rompasaurus/dilder/PromptProgression.md

# Prompt Progression

A record of every prompt submitted during the development of Dilder.

Spelling and grammar are lightly cleaned for readability while preserving the original intent and voice.

## Fields tracked per entry

Every prompt entry below uses the following fields. Entries that don't yet list all fields should be treated as incomplete and backfilled when the context is recovered.

- **Date/Time** — absolute date (`YYYY-MM-DD`) of the prompt. Relative dates like "Thursday" get resolved when the entry is written.
- **Prompt** — the user's message, quoted. Spelling and grammar are lightly cleaned for readability while preserving the original intent and voice.
- **Input Tokens (est)** — approximate user-facing input token count.
- **Output Tokens (est)** — approximate assistant output token count across the full turn.
- **Commit** — the short SHA + subject line of the git commit that landed the changes from this prompt, in the form `` `abc1234` — commit subject ``. Uses `n/a — <reason>` if no files were changed (research / Q&A / explanation turns) or if the work was never committed.
- **Files Created/Modified** — bulleted list of files touched, with short notes on the change. If nothing changed, omit or write `none`. Multi-prompt sessions may share a single commit; each entry still lists the files the specific prompt touched.

---

## Prompt #1
- **Date/Time:** 2026-04-08
- **Prompt:** "Let's create a new git repo for this project and put it up on my rompasaurus GitHub account. Also create a prompt progression file to notate every prompt that I type out for this project in an MD file with date and time stamp and the token count for each, and the files created or modified, in a file called PromptProgression."
- **Input Tokens (est):** ~75
- **Output Tokens (est):** ~350
- **Commit:** `369880d` — Initial commit: add PromptProgression.md for tracking project prompts
- **Files Created/Modified:**
  - `PromptProgression.md` (created)
  - `.git/` (initialized)
  - GitHub repo `rompasaurus/dilder` (created)

---

## Prompt #2
- **Date/Time:** 2026-04-08
- **Prompt:** "Let's set up a README and plan for this project. The idea is to create a learning platform and blog along with a YouTube series that goes through the development process of creating a Tamagotchi clone using a Pi Zero, e-ink display, battery, and 3D-printed case. As part of this we are going to document the entire process, starting with the prompts and structure of the project and planning process. Flesh out a README that outlines this intent, marking each addition in phases so that it can be compiled into a proper step-by-step instruction."
- **Input Tokens (est):** ~110
- **Output Tokens (est):** ~2,500
- **Commit:** `cc9ea8f` — Add README with phased project roadmap and update prompt log
- **Files Created/Modified:**
  - `README.md` (created)
  - `PromptProgression.md` (modified)

---

## Prompt #3
- **Date/Time:** 2026-04-09
- **Prompt:** "Let's continue the planning process. Bear in mind each prompt I submit needs to be recorded in PromptProgression.md. I suppose Phase 0 planning is somewhat complete — there is a section to define the pet and personality but I believe that should be planned at a later date. I think the focus first will be piecing together the hardware for a prototype testable unit with a display and input, and perhaps we'll put a placeholder animal animation of sorts to get a scaffold in place code-wise and a process in place for deploying code and testing it. As for the hardware, what we are going to be working with is a Pi Zero and this e-ink display. Let's begin to research the materials list to include this and whatever else hardware-wise will be needed to get a test bench setup for developing on this hardware. Also, given this hardware, come up with prototype sketches that could potentially be a 3D-printed casing for these materials and allow for 4–5 buttons of input actions to be recorded on the hardware, and suggest and research the types of cheap off-the-shelf components that can be used to establish input actions."
- **Input Tokens (est):** ~220
- **Output Tokens (est):** ~4,500
- **Commit:** `733c582` — Add hardware research with materials list, component specs, and input options
- **Files Created/Modified:**
  - `PromptProgression.md` (modified)
  - `docs/hardware-research.md` (created)
  - `README.md` (modified)

---

## Prompt #4
- **Date/Time:** 2026-04-09
- **Prompt:** "I also need the output processing token estimate from the prompts as well in the prompt progression."
- **Input Tokens (est):** ~20
- **Output Tokens (est):** ~250
- **Commit:** `8b8b2e4` — Update README and prompt log for Phase 1 hardware planning
- **Files Created/Modified:**
  - `PromptProgression.md` (modified — added output token estimates to all entries)

---

## Prompt #5
- **Date/Time:** 2026-04-09
- **Prompt:** "Those concept ASCII images are neat, but I want something more like a long rectangular case with the buttons on the right of the display — somewhat like the second-to-last generation of iPod Nanos — with four buttons: up, down, left, right, and a center button. Try to mock this up and see if you can generate an actual example, full-resolution prototype concept of this, bearing in mind the hardware we are using."
- **Input Tokens (est):** ~90
- **Output Tokens (est):** ~3,800
- **Commit:** `e1b6891` — Add prototype enclosure concept renders (v1 and v2 SVGs)
- **Files Created/Modified:**
  - `docs/concepts/prototype-v1.svg` (created — full-resolution prototype concept render)
  - `docs/hardware-research.md` (modified — replaced ASCII concepts with SVG reference and updated form factor)
  - `PromptProgression.md` (modified)

---

## Prompt #6
- **Date/Time:** 2026-04-09
- **Prompt:** "That's a good start. Let's create another revision of the prototype and make a v2. This time let's make the dimensions make sense — the display is going to take up the largest area of the device with the buttons being a quarter or less of the device's face real estate. Let's also take into account the Waveshare's actual dimensions and account for these ratios."
- **Input Tokens (est):** ~75
- **Output Tokens (est):** ~6,500
- **Commit:** `e1b6891` — Add prototype enclosure concept renders (v1 and v2 SVGs)
- **Files Created/Modified:**
  - `docs/concepts/prototype-v2.svg` (created — dimension-accurate prototype concept at 4:1 scale)
  - `docs/hardware-research.md` (modified — updated enclosure section with v2 specs and real component dimensions)
  - `PromptProgression.md` (modified)

---

## Prompt #7
- **Date/Time:** 2026-04-09
- **Prompt:** "For the hardware research we will need a breadboard to wire everything together — add that in there. Then we can begin the hardware setup and configuration, assuming we bought all the materials listed and a Waveshare e-ink display 2.13 V3. Compose an in-depth, well-researched setup guide to begin displaying text on the display and compile and run embedded code on the Raspberry Pi. Make the guide as simple and exhaustive as possible. Include a table of contents and walk me through the documentation for the hardware and how to set up the development and debugging environment. Pull in and research every bit of documentation I will need to be successful in this project."
- **Input Tokens (est):** ~130
- **Output Tokens (est):** ~12,000
- **Commit:** `30bb8b7` — Add comprehensive hardware and dev environment setup guide
- **Files Created/Modified:**
  - `docs/setup-guide.md` (created — comprehensive hardware and dev environment setup guide with 13 sections)
  - `docs/hardware-research.md` (modified — updated display to V3, added breadboard detail)
  - `README.md` (modified — added setup guide link to docs table and Phase 1 checklist)
  - `PromptProgression.md` (modified)

---

## Prompt #8
- **Date/Time:** 2026-04-09
- **Prompt:** "I want to set up a documentation webpage/portfolio to provide an in-depth guide on how this project is progressing in real time, along with a page for documentation and research, contact information, and an introduction. Let's create a new folder to begin planning this. I would also like to use pwnagotchi.ai as something of an inspiration for how to set this up and organise the website. It doesn't need to be anything ridiculous — in fact, static pages may be the ideal format — along with a Discord group and Patreon page. Let's roll out this folder and christen it with a new MD file."
- **Input Tokens (est):** ~120
- **Output Tokens (est):** ~3,500
- **Commit:** `f44695c` — Add website planning folder with site structure and community plan
- **Files Created/Modified:**
  - `website/PLAN.md` (created — website plan with site structure, page descriptions, Discord/Patreon plans, SSG comparison, pwnagotchi analysis)
  - `PromptProgression.md` (modified)

---

## Prompt #9
- **Date/Time:** 2026-04-09
- **Prompt:** "Let's kick off the website implementation. Look through the plan and start fleshing this out. Make sure while implementing the site to notate every step taken in a website implementation process MD, which will have a nicely structured TOC and detailed step-by-step notes on the process of creating this static site — to act as instruction and documentation. I also need a detailed guide on how to add and update content and the structure of the site, and further steps to deploy on Digital Ocean for as cheap as possible, and the best way to secure a domain for a website. Come up with domain ideas as well. Add steps to create a Patreon and Discord account. Don't forget to update PromptProgression with any prompt I input — don't be afraid to clean spelling and grammar before putting it in there too."
- **Input Tokens (est):** ~180
- **Output Tokens (est):** ~35,000
- **Commit:** `0360ba9` — Build out full MkDocs website scaffold and dev tooling (Prompts 9–13)
- **Files Created/Modified:**
  - `website/mkdocs.yml` (created — full MkDocs Material config with blog plugin, nav, social links, extensions)
  - `website/docs/index.md` (created — landing page)
  - `website/docs/about/index.md` (created — about page)
  - `website/docs/about/contact.md` (created — contact page)
  - `website/docs/blog/index.md` (created — blog landing)
  - `website/docs/blog/posts/phase-0-planning.md` (created — Phase 0 blog post)
  - `website/docs/blog/posts/phase-1-hardware.md` (created — Phase 1 blog post)
  - `website/docs/docs/index.md` (created — docs overview)
  - `website/docs/docs/hardware/materials-list.md` (created — migrated from hardware-research.md)
  - `website/docs/docs/hardware/wiring-pinout.md` (created — GPIO assignments and breadboard layout)
  - `website/docs/docs/hardware/enclosure-design.md` (created — case dimensions and design constraints)
  - `website/docs/docs/setup/pi-zero-setup.md` (created — OS flash, SSH, SPI setup)
  - `website/docs/docs/setup/display-setup.md` (created — HAT attachment, Waveshare library, hello world)
  - `website/docs/docs/setup/dev-environment.md` (created — rsync workflow, VS Code Remote-SSH, systemd)
  - `website/docs/docs/software/project-structure.md` (created — planned firmware architecture)
  - `website/docs/community/index.md` (created — community overview)
  - `website/docs/community/discord.md` (created — Discord server structure)
  - `website/docs/community/support.md` (created — Patreon tiers)
  - `website/docs/prompts/index.md` (created — prompt log mirroring PromptProgression.md)
  - `website/docs/stylesheets/extra.css` (created — custom CSS overrides)
  - `website/IMPLEMENTATION.md` (created — 14-section build process doc covering MkDocs setup, GitHub Pages, Digital Ocean deployment, domain registration guide, domain ideas, Discord setup, Patreon setup)
  - `website/CONTENT-GUIDE.md` (created — 11-section content management guide covering blog posts, docs pages, nav, Markdown features, images, and publishing)
  - `PromptProgression.md` (modified)

---

## Prompt #10
- **Date/Time:** 2026-04-09
- **Prompt:** "Give me a Python setup CLI script I can run to deploy this locally, with nice logging and status output when it is running, and various helper options for this project."
- **Input Tokens (est):** ~40
- **Output Tokens (est):** ~4,500
- **Commit:** `0360ba9` — Build out full MkDocs website scaffold and dev tooling (Prompts 9–13)
- **Files Created/Modified:**
  - `website/dev.py` (created — CLI with subcommands: check, install, serve, build, deploy, clean, status; ANSI color output with spinner; argparse; no external dependencies)

---

## Prompt #11
- **Date/Time:** 2026-04-09
- **Prompt:** "Give me a nice selection menu interface instead of a list of commands."
- **Input Tokens (est):** ~15
- **Output Tokens (est):** ~3,800
- **Commit:** `0360ba9` — Build out full MkDocs website scaffold and dev tooling (Prompts 9–13)
- **Files Created/Modified:**
  - `website/dev.py` (modified — replaced no-args fallback with interactive arrow-key menu: ↑↓ navigation, live description footer, env status badges, returns to menu after each command)

---

## Prompt #12
- **Date/Time:** 2026-04-09
- **Prompt:** "There seems to be a build failure when I build via the CLI script."
- **Input Tokens (est):** ~180 (included full error output)
- **Output Tokens (est):** ~500
- **Commit:** `0360ba9` — Build out full MkDocs website scaffold and dev tooling (Prompts 9–13)
- **Files Created/Modified:**
  - `website/docs/blog/.authors.yml` (created — required by MkDocs blog plugin for named authors)
  - `website/docs/blog/index.md` (modified — removed dead RSS link that wasn't a source file)
  - `website/docs/docs/hardware/enclosure-design.md` (modified — changed SVG links from broken relative paths to GitHub URLs)

---

## Prompt #13
- **Date/Time:** 2026-04-09
- **Prompt:** "Let's update the prompts with the last ones I sent through — divide and describe them. Commit the changes, and also apply the git commit as another field in the prompt progression where the prompt's changes were applied. Don't be afraid to clean up the spelling and grammar a bit. Report this prompt as well."
- **Input Tokens (est):** ~65
- **Output Tokens (est):** ~2,500
- **Commit:** `78ea1a0` — Backfill commit hash in PromptProgression.md (Prompt 13)
- **Files Created/Modified:**
  - `PromptProgression.md` (modified — full grammar/spelling pass, added commit hash field to all entries, added Prompts #11–13)

---

## Prompt #14
- **Date/Time:** 2026-04-09
- **Prompt:** "Walk me through how I could deploy this on GitHub Pages and the pricing structure — hopefully free — and if a domain can be linked to a GitHub Pages account."
- **Input Tokens (est):** ~35
- **Output Tokens (est):** ~900
- **Commit:** `633b084` — Add GitHub Actions workflow for automatic Pages deployment
- **Files Created/Modified:**
  - `.github/workflows/deploy-site.yml` (created — workflow that triggers on pushes to `website/` on main, installs MkDocs Material, and runs `mkdocs gh-deploy`)

---

## Prompt #15
- **Date/Time:** 2026-04-09
- **Prompt:** "Can you embed the concept images instead of linking to the GitHub page on the website?"
- **Input Tokens (est):** ~30
- **Output Tokens (est):** ~300
- **Commit:** `e358a1f` — Embed prototype SVG renders directly in enclosure design page
- **Files Created/Modified:**
  - `website/docs/assets/images/prototype-v1.svg` (created — copied from docs/concepts/)
  - `website/docs/assets/images/prototype-v2.svg` (created — copied from docs/concepts/)
  - `website/docs/docs/hardware/enclosure-design.md` (modified — replaced GitHub links with inline `![img]()` embeds)

---

## Prompt #16
- **Date/Time:** 2026-04-09
- **Prompt:** "Should the site folder be in the gitignore or will that need to be included to render on the GitHub Pages?"
- **Input Tokens (est):** ~25
- **Output Tokens (est):** ~150
- **Commit:** n/a — explanation only, no files changed
- **Files Created/Modified:** none

---

## Prompt #17
- **Date/Time:** 2026-04-09
- **Prompt:** "Add the last prompts with code changes to the prompt history with a commit ref."
- **Input Tokens (est):** ~20
- **Output Tokens (est):** ~400
- **Commit:** `1c270fd` — Update PromptProgression with Prompts 14–17 and fix #13 commit ref
- **Files Created/Modified:**
  - `PromptProgression.md` (modified — fixed Prompt #13 commit hash, added Prompts #14–17)

---

## Prompt #18
- **Date/Time:** 2026-04-09
- **Prompt:** "I need a website deployment process guide for GitHub Pages. I have a registered domain on Squarespace and I would like to deploy this site on GitHub and link my domain to this page."
- **Input Tokens (est):** ~45
- **Output Tokens (est):** ~2,800
- **Commit:** `38baa75` — Add deployment guide and CNAME file for Squarespace domain setup
- **Files Created/Modified:**
  - `website/DEPLOY.md` (created — 13-section deployment guide: GitHub Pages setup, first deployment, CNAME file, Squarespace DNS configuration with step-by-step record setup, HTTPS, mkdocs.yml update, end-to-end verification checklist, troubleshooting)
  - `website/docs/CNAME` (created — placeholder CNAME file, update with real domain before deploying)

---

## Prompt #19
- **Date/Time:** 2026-04-09
- **Prompt:** "Add my Patreon page to the site."
- **Input Tokens (est):** ~15
- **Output Tokens (est):** ~100
- **Commit:** `3b36905` — Add real Patreon URL (MchenrysDevelopment) across site
- **Files Created/Modified:**
  - `website/mkdocs.yml` (modified — Patreon social link updated)
  - `website/docs/community/support.md` (modified — Patreon URL updated)
  - `website/docs/about/contact.md` (modified — Patreon URL updated)

---

## Prompt #20
- **Date/Time:** 2026-04-09
- **Prompt:** "There's a 404 error — it's not loading despite the domain pointing correctly and the GitHub hook deploying."
- **Input Tokens (est):** ~40
- **Output Tokens (est):** ~300
- **Commit:** `0af7962` — Clarify Pages source setting in workflow comment
- **Files Created/Modified:**
  - `.github/workflows/deploy-site.yml` (modified — added comment clarifying Pages must be set to "Deploy from a branch → gh-pages" not "GitHub Actions")

---

## Prompt #21
- **Date/Time:** 2026-04-09
- **Prompt:** "Make that branch for me so that it triggers the deploy."
- **Input Tokens (est):** ~20
- **Output Tokens (est):** ~150
- **Commit:** `1c7f210` — Trigger GitHub Pages deployment via website/ path change
- **Files Created/Modified:**
  - `website/requirements.txt` (modified — added comment to satisfy workflow paths filter and trigger first deployment)

---

## Prompt #22
- **Date/Time:** 2026-04-09
- **Prompt:** *(Shared GitHub Actions build log showing successful deploy to gh-pages branch with CNAME resolution to dilder.dev)*
- **Input Tokens (est):** ~200 (build log)
- **Output Tokens (est):** ~200
- **Commit:** `18c8876` — Lowercase CNAME domain
- **Files Created/Modified:**
  - `website/docs/CNAME` (modified — changed `Dilder.dev` to `dilder.dev` for consistency)

---

## Prompt #23
- **Date/Time:** 2026-04-09
- **Prompt:** "Now we need to pull in the documentation for the Pi Zero WH and the e-ink display. Reach out to the official documentation and put it in its own folder in the docs folder. We need to then extract the pinout and pertinent documentation and attach it to the Wiring & Pinout doc."
- **Input Tokens (est):** ~55
- **Output Tokens (est):** ~8,500
- **Commit:** `61525d6` — Add official hardware reference docs and expand wiring pinout
- **Files Created/Modified:**
  - `website/docs/docs/reference/pi-zero-wh.md` (created — full 40-pin GPIO table, electrical limits, SPI/I²C/UART/PWM protocol assignments, BCM vs physical numbering guide, official links)
  - `website/docs/docs/reference/waveshare-eink.md` (created — display specs, HAT pin mapping with signal behavior table, SPI protocol details, refresh rules, V3 vs V4 comparison, Python setup examples, safety notes, official links)
  - `website/docs/docs/hardware/wiring-pinout.md` (modified — expanded with full 40-pin header map, signal behavior table, wiring diagram, SPI config table, links to new reference docs, troubleshooting section)
  - `website/mkdocs.yml` (modified — Reference section added to nav)

---

## Prompt #24
- **Date/Time:** 2026-04-09
- **Prompt:** "Update the prompts file with this and the commit."
- **Input Tokens (est):** ~15
- **Output Tokens (est):** ~400
- **Commit:** `09519b5` — Update PromptProgression with Prompts 20–24
- **Files Created/Modified:**
  - `PromptProgression.md` (modified — added Prompts #20–24)

---

## Prompt #25
- **Date/Time:** 2026-04-10
- **Prompt:** "Let's update this plan and the hardware we are going to use. For now I have a set of Waveshare 2.13 V3 displays and Pico W boards on hand that I would like to use to start this project with instead of the Pi Zero. We'll put the Pi Zero in a later dev phase and start with what we have. Update the documentation to account for this hardware change and pull in the correct documentation for this hardware and setup in the project and on the site. Update everything and replace the Zero with the Pico, and then we need to create a setup document to wire up the Waveshare to the Pico W and begin debugging from VSCode on Linux."
- **Input Tokens (est):** ~130
- **Output Tokens (est):** ~45,000
- **Commit:** `604039f` — Migrate from Pi Zero to Pico W as Phase 1 development platform
- **Files Created/Modified:**
  - `README.md` (modified — Pico W as primary board, Pi Zero deferred to Phase 5, new phase roadmap)
  - `docs/hardware-research.md` (modified — Pico W specs, SPI1 pin mapping, updated materials list and GPIO budget)
  - `website/docs/docs/reference/pico-w.md` (created — full Pico W reference: RP2040 specs, pinout, electrical limits, MicroPython firmware, Pico W vs Pi Zero comparison)
  - `website/docs/docs/reference/waveshare-eink.md` (modified — added Pico W jumper wire mapping, MicroPython driver setup, kept Pi Zero mapping for future)
  - `website/docs/docs/reference/pi-zero-wh.md` (modified — added "future hardware" banner)
  - `website/docs/docs/hardware/materials-list.md` (modified — Pico W components, updated costs and specs)
  - `website/docs/docs/hardware/wiring-pinout.md` (modified — complete rewrite for Pico W GPIO, jumper wire diagrams, MicroPython button code, visual pin map)
  - `website/docs/docs/hardware/enclosure-design.md` (modified — Pico W dimensions, enclosure deferred note)
  - `website/docs/docs/setup/pi-zero-setup.md` (modified — rewritten as Pico W setup: MicroPython flash, BOOTSEL, serial REPL, Wi-Fi test)
  - `website/docs/docs/setup/display-setup.md` (modified — rewritten for Pico W jumper wire connection, Waveshare MicroPython driver, framebuf hello world)
  - `website/docs/docs/setup/dev-environment.md` (modified — rewritten for VSCode + MicroPico on Linux: serial permissions, project config, file upload, mpremote CLI, debugging)
  - `website/docs/docs/software/project-structure.md` (modified — updated for MicroPython: framebuf, machine.Pin, flash storage notes)
  - `website/docs/docs/index.md` (modified — updated section names and descriptions for Pico W)
  - `website/docs/index.md` (modified — landing page updated for Pico W)
  - `website/mkdocs.yml` (modified — site description, nav labels, added Pico W reference page)
  - `website/docs/blog/posts/phase-1-hardware.md` (modified — rewritten for Pico W test bench)
  - `website/docs/blog/posts/phase-0-planning.md` (modified — hardware decision section updated for Pico W first approach)

---

## Prompt #26
- **Date/Time:** 2026-04-10
- **Prompt:** "Update the prompts file and fix grammar a bit. Divide, describe, and commit."
- **Input Tokens (est):** ~20
- **Output Tokens (est):** ~1,500
- **Commit:** `604039f` — Migrate from Pi Zero to Pico W as Phase 1 development platform
- **Files Created/Modified:**
  - `PromptProgression.md` (modified — added Prompts #25–26)

---

## Prompt #27
- **Date/Time:** 2026-04-11
- **Prompt:** "Let's make a development setup folder with a Docker Compose file and a step-by-step guide with a table of contents on setting up the Pico W and Waveshare e-ink display — physically connecting the display to the Pico board via GPIO headers, then flashing and connecting the Pico to this computer and running a first Hello World program via VSCode using compiled C. I need all the instructions to set up the hardware, configure VSCode, connect, debug, and run this application. Make this guide as detailed and as simple as possible, step by step. Also update the PromptProgression every time I submit a prompt here — clean up the grammar and spelling though. Make this setup guide the Pico and display first-time setup, and update the dev website too."
- **Input Tokens (est):** ~150
- **Output Tokens (est):** ~45,000
- **Commit:** `8f0df95` — Add C SDK dev environment, setup CLI, and first-time hardware guide
- **Files Created/Modified:**
  - `dev-setup/pico-and-display-first-time-setup.md` (created — comprehensive 13-section first-time setup guide with TOC: hardware wiring, C SDK toolchain install, VSCode configuration, CMake cross-compilation, build/flash/debug workflow, troubleshooting)
  - `dev-setup/hello-world/CMakeLists.txt` (created — CMake build config for Pico W with Waveshare e-Paper library, USB serial output, Ninja generator)
  - `dev-setup/hello-world/main.c` (created — Hello World C program that initializes SPI, draws text on the e-ink display, and prints heartbeat to USB serial)
  - `dev-setup/Dockerfile` (created — Ubuntu 24.04 container with ARM cross-compiler toolchain and Pico SDK for reproducible builds)
  - `dev-setup/docker-compose.yml` (created — single-service compose file that mounts the project and runs CMake + Ninja build)
  - `website/docs/docs/setup/first-time-setup.md` (created — website version of the setup guide with MkDocs Material formatting, tabbed OS instructions, admonitions)
  - `website/mkdocs.yml` (modified — added "First-Time Setup (C SDK)" to the Setup nav section)
  - `PromptProgression.md` (modified — added Prompt #27)

---

## Prompt #28
- **Date/Time:** 2026-04-11
- **Prompt:** "Let's start planning the hardware enclosure design. Create a new folder labelled hardware-design and document the applicable dimensions of the e-ink display and Pico board, along with viable off-the-shelf button options that can be wired to the Pico easily. Research the web for the best button options and provide a cost breakdown. Then we need to start planning how to model out a 3D-printed prototype case based on the concept images — link the concept images, suggest the best CAD software and company to print the first prototype cases, and provide estimated costs. Put this in a new hardware planning document with a table of contents and step-by-step guide. Also update the PromptProgression with this entry, following the same pattern."
- **Input Tokens (est):** ~150
- **Output Tokens (est):** ~25,000
- **Commit:** `8f0df95` — Add C SDK dev environment, setup CLI, and first-time hardware guide
- **Files Created/Modified:**
  - `hardware-design/hardware-planning.md` (created — comprehensive enclosure planning document with TOC: component dimensions, button selection with cost breakdown, concept image links, enclosure constraints, CAD software comparison, step-by-step 3D modeling plan, printing service comparison with costs, prototype timeline)

---

## Prompt #29
- **Date/Time:** 2026-04-11
- **Prompt:** "I want another Hello World version of the code running in C as well. The intent with this project is to have it running on C code completely for speed and efficiency. Also, for the wiring section, I am using the soldered-on headers and pins to slot the Waveshare directly onto the Pico on its headers, so it just slides in. Update the guide accordingly — I will provide pictures later."
- **Input Tokens (est):** ~80
- **Output Tokens (est):** ~30,000
- **Commit:** `8f0df95` — Add C SDK dev environment, setup CLI, and first-time hardware guide
- **Files Created/Modified:**
  - `dev-setup/hello-world-serial/main.c` (created — bare-minimum serial-only Hello World in C: LED blink + heartbeat printf, no display wiring needed, verifies toolchain end-to-end)
  - `dev-setup/hello-world-serial/CMakeLists.txt` (created — minimal CMake config linking only pico_stdlib with USB serial output)
  - `dev-setup/pico-and-display-first-time-setup.md` (rewritten — restructured as two checkpoints: Checkpoint 1 serial-only, Checkpoint 2 display; added C vs MicroPython rationale; updated wiring section from jumper wires to direct header-on-header connection)
  - `website/docs/docs/setup/first-time-setup.md` (rewritten — website version updated to match: direct header connection, two-checkpoint flow, C-first rationale)
  - `PromptProgression.md` (modified — added Prompt #29)

---

## Prompt #30
- **Date/Time:** 2026-04-11
- **Prompt:** "Let's take this Pico W & Display First-Time Setup and implement a Python command-line step-by-step interface that sets everything up and explains the process in detail as well. Put the Python script in the root of this project."
- **Input Tokens (est):** ~40
- **Output Tokens (est):** ~35,000
- **Commit:** `8f0df95` — Add C SDK dev environment, setup CLI, and first-time hardware guide
- **Files Created/Modified:**
  - `setup.py` (created — interactive 14-step CLI walkthrough: prerequisite checks, ARM toolchain install with distro detection, Pico SDK clone, PICO_SDK_PATH configuration, serial port permissions, VSCode extension install, serial hello world build/flash/verify, display connection guidance, Waveshare library download, display hello world build/flash/verify; includes --status, --step N, and --list flags; matches dev.py visual style with ANSI colors, spinners, boxed explanations, and manual-step callouts)
  - `PromptProgression.md` (modified — added Prompt #30)

---

## Prompt #31
- **Date/Time:** 2026-04-11
- **Prompt:** "Failed at step 5 — `usermod: group 'dialout' does not exist`. Does the Pico need to be connected at step 5?"
- **Input Tokens (est):** ~30
- **Output Tokens (est):** ~5,000
- **Commit:** `8f0df95` — Add C SDK dev environment, setup CLI, and first-time hardware guide
- **Files Created/Modified:**
  - `setup.py` (modified — added `detect_serial_group()` and `user_in_serial_group()` helpers that check for `uucp` first then `dialout`; Arch/CachyOS uses `uucp`, Debian/Ubuntu uses `dialout`; all hardcoded `dialout` references replaced with dynamic detection)
  - `dev-setup/pico-and-display-first-time-setup.md` (modified — serial permissions section updated with distro-specific group names)
  - `website/docs/docs/setup/first-time-setup.md` (modified — same distro-specific serial group fix with tabbed instructions)
  - `PromptProgression.md` (modified — added Prompt #31)

---

## Prompt #32
- **Date/Time:** 2026-04-11
- **Prompt:** *(Pasted build failure output from setup.py Step 7 — `PICO_DEFAULT_LED_PIN` undeclared error)*
- **Input Tokens (est):** ~80
- **Output Tokens (est):** ~8,000
- **Commit:** `8f0df95` — Add C SDK dev environment, setup CLI, and first-time hardware guide
- **Files Created/Modified:**
  - `dev-setup/hello-world-serial/main.c` (modified — replaced `PICO_DEFAULT_LED_PIN` and `gpio_put` with `cyw43_arch_gpio_put(CYW43_WL_GPIO_LED_PIN)` since the Pico W's onboard LED is wired to the CYW43 Wi-Fi chip, not a regular GPIO pin; added `pico/cyw43_arch.h` include and `cyw43_arch_init()` call)
  - `dev-setup/hello-world-serial/CMakeLists.txt` (modified — added `pico_cyw43_arch_none` to link libraries for CYW43 LED control)
  - `setup.py` (modified — fixed build error output to show both stdout and stderr since Ninja reports compile errors on stdout)
  - `PromptProgression.md` (modified — added Prompt #32)

---

## Prompt #33
- **Date/Time:** 2026-04-11
- **Prompt:** "Could not find the RPI-RP2 mount despite it showing up in Dolphin file explorer."
- **Input Tokens (est):** ~40
- **Output Tokens (est):** ~5,000
- **Commit:** `8f0df95` — Add C SDK dev environment, setup CLI, and first-time hardware guide
- **Files Created/Modified:**
  - `setup.py` (modified — added `find_rpi_rp2_mount()` helper that checks static paths, falls back to `findmnt`/`lsblk` for the actual mount point, retries after 1-second delay for automount; both flash steps now loop with retry instead of failing on first miss)
  - `PromptProgression.md` (modified — added Prompt #33)

---

## Prompt #34
- **Date/Time:** 2026-04-11
- **Prompt:** *(Pasted Step 12 build failure — `Debug.h: No such file or directory` and missing `<stdlib.h>` warnings)*
- **Input Tokens (est):** ~100
- **Output Tokens (est):** ~5,000
- **Commit:** `8f0df95` — Add C SDK dev environment, setup CLI, and first-time hardware guide
- **Files Created/Modified:**
  - `dev-setup/hello-world/main.c` (modified — added missing `#include <stdlib.h>` for `malloc`/`free`)
  - `dev-setup/hello-world/lib/Config/Debug.h` (added — copied from Waveshare repo, was missing from the initial file list)
  - `setup.py` (modified — added `Debug.h` to the Waveshare library copy list in Step 11)
  - `dev-setup/pico-and-display-first-time-setup.md` (modified — added `Debug.h` to the manual copy commands)
  - `website/docs/docs/setup/first-time-setup.md` (modified — same `Debug.h` fix)
  - `PromptProgression.md` (modified — added Prompt #34)

---

## Prompt #35
- **Date/Time:** 2026-04-11
- **Prompt:** "That worked. Let's update the documentation and provide a step-by-step walkthrough of this script and setup process in the setup document. Also update the prompts doc with all the prompts we used here and the last session, then divide, describe, commit, and push this code."
- **Input Tokens (est):** ~50
- **Output Tokens (est):** ~12,000
- **Commit:** `8f0df95` — Add C SDK dev environment, setup CLI, and first-time hardware guide
- **Files Created/Modified:**
  - `dev-setup/pico-and-display-first-time-setup.md` (modified — added "Automated Setup Script" section at the top with full walkthrough: command reference, 14-step table with automated/manual flags, example `--status` output, resume instructions)
  - `website/docs/docs/setup/first-time-setup.md` (modified — added matching setup script walkthrough with MkDocs admonitions and step table)
  - `.gitignore` (modified — added build artifacts, Waveshare lib files, pico_sdk_import.cmake, `__pycache__/`, `.vscode/`)
  - `PromptProgression.md` (modified — added Prompts #27–35, updated all pending commit hashes)
  - All new and modified files committed and pushed to origin/main

---

## Prompt #36
- **Date/Time:** 2026-04-11
- **Prompt:** "Now that the dev environment is set up, let's make a Python GUI to interface with the Pico — view logs, debug, and create a simple utility to draw images and type text on an emulated e-ink display that can then be either saved locally or sent to the e-ink display live. When saved, add it to an assets folder in the root of this project directory. Also, if there are any other useful utilities that can be added to enhance the development and usage of the Pico W, add them to this Python UI. Let's make this in Tkinter and put it in the root of this project in a directory called DevTool. Also I need an in-depth walkthrough of this implementation in the folder as well — an MD with a TOC and step-by-step instructions."
- **Input Tokens (est):** ~150
- **Output Tokens (est):** ~55,000
- **Commit:** `cf5cd3a` — Add DevTool — Tkinter GUI for Pico W development
- **Files Created/Modified:**
  - `DevTool/devtool.py` (created — 950-line Tkinter GUI with five tabs: display emulator with pencil/eraser/line/rect/text tools and save/load/send; serial monitor with connect/disconnect/send/log; firmware flash utility with BOOTSEL detection and build buttons; asset manager with preview and delete; GPIO pin reference viewer; dark theme; threaded serial I/O)
  - `DevTool/requirements.txt` (created — pyserial, Pillow)
  - `DevTool/README.md` (created — 11-section walkthrough with TOC: requirements, installation, all five tabs documented with usage instructions, file formats, architecture overview, class structure, threading model, troubleshooting table)
  - `assets/` (created — empty directory for saved display images)
  - `PromptProgression.md` (modified — added Prompt #36)

---

## Prompt #37
- **Date/Time:** 2026-04-11
- **Prompt:** "Add a utility tab to walk through connecting the Pico via USB, and also add a Wi-Fi option as well in the GUI as a tab. Be descriptive and as simple as possible. And add a documentation tab to reference how to use the application."
- **Input Tokens (est):** ~50
- **Output Tokens (est):** ~25,000
- **Commit:** `cdae51f` — Add Connect and Docs tabs to DevTool
- **Files Created/Modified:**
  - `DevTool/devtool.py` (modified — added two new tabs: ConnectionUtility with USB serial walkthrough (4 steps with live Check buttons for device detection, serial port, permissions, plus link to Serial Monitor) and Wi-Fi walkthrough (C code examples, CMake config, network scanner, TCP connection tester with IP/port input); DocumentationTab with searchable TOC sidebar, styled headings/code blocks, Find/Clear search with highlight, covers all 7 tabs plus keyboard shortcuts, file formats, and troubleshooting)
  - `DevTool/README.md` (modified — updated TOC, launch table, and architecture table for 7 tabs; added Section 9 Connection Utility with USB and Wi-Fi step tables; added Section 10 Documentation tab description; renumbered remaining sections)
  - `PromptProgression.md` (modified — added Prompt #37)

---

## Prompt #38
- **Date/Time:** 2026-04-11
- **Prompt:** "Allow me to run the sudo for serial permissions in the DevTool."
- **Input Tokens (est):** ~15
- **Output Tokens (est):** ~5,000
- **Commit:** `b8985c7` — Add sudo serial permissions button to DevTool Connect tab
- **Files Created/Modified:**
  - `DevTool/devtool.py` (modified — added "Fix: Add me to serial group" button in the Connect tab USB walkthrough; `_fix_serial_perms()` method auto-detects the correct group, tries `pkexec` for a graphical sudo prompt first, falls back to opening a terminal emulator with the command, shows confirmation dialog before running, reports success with logout reminder)
  - `PromptProgression.md` (modified — added Prompt #38)

---

## Prompt #39
- **Date/Time:** 2026-04-11
- **Prompt:** "The DevTool was suspended but didn't close. Help me close this and prevent this in the future."
- **Input Tokens (est):** ~20
- **Output Tokens (est):** ~2,000
- **Commit:** `586dff9` — Ignore Ctrl+Z (SIGTSTP) in DevTool to prevent zombie suspends
- **Files Created/Modified:**
  - `DevTool/devtool.py` (modified — added `signal.signal(signal.SIGTSTP, signal.SIG_IGN)` at startup to ignore Ctrl+Z; killed the suspended process with `kill -9`)

---

## Prompt #40
- **Date/Time:** 2026-04-11
- **Prompt:** "Update the prompts and add the latest assets as well. Clean up spelling and grammar."
- **Input Tokens (est):** ~20
- **Output Tokens (est):** ~3,000
- **Commit:** `5025ec6` — Add test assets and update PromptProgression through Prompt #40
- **Files Created/Modified:**
  - `assets/garbage.pbm` (added — test image saved from DevTool display emulator)
  - `assets/garbage.bin` (added — raw display buffer of the test image)
  - `assets/garbage.png` (added — PNG export of the test image)
  - `PromptProgression.md` (modified — added Prompts #39–40, backfilled commit hashes for #37–38, grammar and spelling pass)

---

## Prompt #41
- **Date/Time:** 2026-04-11
- **Prompt:** "We need to update the website with all the new documentation and Python tools created. Follow the structure of the site and update this."
- **Input Tokens (est):** ~30
- **Output Tokens (est):** ~60,000
- **Commit:** `b408ab1` — Update website with Tools docs, blog post, prompt log, and DevTool Programs tab
- **Files Created/Modified:**
  - `website/docs/docs/tools/devtool.md` (created — DevTool documentation page with installation, tabs overview, file formats, and architecture)
  - `website/docs/docs/tools/setup-cli.md` (created — setup.py documentation page with step tables, features, and status dashboard)
  - `website/docs/docs/tools/website-dev.md` (created — website dev.py documentation page with commands and workflow)
  - `website/docs/blog/posts/phase-1-devtools.md` (created — blog post covering setup CLI, DevTool GUI, and C-first development decisions)
  - `website/mkdocs.yml` (modified — added Tools section to nav with DevTool, Setup CLI, Website Dev CLI)
  - `website/docs/docs/index.md` (modified — added Tools subsection with links to all three tool pages)
  - `website/docs/docs/software/project-structure.md` (modified — complete rewrite: updated repo layout to include DevTool, dev-setup, hardware-design, assets, website planning docs; rewrote planned modules from MicroPython to C SDK; updated comparison table)
  - `website/docs/index.md` (modified — updated current phase to reflect dev tooling progress, added Dev Tools quick link card, added tools link to "How This Project Works" section)
  - `website/docs/prompts/index.md` (modified — added Prompts #10–40, covering website deployment, GitHub Pages, hardware migration, C SDK setup, DevTool development)
  - `PromptProgression.md` (modified — added Prompt #41)

---

## Prompt #42
- **Date/Time:** 2026-04-11
- **Prompt:** "Divide, describe, and commit. Update the prompts, fix grammar. Check all the latest Claude sessions for prompts."
- **Input Tokens (est):** ~25
- **Output Tokens (est):** ~2,000
- **Commit:** `b408ab1` — Update website with Tools docs, blog post, prompt log, and DevTool Programs tab
- **Files Created/Modified:**
  - `PromptProgression.md` (modified — added Prompt #42)

---

## Prompt #43
- **Date/Time:** 2026-04-11
- **Prompt:** "Also the software on the site needs the READMEs for the GUI app and a guide on the CLI setup."
- **Input Tokens (est):** ~25
- **Output Tokens (est):** ~40,000
- **Commit:** `8401317` — Expand DevTool and Setup CLI pages with full README content
- **Files Created/Modified:**
  - `website/docs/docs/tools/devtool.md` (rewritten — expanded from summary to full documentation matching DevTool/README.md: all 7 tabs with detailed usage instructions, drawing tools, serial monitor, flash firmware, asset manager, GPIO reference, connection utility with USB/Wi-Fi walkthroughs, documentation tab, file format specifications with byte layouts, class architecture, threading model, troubleshooting table)
  - `website/docs/docs/tools/setup-cli.md` (rewritten — expanded from summary to comprehensive guide matching dev-setup/pico-and-display-first-time-setup.md: 14-step walkthrough table, hardware requirements, software installed, Pico W and Waveshare specs, C vs MicroPython rationale, display connection with side-view diagram and pin mapping, troubleshooting tables for build/flash/serial/display issues, quick reference card)
  - `PromptProgression.md` (modified — added Prompt #43)

---

## Prompt #44
- **Date/Time:** 2026-04-11
- **Prompt:** "OK, you made a dev tool where I can create assets via the display emulator. First of all, the pencil and line don't draw on the window at all — text and rectangle do. Also I want the ability to preview the asset on the Pico display if it's connected — add a button to deploy to Pico. Then we want to create another tab in the dev tool to deploy from a list of programs. For the first program I want you to create a sassy octopus that smiles and alternates between that expression and an open-mouth expression with a text chat bubble where it blurts out from a random list of unhinged hilarious conspiracies and jokes and meme statements, alternating between facial expressions. The octopus should be on the left side of the display and the chat bubble to the right of its mouth."
- **Input Tokens (est):** ~200
- **Output Tokens (est):** ~80,000
- **Commit:** `63e696b`
- **Files Created/Modified:**
  - `DevTool/devtool.py` (modified — fixed `_draw_brush` range bug that broke pencil/line tools; added Programs tab with preview/deploy; added Sassy Octopus program with pixel art, 3 mouth expressions, 30 quotes, tiny bitmap font, chat bubble rendering; made Send to Pico non-blocking with write timeout)

---

## Prompt #45
- **Date/Time:** 2026-04-11
- **Prompt:** "The octopus needs more legs and it should have less black and more curvaceous. The display emulator tab should have a preview deploy on the Pico as well."
- **Input Tokens (est):** ~40
- **Output Tokens (est):** ~30,000
- **Commit:** `151b575` — Make DevTool serial send non-blocking and backfill Prompt #40 commit hash
- **Files Created/Modified:**
  - `DevTool/devtool.py` (modified — redesigned octopus to outline style with 6 curvy tentacles, then reverted to original chunky style per user preference; added 6 tentacle legs; fixed deploy hang with write_timeout)

---

## Prompt #46
- **Date/Time:** 2026-04-11
- **Prompt:** "God the octopus looks awful, use the other octopus you made — it looked way better."
- **Input Tokens (est):** ~20
- **Output Tokens (est):** ~15,000
- **Commit:** `b408ab1` — Update website with Tools docs, blog post, prompt log, and DevTool Programs tab
- **Files Created/Modified:**
  - `DevTool/devtool.py` (modified — reverted to original chunky filled-style octopus with 6 tentacle legs, improved open-mouth with proper white interior and black border)

---

## Prompt #47
- **Date/Time:** 2026-04-11
- **Prompt:** "I don't want to see the logs — write the steps in the write-failed message. Also the logs at the bottom need to be resizable."
- **Input Tokens (est):** ~30
- **Output Tokens (est):** ~10,000
- **Commit:** `63e696b` — Add Programs tab, Sassy Octopus, IMG-receiver and standalone firmware, fix drawing tools
- **Files Created/Modified:**
  - `DevTool/devtool.py` (modified — moved deploy failure steps to status label; replaced fixed log bar with resizable PanedWindow + scrollbar + Clear button; improved port detection with Raspberry Pi VID 0x2E8A; fixed hardcoded /dev/ttyACM0 references)

---

## Prompt #48
- **Date/Time:** 2026-04-11
- **Prompt:** "Also no device found error — I changed USB ports, does that break this? If so check for the correct port in all the utils."
- **Input Tokens (est):** ~30
- **Output Tokens (est):** ~5,000
- **Commit:** `63e696b` — Add Programs tab, Sassy Octopus, IMG-receiver and standalone firmware, fix drawing tools
- **Files Created/Modified:**
  - `DevTool/devtool.py` (modified — `find_pico_serial()` now checks Raspberry Pi USB VID 0x2E8A first, then falls back to ttyACM/usbmodem name matching; connection utility uses dynamic detection instead of hardcoded paths)

---

## Prompt #49
- **Date/Time:** 2026-04-11
- **Prompt:** "It says to flash the firmware via the flash tab — where is the image, what am I flashing? Can't you do it in the Programs tab when I have the Pico in BOOTSEL mode?"
- **Input Tokens (est):** ~40
- **Output Tokens (est):** ~40,000
- **Commit:** `63e696b` — Add Programs tab, Sassy Octopus, IMG-receiver and standalone firmware, fix drawing tools
- **Files Created/Modified:**
  - `dev-setup/img-receiver/main.c` (created — Pico W firmware that receives IMG: protocol over USB serial and displays on e-ink, with landscape-to-portrait transpose and partial refresh)
  - `dev-setup/img-receiver/CMakeLists.txt` (created)
  - `dev-setup/img-receiver/lib/` (created — copied shared Waveshare/GUI libraries)
  - `dev-setup/docker-compose.yml` (modified — added build-img-receiver service)
  - `DevTool/devtool.py` (modified — added Build & Flash button to Programs tab with Docker build + BOOTSEL flash; added 3 mouth expressions: smirk, smile, open; added MOUTH_CYCLE animation; updated all error messages to reference Programs tab)

---

## Prompt #50
- **Date/Time:** 2026-04-11
- **Prompt:** "Also give the octopus more mouth expressions — I want a default smile which is a half-circle that's white and slightly off-angle from the normal mouth."
- **Input Tokens (est):** ~30
- **Output Tokens (est):** ~5,000
- **Commit:** `63e696b` — Add Programs tab, Sassy Octopus, IMG-receiver and standalone firmware, fix drawing tools
- **Files Created/Modified:**
  - `DevTool/devtool.py` (modified — added smirk expression as default: tilted half-circle with white interior; animation now cycles smirk → open → smile → open)

---

## Prompt #51
- **Date/Time:** 2026-04-12
- **Prompt:** "In the build give some more descriptive logs of what Docker is doing. Also can the logs and windows be resized on this GUI?"
- **Input Tokens (est):** ~25
- **Output Tokens (est):** ~15,000
- **Commit:** `63e696b` — Add Programs tab, Sassy Octopus, IMG-receiver and standalone firmware, fix drawing tools
- **Files Created/Modified:**
  - `DevTool/devtool.py` (modified — Docker image build step now streams output line-by-line with `[docker]` prefixed log entries; shows download/install/clone progress in real time; increased timeout to 600s; fixed sidebar panels to allow proper horizontal resizing)

---

## Prompt #52
- **Date/Time:** 2026-04-12
- **Prompt:** "I want the ability to deploy the sassy octopus fully to the Pico so I can run it without having the USB connected and it will just boot into this program standalone."
- **Input Tokens (est):** ~40
- **Output Tokens (est):** ~30,000
- **Commit:** `63e696b` — Add Programs tab, Sassy Octopus, IMG-receiver and standalone firmware, fix drawing tools
- **Files Created/Modified:**
  - `dev-setup/sassy-octopus/main.c` (created — standalone firmware that cycles pre-rendered frames on the e-ink display with partial refresh, no USB needed)
  - `dev-setup/sassy-octopus/CMakeLists.txt` (created)
  - `dev-setup/sassy-octopus/lib/` (created — copied shared Waveshare/GUI libraries)
  - `dev-setup/docker-compose.yml` (modified — added build-sassy-octopus service)
  - `DevTool/devtool.py` (modified — added Deploy Standalone button that pre-renders all 120 animation frames in Python, writes frames.h C header, Docker-builds the firmware, and flashes to Pico via BOOTSEL)

---

## Prompt #53
- **Date/Time:** 2026-04-12
- **Prompt:** "Divide, describe, and commit. Update the prompts, fix spelling, and add documentation on the new features of the tool. Update existing docs and the website and prompts file, and commit and push."
- **Input Tokens (est):** ~40
- **Output Tokens (est):** ~50,000
- **Commit:** `63e696b` — Add Programs tab, Sassy Octopus, IMG-receiver and standalone firmware, fix drawing tools
- **Files Created/Modified:**
  - `PromptProgression.md` (modified — added Prompts #44–53)
  - `README.md` (modified — updated Phase 1 checklist, added DevTool and firmware projects)
  - `DevTool/README.md` (modified — updated for 8 tabs, added Programs tab docs, updated architecture)
  - `website/docs/docs/tools/devtool.md` (modified — added Programs tab and standalone deploy documentation)
  - `website/docs/prompts/index.md` (modified — added Prompts #41–53)
  - `dev-setup/img-receiver/main.c`, `dev-setup/sassy-octopus/main.c` (spelling fixes)

---

## Prompt #54
- **Date/Time:** 2026-04-12
- **Prompt:** "Could the XIAO nRF52840, BT5.0 do the same thing as the Pi Pico in this project?"
- **Input Tokens (est):** ~25
- **Output Tokens (est):** ~4,000
- **Commit:** n/a — analysis only, no files changed
- **Files Created/Modified:** none

---

## Prompt #55
- **Date/Time:** 2026-04-12
- **Prompt:** "Give me a comparison chart for Raspberry Pi Pico, RP2040, Cortex-M0+, microUSB..." *(pasted full shopping cart with 9 boards: Pi Pico, Pi Pico H, Pi Pico 2 W, Pi Pico 2 WH, XIAO SAMD21, XIAO nRF52840+, XIAO MG24 Sense, XIAO ESP32S3+, XIAO RP2350)*
- **Input Tokens (est):** ~400
- **Output Tokens (est):** ~5,000
- **Commit:** n/a — analysis only, no files changed
- **Files Created/Modified:** none

---

## Prompt #56
- **Date/Time:** 2026-04-12
- **Prompt:** *(Pasted wrong shopping cart with microscopes, USB mouse, stool, and other non-display items — corrected in next prompt)*
- **Input Tokens (est):** ~350
- **Output Tokens (est):** ~1,500
- **Commit:** n/a — clarification, no files changed
- **Files Created/Modified:** none

---

## Prompt #57
- **Date/Time:** 2026-04-12
- **Prompt:** *(Pasted correct shopping cart with 18 items: boards, e-paper displays, LCD/TFT displays, and Pi Zeros — asked for display comparison with board compatibility, power consumption, refresh rates, and pros/cons)*
- **Input Tokens (est):** ~600
- **Output Tokens (est):** ~8,000
- **Commit:** n/a — analysis only, no files changed
- **Files Created/Modified:** none

---

## Prompt #58
- **Date/Time:** 2026-04-12
- **Prompt:** "Go in depth with the difference in the e-ink displays — what would be the improvements or detriments to each."
- **Input Tokens (est):** ~20
- **Output Tokens (est):** ~6,000
- **Commit:** n/a — analysis only, no files changed
- **Files Created/Modified:** none

---

## Prompt #59
- **Date/Time:** 2026-04-12
- **Prompt:** "OK, update the hardware research with all the details from this research and prompt session. Also update the prompts file and clean grammar and spelling. Commit and push."
- **Input Tokens (est):** ~30
- **Output Tokens (est):** ~8,000
- **Commit:** `ce2f22b` — Add board and display comparison research to hardware docs
- **Files Created/Modified:**
  - `docs/hardware-research.md` (modified — added Board Comparison table with 9 boards, Display Comparison section with 4 e-paper displays and 7 LCD/TFT alternatives, trade-off analysis, firmware impact assessments, and recommendations; updated firmware language from MicroPython to C/C++)
  - `PromptProgression.md` (modified — added Prompts #54–59, grammar and spelling cleanup)

---

## Prompt #60
- **Date/Time:** 2026-04-12
- **Prompt:** "OK, let's research LiPo batteries that I could wire up to these boards easily and run me through estimated cost and battery life on each board and wiring setup process as well."
- **Input Tokens (est):** ~40
- **Output Tokens (est):** ~10,000
- **Commit:** n/a — analysis only, no files changed
- **Files Created/Modified:** none

---

## Prompt #61
- **Date/Time:** 2026-04-12
- **Prompt:** "Could a rechargeable AAA battery work for this?"
- **Input Tokens (est):** ~15
- **Output Tokens (est):** ~3,000
- **Commit:** n/a — analysis only, no files changed
- **Files Created/Modified:** none

---

## Prompt #62
- **Date/Time:** 2026-04-12
- **Prompt:** "What about just 1 battery?"
- **Input Tokens (est):** ~10
- **Output Tokens (est):** ~2,000
- **Commit:** n/a — analysis only, no files changed
- **Files Created/Modified:** none

---

## Prompt #63
- **Date/Time:** 2026-04-12
- **Prompt:** "Update the hardware research — add a section for batteries and expected battery life. Include 2000mAh and 3000mAh options and viable options for that and expected price. Update prompts and website documentation with everything as well. Commit and push."
- **Input Tokens (est):** ~40
- **Output Tokens (est):** ~10,000
- **Commit:** `1e27cb4` — Add battery and power research to hardware docs and website
- **Files Created/Modified:**
  - `docs/hardware-research.md` (modified — added Battery & Power section with board power consumption, LiPo options up to 3000mAh, battery life estimates, charging solutions, wiring diagrams for Pico/XIAO/Pi Zero, AAA NiMH alternative, and recommendation)
  - `website/docs/docs/hardware/materials-list.md` (modified — updated battery section with specific recommendations, added no-boost-converter tip)
  - `website/docs/prompts/index.md` (modified — added Prompts #54–63)
  - `PromptProgression.md` (modified — added Prompts #60–63)

---

## Prompt #64
- **Date/Time:** 2026-04-12
- **Prompt:** "OK, the testing pulled screenshots for the website. I also need the devtool and the setup to have screenshot walkthroughs as well and detailed documentation. Also scan code changes and ensure the tests are up to date."
- **Input Tokens (est):** ~50
- **Output Tokens (est):** ~120,000
- **Commit:** *(included in multi-commit push)*
- **Files Created/Modified:**
  - `testing/devtool/test_dependency_gate.py` (created — tests for `_check_and_install_deps()` distro detection, `_check_docker_toolchain()` startup health check, and simplified output logging)
  - `testing/setup_cli/test_docker_step.py` (created — tests for Step 15 Docker install/daemon/compose detection and build file verification)
  - `testing/setup_cli/test_test_setup.py` (created — tests for `setup_testing()` function, `--test-setup` CLI flag, Docker/Testing status sections)
  - `testing/setup_cli/test_cli_screenshots.py` (created — ANSI-to-PNG rendering pipeline for CLI screenshots via Playwright)
  - `testing/setup_cli/test_prerequisites.py` (modified — added `TestTkinterPrereqCheck` and `TestPyserialPrereqCheck` classes with realistic mock run_cmd responses)
  - `testing/setup_cli/test_vscode_extensions.py` (modified — added `TestCodeOSSDetection` class covering pacman detection, codium path resolution, and proprietary VSCode fallback)
  - `testing/setup_cli/test_cli_navigation.py` (modified — updated step count from 14 to 15, added `TestTestSetupFlag` class and `--test-setup` help mention test)
  - `testing/utils/guide_generator.py` (modified — added setup_cli screenshot descriptions for help, list, status, and test-setup renders)
  - DevTool screenshots generated: 35 PNGs covering all 8 tabs (display emulator with all 6 tools, serial monitor states, flash firmware, asset manager, programs, GPIO pins, connection utility USB/WiFi modes, documentation with search)
  - Setup CLI screenshots generated: 4 PNGs for global flags (help, list, status, test-setup rendered as styled terminal HTML)
  - Test suite: 147 tests passing (90 devtool + 57 setup_cli), 0 failures
  - User guides generated: `testing/guides/devtool_guide.md` (35 screenshots), `testing/guides/setup_cli_guide.md` (4 screenshots), `testing/guides/website_guide.md` (23 screenshots)

---

## Prompt #65
- **Date/Time:** 2026-04-12
- **Prompt:** "Get a few more screenshots for the setup.py util. I want every step captured and put into documentation. Also we need to attach all the screenshots to the associated documentation and update the website to show it."
- **Input Tokens (est):** ~50
- **Output Tokens (est):** ~150,000
- **Commit:** *(included in multi-commit push)*
- **Files Created/Modified:**
  - `testing/setup_cli/test_cli_screenshots.py` (rewritten — added `TestStepScreenshots` class with parametrized tests for all 15 steps, `_capture_step_output()` helper that pipes Enter+quit to capture step headers/explanations, `TestCLIGlobalScreenshots` class for --help/--list/--status/--test-setup)
  - `testing/utils/guide_generator.py` (modified — added 15 step-by-step screenshot descriptions: `setup_cli_step_01` through `setup_cli_step_15`)
  - `website/docs/assets/images/setup-cli/` (created — 19 PNGs: 4 global flag renders + 15 individual step screenshots)
  - `website/docs/assets/images/devtool/` (created — 35 PNGs copied from testing screenshots)
  - `website/docs/docs/tools/setup-cli.md` (rewritten — added 19 embedded screenshots: help output, step list, full step-by-step walkthrough with a screenshot for each of all 15 steps, status dashboard, testing setup; updated step count to 15, added Checkpoint 3, added Code OSS detection and `--test-setup` documentation)
  - `website/docs/docs/tools/devtool.md` (rewritten — added 28 embedded screenshots: every tab overview, all 6 drawing tools individually, drawing demo, inverted canvas, save workflow, serial monitor 3 states, flash firmware with BOOTSEL detection, asset manager list and preview, programs list/preview/deploy, GPIO pin diagram, connection utility USB/WiFi modes, documentation with search; updated architecture for dependency gate, Docker health check, line count ~3400)
  - `website/docs/docs/setup/first-time-setup.md` (modified — added 7 embedded screenshots at toolchain install, Docker setup, checkpoint 1, display connection, and checkpoint 2 sections; updated step count from 14 to 15, added Step 15 Docker row, added status dashboard screenshot)
  - Test suite: 162 tests passing (90 devtool + 72 setup_cli), 0 failures
  - MkDocs site builds successfully with all 54 images resolving across 3 documentation pages

---

## Prompt #66
- **Date/Time:** 2026-04-12
- **Prompt:** "Looks good, let's update the prompts. Look through the entire list of relevant session history in Claude and ensure the entire prompts with error messages are put into the prompt history. Clean up grammar and spelling and account for any prompts that haven't been listed yet. Update while running the commits on all the staged code changes. Be descriptive and push it."
- **Input Tokens (est):** ~60
- **Output Tokens (est):** ~80,000
- **Commit:** *(see commits below)*
- **Files Created/Modified:**
  - `PromptProgression.md` (modified — added Prompts #64–66 covering testing framework creation, step screenshot capture, documentation updates with embedded images, and prompt history update)
  - `website/docs/prompts/index.md` (modified — added Prompts #64–66)

---

## Prompt #67
- **Date/Time:** 2026-04-12
- **Prompt:** "Let's continue the hardware design process. Let's make a 3D print prototyping pipeline MD analysis document and go through every viable off-the-shelf 3D printing option, technologies and price points, and use this to evaluate the most cost-effective and quickest way to CAD design and print a case and mounting system for this hardware. Give a pros and cons list between all the available 3D printing technologies and tech stacks and overhead behind it. Also deep-dive into third-party print options and the pros and cons and price options for this as well. Build a robust document for this with a TOC and pricing estimates. Give several viable options after research."
- **Input Tokens (est):** ~120
- **Output Tokens (est):** ~15,000
- **Commit:** `d61b2ff` — Add 3D printing prototyping pipeline analysis
- **Files Created/Modified:**
  - `hardware-design/3d-printing-pipeline.md` (created — comprehensive 15-section analysis covering FDM/SLA/SLS/MJF technologies, 9 third-party services deep-dived with pricing, material guide, CAD software comparison, cost estimates specific to Dilder enclosure, 5 ranked viable options, decision framework, and scaling path to injection molding)

---

## Prompt #68
- **Date/Time:** 2026-04-12
- **Prompt:** "OK, update the prompts with this and commit and push this doc and update the website as well."
- **Input Tokens (est):** ~25
- **Output Tokens (est):** ~8,000
- **Commit:** `d61b2ff` — Add 3D printing pipeline to website and update prompts
- **Files Created/Modified:**
  - `PromptProgression.md` (modified — added Prompts #67–68)
  - `website/docs/prompts/index.md` (modified — added Prompts #67–68)
  - `website/docs/docs/hardware/3d-printing-pipeline.md` (created — website copy of the pipeline analysis)
  - `website/docs/docs/hardware/enclosure-design.md` (modified — added 3D Printing Pipeline summary section with technology table, recommended approach, top services, and JLCPCB bundling tip)
  - `website/mkdocs.yml` (modified — added "3D Printing Pipeline" to Hardware nav section)

---

## Prompt #69
- **Date/Time:** 2026-04-12
- **Prompt:** "Alright we have a sassy octopus, let's make a sassy supportive octopus — same functionality but just the text should be more oriented to humorous but supportive statements, littered with unhinged but weirdly loving statements, sprinkle in some spicy language, and make a huge list of cycled text for this and add it to the programs to be deployable to the Pico."
- **Input Tokens (est):** ~80
- **Output Tokens (est):** ~12,000
- **Commit:** `da4d979`
- **Files Created/Modified:**
  - `DevTool/devtool.py` (modified — added `SUPPORTIVE_QUOTES` list with 80 quotes, added `supportive_octopus` program entry, parameterized `_draw_chat_bubble` and `_generate_octopus_frame` with tagline, refactored `_run_sassy_octopus` to generic `_run_octopus`, added `_OCTOPUS_CONFIGS` and `_FIRMWARE_DIRS` lookup dicts)
  - `dev-setup/supportive-octopus/main.c` (created — standalone Pico firmware for Supportive Octopus)
  - `dev-setup/supportive-octopus/CMakeLists.txt` (created — CMake build config)
  - `dev-setup/docker-compose.yml` (modified — added `build-supportive-octopus` service)
  - `.gitignore` (modified — added supportive-octopus build artifacts)

---

## Prompt #70
- **Date/Time:** 2026-04-12
- **Prompt:** "OK the sassy quotes are looking sparse compared to the supportive ones, let's expand on this — more unhinged, more weird, more conspiratorial, and more chaotic. Sprinkle in plenty of spicy language and swear words too. Get tin-foiled with some of them, get stupid with the others. Pull from modern memetic conspiracies. And if the quotes are especially weird, give the octopus a weird expression, and especially unhinged, make an unhinged expression."
- **Input Tokens (est):** ~100
- **Output Tokens (est):** ~15,000
- **Commit:** `da4d979`
- **Files Created/Modified:**
  - `DevTool/devtool.py` (modified — expanded `SASSY_QUOTES` from 30 to 124 entries with mood tags, added `MOUTH_WEIRD` and `MOUTH_UNHINGED` expressions with pixel art functions for wobbly sine-wave mouth and jagged scream-mouth, added `_octo_weird_eyes` with misaligned pupils and `_octo_unhinged_eyes` with tiny pinprick pupils, added `_parse_quote` and `_mood_cycle` helpers, updated all rendering and frame generation to use mood-based expression cycling)

---

## Prompt #71
- **Date/Time:** 2026-04-12
- **Prompt:** "OK the DevTool program tab is a bit wonky — when I select a display model it deselects the program. Also the display mode is hard to read once selected, the background lightness ruins the text."
- **Input Tokens (est):** ~40
- **Output Tokens (est):** ~3,000
- **Commit:** `da4d979`
- **Files Created/Modified:**
  - `DevTool/devtool.py` (modified — added `exportselection=False` to program Listbox to prevent deselection on focus loss, added `TCombobox` dark theme styling with proper `fieldbackground`/`foreground`/`selectbackground` for readonly state, added `option_add` for combobox popdown listbox dark theme)

---

## Prompt #72
- **Date/Time:** 2026-04-12
- **Prompt:** "Let's embed the sassy and supportive octopus on the website too, as a banner with all the quotes made. Have it cycle through them at the top."
- **Input Tokens (est):** ~30
- **Output Tokens (est):** ~10,000
- **Commit:** `b447aab`
- **Files Created/Modified:**
  - `website/docs/javascripts/octopus-banner.js` (created — canvas-rendered pixel art octopus with typewriter quote cycling across both sassy and supportive pools, responsive design)
  - `website/docs/stylesheets/extra.css` (modified — added octopus banner styles with dark background, blinking cursor, responsive breakpoints)
  - `website/docs/index.md` (modified — added banner div at top of homepage)
  - `website/mkdocs.yml` (modified — added `extra_javascript` for banner script)

---

## Prompt #73
- **Date/Time:** 2026-04-12
- **Prompt:** "Look at the SASSY_QUOTES and SUPPORTIVE_QUOTES blocks of strings. I want you to double the amount of quotes in each one and get weird with it — go off the rails, get unhinged, conspiratorial, and fun. Silly but match the theme for each block. Don't be afraid to swear or use spicy language."
- **Input Tokens (est):** ~80
- **Output Tokens (est):** ~18,000
- **Commit:** `23e7fd7`
- **Files Created/Modified:**
  - `DevTool/devtool.py` (modified — doubled `SASSY_QUOTES` from 124 to 252, doubled `SUPPORTIVE_QUOTES` from 80 to 160, each section expanded with theme-matched new entries)
  - `website/docs/javascripts/octopus-banner.js` (modified — updated JS quote arrays to match the expanded Python lists)

---

## Prompt #74
- **Date/Time:** 2026-04-12
- **Prompt:** "I want to ensure the programs on the Pi will also contain these quotes."
- **Input Tokens (est):** ~15
- **Output Tokens (est):** ~20,000
- **Commit:** `6b42bde`
- **Files Created/Modified:**
  - `dev-setup/sassy-octopus/main.c` (rewritten — runtime rendering engine replaces pre-baked frames; embeds body RLE, 5×7 bitmap font, all 5 mouth expressions, word-wrap text renderer, ADC-seeded PRNG; renders each frame on-the-fly)
  - `dev-setup/supportive-octopus/main.c` (rewritten — identical runtime renderer)
  - `dev-setup/sassy-octopus/CMakeLists.txt` (modified — removed GUI/Font deps, added hardware_adc and math lib)
  - `dev-setup/supportive-octopus/CMakeLists.txt` (modified — same changes)
  - `DevTool/devtool.py` (modified — replaced `_generate_frames_header` with `_generate_quotes_header` that outputs ~17KB string header instead of ~4MB bitmap data)
  - `.gitignore` (modified — `frames.h` → `quotes.h`)

---

## Prompt #75
- **Date/Time:** 2026-04-12
- **Prompt:** "OK let's look at the DevTool GUI documentation — the screenshots are nice but too damn big to really read. Can we run the test with the GUI again but with a smaller window and capture more readable screenshots?"
- **Input Tokens (est):** ~50
- **Output Tokens (est):** ~15,000
- **Commit:** `75fb79a` — Retake DevTool screenshots at compact 900x550 window size
- **Files Created/Modified:**
  - `DevTool/capture_screenshots.py` (created — automated screenshot capture script that launches the DevTool at 900x550, cycles through all 8 tabs, and saves PNGs via ImageMagick `import`)
  - `website/docs/assets/images/devtool/*.png` (35 files modified — all screenshots resized from 1908x2040 to 976x720, total image size reduced from ~2.5MB to ~1.3MB)

---

## Prompt #76
- **Date/Time:** 2026-04-12
- **Prompt:** "The website still shows the old small pics."
- **Input Tokens (est):** ~10
- **Output Tokens (est):** ~1,000
- **Commit:** n/a — confirmed GitHub Actions deployed successfully; issue was CDN cache (max-age 600s), resolved with hard refresh
- **Files Created/Modified:** none

---

## Prompt #77
- **Date/Time:** 2026-04-12
- **Prompt:** "The tool demo screenshots are all the same blank canvases — nothing shows on them in the screenshots."
- **Input Tokens (est):** ~20
- **Output Tokens (est):** ~20,000
- **Commit:** `7e06495` — Retake all DevTool screenshots with real drawn content
- **Files Created/Modified:**
  - `DevTool/capture_screenshots.py` (rewritten — draws real content for each tool: pencil sine wave, eraser with gap, crossing lines, nested rectangles, overlapping filled rects, multi-size text, house scene with roof/door/tree/sun, inverted version, simulated serial output with heartbeats, Sassy Octopus preview with quote)
  - `website/docs/assets/images/devtool/*.png` (16 detail screenshots replaced — each now shows actual tool output instead of blank canvas copies)

---

## Prompt #78
- **Date/Time:** 2026-04-12
- **Prompt:** "Perfect. Take all my prompts in this session not in the prompt progression and add them. Fix the grammar and spelling and commit."
- **Input Tokens (est):** ~25
- **Output Tokens (est):** ~8,000
- **Commit:** `608ab92` — Add Prompts #75–78 covering screenshot recapture and prompt log update
- **Files Created/Modified:**
  - `PromptProgression.md` (modified — added Prompts #75–78, grammar and spelling cleanup)

---

## Prompt #79
- **Date/Time:** 2026-04-12
- **Prompt:** "OK I have added pictures of the Pico and display setup. Compress into a smaller JPEG and delete the originals in the folders, then put them in the setup guide in the appropriate locations to give a picture of how the hardware looks and is set up."
- **Input Tokens (est):** ~50
- **Output Tokens (est):** ~10,000
- **Commit:** `a6f174c` — Add hardware photos to setup guide — compressed HEIC to JPG
- **Files Created/Modified:**
  - `website/docs/assets/images/hardware/*.jpg` (8 files created — converted from 4096x3072 HEIC to 800px-wide compressed JPG, ~985KB total down from ~21MB)
  - `docs/pictures/*.heic` (8 files deleted — originals removed after conversion)
  - `website/docs/docs/setup/first-time-setup.md` (modified — embedded photos at What You Need, Pico W at a Glance, Waveshare HAT, Seat the Display, Checkpoint 2 sections)

---

## Prompt #80
- **Date/Time:** 2026-04-12
- **Prompt:** "OK let's update the programs — the sassy and supportive octopuses. I want you to move the octopus and chat bubble down more, center vertically. Then let's add the day's date fully written out and the time without seconds, 12-hour format AM/PM, at the top middle."
- **Input Tokens (est):** ~60
- **Output Tokens (est):** ~15,000
- **Commit:** `2532778` — Add date/time header and vertically center octopus layout
- **Files Created/Modified:**
  - `DevTool/devtool.py` (modified — added date/time header rendering with `datetime.now().strftime`, centered at top; added Y_OFF=12 vertical offset to all octopus drawing; added y_offset parameter to `_draw_chat_bubble`)

---

## Prompt #81
- **Date/Time:** 2026-04-12
- **Prompt:** "The clock and height look good on the preview. I need it to also deploy via the C code as well to the Pico."
- **Input Tokens (est):** ~25
- **Output Tokens (est):** ~20,000
- **Commit:** `2864b14` — Add date/time header and vertical centering to standalone Pico firmware
- **Files Created/Modified:**
  - `dev-setup/sassy-octopus/main.c` (modified — added RTC initialization from compile-time `__DATE__`/`__TIME__`, `draw_clock_header()` with month name lookup and 12-hour format, Y_OFF=12 with `px_set_off`/`px_clr_off` helpers, offset applied to all body/eye/mouth/bubble drawing)
  - `dev-setup/sassy-octopus/CMakeLists.txt` (modified — added `hardware_rtc` to link libraries)
  - `dev-setup/supportive-octopus/main.c` (modified — same changes as sassy-octopus)
  - `dev-setup/supportive-octopus/CMakeLists.txt` (modified — added `hardware_rtc`)

---

## Prompt #82
- **Date/Time:** 2026-04-12
- **Prompt:** "Perfect. Update the prompts with this and commit."
- **Input Tokens (est):** ~10
- **Output Tokens (est):** ~5,000
- **Commit:** `17d0953` — Add Prompts #79–82 covering hardware photos, clock header, and Pico deploy
- **Files Created/Modified:**
  - `PromptProgression.md` (modified — added Prompts #79–82, backfilled commit hash for Prompt #78)

---

## Prompt #83
- **Date/Time:** 2026-04-12
- **Prompt:** "OK let's make an angry octopus program. We need to change its eyes to be two slanted half-circles angled in an angry way, then compile a list of nonsensical wacky kind-of-mean quotes but still cute. Then we also want to split out the sassy octopus and pull out the conspiratorial crazy statements into a conspiratorial octopus program. And if there are other emotional states we can map into a program, let's create those as well. Get fun and weird with the quotes and make sure they match the emotion state."
- **Input Tokens (est):** ~100
- **Output Tokens (est):** ~60,000
- **Commit:** `d0cc8fb` — Add Angry, Conspiratorial, Sad, and Chaotic octopus programs
- **Files Created/Modified:**
  - `DevTool/devtool.py` (modified — added MOUTH_ANGRY/SAD/CHAOTIC expressions with pixel art, angry slanted half-circle eyebrows, sad droopy brows, chaotic spiral eyes, angry frown mouth, sad frown, chaotic zigzag mouth, per-program default_mood, ANGRY_QUOTES 45 entries, CONSPIRATORIAL_QUOTES 47 entries split from sassy, SAD_QUOTES 35 entries, CHAOTIC_QUOTES 40 entries, 6 programs registered in PROGRAMS/_OCTOPUS_CONFIGS/_FIRMWARE_DIRS)
  - `dev-setup/angry-octopus/main.c`, `dev-setup/angry-octopus/CMakeLists.txt` (created)
  - `dev-setup/conspiratorial-octopus/main.c`, `dev-setup/conspiratorial-octopus/CMakeLists.txt` (created)
  - `dev-setup/sad-octopus/main.c`, `dev-setup/sad-octopus/CMakeLists.txt` (created)
  - `dev-setup/chaotic-octopus/main.c`, `dev-setup/chaotic-octopus/CMakeLists.txt` (created)
  - `dev-setup/docker-compose.yml` (modified — added 4 new build services)
  - `.gitignore` (modified — added new firmware build/lib/quote artifacts)

---

## Prompt #84
- **Date/Time:** 2026-04-12
- **Prompt:** "That's pretty great. Let's fix the angry one's eyes — they should look like slanted half-circles."
- **Input Tokens (est):** ~20
- **Output Tokens (est):** ~8,000
- **Commit:** `cba64b2` — Fix angry octopus eyebrows — thick slanted half-circle arcs
- **Files Created/Modified:**
  - `DevTool/devtool.py` (modified — rewrote `_octo_angry_eyes()` with proper thick curved arcs using sine-wave sweep across the eye socket width, 3px thick with extra fill, outer high / inner low for V-furrowed brow look)

---

## Prompt #85
- **Date/Time:** 2026-04-12
- **Prompt:** "The angry eyes look good on the preview but the C program eyes don't match — the pupils should be close to the nose and downward."
- **Input Tokens (est):** ~25
- **Output Tokens (est):** ~20,000
- **Commit:** `db5d6cd` — Add angry/sad/chaotic expressions to standalone Pico firmware
- **Files Created/Modified:**
  - `dev-setup/sassy-octopus/main.c` (modified — added MOOD_ANGRY/SAD/CHAOTIC constants, EXPR_ANGRY/SAD/CHAOTIC, `draw_pupils_angry()` with inward+down shifted pupils, `draw_brows_angry()` with matching half-circle arcs, `draw_pupils_sad()` with downward pupils, `draw_brows_sad()` with droopy arcs, `draw_pupils_chaotic()` with spiral ring eyes, `draw_mouth_angry/sad/chaotic()`, updated expression cycles and render_frame switch)
  - All 5 other octopus firmware main.c files updated with same changes

---

## Prompt #86
- **Date/Time:** 2026-04-12
- **Prompt:** "OK update the webpage implementation as well with the new quotes and emotion states."
- **Input Tokens (est):** ~15
- **Output Tokens (est):** ~15,000
- **Commit:** `038ba93` — Add all 6 octopus emotion states to website banner
- **Files Created/Modified:**
  - `website/docs/javascripts/octopus-banner.js` (modified — added ANGRY, CONSPIRATORIAL, SAD, CHAOTIC quote arrays with 25 entries each, updated `buildPool()` to include all 6 pools, updated `updateMode()` with labels and CSS classes for all 6 modes)
  - `website/docs/stylesheets/extra.css` (modified — added `.octo-mode-angry` red, `.octo-mode-conspiratorial` yellow, `.octo-mode-sad` blue, `.octo-mode-chaotic` orange accent colors)

---

## Prompt #87
- **Date/Time:** 2026-04-12
- **Prompt:** "Update the prompts with the latest ones not added and fix grammar and push."
- **Input Tokens (est):** ~15
- **Output Tokens (est):** ~8,000
- **Commit:** `59921bf` — Add Prompts #83–87 covering new octopus programs, expression fixes, and website banner
- **Files Created/Modified:**
  - `PromptProgression.md` (modified — added Prompts #83–87, backfilled commit hash for Prompt #82)

---

## Prompt #88
- **Date/Time:** 2026-04-12
- **Prompt:** "Let's add a hungry and tired and slap happy octopus as well. Implement this on the webpage, on the DevTool preview, and in the C program. Come up with a really good set of quotes for each state."
- **Input Tokens (est):** ~40
- **Output Tokens (est):** ~40,000
- **Commit:** `b8bdf54` — Add Hungry, Tired, and Slap Happy octopus programs
- **Files Created/Modified:**
  - `DevTool/devtool.py` (modified — added MOUTH_HUNGRY/TIRED/SLAPHAPPY expressions, hungry upward-staring eyes, tired half-closed eyelids, slap-happy one-squint-one-manic eyes, drooling mouth, yawn mouth, wobbly grin, HUNGRY_QUOTES 30, TIRED_QUOTES 30, SLAPHAPPY_QUOTES 30, 3 new programs registered)
  - `dev-setup/hungry-octopus/`, `dev-setup/tired-octopus/`, `dev-setup/slaphappy-octopus/` (created — main.c + CMakeLists.txt)
  - All 9 octopus firmware main.c files updated with new expressions
  - `dev-setup/docker-compose.yml` (modified — 3 new build services)
  - `.gitignore` (modified — new build/lib entries)
  - `website/docs/javascripts/octopus-banner.js` (modified — 3 new quote arrays, labels, sources)
  - `website/docs/stylesheets/extra.css` (modified — hungry pink, tired gray, slap-happy teal)

---

## Prompt #89
- **Date/Time:** 2026-04-12
- **Prompt:** "Let's add a lazy octopus and a fat octopus and chill octopus and creepy octopus."
- **Input Tokens (est):** ~20
- **Output Tokens (est):** ~80,000
- **Commit:** `d053296` — Add Lazy, Fat, Chill, Creepy, Excited, Nostalgic, and Homesick octopus programs
- **Files Created/Modified:**
  - `DevTool/devtool.py` (modified — added 7 new expression types: lazy nearly-shut eyes + flat mouth, fat wide pupils + cheek puffs, chill side-glancing + half-smile, creepy heart-shaped pupils + tongue, excited sparkle crosses + wide grin, nostalgic up-right looking + wistful smile, homesick teary eyes + wobbly line; 7 quote lists of 30 each; 7 programs registered)
  - 7 new firmware directories created (lazy/fat/chill/creepy/excited/nostalgic/homesick-octopus)
  - All 16 firmware main.c files updated
  - Docker, gitignore, website JS + CSS all updated

---

## Prompt #90
- **Date/Time:** 2026-04-12
- **Prompt:** "Excited as well and nostalgic."
- **Input Tokens (est):** ~5
- **Output Tokens (est):** ~500
- **Commit:** `ec59806` — Add Prompts #88-95, update website docs for 16 programs and body animations
- **Files Created/Modified:** (included in Prompt #89 commit — both were added in the same batch)

---

## Prompt #91
- **Date/Time:** 2026-04-12
- **Prompt:** "Homesick too."
- **Input Tokens (est):** ~5
- **Output Tokens (est):** ~500
- **Commit:** `ec59806` — Add Prompts #88-95, update website docs for 16 programs and body animations
- **Files Created/Modified:** (included in Prompt #89 commit)

---

## Prompt #92
- **Date/Time:** 2026-04-12
- **Prompt:** "The emotion state doc shouldn't have checkboxes. Also you didn't produce any images of the state or animation for me to view — you only explained it."
- **Input Tokens (est):** ~30
- **Output Tokens (est):** ~15,000
- **Commit:** `efcb22b` — Replace emotion states doc with rendered previews, remove checkboxes
- **Files Created/Modified:**
  - `assets/octopus-emotion-states.md` (rewritten — removed all checkboxes and tracker tables, replaced with clean visual gallery showing each octopus face)
  - `assets/emotion-previews/*.png` (17 files created — rendered at 2x scale from the DevTool engine, one per emotion state)

---

## Prompt #93
- **Date/Time:** 2026-04-12
- **Prompt:** "Let's make some body movement animations and head deformations to match with the emotional states in various ways as well."
- **Input Tokens (est):** ~25
- **Output Tokens (est):** ~50,000
- **Commit:** `b5a3b2f` — Add body movement animations and head deformations per emotional state
- **Files Created/Modified:**
  - `DevTool/devtool.py` (modified — added `_body_transform(mood, frame_count)` returning dx/dy/x_expand/row_wobble per mood, modified `_generate_octopus_frame` to accept `frame_count` and apply transforms to body spans and pixel offsets)
  - All 16 firmware main.c files updated with matching C `setup_body_transform()` function, `draw_body_transformed()`, per-row wobble globals, and `render_frame` now takes `frame_idx` parameter
  - `assets/emotion-previews/*-anim.png` (17 animation strip PNGs created — 4-frame strips showing body movement per mood)
  - `assets/octopus-emotion-states.md` (updated — added animation strips and body animation descriptions to every emotion state)

---

## Prompt #94
- **Date/Time:** 2026-04-12
- **Prompt:** "Also I want images of just the octopus in the MD document, focusing on the animations and clearly annotated and described in each picture. Make a robust set, then apply it."
- **Input Tokens (est):** ~30
- **Output Tokens (est):** ~5,000
- **Commit:** `ec59806` — Add Prompts #88-95, update website docs for 16 programs and body animations
- **Files Created/Modified:** (included in Prompt #93 commit — animation strips were generated in that batch)

---

## Prompt #95
- **Date/Time:** 2026-04-12
- **Prompt:** "OK let's look through the session prompts and add them to the prompt document, then update all the webpages with the new documents and documentation. Fix spelling and grammar too."
- **Input Tokens (est):** ~30
- **Output Tokens (est):** ~30,000
- **Commit:** *(see below)*
- **Files Created/Modified:**
  - `PromptProgression.md` (modified — added Prompts #88–95, backfilled commit hash for Prompt #87)
  - `website/docs/prompts/index.md` (modified — added Prompts #88–95)
  - `website/docs/docs/tools/devtool.md` (modified — updated Programs tab section for 16 programs, added body animation documentation)

---

## Prompt #96
- **Date/Time:** 2026-04-12
- **Prompt:** "OK let's export the octopus and its facial expressions and animations into the assets folder, label and map all the available combinations, and then plan for new implementation. For every emotional state of the octopus planned we need to start moving the body according to its state as well. Give me a nice exhaustive combination of assets that eventually can be put into the C program upon approval. Give me an MD document to outline each state and provide a check mark and notes option for each state for improvements later in Claude."
- **Input Tokens (est):** ~100
- **Output Tokens (est):** ~15,000
- **Commit:** `deb3291` — Add custom fat/lazy octopus bodies, C-faithful renderer, keyboard input plan, and Prompts #96-104
- **Files Created/Modified:**
  - `assets/octopus-emotion-states.md` (created — comprehensive tracker doc with all 13 emotional states, per-feature tables, body motion priority matrix, implementation approach for RLE body transforms, animation cycle reference, and source file reference)

---

## Prompt #97
- **Date/Time:** 2026-04-12
- **Prompt:** "What would it take to map the keyboard actions for the time being to the Pico so that I can play around with user actions on the octopus? Create an MD in the docs and dive into the options."
- **Input Tokens (est):** ~40
- **Output Tokens (est):** ~20,000
- **Commit:** `deb3291` — Add custom fat/lazy octopus bodies, C-faithful renderer, keyboard input plan, and Prompts #96-104
- **Files Created/Modified:**
  - `docs/keyboard-to-pico-input.md` (created — explores 3 options: Serial Command Mode over existing USB CDC, GPIO Button Array on free pins GP0-GP4, and Hybrid; includes full key mapping table for 30+ commands covering mood selection, expression override, animation control, body motion, quote control, and system commands; provides C code snippets for handle_command(), polling main loop, and state variables; GPIO pinout diagram; DevTool integration mockup; 10-step implementation plan)

---

## Prompt #98
- **Date/Time:** 2026-04-12
- **Prompt:** "The fat and lazy octopus legs are hard to differentiate between which leg is which. Perhaps for the fat one make the octopus fat up top with a bit thicker legs, and with the lazy one make it lounge on its side with a tentacle on its belly lying like a French woman."
- **Input Tokens (est):** ~50
- **Output Tokens (est):** ~40,000
- **Commit:** `deb3291` — Add custom fat/lazy octopus bodies, C-faithful renderer, keyboard input plan, and Prompts #96-104
- **Files Created/Modified:**
  - `dev-setup/fat-octopus/main.c` (modified — replaced `body_rle[]` with custom wider body: dome starts 2 rows higher, +5px per side at peak, no waist taper, tentacles widened +1px per side; updated `setup_body_transform` to remove `body_x_expand=3` since body is inherently fat)
  - `dev-setup/lazy-octopus/main.c` (modified — replaced `body_rle[]` with reclining pose: asymmetric body sloping rightward, belly tentacle overlay function, sprawling tentacles; updated `setup_body_transform`)
  - `DevTool/devtool.py` (modified — added `_octo_body_fat()`, `_octo_body_lazy()`, `_octo_belly_tentacle_lazy()`, updated `_body_transform()` and `_generate_octopus_frame()` to use mood-specific bodies)

---

## Prompt #99
- **Date/Time:** 2026-04-12
- **Prompt:** "Use the C implementation of the animations and produce accurately a set of images in the assets folder to compare against the Python."
- **Input Tokens (est):** ~25
- **Output Tokens (est):** ~50,000
- **Commit:** `deb3291` — Add custom fat/lazy octopus bodies, C-faithful renderer, keyboard input plan, and Prompts #96-104
- **Files Created/Modified:**
  - `assets/render_c_previews.py` (created — standalone Python script that is a 1:1 port of every C firmware drawing function: `fill_circle`, all `draw_pupils_*`, `draw_brows_*`, `draw_lids_*`, `draw_mouth_*`, body RLE decode, chat bubble, body transforms, and row wobble; renders all 16 moods to PNG at 4x scale plus a comparison grid)
  - `assets/c-render/*.png` (16 individual mood PNGs + `_grid_all_moods.png` generated)
  - `assets/py-render/*.png` (16 Python devtool renders regenerated for comparison)
  - `assets/c-vs-python-key-comparison.png` (created — side-by-side Normal/Fat/Lazy comparison)
  - `assets/c-vs-python-comparison.png` (created — side-by-side all 16 moods)

---

## Prompt #100
- **Date/Time:** 2026-04-12
- **Prompt:** "Lazy octopus looks weird. Just have him sit on his side with his legs draped to the right."
- **Input Tokens (est):** ~20
- **Output Tokens (est):** ~15,000
- **Commit:** `deb3291` — Add custom fat/lazy octopus bodies, C-faithful renderer, keyboard input plan, and Prompts #96-104
- **Files Created/Modified:**
  - `dev-setup/lazy-octopus/main.c` (modified — replaced reclining body_rle with simpler design: standard head dome + body, cheeks taper rightward, all 5 tentacles sweep diagonally to the right with organic sine wobble; removed `draw_belly_tentacle_lazy()` call from render_frame)
  - `DevTool/devtool.py` (modified — updated `_octo_body_lazy()` to match new tentacles-draped-right design, removed belly tentacle from frame builder)
  - `assets/render_c_previews.py` (modified — updated `BODY_RLE_LAZY` and removed belly tentacle from `MOOD_CONFIG`)
  - All preview PNGs regenerated

---

## Prompt #101
- **Date/Time:** 2026-04-12
- **Prompt:** "Compare the C renders with the Python images and make sure they line up. Also with the C render, split up each octopus into its own image file named like the emotion previews."
- **Input Tokens (est):** ~30
- **Output Tokens (est):** ~10,000
- **Commit:** `deb3291` — Add custom fat/lazy octopus bodies, C-faithful renderer, keyboard input plan, and Prompts #96-104
- **Files Created/Modified:**
  - `assets/render_c_previews.py` (modified — added full `setup_body_transform()` with body_dx/dy/x_expand/wobble matching C firmware, added `body_x_expand` to `draw_body()`, added `row_wobble()` to `px_set_off`/`px_clr_off`)
  - `assets/emotion-previews/*.png` (all 34 files regenerated — 17 statics + 17 anim strips from C-faithful renderer)
  - `assets/c-render/*.png` (regenerated with body transforms applied)
  - `assets/py-render/*.png` (regenerated for comparison)
  - Pixel comparison: 10/16 moods pixel-perfect match, remaining 6 within 256 pixels (sinf rounding)

---

## Prompt #102
- **Date/Time:** 2026-04-12
- **Prompt:** "C renders need to be generated now too."
- **Input Tokens (est):** ~10
- **Output Tokens (est):** ~500
- **Commit:** `deb3291` — Add custom fat/lazy octopus bodies, C-faithful renderer, keyboard input plan, and Prompts #96-104
- **Files Created/Modified:**
  - `assets/c-render/*.png` (regenerated — 16 individual PNGs + grid)

---

## Prompt #103
- **Date/Time:** 2026-04-12
- **Prompt:** "The C renders don't have as many as the emotion previews though."
- **Input Tokens (est):** ~15
- **Output Tokens (est):** ~5,000
- **Commit:** `deb3291` — Add custom fat/lazy octopus bodies, C-faithful renderer, keyboard input plan, and Prompts #96-104
- **Files Created/Modified:**
  - `assets/c-render/*-anim.png` (17 animation strips generated to match emotion-previews)
  - `assets/c-render/supportive.png` and `assets/c-render/supportive-anim.png` (copied from normal)
  - `assets/py-render/*-anim.png` (17 animation strips generated)
  - `assets/py-render/supportive.png` and `assets/py-render/supportive-anim.png` (copied from normal)
  - All three folders now contain matching 34-file sets

---

## Prompt #104
- **Date/Time:** 2026-04-12
- **Prompt:** "OK go through session history, find all my new prompts, update the prompt document, commit and push the change. Be as descriptive as possible. Update docs and the website as well."
- **Input Tokens (est):** ~30
- **Output Tokens (est):** ~40,000
- **Commit:** `deb3291` — Add custom fat/lazy octopus bodies, C-faithful renderer, keyboard input plan, and Prompts #96-104
- **Files Created/Modified:**
  - `PromptProgression.md` (modified — added Prompts #96–104)
  - `website/docs/prompts/index.md` (modified — added Prompts #93–104)
  - `assets/octopus-emotion-states.md` (modified — updated Fat and Lazy body descriptions)
  - All changes committed and pushed

---

## Prompt #105
- **Date/Time:** 2026-04-12
- **Prompt:** "OK let's implement a new project that combines all the emotional states of the octopus and put the state below and allow keyboard input to go left and right to select a new state and show the quotes for the states. Show < on the left and > on the right to indicate the selection and put the state bottom middle."
- **Input Tokens (est):** ~75
- **Output Tokens (est):** ~80,000
- **Commit:** `dd837c7` — Add Mood Selector program, comprehensive programs guide, and Prompts #105-111
- **Files Created/Modified:**
  - `dev-setup/mood-selector/main.c` (created — 1,305-line C firmware combining all 16 emotional states into one interactive program; includes all pupil/mouth/brow/lid/tear drawing functions, body transforms, expression cycles, quote filtering by mood, serial input polling with `[`/`]` navigation, and `< MOOD_NAME >` status bar at screen bottom)
  - `dev-setup/mood-selector/quotes.h` (created — auto-generated, 823 quotes from all 16 moods, 51.6 KB)
  - `dev-setup/mood-selector/generate_quotes.py` (created — Python script that extracts all quote lists from `devtool.py` and generates the combined `quotes.h`)
  - `dev-setup/mood-selector/CMakeLists.txt` (created — Pico SDK build config with display variant selection)
  - `dev-setup/mood-selector/pico_sdk_import.cmake` (copied from sassy-octopus)
  - `dev-setup/mood-selector/lib/` (copied — Waveshare display drivers)
  - `DevTool/devtool.py` (modified — added `mood_selector` to `PROGRAMS`, `_OCTOPUS_CONFIGS` with all quotes concatenated, and `_FIRMWARE_DIRS`)
  - Font extended with `<` and `>` glyph bitmaps (indices 49, 50) in `font5x7[]` array

---

## Prompt #106
- **Date/Time:** 2026-04-12
- **Prompt:** "Also provide input options on the program main page that map to the Pico."
- **Input Tokens (est):** ~20
- **Output Tokens (est):** ~5,000
- **Commit:** `dd837c7` — Add Mood Selector program, comprehensive programs guide, and Prompts #105-111
- **Files Created/Modified:**
  - `dev-setup/mood-selector/main.c` (modified — added `print_help()` function that prints full key mapping table to serial on startup and on `?` keypress; includes mood navigation `[`/`]`, direct selection letters `n/w/u/a/s/c/h/t/p/l/f/k/y/e/o/m`, quote refresh `q`, and random mood `r`)

---

## Prompt #107
- **Date/Time:** 2026-04-12
- **Prompt:** "Move the mood selector more to the bottom and put the actual emotion state in the text field, not mood selector, with < char and > char instead of ~."
- **Input Tokens (est):** ~30
- **Output Tokens (est):** ~3,000
- **Commit:** `dd837c7` — Add Mood Selector program, comprehensive programs guide, and Prompts #105-111
- **Files Created/Modified:**
  - `dev-setup/mood-selector/main.c` (modified — moved status bar to `IMG_H - 8` for flush-bottom positioning; replaced `~ MOOD SELECTOR ~` tagline with dynamic `< MOOD_NAME >` using `<` and `>` characters; restored bubble to full 70px height)

---

## Prompt #108
- **Date/Time:** 2026-04-12
- **Prompt:** "Also when deploying to the Pi give a clear indication of the [] buttons and whether they were pressed and what mood is showing on the Pico."
- **Input Tokens (est):** ~25
- **Output Tokens (est):** ~5,000
- **Commit:** `dd837c7` — Add Mood Selector program, comprehensive programs guide, and Prompts #105-111
- **Files Created/Modified:**
  - `dev-setup/mood-selector/main.c` (modified — enhanced serial output: each keypress now logs `KEY 'x' pressed | >> RIGHT | SASSY --> WEIRD` with direction indicator `<< LEFT`/`>> RIGHT`/`?? RAND`/`== JUMP`, previous and new mood names, position counter `(N/16)`, and separator lines; frame log updated to show `Frame N | < MOOD > (N/16) | "QUOTE"`)

---

## Prompt #109
- **Date/Time:** 2026-04-12
- **Prompt:** "The firmware started with the program though." (Regarding serial input not working — Pico detected at `/dev/ttyACM0` via `/dev/serial/by-id/`)
- **Input Tokens (est):** ~10
- **Output Tokens (est):** ~500
- **Commit:** `dd837c7` — Add Mood Selector program, comprehensive programs guide, and Prompts #105-111
- **Files Created/Modified:**
  - No files modified — troubleshooting session: confirmed Pico serial device at `/dev/serial/by-id/usb-Raspberry_Pi_Pico_*`, instructed to connect with `screen /dev/ttyACM0 115200` or `picocom`

---

## Prompt #110
- **Date/Time:** 2026-04-12
- **Prompt:** (Build failure: `no such service: build-mood-selector` — Docker compose missing the mood-selector service)
- **Input Tokens (est):** ~15
- **Output Tokens (est):** ~2,000
- **Commit:** `dd837c7` — Add Mood Selector program, comprehensive programs guide, and Prompts #105-111
- **Files Created/Modified:**
  - `dev-setup/docker-compose.yml` (modified — added `build-mood-selector` service with volumes mapping `./mood-selector:/project` and `./hello-world/lib:/project/lib`)

---

## Prompt #111
- **Date/Time:** 2026-04-12
- **Prompt:** "OK update the documentation and give an in-depth breakdown of every program and its uses and how to use it fully and provide screenshots. Make a new MD with a TOC for all of the options, then update the prompt, fix spelling, pull latest prompts, and all that. Commit and push."
- **Input Tokens (est):** ~50
- **Output Tokens (est):** ~60,000
- **Commit:** `dd837c7` — Add Mood Selector program, comprehensive programs guide, and Prompts #105-111
- **Files Created/Modified:**
  - `docs/programs-guide.md` (created — comprehensive guide to all 19 programs with TOC, display layout diagram, animation cycle docs, building/flashing instructions, per-program sections with preview images and feature tables, mood selector serial input reference with connection instructions, and comparison table)
  - `website/docs/docs/software/project-structure.md` (modified — updated directory tree to include all 16 octopus programs, mood-selector, keyboard-to-pico-input.md, and programs-guide.md)
  - `PromptProgression.md` (modified — added Prompts #105–111)
  - `website/docs/prompts/index.md` (modified — added Prompts #102–107)
  - `.gitignore` (modified — added mood-selector build/lib/cmake excludes)
  - All changes committed and pushed

---

## Prompt #112
- **Date/Time:** 2026-04-12
- **Prompt:** "How do I input via the computer connected to the mood selector app? The keys aren't working right now."
- **Input Tokens (est):** ~20
- **Output Tokens (est):** ~500
- **Commit:** `4e891f6` — Add collapsible program tree, update Prompts #112-118
- **Files Created/Modified:**
  - No files modified — troubleshooting: Pico found at `/dev/serial/by-id/usb-Raspberry_Pi_Pico_*` (`/dev/ttyACM0`), instructed to connect with `screen /dev/ttyACM0 115200`, `picocom`, or `minicom`; noted that only one program can hold the serial port at a time

---

## Prompt #113
- **Date/Time:** 2026-04-12
- **Prompt:** "The firmware started with the program though." (Clarifying that the Pico was running but serial input wasn't reaching it)
- **Input Tokens (est):** ~10
- **Output Tokens (est):** ~300
- **Commit:** `4e891f6` — Add collapsible program tree, update Prompts #112-118
- **Files Created/Modified:**
  - No files modified — confirmed device present at `/dev/ttyACM0` via `/dev/serial/by-id/`; issue was that no serial terminal was connected to send keystrokes to the firmware

---

## Prompt #114
- **Date/Time:** 2026-04-12
- **Prompt:** "We need to organize the programs — they are getting too complex. Let's make a tree structure for it that expands and collapses. Use your best judgment, don't make it more than 3 deep."
- **Input Tokens (est):** ~35
- **Output Tokens (est):** ~15,000
- **Commit:** `b0fd97a` — Add joystick wiring guide, update materials list, and sync Prompts #114-133
- **Files Created/Modified:**
  - `DevTool/devtool.py` (modified — replaced flat `tk.Listbox` program selector with collapsible `ttk.Treeview`; added `PROGRAM_TREE` data structure defining 3-level hierarchy; added `_TOOL_PROGRAMS` dict for utility program metadata; added `_tree_id_to_key` mapping; updated `_build_ui()` to populate tree with categories and subcategories; updated `_get_selected_key()` to use Treeview selection; updated `_on_select()` to look up programs in both `PROGRAMS` and `_TOOL_PROGRAMS` dicts; styled with `Prog.Treeview` theme matching dark UI)

---

## Prompt #115
- **Date/Time:** 2026-04-12
- **Prompt:** (Runtime error: `_tkinter.TclError: unknown option "-width"` — `ttk.Treeview` does not accept a `width` constructor argument)
- **Input Tokens (est):** ~15
- **Output Tokens (est):** ~500
- **Commit:** `b0fd97a` — Add joystick wiring guide, update materials list, and sync Prompts #114-133
- **Files Created/Modified:**
  - `DevTool/devtool.py` (modified — replaced `width=28` constructor kwarg with `self.prog_tree.column("#0", width=220, minwidth=180)` which is the correct Treeview API for setting column width)

---

## Prompt #116
- **Date/Time:** 2026-04-12
- **Prompt:** "I think we need to add a level for 'Octopus' to contain all the things below Tools."
- **Input Tokens (est):** ~20
- **Output Tokens (est):** ~2,000
- **Commit:** `b0fd97a` — Add joystick wiring guide, update materials list, and sync Prompts #114-133
- **Files Created/Modified:**
  - `DevTool/devtool.py` (modified — restructured `PROGRAM_TREE`: merged "Emotional States" and "Interactive" under a single "Octopus" top-level category; tree is now Tools > [programs] and Octopus > Classic/Intense/Melancholy/Playful/Relaxed/Interactive > [programs]; maintains 3-level max depth)

---

## Prompt #117
- **Date/Time:** 2026-04-12
- **Prompt:** "OK run through all the session prompts for this project again and update the prompt document. Fix grammar while you're at it."
- **Input Tokens (est):** ~25
- **Output Tokens (est):** ~20,000
- **Commit:** `b0fd97a` — Add joystick wiring guide, update materials list, and sync Prompts #114-133
- **Files Created/Modified:**
  - `PromptProgression.md` (modified — added Prompts #112–117, corrected website prompt index reference in #111)
  - `website/docs/prompts/index.md` (modified — added Prompts #108–113)

---

## Prompt #118
- **Date/Time:** 2026-04-12
- **Prompt:** "OK run through all the session prompts for this project again and update the prompt document. Fix grammar while you're at it." (Duplicate of #117 — prompted commit of uncommitted changes)
- **Input Tokens (est):** ~25
- **Output Tokens (est):** ~2,000
- **Commit:** `b0fd97a` — Add joystick wiring guide, update materials list, and sync Prompts #114-133
- **Files Created/Modified:**
  - `PromptProgression.md` (modified — added Prompt #118)
  - `DevTool/devtool.py`, `PromptProgression.md`, `website/docs/prompts/index.md` — all committed and pushed

---

## Prompt #119
- **Date/Time:** 2026-04-13
- **Prompt:** "I've done a bit of research on the Pico and since the Raspberry Pi Pico W features the CYW43439 chip, it supports both Wi-Fi and Bluetooth (BLE). Depending on whether you have an existing Wi-Fi network or want the devices to work entirely independently, there are three primary ways to achieve discovery and synchronization. [Detailed research on Wi-Fi Infrastructure Mode, Wi-Fi SoftAP Mode, and BLE Advertising including detection/sync mechanisms, pros/cons, and handshake logic.] What I would like to have is a feature that synchronizes with other Picos running this pet and provides a bonus or notification to indicate that you discovered other players. Add a research document for this feature to the root docs folder."
- **Input Tokens (est):** ~500
- **Output Tokens (est):** ~8,000
- **Commit:** `b0fd97a` — Add joystick wiring guide, update materials list, and sync Prompts #114-133
- **Files Created/Modified:**
  - `docs/peer-discovery-research.md` (created — full research document covering three communication methods, recommended BLE approach, discovery protocol design with 13-byte handshake packet, validation logic, cooldown timer, reward/notification system with animations and stat boosts, encounter log data structure, display feedback, technical considerations for power/flash/versioning/security, and phased implementation plan A–E)

---

## Prompt #120
- **Date/Time:** 2026-04-13
- **Prompt:** "I think another component of peer discovery would be mating prospects to create unique offspring based on the other types of creatures met via proximity."
- **Input Tokens (est):** ~30
- **Output Tokens (est):** ~6,000
- **Commit:** `b0fd97a` — Add joystick wiring guide, update materials list, and sync Prompts #114-133
- **Files Created/Modified:**
  - `docs/peer-discovery-research.md` (modified — added Mating & Offspring System section: genetic trait system with 17-bit genome encoding 6 traits, 45/45/10 inheritance algorithm, mating eligibility conditions, offspring lifecycle with egg/hatching/slots, offspring data structure, generation tracking, BLE protocol extension for gene exchange, display integration for mating events; expanded implementation phases from A–E to A–I; added new open questions about trait rendering, offspring permanence, cross-pollination, and consent UX)

---

## Prompt #121
- **Date/Time:** 2026-04-13
- **Prompt:** "I suppose with a mating system we could generate unique animals and creatures as a result based on this but would it get too complex to compute this on a Pico?"
- **Input Tokens (est):** ~30
- **Output Tokens (est):** ~4,000
- **Commit:** `b0fd97a` — Add joystick wiring guide, update materials list, and sync Prompts #114-133
- **Files Created/Modified:**
  - `docs/peer-discovery-research.md` (modified — added Computational Feasibility on the Pico W section: genetics calculation cost analysis showing sub-microsecond execution, rendering cost breakdown showing table lookups vs hardcoded values are identical cost, combinatorial variety analysis showing 131,072 unique combinations from ~308 bytes of lookup tables, SRAM budget showing ~45 bytes additional, flash budget showing ~3.4KB additional, and hardware limitation analysis confirming the Pico W has orders of magnitude more resources than needed)

---

## Prompt #122
- **Date/Time:** 2026-04-13
- **Prompt:** "Also tell me what it would take to add more flash memory if that would be needed."
- **Input Tokens (est):** ~15
- **Output Tokens (est):** ~6,000
- **Commit:** `b0fd97a` — Add joystick wiring guide, update materials list, and sync Prompts #114-133
- **Files Created/Modified:**
  - `docs/hardware-research.md` (modified — added Flash Memory Expansion section: current flash budget analysis, Option 0 Pico 2 W upgrade, Option 1 SPI NOR flash chips W25Q16–W25Q128 with pricing and SPI0 wiring table, Option 2 pre-assembled breakout modules, Option 3 MicroSD card, comparison summary table, and tiered recommendation)

---

## Prompt #123
- **Date/Time:** 2026-04-13
- **Prompt:** "Is there a way to get 100+ MB of flash?"
- **Input Tokens (est):** ~10
- **Output Tokens (est):** ~2,500
- **Commit:** `b0fd97a` — Add joystick wiring guide, update materials list, and sync Prompts #114-133
- **Files Created/Modified:**
  - (No files modified — conversational response explaining SPI NAND flash chips W25N01GV through W25N04KV with pricing, NOR vs NAND trade-offs table, and recommendation that MicroSD is the better choice for 100+ MB)

---

## Prompt #124
- **Date/Time:** 2026-04-13
- **Prompt:** "Give the price and update the docs."
- **Input Tokens (est):** ~10
- **Output Tokens (est):** ~8,000
- **Commit:** `b0fd97a` — Add joystick wiring guide, update materials list, and sync Prompts #114-133
- **Files Created/Modified:**
  - `docs/hardware-research.md` (modified — added Option 3 SPI NAND Flash section with W25N512GV through W25N04KV chip lineup and pricing, NOR vs NAND comparison table, driver complexity notes mentioning dhara FTL library, breakout module availability; restructured Option 4 MicroSD with clearer pricing; expanded comparison summary table with all NAND options; updated recommendation with two paths to 100+ MB)

---

## Prompt #125
- **Date/Time:** 2026-04-13
- **Prompt:** "How much more power hungry is the Pi Zero?"
- **Input Tokens (est):** ~10
- **Output Tokens (est):** ~1,500
- **Commit:** `b0fd97a` — Add joystick wiring guide, update materials list, and sync Prompts #114-133
- **Files Created/Modified:**
  - (No files modified — conversational response referencing existing battery life data from hardware-research.md: Pi Zero W draws 3.2x more active power, 35x more in sleep, needs a boost converter, and lasts ~12 hours on 1000mAh vs 6.8 days for the Pico W)

---

## Prompt #126
- **Date/Time:** 2026-04-13
- **Prompt:** "Can I get a Pico with a larger NAND memory somewhere somehow?"
- **Input Tokens (est):** ~15
- **Output Tokens (est):** ~3,000
- **Commit:** `b0fd97a` — Add joystick wiring guide, update materials list, and sync Prompts #114-133
- **Files Created/Modified:**
  - (No files modified — conversational response explaining no Pico-class board ships with NAND; listed RP2040/RP2350 boards with extra NOR flash including WeAct RP2040, SparkFun Thing Plus, and Pimoroni Pico Plus 2 W with 16MB flash + 8MB PSRAM at ~$14; confirmed 100+ MB always requires external add-on)

---

## Prompt #127
- **Date/Time:** 2026-04-13
- **Prompt:** "Add this to the doc and give the power consumption estimates."
- **Input Tokens (est):** ~10
- **Output Tokens (est):** ~8,000
- **Commit:** `b0fd97a` — Add joystick wiring guide, update materials list, and sync Prompts #114-133
- **Files Created/Modified:**
  - `docs/hardware-research.md` (modified — expanded Option 0 into full board upgrade comparison table with Pico W, Pico 2 W, Adafruit Feather RP2040, SparkFun Thing Plus RP2040, and Pimoroni Pico Plus 2 W; added power consumption comparison table for all boards; added battery life estimates showing Pimoroni at ~5.5–6.0 days vs Pico 2 W at ~6.4 days; added external flash power consumption table for NOR, NAND, MicroSD, and PSRAM; updated comparison summary with power column; updated recommendation to include Pimoroni as Option 3)

---

## Prompt #128
- **Date/Time:** 2026-04-13
- **Prompt:** "Let's look at the Chinese market and tell me if there is a Pico-like board with Wi-Fi and a lot of memory."
- **Input Tokens (est):** ~20
- **Output Tokens (est):** ~8,000
- **Commit:** `b0fd97a` — Add joystick wiring guide, update materials list, and sync Prompts #114-133
- **Files Created/Modified:**
  - (No files modified — conversational research response covering Chinese MCU boards: ESP32-S3 boards from WeAct, Luatos, YD, and Lolin with 16MB flash + 8MB PSRAM + WiFi + BLE at $3.50–6; RP2040 boards from WeAct and YD with 16MB flash but no wireless at $2.50–3.50; exotic options like Sipeed BL616/BL808; trade-off analysis of Pico SDK vs ESP-IDF migration)

---

## Prompt #129
- **Date/Time:** 2026-04-13
- **Prompt:** "Give me the processor specs and speed."
- **Input Tokens (est):** ~10
- **Output Tokens (est):** ~6,000
- **Commit:** `b0fd97a` — Add joystick wiring guide, update materials list, and sync Prompts #114-133
- **Files Created/Modified:**
  - (No files modified — conversational response with detailed ESP32-S3 vs RP2040 vs RP2350 comparison: CPU architecture, clock speeds, FPU, DSP, cache sizes, DMA, crypto acceleration, CoreMark and Dhrystone benchmarks, power consumption comparison)

---

## Prompt #130
- **Date/Time:** 2026-04-13
- **Prompt:** "Also give me the documentation rating for these options and how easy code would be given the docs and API and resources available."
- **Input Tokens (est):** ~25
- **Output Tokens (est):** ~2,000
- **Commit:** `b0fd97a` — Add joystick wiring guide, update materials list, and sync Prompts #114-133
- **Files Created/Modified:**
  - (No files modified — conversational response with developer experience ratings for Pico SDK, Pico SDK 2.x, and ESP-IDF across documentation quality, getting started ease, API clarity, community support, example code, BLE maturity, e-ink library support, Arduino support, and toolchain setup)

---

## Prompt #131
- **Date/Time:** 2026-04-13
- **Prompt:** "Other than e-ink, what is another very low watt screen option for this project?"
- **Input Tokens (est):** ~15
- **Output Tokens (est):** ~6,000
- **Commit:** `b0fd97a` — Add joystick wiring guide, update materials list, and sync Prompts #114-133
- **Files Created/Modified:**
  - (No files modified — conversational research response covering Sharp Memory LCD, OLED, and Nokia PCD8544 displays: Sharp LS013B7DH03 as top pick with 1µA standby and 10–20 fps animation at $15–25; SSD1306 OLED as runner-up at $2–5 with 60 fps but 100–250x more power; PCD8544 as retro budget option at $1–3 but only 84x48 resolution; full comparison matrix of power, animation, sunlight readability, battery life, and pricing)

---

## Prompt #132
- **Date/Time:** 2026-04-13
- **Prompt:** "Get all the session prompts for this project and add to the prompts and commit and push the code."
- **Input Tokens (est):** ~20
- **Output Tokens (est):** ~15,000
- **Commit:** `b0fd97a` — Add joystick wiring guide, update materials list, and sync Prompts #114-133
- **Files Created/Modified:**
  - `PromptProgression.md` (modified — added Prompts #119–132)
  - `docs/peer-discovery-research.md` (created)
  - `docs/hardware-research.md` (modified)
  - All changes committed and pushed

---

## Prompt #133
- **Date/Time:** 2026-04-13
- **Prompt:** "OK today I should be receiving this DollaTek 5pcs Five Direction Navigation Button Module for MCU AVR Game 5D Rocker Joystick... let's make a wiring and setup plan to begin testing this component with the Pico board and suggest the ideal way to wire this given the screen and headers already being used and also tell me if a GPS module could be attached along with an accelerometer."
- **Input Tokens (est):** ~250
- **Output Tokens (est):** ~30,000
- **Commit:** `2147300` — Add LiPo battery wiring guide, update materials and pinout, add Prompts #133-134
- **Files Created/Modified:**
  - `website/docs/docs/hardware/joystick-wiring.md` (created — full wiring guide with TOC, step-by-step instructions, wiring diagram, C and MicroPython test code, debounce notes, GPIO budget, future expansion compatibility, troubleshooting table)
  - `website/mkdocs.yml` (modified — added Joystick Wiring nav entry under Hardware)
  - `website/docs/docs/hardware/materials-list.md` (modified — added DollaTek 5-Way Navigation Button Module)
  - `website/docs/docs/hardware/wiring-pinout.md` (modified — added joystick module cross-reference)
  - `PromptProgression.md` (modified — added Prompt #133)
  - `website/docs/prompts/index.md` (modified — added Prompts #114–133)
  - All changes committed and pushed

---

## Prompt #134
- **Date/Time:** 2026-04-13
- **Prompt:** "OK let's also make a plan for this component as well: InnCraft Energy Lithium Polymer Battery 1000 mAh 3.7V, 51x34x5 Model 503450 2P Molex 51021-020 1.25mm Connection. Guide me through wiring this up and make another MD hardware doc on this."
- **Input Tokens (est):** ~100
- **Output Tokens (est):** ~25,000
- **Commit:** `2147300` — Add LiPo battery wiring guide, update materials and pinout, add Prompts #133-134
- **Files Created/Modified:**
  - `website/docs/docs/hardware/battery-wiring.md` (created — full LiPo wiring guide with TOC, 3 wiring options, step-by-step for direct and TP4056, safety guide, voltage monitoring code in C and MicroPython, battery life estimates, charging behavior, troubleshooting)
  - `website/mkdocs.yml` (modified — added Battery Wiring nav entry under Hardware)
  - `website/docs/docs/hardware/materials-list.md` (modified — updated 1000mAh battery entry with InnCraft product link and Molex connector details)
  - `website/docs/docs/hardware/wiring-pinout.md` (modified — added battery VSYS/GND to pin budget table and cross-reference)
  - `PromptProgression.md` (modified — added Prompts #133–134)
  - `website/docs/prompts/index.md` (modified — added Prompt #134)
  - All changes committed and pushed

---

## Prompt #135
- **Date/Time:** 2026-04-13
- **Prompt:** "OK let's get the user engagement plan committed and up on the site as well. Update prompts in this process too, and commit and push."
- **Input Tokens (est):** ~30
- **Output Tokens (est):** ~5,000
- **Commit:** `9379cb0` — Add user engagement plan to website docs, update Prompt #135
- **Files Created/Modified:**
  - `website/docs/docs/design/user-engagement-plan.md` (created — copied from `docs/user-engagement-plan.md` to website; comprehensive game design document with 21 sections covering gameplay loops, stat system, emotional state engine, sensor interactions, life stages, progression, dialogue, treasure hunts, step rewards, hardware requirements, virtual pet research, and phased rollout plan)
  - `website/mkdocs.yml` (modified — added Design section with User Engagement Plan entry)
  - `PromptProgression.md` (modified — added Prompt #135)
  - `website/docs/prompts/index.md` (modified — added Prompt #135)
  - `docs/user-engagement-plan.md` (committed — was previously untracked)
  - All changes committed and pushed

---

## Prompt #136
- **Date/Time:** 2026-04-14
- **Prompt:** "OK take a look at this project https://github.com/7west/PicoTop/ — this guy designed a purpose-built Pico with the components he wanted to do the things he designed it to do, a simple desktop. But I want to look at this codebase and see how the PicoTop board was designed and implemented. Reverse this process based on the repo and outline this in a research document in the docs folder of the root. Make an in-depth MD file and also research what it would take to design a board with all the components I have planned for this project. Outline how they can be designed, what open technologies can be used to create the schematics, and how it can be brought into a physical reality, and what services could be used to print out a custom board. Give me a TOC and ample resources that will guide me through this concept to a fleshed-out board and map of learning and implementation plan to do this."
- **Input Tokens (est):** ~200
- **Output Tokens (est):** ~50,000
- **Commit:** `b6ec18d` — Add custom PCB design research with PicoTop case study and learning path
- **Files Created/Modified:**
  - `docs/custom-pcb-design-research.md` (created — comprehensive 14-section research document: PicoTop reverse-engineering case study with full component inventory and manufacturing pipeline analysis; Dilder custom board target specification with component map, interface diagram, power architecture, and phased board tiers; PCB design tool comparison (KiCad 10, LibrePCB, Horizon EDA); RP2040 minimal circuit with LCSC BOM; full schematic-to-board workflow; fabrication service comparison (JLCPCB, PCBWay, OSH Park, Aisler, Seeed); component sourcing strategy; system block diagram with I2C bus and power tree; 15-week learning path from zero to custom board; curated resources including videos, books, and communities; cost estimate (~$21/board for 5-board run); risk assessment; and milestone-based implementation plan)
  - `PromptProgression.md` (modified — added Prompt #136)
  - `website/docs/prompts/index.md` (modified — added Prompt #136)
  - All changes committed and pushed

---

## Prompt #137
- **Date/Time:** 2026-04-14
- **Prompt:** "Let's update the website as well with this research and a blog post for this and add some other blog posts for the latest changes implemented as well that would make sense to add."
- **Input Tokens (est):** ~30
- **Output Tokens (est):** ~15,000
- **Commit:** `69ad9a9` — Add breadboard wiring guide, PCB research to site, 4 blog posts, Prompts #137-140
- **Files Created/Modified:**
  - `website/docs/docs/design/custom-pcb-design-research.md` (created — PCB research added to website Design section)
  - `website/mkdocs.yml` (modified — added Custom PCB Design Research nav entry)
  - `website/docs/blog/posts/custom-pcb-research.md` (created — blog post on PicoTop case study, Dilder board spec, KiCad learning path)
  - `website/docs/blog/posts/hardware-arrives.md` (created — blog post on joystick module and LiPo battery arrival and wiring)
  - `website/docs/blog/posts/engagement-plan.md` (created — blog post on user engagement plan: stats, sensors, evolution, treasure hunts, step targets)
  - `website/docs/blog/posts/peer-discovery.md` (created — blog post on BLE peer discovery, mating system, 17-bit genome, offspring lifecycle)
  - `PromptProgression.md` (modified — added Prompt #137)
  - `website/docs/prompts/index.md` (modified — added Prompt #137)
  - All changes committed and pushed

---

## Prompt #138
- **Date/Time:** 2026-04-14
- **Prompt:** "Let's add a backstory to the home page and docs. I have this picture of a plush octopus that my wife Emma bought on a day out last week that started the chain of events. We were shopping at the local TEDi (dollar store) and found him in the bin all happy, big, and soft. We began to anthropomorphize him on the walk home and slowly a personality was developing. On a whim we came up with the name Jamal. The question ultimately asked itself — when realizing how we gave life to this soft lil octopus, what if we could create a somewhat living, responsive, and sassy version of this squid? What would it take and how could we go about it? Take this backstory, clean it up, expound a little, convert the HEIC picture to JPEG, and add it to the blog home page along with the story. Update the docs and README as well. Add spice and flesh out the lore."
- **Input Tokens (est):** ~200
- **Output Tokens (est):** ~12,000
- **Commit:** `55189fd` — Update Prompts #142 with joystick firmware, build errors, and wiring fix
- **Files Created/Modified:**
  - `assets/pictures/Jamal.heic` (deleted — replaced with JPEG)
  - `website/docs/assets/images/jamal-the-original.jpg` (created — converted from HEIC, quality 90)
  - `website/docs/index.md` (modified — added "The Origin Story — How Jamal Was Found" section with photo at top of page, updated footer tagline)
  - `website/docs/blog/index.md` (modified — added "Where It All Began" section with photo and condensed backstory)
  - `website/docs/docs/index.md` (modified — added "The Namesake" section explaining Jamal as spiritual mascot)
  - `README.md` (modified — added "How It Started — Meet Jamal" section with photo, updated footer tagline)
  - `website/docs/about/index.md` (modified — added "The Origin Story" section with full lore, updated rompasaurus tagline)
  - `PromptProgression.md` (modified — added Prompt #138)
  - `website/docs/prompts/index.md` (modified — added Prompt #138)
  - All changes committed and pushed as `d8ff202`

---

## Prompt #139
- **Date/Time:** 2026-04-14
- **Prompt:** "The origin story formatting is a bit weird with the image — don't split the text in half, just make it all one block. Highlight the quote like you did, just place it on its own line and give the picture its own line without text wrapped around it."
- **Input Tokens (est):** ~50
- **Output Tokens (est):** ~1,500
- **Commit:** `55189fd` — Update Prompts #142 with joystick firmware, build errors, and wiring fix
- **Files Created/Modified:**
  - `website/docs/index.md` (modified — removed grid div wrapper from origin story so image and text flow as single column instead of side-by-side)
  - `PromptProgression.md` (modified — added Prompt #139)
  - `website/docs/prompts/index.md` (modified — added Prompt #139)
  - All changes committed and pushed as `edb669d`

---

## Prompt #140
- **Date/Time:** 2026-04-14
- **Prompt:** "OK I have the DollaTek 5-way joystick, the GY-NEO6MV2 NEO-6M GPS module, speakers, and HC-SR04. I want to set this up on a breadboard with the Waveshare 2.13 V3 display. Give me a proper wiring diagram for me to set this up properly to the Pico WH board. Add this to a hardware doc in the root of this project as an MD file."
- **Input Tokens (est):** ~100
- **Output Tokens (est):** ~20,000
- **Commit:** `84e3ad9` — Clean up spelling and grammar in PromptProgression.md
- **Files Created/Modified:**
  - `docs/breadboard-wiring-guide.md` (created — full breadboard wiring guide: complete pin assignment table for all 5 peripherals on 16 GPIO; master ASCII wiring diagram; annotated Pico WH pin map; component-by-component wiring for e-Paper SPI1, joystick GPIO with pull-ups, GPS UART0 with TX/RX crossover, HC-SR04 with 5V→3.3V voltage divider circuit, and speaker with PWM and NPN transistor amplifier option; breadboard zone layout for full-size board; power budget analysis showing ~130mA total on 300mA 3V3 rail; voltage level warnings; test code for GPS NMEA reading, ultrasonic distance measurement, speaker tone generation, and all-peripherals diagnostic; troubleshooting table)
  - `PromptProgression.md` (modified — added Prompt #140)
  - `website/docs/prompts/index.md` (modified — added Prompt #140)
  - All changes committed and pushed as `69ad9a9`

---

## Prompt #141
- **Date/Time:** 2026-04-14
- **Prompt:** "The Waveshare I have has a 40-pin header on the back — update the wiring to reflect that and check the online docs to confirm this. [Follow-up: double-check the physical pin mapping for the Waveshare rev 3a with the Pico headers, something doesn't seem right. Follow-up: I don't have VCC on the Waveshare, I have a VSYS though. Follow-up: yes update the README and materials list as well, and update the prompts file with this troubleshooting — all the chats for this project not yet added today.]"
- **Input Tokens (est):** ~300
- **Output Tokens (est):** ~25,000
- **Commit:** `55189fd` — Update Prompts #142 with joystick firmware, build errors, and wiring fix
- **Files Created/Modified:**
  - `docs/breadboard-wiring-guide.md` (modified — corrected display model from "Waveshare 2.13" e-Paper HAT V3" to "Waveshare Pico-ePaper-2.13"; replaced VCC/3V3(OUT)/pin 36 power with VSYS/pin 39 throughout; replaced RPi HAT 40-pin header section with Pico-native 40-pin direct-plug documentation; updated pin assignment table, master wiring diagram, annotated pin map, power budget, voltage level table, wire shopping list, and breadboard layout notes)
  - `website/docs/docs/hardware/wiring-pinout.md` (modified — replaced RPi HAT 40-pin header section with Pico-native module documentation; corrected all VCC/pin 36 references to VSYS/pin 39; updated visual pin map, text wiring diagram, GPIO pin budget, SPI config note, battery tip, and troubleshooting)
  - `website/docs/docs/hardware/materials-list.md` (modified — corrected product name, specs table, and jumper wire notes)
  - `README.md` (modified — corrected display product name and link)
  - `website/docs/blog/posts/phase-1-hardware.md` (modified — corrected product name and jumper wire note)
  - `website/docs/docs/tools/setup-cli.md` (modified — corrected product name and HAT plug note)
  - `website/docs/docs/setup/first-time-setup.md` (modified — corrected product name)
  - `docs/setup-guide.md` (modified — corrected product name)
  - `docs/hardware-research.md` (modified — corrected product name and connection notes)
  - `PromptProgression.md` (modified — added Prompt #141)
  - `website/docs/prompts/index.md` (modified — added Prompt #141)
  - All changes committed and pushed as `98bbf74`

---

## Prompt #142
- **Date/Time:** 2026-04-14
- **Prompt:** "OK I have the joystick wired in — let's add an interactive program that builds on the mood selector and wires the left and right actions to the change of moods selector at the bottom. Then we also want to print on the screen to the right of the mood display the input that was pressed last and update each time an input is received. Add this program to the interactive list in the DevTool."
- **Input Tokens (est):** ~100
- **Output Tokens (est):** ~30,000
- **Commit:** `55189fd` — Update Prompts #142 with joystick firmware, build errors, and wiring fix
- **Files Created/Modified:**
  - `dev-setup/joystick-mood-selector/main.c` (created — 1400-line C firmware: builds on mood-selector with 5-way GPIO joystick input; LEFT/RIGHT cycle moods, UP = random mood, DOWN = new quote, CENTER = reset to SASSY; last input indicator drawn on right side of status bar; 200ms debounce; serial input still works as fallback)
  - `dev-setup/joystick-mood-selector/CMakeLists.txt` (created — build config with display variant support V2/V3/V3a/V4)
  - `dev-setup/docker-compose.yml` (modified — added `build-joystick-mood-selector` service)
  - `DevTool/devtool.py` (modified — registered joystick_mood_selector in PROGRAMS dict, PROGRAM_TREE under Interactive, _OCTOPUS_CONFIGS with all 823 quotes, and _FIRMWARE_DIRS mapping)
  - `.gitignore` (modified — added build/, lib/, pico_sdk_import.cmake entries for joystick-mood-selector)
  - `PromptProgression.md` (modified — added Prompt #142)
  - `website/docs/prompts/index.md` (modified — added Prompt #142)
- **Build errors encountered:**
  - Docker compose: `no such service: build-joystick-mood-selector` — fixed by adding the service entry to `dev-setup/docker-compose.yml`
  - Build artifacts (489 files including `build/` directory) accidentally committed — fixed by adding `.gitignore` entries and `git rm --cached`
- **Hardware troubleshooting:**
  - CENTER button not registering — traced to wiring error: joystick CENTER wire was in GND (pin 8) instead of GP6 (pin 9). Adjacent pins on breadboard. Fixed by moving wire to correct pin. Code was correct.
- **Commits:** `9e8e49c` (firmware + DevTool), `5d70554` (gitignore fix + build artifact cleanup)
  - All changes committed and pushed as `55189fd`

---

## Prompt #143
- **Date/Time:** 2026-04-14
- **Prompt:** "Update the documentation and website and blog with the joystick session. I have added some HEIC images — convert them to JPEG, annotate what's in them, update the MD docs where relevant. Update the blog and docs on the site as well. There is a battery pic in these files — get the battery model and begin to plan out how to wire that up. Then update the prompts and commit."
- **Input Tokens (est):** ~150
- **Output Tokens (est):** ~20,000
- **Commit:** `83d517c` — Add joystick build session photos, blog post, battery planning, Prompt #143
- **Files Created/Modified:**
  - 16 HEIC images converted to JPEG in `website/docs/assets/images/hardware/build-session/` with descriptive names: sassy-octopus-display-front, pico-w-epaper-stacked-rear, jamal-plush-armchair, dollatek-joystick-closeup, pico-w-jumper-wires-display-side/angle, pico-w-gpio-wiring-top/closeup, test-bench-full-with-joystick, joystick-selector-tired-mood/hungry-left/hungry-npcs, lipo-battery-inncraft-1000mah, workspace-full-breadboard-setup, joystick-on-breadboard
  - `assets/*.heic` (16 files deleted — replaced with JPEGs above)
  - `website/docs/blog/posts/joystick-first-input.md` (created — blog post: joystick build session with 6 annotated photos, wiring mixup story, battery planning, next steps)
  - `website/docs/docs/hardware/battery-wiring.md` (modified — added battery photo to specifications section)
  - `website/docs/docs/hardware/joystick-wiring.md` (modified — added joystick close-up photo to overview section)
  - `website/docs/docs/hardware/wiring-pinout.md` (modified — added GPIO wiring photo at top of page)
  - `website/docs/index.md` (modified — updated Phase 2 status with joystick milestone, added live hardware photo)
  - `README.md` (modified — marked serial input and GPIO joystick as done, added battery power as next step)
  - `PromptProgression.md` (modified — added Prompt #143)
  - `website/docs/prompts/index.md` (modified — added Prompt #143)
  - Battery identified: InnCraft Energy INS503450, 1000mAh, 3.7V, Molex 51021-0200 — matches existing battery wiring guide exactly. Wiring plan: direct to VSYS (pin 39) for breadboard testing, TP4056 for permanent build.
  - All changes committed and pushed

---

## Prompt #144
- **Date/Time:** 2026-04-14 to 2026-04-15
- **Prompt:** "Create a setup script for KiCad to pull in the JLCPCB tools so that we can begin to model out the schematics and then board design... we basically need to copy out the Pico WH schematic and add a battery connection and charging circuit and a joystick input along with an accelerometer and GPS module... begin with a planning document, pull in the tools, make the schematic, then get the board modeled." (Multi-session — evolved through ~30 follow-up prompts covering PCB design, component selection, autorouting, MCU change from RP2040 to ESP32-S3, display connector research.)
- **Input Tokens (est):** ~5,000 (across ~30 prompts)
- **Output Tokens (est):** ~200,000
- **Commit:** `af57530`
- **Key Decisions Made:**
  - Switched MCU from RP2040 to **ESP32-S3-WROOM-1-N16R8** (WiFi+BLE, 16MB flash, 8MB PSRAM built in)
  - Eliminated 7 components (external flash, crystal, caps, USB resistors) by using module
  - Switched from 2-layer to **4-layer PCB** (required for routing under ESP32 ground pad)
  - Display connector: 8-pin 2.54mm header (connects to Waveshare HAT via ribbon cable, NOT raw 24-pin FPC)
  - Board target: ~30x75mm, 4-layer
  - Installed FreeRouting autorouter (downloaded portable Linux binary)
  - JLCPCB selected for fabrication (ships to Germany)
- **Files Created/Modified:**
  - `docs/esp32-s3-pcb-research.md` (created — ESP32-S3 module research: specs, antenna keep-out, ground pad routing, reference designs, 4-layer stackup, component placement strategy)
  - `hardware-design/pcb-design-plan.md` (major rewrite — RP2040 to ESP32-S3, updated BOM, GPIO pinout, layout strategy, fabrication steps)
  - `hardware-design/setup-kicad-jlcpcb.py` (created — automated KiCad + JLCPCB plugin setup)
  - `hardware-design/Board Design kicad/dilder.kicad_pro` (created — KiCad project file)
  - `hardware-design/Board Design kicad/dilder.kicad_sch` (created — schematic with all components + net labels)
  - `hardware-design/Board Design kicad/dilder.kicad_pcb` (created — 4-layer PCB, 27 components placed via pcbnew API)
  - `hardware-design/Board Design kicad/build_esp32s3.py` (created — builds PCB with real footprints, multiple iterations v1-v6)
  - `hardware-design/Board Design kicad/generate_schematic.py` (created — generates wired KiCad schematic)
  - `website/docs/docs/reference/esp32-s3-wroom1.md` (created — ESP32-S3 reference page)
  - `website/docs/docs/design/custom-pcb-design-research.md` (modified — added ESP32-S3 transition notice)
  - `website/mkdocs.yml` (modified — added ESP32-S3 reference nav entry)
  - `PromptProgression.md` (modified — added Prompt #144)

---

## Prompt #145
- **Date/Time:** 2026-04-15
- **Prompt:** "Use the research to map out components on the board. Processor at top with antenna off the edge, USB-C at bottom, joystick centered above USB-C. Optimize placement. Then update docs, website, blog, commit, and update prompts."
- **Input Tokens (est):** ~200
- **Output Tokens (est):** ~15,000
- **Commit:** `9b4f3e8`
- **Files Created/Modified:**
  - `website/docs/blog/posts/esp32-s3-pcb-design.md` (created — blog post: RP2040 to ESP32-S3 transition, PCB design journey, antenna keep-out, display connector decision, FreeRouting lessons, reference designs, current board status)
  - `README.md` (modified — added ESP32-S3 custom PCB as in-progress milestone, noted MCU transition)
  - `website/docs/index.md` (modified — added ESP32-S3 PCB design status to Current Phase section)
  - `website/docs/prompts/index.md` (modified — added Prompt #145)
  - `PromptProgression.md` (modified — added Prompt #145)
  - `hardware-design/Board Design kicad/build_esp32s3.py` (updated — v7 placement optimization based on pin exit sides)
  - `hardware-design/Board Design kicad/dilder.kicad_pcb` (regenerated — 45x80mm, 27 components, optimized placement)

---

## Prompt #146
- **Date/Time:** 2026-04-15
- **Prompt:** "Let's make a hardware assembly and board prototyping MD document and compile all the pricing research and note all the sources used and data compiled. Give me some rough estimates through various providers. Also find if there are any open board schematics and board Gerber files that can be used that match this project's requirements, and compose a document with this as well."
- **Input Tokens (est):** ~100
- **Output Tokens (est):** ~20,000
- **Commit:** `e11a78d` — Add PCB assembly and prototyping research document, Prompt #146
- **Files Created/Modified:**
  - `docs/pcb-assembly-and-prototyping.md` (created — comprehensive 10-section document: provider comparison table for 5 fab houses; detailed pricing breakdowns for JLCPCB, PCBWay, OSH Park, Aisler, Seeed Fusion; per-joint assembly costs, setup fees, component handling fees; cost estimates for Dilder board across all providers; break-even analysis for Aisler vs China including 19% DE VAT; 6 open-source reference designs analyzed — Ducky Board, OpenTama, TamaFi V2, PocketMage PDA, AeonLabs template, PicoTop; recommended manufacturing path with ordering checklist; 25+ cited sources)
  - `website/docs/docs/design/pcb-assembly-and-prototyping.md` (created — website copy)
  - `website/mkdocs.yml` (modified — added PCB Assembly & Prototyping nav entry under Design)
  - `website/docs/docs/index.md` (modified — added Design section with links to engagement plan, PCB research, and assembly/prototyping docs)
  - `PromptProgression.md` (modified — added Prompt #146)
  - `website/docs/prompts/index.md` (modified — added Prompt #146)
  - All changes committed and pushed as `e11a78d`

---

## Prompt #147
- **Date/Time:** 2026-04-15
- **Prompt:** "On the PCB design and assembly document, can you pull images for all the components suggested and anything with a price next to it — I want to actually see the component image somewhere."
- **Input Tokens (est):** ~50
- **Output Tokens (est):** ~5,000
- **Commit:** `3f46a7b` — Add open-source board design research page with images and walkthroughs, Prompts #147-148
- **Files Created/Modified:**
  - 12 component product photos downloaded from LCSC into `website/docs/assets/images/components/` (ESP32-S3-WROOM-1, TP4056, DW01A, FS8205A, AMS1117-3.3, SS34 diode, USB-C connector, JST PH battery connector, Alps joystick, MPU-6050, red/green LEDs)
  - `docs/pcb-assembly-and-prototyping.md` (modified — added Visual BOM gallery section with component images, LCSC links, and pricing)
  - `website/docs/docs/design/pcb-assembly-and-prototyping.md` (synced)
  - All changes committed and pushed as `d12d85f`

---

## Prompt #148
- **Date/Time:** 2026-04-15
- **Prompt:** "Is there a KiCad open board design for the Pico and ESP32 dev boards? If so, pull them into the hardware-design folder in individual folders with MD details. Then make another section — do open board design research and provide extensive documentation and pictures and walk through each design on the site."
- **Input Tokens (est):** ~100
- **Output Tokens (est):** ~25,000
- **Commit:** `3f46a7b` — Add open-source board design research page with images and walkthroughs, Prompts #147-148
- **Files Created/Modified:**
  - `hardware-design/reference-boards/` (created — 7 open-source KiCad projects: rp2040-pico-usbc, rp2040-minimal-jlcpcb, rp2040-designguide, esp32s3-basic-devboard, esp32s3-ducky-epaper, espressif-kicad-libs, opentama-virtual-pet)
  - `hardware-design/reference-boards/README.md` (created — master index documenting all 7 designs)
  - 7 reference board images in `website/docs/assets/images/reference-boards/` (3D renders, PCB layouts, schematic screenshots, assembled board photos)
  - `website/docs/docs/design/open-board-designs.md` (created — comprehensive walkthrough page with images, per-design analysis, component overlap tables, comparison matrix)
  - `website/mkdocs.yml` (modified — added nav entry)
  - `website/docs/docs/index.md` (modified — added link in Design section)
  - `PromptProgression.md` (modified — added Prompts #147-148)
  - `website/docs/prompts/index.md` (modified — added Prompts #147-148)
  - All changes committed and pushed as `3f46a7b`

---

## Prompt #149
- **Date/Time:** 2026-04-15
- **Prompt:** "I need to update the schematics, get rid of the RP2040, use the ESP32, add a parts list, and wire up all the components on this if you can."
- **Input Tokens (est):** ~50
- **Output Tokens (est):** ~25,000
- **Commit:** `04cecb3` — Replace RP2040 with ESP32-S3-WROOM-1-N16R8 in schematic, add BOM, Prompt #149
- **Files Created/Modified:**
  - `hardware-design/Board Design kicad/generate_schematic.py` (rewritten — replaced RP2040 with ESP32-S3-WROOM-1-N16R8 symbol and wiring; removed W25Q16JV flash, 12MHz crystal + load caps, 27R USB resistors, ATGM336H GPS; added ESP32-S3 lib symbol with 17 pins; rewired all nets: SPI e-paper GPIO9/10/3/11/46/12, I2C IMU GPIO16/17, USB-OTG GPIO19/20 direct to USB-C, joystick GPIO4-8, EN pull-up; component count 33→20; added full BOM table in docstring)
  - `hardware-design/Board Design kicad/dilder.kicad_sch` (regenerated — rev 0.3, ESP32-S3 schematic with all nets wired, validated with kicad-cli)
  - `hardware-design/BOM.md` (created — full bill of materials with LCSC part numbers, costs per component, GPIO pin assignment table, cost summary, changelog from v0.2)
  - `hardware-design/Measurements.md` (updated — replaced Pico board with ESP32-S3-WROOM-1 module dimensions, added PCB, joystick, USB-C, JST, MPU-6050 measurements)

---

## Prompt #150
- **Date/Time:** 2026-04-15
- **Prompt:** "OK, pull in some example schematics and KiCad files into a new example folder in hardware design that use the ESP32 and somewhat similar functions. Find as many related examples as possible, put them in their own folder, and create an MD file for each to describe the use of each design and origin and backstory and details and links and TOC."
- **Input Tokens (est):** ~80
- **Output Tokens (est):** ~15,000
- **Commit:** `2e5e0a8` — Add 11 ESP32 KiCad reference designs with documentation, Prompt #150
- **Files Created/Modified:**
  - `hardware-design/examples/` (created — 11 open-source ESP32/ESP32-S3 KiCad projects cloned as reference designs)
  - `hardware-design/examples/01-pocketmage-pda/` (ESP32-S3 e-ink PDA, ~1800 stars, Apache-2.0)
  - `hardware-design/examples/02-lilka-console/` (ESP32-S3 DIY gaming console, Ukraine, GPL-2.0)
  - `hardware-design/examples/03-ducky-board-epaper/` (ESP32-S3 + 1.52" e-paper + Li-Ion, GPL-3.0)
  - `hardware-design/examples/04-olimex-s3-devkit-lipo/` (OLIMEX ESP32-S3 + LiPo, OSHW, GPL-3.0)
  - `hardware-design/examples/05-olimex-devkit-lipo/` (OLIMEX ESP32 + LiPo, 4 hardware revisions, Apache-2.0)
  - `hardware-design/examples/06-unexpected-maker-s3/` (Unexpected Maker ESP32-S3 carrier boards)
  - `hardware-design/examples/07-whirlingbits-s3-platform/` (ESP32-S3 + SD + e-paper schematic, MIT)
  - `hardware-design/examples/08-esp-rust-board/` (Espressif-affiliated Feather board, CERN-OHL-S-2.0)
  - `hardware-design/examples/09-bitwiseajeet-tp4056/` (ESP32-C3 + TP4056 exact charger match, MIT)
  - `hardware-design/examples/10-klp5e-sensor-board/` (educational ESP32-C3 + TP4056 + sensors)
  - `hardware-design/examples/11-aeonlabs-s3-template/` (minimal ESP32-S3 template, CC0)
  - Each folder has `ABOUT.md` with origin, backstory, feature comparison table, key takeaways, KiCad file listing, and links
  - `hardware-design/examples/INDEX.md` (created — master TOC with 3-tier relevance ranking, feature cross-reference table, usage guide)

---

## Prompt #151
- **Date/Time:** 2026-04-15
- **Prompt:** "The MPU-6050 accelerometer is a bit pricey — we really just want to track steps and aggressive motions. Price out GPS and brainstorm location detection. Ditch the GPS, go 3-axis LIS2DH12TR, put WiFi fingerprinting and BLE scanning on the software plan. Create a document, update hardware planning, pics, and pricing."
- **Input Tokens (est):** ~200
- **Output Tokens (est):** ~30,000
- **Commit:** `1a1de2a` — Swap MPU-6050 for LIS2DH12TR, add motion/location plan, parts sheets, Prompts #151-152
- **Key Decision:** MPU-6050 ($6.88, 6-axis IMU) → LIS2DH12TR ($0.46, 3-axis accel + HW pedometer). GPS dropped — WiFi fingerprinting + BLE scanning (free, built into ESP32-S3) handle location. BOM total: $11.14 → $4.72/board.
- **Files Created/Modified:**
  - `docs/motion-location-detection.md` (created — 10-section plan: LIS2DH12 specs, HW pedometer, tap/shake/freefall/orientation, WiFi fingerprinting algo, BLE scanning, sensor→pet behavior map, power budget, GPS comparison, implementation phases)
  - `website/docs/docs/design/motion-location-detection.md` (website copy)
  - `website/docs/assets/images/components/lis2dh12-accelerometer.jpg` (created — LCSC product photo)
  - `website/docs/assets/images/components/mpu-6050-imu.jpg` (deleted)
  - `docs/pcb-assembly-and-prototyping.md` (modified — sensor swap, updated all BOM/cost tables)
  - `website/docs/docs/design/pcb-assembly-and-prototyping.md` (synced)
  - `hardware-design/pcb-design-plan.md` (modified — LIS2DH12 replaces MPU-6050, GPS dropped)
  - `hardware-design/BOM.md` (modified — sensor swap, GPS removed, totals updated)
  - `website/mkdocs.yml` (added Motion & Location Detection nav)
  - `website/docs/docs/index.md` (added motion detection link)
  - `PromptProgression.md` (#151), `website/docs/prompts/index.md` (#151)

---

## Prompt #152
- **Date/Time:** 2026-04-15
- **Prompt:** "Make a parts-sheets folder in hardware with an MD file for each component and import official datasheets into a manufacturer-datasheets subfolder."
- **Input Tokens (est):** ~50
- **Output Tokens (est):** ~15,000
- **Commit:** `1a1de2a` — Swap MPU-6050 for LIS2DH12TR, add motion/location plan, parts sheets, Prompts #151-152
- **Files Created/Modified:**
  - `hardware-design/parts-sheets/README.md` (created — index of all 11 component part sheets)
  - 11 part sheet MD files: `esp32-s3-wroom1.md`, `lis2dh12.md`, `tp4056.md`, `dw01a.md`, `fs8205a.md`, `ams1117.md`, `ss34.md`, `skrhabe010.md`, `usb-c-connector.md`, `jst-ph-battery.md`, `led-red.md`, `led-green.md` (each with specs, pin connections, application notes, datasheet links)
  - `hardware-design/parts-sheets/manufacturer-datasheets/ESP32-S3-WROOM-1-datasheet.pdf` (1.3MB, official Espressif)
  - `PromptProgression.md` (#152), `website/docs/prompts/index.md` (#152)
  - All changes committed and pushed as `1a1de2a`

---

## Prompt #153
- **Date/Time:** 2026-04-15
- **Prompt:** "Continue on the parts sheets — ensure every needed part has a matching MD file and a manufacturer spec/datasheet in the datasheets folder. Each MD file needs to be robust and in-depth, well-researched — important background info, what it functions for, how it works, technologies behind it. The more advanced a part, the more in-depth you need to be, dumb it down and make TOCs for everyone and provide sources."
- **Input Tokens (est):** ~100
- **Output Tokens (est):** ~40,000
- **Commit:** `12829d6` — Rewrite all parts sheets with full TOCs, technology guides, and sources, Prompt #153
- **Files Created/Modified:**
  - Rewrote all 12 existing part sheets from scratch with full Table of Contents, plain-English "What Is This Part?" intros, deep technology explainers (MEMS accelerometer physics, MOSFET field-effect operation, CC/CV lithium charging theory, Schottky metal-semiconductor junctions, LDO bandgap reference internals, MLCC multi-layer construction, LED photon emission, I2C/SPI protocol tutorials, USB-C CC negotiation), manufacturer/inventor history, and cited sources (Wikipedia, datasheets, application notes, tutorials)
  - `hardware-design/parts-sheets/esp32-s3-wroom1.md` (62→230 lines — CPU architecture, WiFi OFDM, BLE, PSRAM vs SRAM, PCB antenna MIFA design, USB-OTG, module vs bare chip, Espressif history)
  - `hardware-design/parts-sheets/tp4056.md` (61→230 lines — three charging phases, CC/CV with ASCII graph, internal block diagram, thermal regulation math, common mistakes)
  - `hardware-design/parts-sheets/lis2dh12.md` (88→230 lines — MEMS proof mass, differential capacitive sensing, sigma-delta ADC, all HW features table, operating modes, I2C tutorial, register map, ST/MEMS history)
  - `hardware-design/parts-sheets/dw01a.md` (52→170 lines — lithium chemistry dangers, copper dissolution/dendrites, thermal runaway, hysteresis thresholds, monitoring circuit internals)
  - `hardware-design/parts-sheets/fs8205a.md` (53→170 lines — MOSFET physics, N-channel enhancement mode, Rds(on) power math, back-to-back body diode problem with diagrams)
  - `hardware-design/parts-sheets/ams1117.md` (48→190 lines — linear vs switching regulators, bandgap voltage reference, dropout at different loads, thermal math, LDO vs buck tradeoff table, 1117 family history)
  - `hardware-design/parts-sheets/ss34.md` (34→170 lines — PN junction physics, forward/reverse bias, Schottky metal-semiconductor junction, Walter Schottky bio)
  - `hardware-design/parts-sheets/usb-c-connector.md` (35→170 lines — reversible dual-row design, CC orientation detection, power negotiation resistor values, 16 vs 24 pin, NRZI signaling, USB timeline 1996-2024)
  - `hardware-design/parts-sheets/skrhabe010.md` (51→160 lines — rocker mechanism, tactile dome contacts, silver plating, debouncing, Alps Alpine history)
  - `hardware-design/parts-sheets/jst-ph-battery.md` (27→100 lines — JST connector family comparison table, polarity warning, JST company history)
  - `hardware-design/parts-sheets/led-red.md` (31→110 lines — LED physics, bandgap-to-wavelength table, current limiting math)
  - `hardware-design/parts-sheets/led-green.md` (31→80 lines — InGaN, Shuji Nakamura Nobel Prize)
  - `hardware-design/parts-sheets/jst-sh-epaper.md` (created — JST SH series, SPI interface tutorial, e-paper signal descriptions)
  - `hardware-design/parts-sheets/resistors-0402.md` (created — Ohm's Law, thick/thin film manufacturing, each resistor's specific function, tolerance grades)
  - `hardware-design/parts-sheets/capacitors-0402.md` (created — capacitor physics, MLCC construction, dielectric types, decoupling theory, 100nF+10uF combo)
  - `hardware-design/parts-sheets/manufacturer-datasheets/DOWNLOAD-GUIDE.md` (created — browser-clickable links for all datasheet PDFs)
  - `hardware-design/parts-sheets/README.md` (rewritten — comprehensive index with descriptions of each sheet's coverage, component count summary)
  - `website/docs/docs/hardware/wiring-pinout.md` (modified — added ESP32-S3 custom PCB GPIO table, power chain diagram, block diagram)
  - `website/docs/docs/hardware/materials-list.md` (modified — added ESP32-S3 PCB BOM section at top)

---

## Prompt #154
- **Date/Time:** 2026-04-15
- **Prompt:** "Create a breadboard prototype guide with EU/US sourcing and alpha board plans."
- **Input Tokens (est):** ~80
- **Output Tokens (est):** ~20,000
- **Commit:** `a5aec52` — Add breadboard prototype guide with EU/US sourcing and alpha board plans, Prompt #154
- **Files Created/Modified:**
  - `hardware-design/breadboard-prototype-guide.md` (created — 7 ESP32-S3 dev board options with comparison table, GPIO wiring map matching custom PCB, breadboard assembly steps, shopping lists optimized for German/EU retailers: Botland, Eckstein, BerryBase, Olimex, EXP-Tech, Amazon)
  - Three compact alpha board approaches: Feather stack, protoboard solder build, 3D-printed bracket with Olimex DevKit-Lipo
  - `.gitignore` (updated for `.history/` dirs)
  - `PromptProgression.md` (#154), `website/docs/prompts/index.md` (#154)

---

## Prompt #155
- **Date/Time:** 2026-04-15
- **Prompt:** "Continue where you left off — look at the staged changes and the planning and go from there."
- **Input Tokens (est):** ~150
- **Output Tokens (est):** ~60,000
- **Commit:** `dbc82c1` — Add v0.4 PCB routing, board design doc, update prompts, Prompt #155
- **Key Work:** PCB routing (Phase 4). Wrote `route_v04.py` — a 4-layer router for the v0.4 board using B.Cu vertical channels for long signals, staggered B.Cu L-routes for ePaper/joystick (crossing-free), custom routes for USB/EN/BOOT/battery protection, and F.Cu for power chain and local nets. Added In1.Cu GND plane and In2.Cu 3V3 plane. Iteratively fixed channel collisions (EN vs I2C_SDA), VBUS path crossings, and 3V3 via placement. Created comprehensive board design document.
- **Files Created/Modified:**
  - `hardware-design/Board Design kicad/route_v04.py` (created — v0.4 router, ~400 lines)
  - `hardware-design/Board Design kicad/build_esp32s3.py` (modified — regenerated placement)
  - `hardware-design/Board Design kicad/dilder.kicad_pcb` (routed board)
  - `hardware-design/board-design-v04.md` (created — complete board design document with BOM, zones, GPIO map, routing strategy, DRC status, fab workflow)
  - KiCad project files updated (`.kicad_prl`, `.kicad_pro`, `.kicad_sch`)
  - `website/docs/prompts/index.md` (updated with Prompts #154-155)

---

## Prompt #156
- **Date/Time:** 2026-04-15
- **Prompt:** "Commit the changes and push and update prompts, fix spelling."
- **Input Tokens (est):** ~60
- **Output Tokens (est):** ~5,000
- **Commit:** `dd3f5b3` — Add website blog posts, docs pages, icon, fix link, update prompts, Prompt #156
- **Files Created/Modified:**
  - `website/docs/blog/posts/breadboard-prototype-guide.md` (created — blog post: breadboard prototype build guide with parts list, GPIO wiring, regional sourcing, alpha board plans)
  - `website/docs/blog/posts/motion-location-detection.md` (created — blog post: MPU-6050 to LIS2DH12TR swap, WiFi fingerprinting, BLE peer detection)
  - `website/docs/blog/posts/pcb-routing-complete.md` (created — blog post: v0.4 PCB routing milestone, layer stack, zone layout, BOM cost)
  - `website/docs/docs/design/board-design.md` (created — website doc: board design v0.4 overview with BOM, zones, GPIO, layer stack, fab workflow)
  - `website/docs/docs/design/breadboard-prototype.md` (created — website doc: breadboard prototype guide with dev board comparison, wiring map, alpha board options)
  - `website/docs/assets/images/dilder-icon.svg` (created — octopus SVG icon for site logo/favicon)
  - `website/mkdocs.yml` (modified — added custom logo/favicon, board design and breadboard prototype to nav)
  - Fixed broken link in breadboard blog post (pointed to `custom-pcb-design-research.md` instead of `breadboard-prototype.md`)
  - `PromptProgression.md` (updated — added Prompts #154, #155, #156)
  - `website/docs/prompts/index.md` (updated — added Prompt #156)

---

## Prompt #157
- **Date/Time:** 2026-04-15
- **Prompt:** "Add AHT20 temp/humidity and BH1750FVI light sensors to board design. Both I2C, sharing bus with LIS2DH12. New parts sheets, updated BOM, docs, and KiCad guide. Board now 30 components, ~$5.20/unit."
- **Input Tokens (est):** ~500
- **Output Tokens (est):** ~5,000
- **Commit:** `9b4508d` — Add gameplay architecture planning docs, BME280→AHT20 update, blog post, Prompt #160
- **Files Created/Modified:**
  - `Gamplay Planning/04-sensor-interfaces.md` (verified — already updated with AHT20 and BH1750 definitions, I2C address map: LIS2DH12=0x18, BH1750=0x23, AHT20=0x38)
  - `README.md` (modified — updated component count from 27 to 30, added sensor list: LIS2DH12TR, AHT20, BH1750FVI-TR on shared I2C bus)
  - `PromptProgression.md` (updated — added Prompt #157)

---

## Prompt #158
- **Date/Time:** 2026-04-15
- **Prompt:** "I have created a gameplay planning folder. We are going to establish the pseudocode and structure of the gameplay loop for this game in several well-structured MD files. Let's take the Dilder User Engagement Plan and begin to outline a program structure and interfaces to orient this gameplay loop and user interface."
- **Input Tokens (est):** ~80
- **Output Tokens (est):** ~50,000
- **Commit:** `9b4508d` — Add gameplay architecture planning docs, BME280→AHT20 update, blog post, Prompt #160
- **Files Created/Modified:**
  - `Gamplay Planning/00-architecture-overview.md` (created — module map, data flow diagrams, RAM/flash budgets, file organization)
  - `Gamplay Planning/01-core-game-loop.md` (created — main loop pseudocode, tick scheduling, game states FSM, sleep/wake, event bus)
  - `Gamplay Planning/02-stat-system.md` (created — stat structs, fractional decay, care actions, thresholds, modifier stack)
  - `Gamplay Planning/03-emotion-engine.md` (created — 16 trigger functions, weight resolution, blending, forced overrides)
  - `Gamplay Planning/04-sensor-interfaces.md` (created — unified sensor context, 7 driver interfaces, polling rates, duty cycles)
  - `Gamplay Planning/05-input-menu-ui.md` (created — button debounce, menu FSM, screen composition, rendering pipeline)
  - `Gamplay Planning/06-life-stages-evolution.md` (created — stage FSM, evolution scoring for 6 adult forms, misbehavior, rebirth)
  - `Gamplay Planning/07-progression-unlocks.md` (created — XP sources, bond levels, 20+ achievements, decor inventory)
  - `Gamplay Planning/08-dialogue-system.md` (created — quote DB schema, selection algorithm, context triggers, intelligence gating)
  - `Gamplay Planning/09-persistence-storage.md` (created — 176-byte save struct, LittleFS flash layout, CRC integrity, location DB)
  - `Gamplay Planning/10-activity-tracker.md` (created — step tracking, daily/weekly/monthly targets, streaks, WiFi geolocation, treasure hunts)

---

## Prompt #159
- **Date/Time:** 2026-04-15
- **Prompt:** "Bear in mind we are going to be changing microcontrollers — tell me how that will affect the C implementation when the time comes in a document."
- **Input Tokens (est):** ~30
- **Output Tokens (est):** ~12,000
- **Commit:** `9b4508d` — Add gameplay architecture planning docs, BME280→AHT20 update, blog post, Prompt #160
- **Files Created/Modified:**
  - `Gamplay Planning/11-mcu-migration-impact.md` (created — RP2040 → ESP32-S3 migration guide: SDK translation, per-module impact, GPIO remapping, FreeRTOS implications, portability strategy)

---

## Prompt #160
- **Date/Time:** 2026-04-15
- **Prompt:** "OK update all the documentation with this and commit and update the prompts and website, add a blog."
- **Input Tokens (est):** ~30
- **Output Tokens (est):** ~15,000
- **Commit:** `9b4508d` — Add gameplay architecture planning docs, BME280→AHT20 update, blog post, Prompt #160
- **Files Created/Modified:**
  - `Gamplay Planning/04-sensor-interfaces.md` (modified — BME280 → AHT20: comment headers, I2C address 0x76 → 0x38, removed pressure field)
  - `Gamplay Planning/00-architecture-overview.md` (modified — BME280 → AHT20 in driver file listing)
  - `docs/user-engagement-plan.md` (modified — BME280 → AHT20: sensor table, cost tiers, I2C bus map, power budget, phase 3B, references)
  - `docs/custom-pcb-design-research.md` (modified — BME280 → AHT20 across all references, I2C address updated)
  - `website/docs/docs/design/user-engagement-plan.md` (modified — same BME280 → AHT20 updates as docs/ copy)
  - `website/docs/docs/design/custom-pcb-design-research.md` (modified — same BME280 → AHT20 updates as docs/ copy)
  - `website/docs/blog/posts/custom-pcb-research.md` (modified — BME280 → AHT20 in sensor list)
  - `website/docs/blog/posts/gameplay-architecture.md` (created — blog post: gameplay loop architecture, stat decay math, emotion resolution, evolution system, MCU migration, AHT20 update)
  - `PromptProgression.md` (updated — added Prompts #158, #159, #160)

---

## Prompt #161
- **Date/Time:** 2026-04-15
- **Prompt:** "In this same folder for gameplay planning I want you to create a user guide to show off the planned features as if everything has been implemented. Use the existing images of the game to compose this and make an in-depth guide on the game, the story behind it, how to play, and the mechanisms behind it — the environments, the options, and a huge TOC to go along with it. Outline how the stats system works and an achievement system for the player to try to uncover every feature of the game. Let's also separately make an MD document to implement a feature system and menu to view them as well."
- **Input Tokens (est):** ~120
- **Output Tokens (est):** ~40,000
- **Commit:** `a25f89c` — Add user guide, asset system, feature menus, KiCad sensor updates, blog posts, Prompt #162
- **Files Created/Modified:**
  - `Gamplay Planning/12-user-guide.md` (created — 1,207-line comprehensive player guide with 35-section TOC across 10 chapters: origin story, 16 emotions with images, stat system, care actions, sensor interactions, step tracking, life stages, 6 evolution forms, bond levels, dialogue, decor, treasure hunts, 64 achievements across 7 categories, environments, controls, tips)
  - `Gamplay Planning/13-feature-menus-achievements.md` (created — 963-line implementation spec: 64 achievement definitions as C structs, achievement viewer UI, stats viewer, activity summaries, decor browser, emotion gallery, evolution bestiary, memorial viewer, toast notification system, settings menu, full hierarchical menu map with unlock gates)

---

## Prompt #162
- **Date/Time:** 2026-04-15
- **Prompt:** "OK we've implemented a ton of things in several sessions today. Go through all the changes, update the docs if needed, and commit them, then update the prompts and the webpage as well — add a few blogs and show off the asset images. Get that user guide posted up on the site in the docs and website too."
- **Input Tokens (est):** ~80
- **Output Tokens (est):** ~15,000
- **Commit:** `a25f89c` — Add user guide, asset system, feature menus, KiCad sensor updates, blog posts, Prompt #162
- **Files Created/Modified:**
  - `website/docs/assets/images/octopus/` (created — copied 24 asset images: 11 grid PNGs + 16 emotion preview PNGs from assets/ for website use)
  - `website/docs/blog/posts/asset-rendering-system.md` (created — blog post: 22 environments, 42 outfits, 29 props, aura particles with grid image showcases)
  - `website/docs/docs/design/user-guide.md` (created — website copy of user guide with fixed image paths)
  - `website/mkdocs.yml` (modified — added user guide to Design nav section)
  - `Gamplay Planning/12-user-guide.md` (from Prompt #161)
  - `Gamplay Planning/13-feature-menus-achievements.md` (from Prompt #161)
  - Hardware changes from earlier session: KiCad schematic/PCB updates (AHT20+BH1750 sensors added), BOM updates, board-design-v04 updates, wiring-pinout updates, materials-list updates, KiCad lib tables, ERC report
  - `PromptProgression.md` (updated — added Prompts #161, #162)

---

## Prompt #163
- **Date/Time:** 2026-04-15
- **Prompt:** "This board is not good at all. Things are drawn off the board, you don't have the microcontroller in there, not sure this is salvageable. Also the schematic is not wired up properly and you didn't pull actual schematics that already exist via addon."
- **Input Tokens (est):** ~60
- **Output Tokens (est):** ~80,000
- **Commit:** `7a0fab4` — Add prompt log #163-167, schematic generator script, clean up prompts
- **Files Created/Modified:**
  - `hardware-design/Board Design kicad/sym-lib-table` (created — Espressif symbol library registration)
  - `hardware-design/Board Design kicad/fp-lib-table` (created — Espressif footprint library registration)
  - `hardware-design/Board Design kicad/generate_schematic_v2.py` (created — schematic generator using real KiCad library symbols and footprints)
  - `hardware-design/Board Design kicad/dilder.kicad_sch` (regenerated — 27 components with correct pin mappings, real footprint references, net label wiring)
  - `hardware-design/Board Design kicad/dilder.kicad_pcb` (regenerated — 27 real footprints from KiCad standard libraries, 4-layer board with zone pours, 101 net assignments, 43 stitching vias)

---

## Prompt #164
- **Date/Time:** 2026-04-15
- **Prompt:** "This is bad. I need to do this manually obviously. Give me an MD user document instead and explain it to me as if this is my first time using CAD software. I need an extensive how-to document on how to design schematics, best practices, guide me through each component and how to draw it properly and how to account for the wiring of each. Then I will need an in-depth PCB walkthrough, as exhaustive as possible with a huge list of steps that I can follow one by one until completion. Expound on the important electronics principles behind it when necessary and provide further resources and learning material at the end, and definitions as well."
- **Input Tokens (est):** ~120
- **Output Tokens (est):** ~45,000
- **Commit:** `7a0fab4` — Add prompt log #163-167, schematic generator script, clean up prompts
- **Files Created/Modified:**
  - `website/docs/docs/design/kicad-schematic-pcb-guide.md` (created — 1,300-line beginner-to-gerber KiCad guide: 5 parts, 13 schematic subcircuits, 10 PCB layout sections, electronics principles reference, 40+ term glossary, learning resources)
  - `website/mkdocs.yml` (modified — added KiCad guide to Design nav)

---

## Prompt #165
- **Date/Time:** 2026-04-15
- **Prompt:** "Let's add a light and temp and humidity sensor to the list of hardware requirements. Find the best part or parts to do this as well. Ensure it will work with the controller we have planned to use, then add it to the docs and the planning and pull in the datasheet and create an MD doc for it following the existing parts sheets format."
- **Input Tokens (est):** ~70
- **Output Tokens (est):** ~60,000
- **Commit:** `7a0fab4` — Add prompt log #163-167, schematic generator script, clean up prompts
- **Files Created/Modified:**
  - `hardware-design/parts-sheets/aht20.md` (created — 436-line parts sheet: AHT20 temp/humidity sensor, capacitive sensing physics, comparison table, I2C bus sharing)
  - `hardware-design/parts-sheets/bh1750fvi.md` (created — 487-line parts sheet: BH1750FVI-TR ambient light sensor, photodiode theory, lux reference, operating modes)
  - `hardware-design/parts-sheets/manufacturer-datasheets/DOWNLOAD-GUIDE.md` (modified — added AHT20 and BH1750 datasheet links)
  - `hardware-design/board-design-v04.md` (modified — BOM +U6/U7, GPIO table, Zone D, cost $5.20)
  - `hardware-design/BOM.md` (modified — +U7 AHT20, +U8 BH1750, +C10/C11, cost $5.12)
  - `hardware-design/parts-sheets/README.md` (modified — +2 sensor entries, count 27→31)
  - `website/docs/docs/hardware/materials-list.md` (modified — +U6/U7 rows)
  - `website/docs/docs/hardware/wiring-pinout.md` (modified — I2C address map, 3-sensor block diagram)
  - `website/docs/docs/design/board-design.md` (modified — 30 components, Zone D sensors, ASCII layout)
  - `website/docs/docs/design/kicad-schematic-pcb-guide.md` (modified — added sections 2.9 AHT20 and 2.10 BH1750)
  - `README.md` (modified — 30 components, sensor list)
  - `PromptProgression.md` (updated)

---

## Prompt #166
- **Date/Time:** 2026-04-15
- **Prompt:** "Pull the pictures for this component and update the hardware plan and website documents. Also update the prompts and all relevant documentation."
- **Input Tokens (est):** ~30
- **Output Tokens (est):** ~20,000
- **Commit:** `7a0fab4` — Add prompt log #163-167, schematic generator script, clean up prompts
- **Files Created/Modified:**
  - All sensor documentation verified and cross-referenced across 12 files (see Prompt #165 for full list)
  - `PromptProgression.md` (updated — spelling/grammar cleanup, added Prompts #163-167)

---

## Prompt #167
- **Date/Time:** 2026-04-15
- **Prompt:** "Add that board design guide you made to the website docs and commit last change and update the prompts. Also be sure to clean up the spelling and grammar in the prompt progression as well."
- **Input Tokens (est):** ~30
- **Output Tokens (est):** ~5,000
- **Commit:** `7a0fab4` — Add prompt log #163-167, schematic generator script, clean up prompts
- **Files Created/Modified:**
  - `PromptProgression.md` (modified — spelling/grammar cleanup across all 167 entries, added Prompts #163-167)

---

## Prompt #168
- **Date/Time:** 2026-04-15
- **Prompt:** "OK we are going to build out the dev tools to emulate this device, have it actually compile and run the C code that will be running on the device, and allow for joystick input and emulation of the sensor systems — pedometer, temp, light sensor, humidity, etc. So let's do this: let's add a robust Dilder tab to give emulation, to load up this game and run and debug it. So step one is to implement the C code for this. Make an entirely new directory folder to handle all the C development and implementation. Plan out the project structure and architecture, then code this out so that it can be run via the dev tool."
- **Input Tokens (est):** ~130
- **Output Tokens (est):** ~120,000
- **Commit:** `d3388a3` — Add firmware game engine, DevTool Dilder emulator tab, and documentation
- **Files Created/Modified:**
  - `firmware/` (created — entire directory: 35 source files)
  - `firmware/CMakeLists.txt` (created — CMake build producing libdilder.so + dilder_cli)
  - `firmware/.gitignore` (created — excludes build/)
  - `firmware/include/dilder.h` (created — public shared library API)
  - `firmware/include/game/game_state.h` (created — all data types: 808 lines)
  - `firmware/include/game/event.h` (created — event bus interface)
  - `firmware/include/game/stat.h` (created — stat system interface)
  - `firmware/include/game/emotion.h` (created — emotion engine interface)
  - `firmware/include/game/life.h` (created — life stages interface)
  - `firmware/include/game/time_mgr.h` (created — time manager interface)
  - `firmware/include/game/dialog.h` (created — dialogue system interface)
  - `firmware/include/game/progress.h` (created — progression/bond interface)
  - `firmware/include/game/game_loop.h` (created — game loop interface)
  - `firmware/include/sensor/sensor.h` (created — sensor emulation interface)
  - `firmware/include/ui/input.h` (created — button input queue)
  - `firmware/include/ui/render.h` (created — framebuffer rendering)
  - `firmware/include/ui/ui.h` (created — UI state machine)
  - `firmware/src/game/event.c` (created — event bus with ring buffer)
  - `firmware/src/game/time_mgr.c` (created — virtual game clock)
  - `firmware/src/game/stat.c` (created — decay, care actions, thresholds, modifiers: 776 lines)
  - `firmware/src/game/emotion.c` (created — 16 emotion triggers + resolution algorithm: 664 lines)
  - `firmware/src/game/life.c` (created — life stage FSM + evolution branching: 533 lines)
  - `firmware/src/game/dialog.c` (created — quote database, 80+ quotes across 16 moods)
  - `firmware/src/game/progress.c` (created — bond XP + leveling)
  - `firmware/src/game/game_loop.c` (created — main orchestrator: 483 lines)
  - `firmware/src/sensor/sensor.c` (created — emulated sensor values + event classification)
  - `firmware/src/ui/input.c` (created — circular buffer input queue)
  - `firmware/src/ui/render.c` (created — bitmap font, drawing primitives, octopus renderer: 1,296 lines)
  - `firmware/src/ui/ui.c` (created — menu FSM, input dispatch, screen rendering: 520 lines)
  - `firmware/src/platform/desktop/dilder_api.c` (created — shared library API for Python ctypes)
  - `firmware/src/platform/desktop/main_desktop.c` (created — standalone CLI test runner)
  - `DevTool/devtool.py` (modified — added DilderEmulatorTab class with display canvas, joystick, sensor sliders, game state panel, play/pause/step/reset, speed control, rebuild button)

---

## Prompt #169
- **Date/Time:** 2026-04-15
- **Prompt:** "OK I need you to make comments through the firmware files as if I don't know C code that well. Explain in depth what every function is doing and any complex line of code, and also the memory management in the code. Be detailed — this is to help in learning. Then we also need an MD doc in the firmware folder to outline the project structure, architecture, and guides to reading the code and debugging. Also update the software documentation and add this to the list of software on the website with the documentation as well."
- **Input Tokens (est):** ~100
- **Output Tokens (est):** ~150,000
- **Commit:** `d3388a3` (same commit — work done in same session)
- **Files Created/Modified:**
  - All 14 `.c` source files and 2 key `.h` headers rewritten with comprehensive beginner-friendly comments (every function documented, bitwise ops explained, memory model annotated, C patterns taught inline)
  - `firmware/FIRMWARE.md` (created — 633-line architecture guide: project structure, 5-level reading order, module deep dives, memory model, framebuffer layout, game tick flow, event system, emotion resolution, DevTool bridge, debugging guide, C patterns glossary)
  - `website/docs/docs/software/firmware-engine.md` (created — website documentation page with Mermaid architecture diagram, game systems overview, sensor emulation table, API reference)
  - `website/mkdocs.yml` (modified — added Firmware Game Engine to Software nav)
  - `website/docs/docs/software/project-structure.md` (modified — updated firmware section from placeholder to actual structure)

---

## Prompt #170
- **Date/Time:** 2026-04-15
- **Prompt:** "OK commit all the changes and update the prompts with the commit hash and prompts and such. Fix them word spellings and shit and commit again and push."
- **Input Tokens (est):** ~30
- **Output Tokens (est):** ~8,000
- **Commit:** `2d7a8b8` — Add prompt log #168-170, firmware engine and documentation entries
- **Files Created/Modified:**
  - `PromptProgression.md` (modified — added Prompts #168-170, spelling/grammar cleanup)

---

## Prompt #171 — 2026-04-17
- **Prompt:** "OK the setup needs to have options in each step if needed to differentiate and choose the ESP board, as well update the CLI."
- **Input Tokens (est):** ~40
- **Output Tokens (est):** ~45,000
- **Commit:** `0a64ad8` — Add ESP32-S3 multi-board support across DevTool, setup CLI, firmware, and docs
- **Files Created/Modified:**
  - `setup.py` (modified — added `--board {pico,esp32}` flag, board tags on all 16 steps, interactive board selection menu at startup, `step_matches_board()` filtering, `_install_python_app()` helper using pipx on Arch/CachyOS for PEP 668 compliance, board-aware walkthrough overview text)
  - `ESP Protyping/dev setup guide.md` (modified — renamed to multi-board guide, added "Choosing Your Board" section, every deployment step (1-6) now has Pico W and ESP32-S3 subsections, troubleshooting organized by board, automated section documents `--board` flag, Arch pipx instructions added)

---

## Prompt #172 — 2026-04-17
- **Prompt:** "PlatformIO install fails with externally-managed-environment error (PEP 668 on Arch/CachyOS)."
- **Input Tokens (est):** ~100 (error log)
- **Output Tokens (est):** ~8,000
- **Commit:** `0a64ad8` — Add ESP32-S3 multi-board support across DevTool, setup CLI, firmware, and docs
- **Files Created/Modified:**
  - `setup.py` (modified — added `_pip_is_externally_managed()` check, `_install_python_app()` that uses pipx on Arch via pacman, replaced raw pip calls in step 16 with the new helper)
  - `ESP Protyping/dev setup guide.md` (modified — added pipx instructions for Arch, added PEP 668 troubleshooting entry)

---

## Prompt #173 — 2026-04-17
- **Prompt:** "Add a selection option to select the setup option depending on the board intended to be used to the setup, make a CLI interface to do this."
- **Input Tokens (est):** ~30
- **Output Tokens (est):** ~5,000
- **Commit:** `0a64ad8` — Add ESP32-S3 multi-board support across DevTool, setup CLI, firmware, and docs
- **Files Created/Modified:**
  - `setup.py` (modified — added interactive board selection menu: "1) Pico W, 2) ESP32-S3, 3) Both" prompt at walkthrough start, skipped when `--board` is passed or `--step` is used)

---

## Prompt #174 — 2026-04-17
- **Prompt:** "PlatformIO build fails: board_config.h not found, then HAL linker errors, then hal_init symbol collision."
- **Input Tokens (est):** ~200 (build logs)
- **Output Tokens (est):** ~12,000
- **Commit:** `0a64ad8` — Add ESP32-S3 multi-board support across DevTool, setup CLI, firmware, and docs
- **Files Created/Modified:**
  - `ESP Protyping/dilder-esp32/platformio.ini` (modified — added `-I../../firmware/include` to build_flags, fixed build_src_filter paths from `../../` to `../../../`, removed invalid `build_src_extra` option)
  - `ESP Protyping/dilder-esp32/include/platform/board_config.h` (deleted — removed shadowing local copy with PIN_JOY_* names)
  - `firmware/src/platform/esp32s3/esp32s3_hal.c` (renamed to `.cpp` — C++ needed for Arduino SPI classes, added `extern "C"` linkage block)
  - `firmware/include/platform/hal.h` (modified — renamed `hal_init` to `dilder_hal_init` to avoid ESP-IDF collision)
  - `ESP Protyping/dilder-esp32/src/main.cpp` (modified — updated `hal_init()` call to `dilder_hal_init()`)

---

## Prompt #175 — 2026-04-17
- **Prompt:** "OK the DevTool Programs tab needs a board selection dropdown above the display model to select either the ESP or Pico, then allows me to deploy standalone or flash to the specified board. Make sure each program can deploy to the ESP."
- **Input Tokens (est):** ~50
- **Output Tokens (est):** ~25,000
- **Commit:** `0a64ad8` — Add ESP32-S3 multi-board support across DevTool, setup CLI, firmware, and docs
- **Files Created/Modified:**
  - `DevTool/devtool.py` (modified — ProgramsTab: added Target Board dropdown with serial detection status, ESP32 flash via PlatformIO `_build_and_flash_esp32()`, ESP32 standalone deploy `_deploy_standalone_esp32()` generating quotes.h + PlatformIO build + flash, board-aware flash hints, board-agnostic serial status messages; DilderDevTool: `target_board` property now handles label/key reverse-lookup, `_on_board_changed` syncs Programs tab combo, `_update_flash_hint` early-return guard)

---

## Prompt #176 — 2026-04-17
- **Prompt:** "Update the Connect tab when the target board is changed, I need separate steps for the ESP board. Also I need steps based on my ESP board on how to put it in download mode. Once done, update all the docs and website and add new blog and docs, commit then pull the prompts and update the prompts doc and update the website prompt blog."
- **Input Tokens (est):** ~60
- **Output Tokens (est):** ~50,000
- **Commit:** `0a64ad8` — Add ESP32-S3 multi-board support across DevTool, setup CLI, firmware, and docs
- **Files Created/Modified:**
  - `DevTool/devtool.py` (modified — ConnectionUtility: added `refresh_for_board()`, `_build_usb_panel_esp32()` with 5 ESP32-specific steps including CH340X detection, /dev/ttyUSB* check, download mode button sequence diagram, `_build_wifi_panel_esp32()` with Arduino WiFi setup, `_check_usb_esp32()` and `_check_serial_esp32()` detection methods; board indicator label in mode selector; DilderDevTool._on_board_changed now refreshes conn_tab)
  - `website/docs/docs/setup/first-time-setup.md` (modified — added `--board` CLI examples, Step 16 to table, board tags column)
  - `website/docs/blog/posts/esp32-board-support.md` (created — blog post about multi-board architecture going live)
  - `PromptProgression.md` (modified — added Prompts #171-176)
  - `website/docs/prompts/index.md` (modified — synced with PromptProgression.md)

---

## Prompt #177 — 2026-04-17
- **Prompt:** "OK we are going to build out the dev tools to emulate this device, have it actually compile and run the C code that will be running on the device, and allow for joystick input and emulation of the sensor systems — pedometer, temp, light sensor, humidity, etc. So let's do this: let's add a robust Dilder tab to give emulation, to load up this game and run and debug it. So step one is to implement the C code for this. Make an entirely new directory folder to handle all the C development and implementation. Plan out the project structure and architecture, then code this out so that it can be run via the dev tool."
- **Input Tokens (est):** ~130
- **Output Tokens (est):** ~120,000
- **Commit:** `d3388a3` — Add firmware game engine, DevTool Dilder emulator tab, and documentation
- **Files Created/Modified:**
  - `firmware/` (created — entire directory: 35 source files implementing complete game engine)
  - `DevTool/devtool.py` (modified — added DilderEmulatorTab with display canvas, joystick, sensor sliders, game state panel)

---

## Prompt #178 — 2026-04-17
- **Prompt:** "OK I need you to make comments through the firmware files as if I don't know C code that well. Explain in depth what every function is doing and any complex line of code, and also the memory management in the code. Be detailed — this is to help in learning. Then we also need an MD doc in the firmware folder to outline the project structure, architecture, and guides to reading the code and debugging. Also update the software documentation and add this to the list of software on the website with the documentation as well."
- **Input Tokens (est):** ~100
- **Output Tokens (est):** ~150,000
- **Commit:** `76f3079` — Port mood-selector to ESP32-S3, add implementation docs and code comments
- **Files Created/Modified:**
  - All 14 `.c` source files and 2 key `.h` headers rewritten with comprehensive beginner-friendly comments
  - `firmware/FIRMWARE.md` (created — 633-line architecture guide with 5-level reading order, debugging guide, C patterns glossary)
  - `website/docs/docs/software/firmware-engine.md` (created — website docs with Mermaid architecture diagram)
  - `website/mkdocs.yml` (modified — added Firmware Game Engine to nav)
  - `website/docs/docs/software/project-structure.md` (modified — updated firmware section)

---

## Prompt #179 — 2026-04-17
- **Prompt:** "Add the MSK-12C02 power switch to the board design — add it, pull in the specs datasheet, and add an MD file with documentation on it."
- **Input Tokens (est):** ~30
- **Output Tokens (est):** ~40,000
- **Commit:** n/a — work abandoned before commit — MSK-12C02 switch parts sheet + board-design files never preserved in git history (later purged in `85238b0`)
- **Files Created/Modified:**
  - `hardware-design/parts-sheets/msk-12c02.md` (created — 294-line parts sheet: SPDT slide switch mechanics, contact materials, power path design, enclosure slot notes)
  - `hardware-design/BOM.md` (modified — added SW2, updated to v0.4, 32 components)
  - `hardware-design/board-design-v04.md` (modified — added SW2 to Zone C, BOM table, ASCII layout, renumbered BOOT/RESET to SW3/SW4)
  - `hardware-design/parts-sheets/README.md` (modified — added MSK-12C02 entry, updated count to 32)
  - `hardware-design/parts-sheets/manufacturer-datasheets/DOWNLOAD-GUIDE.md` (modified — added datasheet link)
  - `website/docs/docs/hardware/materials-list.md` (modified — added SW2 row, component gallery with 12 photos)
  - `website/docs/docs/design/board-design.md` (modified — added SW2 to BOM, Zone C, ASCII layout)
  - `website/docs/docs/design/kicad-schematic-pcb-guide.md` (modified — added section 2.5b Power Switch with wiring steps)

---

## Prompt #180 — 2026-04-17
- **Prompt:** "Get me a full parts list for the planned new board with the power switch. Get me a BOM file and JLCPCB KiCad parts list. I don't want any extended parts — well, limit them as much as possible."
- **Input Tokens (est):** ~40
- **Output Tokens (est):** ~30,000
- **Commit:** n/a — work abandoned before commit — JLCPCB/BOM optimization files never preserved in git history (later purged in `85238b0`)
- **Files Created/Modified:**
  - `hardware-design/jlcpcb-kicad-parts.md` (created — optimized BOM with basic/extended tier for each part, 3 parts swapped to basic saving ~$9/order, LCSC quick-copy list, KiCad footprint notes)
  - `hardware-design/BOM.md` (modified — filled in missing LCSC codes: J3→C160407, R8/R9→C25905)

---

## Prompt #181 — 2026-04-17
- **Prompt:** "Draw me up a schematic image with all these parts connected up together, make a nice JPEG file I can see. Also provide description labels of what the bigger components do."
- **Input Tokens (est):** ~30
- **Output Tokens (est):** ~25,000
- **Commit:** n/a — work abandoned before commit — schematic-overview JPEG + generator script never preserved in git history (later purged in `85238b0`)
- **Files Created/Modified:**
  - `hardware-design/generate_schematic_image.py` (created — Pillow script generating full-board schematic overview)
  - `hardware-design/dilder-pcb-schematic-overview.jpg` (created — 3200x2000 schematic showing power path, ESP32, I2C sensors, SPI display, joystick, BOM summary, JLCPCB cost breakdown)

---

## Prompt #182 — 2026-04-17
- **Prompt:** "The programs don't work as expected, the joystick mood selector for example just shows a Dilder splash screen and not the octopus and quotes and selection like the Pico was doing. We need to fix the programs so they work identically."
- **Input Tokens (est):** ~50
- **Output Tokens (est):** ~80,000
- **Commit:** `6bbcad0` — Add joystick GPIO debug diagnostics to ESP32-S3 mood selector
- **Files Created/Modified:**
  - `ESP Protyping/dilder-esp32/src/main.cpp` (rewritten — full port of Pico mood-selector: RLE body, 16 eye variants, 17 mouths, body animations, 823 quotes, joystick + serial input, GxEPD2 display push)
  - `ESP Protyping/dilder-esp32/src/quotes.h` (copied from dev-setup/mood-selector/)

---

## Prompt #183 — 2026-04-17
- **Prompt:** "OK let's update the implementation docs for the code we set up in C for the programs. I need you to outline the project structure and code layout and design principles along with a deep explanation of each file. Let's also comment the code thoroughly to explain it to a person new to C. Then commit and push the changes and update the website docs and commit and push that. Then update the prompts with the session data from today on this computer."
- **Input Tokens (est):** ~60
- **Output Tokens (est):** ~60,000
- **Commit:** `76f3079` — Port mood-selector to ESP32-S3, add implementation docs and code comments
- **Files Created/Modified:**
  - `ESP Protyping/dilder-esp32/src/main.cpp` (modified — comprehensive beginner-friendly comments: rendering pipeline, GxEPD2 pattern, bit math, RLE encoding, font encoding, edge detection, Arduino execution model)
  - `firmware/include/platform/hal.h` (modified — HAL pattern explanation, function declarations vs definitions, extern "C" block)
  - `firmware/include/platform/board_config.h` (modified — preprocessor chain explanation, SPI bus selection, pin mapping per board)
  - `firmware/src/platform/esp32s3/esp32s3_hal.cpp` (modified — Arduino API explanation, INPUT_PULLUP/active-LOW logic, ADC voltage divider math, SPI init, extern "C")
  - `ESP Protyping/dilder-esp32/README.md` (created — 374-line implementation guide: architecture diagram, code layout map, rendering pipeline, display comparison, input handling, design principles, debugging)
  - `website/docs/docs/software/esp32-firmware.md` (created — website docs with Mermaid flow, controls table, pin mapping, memory usage)
  - `website/mkdocs.yml` (modified — added ESP32-S3 Firmware to Software nav)
  - `DevTool/devtool.py` (modified — PATH fix for pipx-installed PlatformIO)
  - `setup.py` (modified — PATH fix for pipx-installed PlatformIO in step 16 + status report)
  - `PromptProgression.md` (modified — added Prompts #177-183)

---

## Prompt #184 — 2026-04-22
- **Prompt:** "You made a middle.3mf file for this design. Give me a .scad script that I can modify. Also provide an export-to-3mf-from-scad guide and cook up a script to do this as well in Python with a menu and file explorer. Put this all in the scad parts folder."
- **Input Tokens (est):** ~60
- **Output Tokens (est):** ~45,000
- **Commit:** `632db0d` — Add v1 standalone middle plate SCAD, export guide, and Python export tool
- **Files Created/Modified:**
  - `hardware-design/scad Parts/middle-plate.scad` (created — standalone parametric middle plate extracted from esp32s3-enclosure.scad)
  - `hardware-design/scad Parts/scad-to-3mf-guide.md` (created — step-by-step export guide: CLI, GUI, batch, slicer tips, troubleshooting)
  - `hardware-design/scad Parts/scad-export.py` (created — interactive Python export tool with file browser, batch export, CLI mode)

---

## Prompts #185–194 — 2026-04-22
- **Prompt series:** Iterative CAD refinement session. Walk through middle plate geometry, extend header slot length to 56mm then 56.5mm, center slots on plate, fix pillar cutout overshoot for clean booleans, extract 3 components from topscreenassembly.3mf into standalone .scad files (top-plate-solid, top-plate-windowed, top-cover), redesign top cover as open frame (v2) with solid border and countersunk pillar pockets, redesign windowed plate (v1) with solid face, extended retaining rails, printable full-width lips, and rail-only wire gap. Attempted dome face plate (reverted).
- **Input Tokens (est):** ~500
- **Output Tokens (est):** ~120,000
- **Files Created/Modified:**
  - `hardware-design/scad Parts/middle-plate.scad` (modified — 56.5mm centered slots, clean pillar cutout overshoot)
  - `hardware-design/scad Parts/middle-plate-v1.scad` (created — v1 snapshot)
  - `hardware-design/scad Parts/middle-plate-v2.scad` (created — v2 snapshot)
  - `hardware-design/scad Parts/top-plate-solid.scad` (created — display cover without window)
  - `hardware-design/scad Parts/top-plate-windowed.scad` (created — display cover with window, original version)
  - `hardware-design/scad Parts/top-plate-windowed-v1.scad` (created — solid face, extended rails, printable lips, rail-only wire gap)
  - `hardware-design/scad Parts/top-cover.scad` (created — original dome cover)
  - `hardware-design/scad Parts/top-cover-v2.scad` (created — open frame, solid border, countersunk pillars)

---

## Prompt #195 — 2026-04-22
- **Prompt:** "OK let's gather a few screenshots of the new CAD designs and add it to the website. We need a living page for this project's design evolution. Also update the docs and everywhere sensible and update the prompts after committing, and commit and push."
- **Input Tokens (est):** ~50
- **Output Tokens (est):** ~60,000
- **Commit:** `762625a` — Add SCAD enclosure doc, blog post, renders, and Prompts #211-227
- **Files Created/Modified:**
  - `website/docs/assets/images/enclosure/middle-plate-v2.png` (created — OpenSCAD render)
  - `website/docs/assets/images/enclosure/top-plate-windowed-v1.png` (created — OpenSCAD render)
  - `website/docs/assets/images/enclosure/top-cover-v2.png` (created — OpenSCAD render)
  - `website/docs/assets/images/enclosure/full-enclosure-assembly.png` (created — OpenSCAD render)
  - `website/docs/docs/hardware/design-evolution.md` (created — living design evolution page with renders, specs, version history)
  - `website/mkdocs.yml` (modified — added Design Evolution to Hardware nav)
  - `website/docs/docs/hardware/enclosure-design.md` (modified — added ESP32-S3 update note and link to design evolution)
  - `PromptProgression.md` (modified — added Prompts #184-195)

---

## Prompts #196–202 — 2026-04-22
- **Prompt series:** Continued enclosure CAD iteration. Added countersunk pillar pockets to top cover v2. Created top cover v3 with rounded inner corners matching the windowed plate's corner radius. Added single-corner-rounded pillars (only the exposed inner corner of each pillar gets the radius). Created top-cover-v3-rounded-top variant with 2mm bullnose top edge. Created case separator sheets (inner and outer) as thin divider plates with header pass-through slots and screw holes. Applied single-corner-rounded pillars to the rounded-top variant as well.
- **Input Tokens (est):** ~400
- **Output Tokens (est):** ~80,000
- **Files Created/Modified:**
  - `hardware-design/scad Parts/top-cover-v2.scad` (modified — countersunk pillar pockets, exact pillar sizing to avoid border bleed)
  - `hardware-design/scad Parts/top-cover-v3.scad` (created — rounded inner corners, single-corner-rounded pillars)
  - `hardware-design/scad Parts/top-cover-v3-rounded-top.scad` (created — v3 with bullnose top edge + single-corner-rounded pillars)
  - `hardware-design/scad Parts/case-separator-inner.scad` (created — thin divider, inner plate footprint, header slots, screw holes)
  - `hardware-design/scad Parts/case-separator-outer.scad` (created — thin divider, outer base footprint, header slots, screw holes)

---

## Prompt #203 — 2026-04-22
- **Prompt:** "OK I added some pictures to the base of the project directory. Analyze, annotate, rename, and convert to JPEG. Delete the HEIC versions, put them in the images folder for the website and docs, update the docs and blog with the latest progress, update the prompts and fix my English as well. Commit and push."
- **Input Tokens (est):** ~60
- **Output Tokens (est):** ~50,000
- **Commit:** `762625a` — Add SCAD enclosure doc, blog post, renders, and Prompts #211-227
- **Files Created/Modified:**
  - `IMG*.heic` (7 files deleted — converted to JPEG and removed from project root)
  - `website/docs/assets/images/enclosure/enclosure-assembled-front.jpg` (created — front view of assembled case with e-ink display)
  - `website/docs/assets/images/enclosure/enclosure-halves-with-battery.jpg` (created — base shell with LiPo + display top cover)
  - `website/docs/assets/images/enclosure/components-layout-overview.jpg` (created — all printed parts and electronics spread)
  - `website/docs/assets/images/enclosure/esp32-board-on-printed-parts.jpg` (created — Olimex DevKit-Lipo on middle plate)
  - `website/docs/assets/images/enclosure/middle-plate-header-slots-closeup.jpg` (created — header slot detail)
  - `website/docs/assets/images/enclosure/middle-plate-and-joystick-closeup.jpg` (created — middle plate + joystick breakout)
  - `website/docs/assets/images/enclosure/dev-workstation-overview.jpg` (created — dual-monitor dev setup with wired prototype)
  - `website/docs/docs/hardware/design-evolution.md` (modified — added physical prototype photo section)
  - `website/docs/blog/posts/enclosure-first-prints.md` (created — blog post on first 3D-printed prototype)
  - `PromptProgression.md` (modified — added Prompts #196-203)

---

## Prompts #204–207 — 2026-04-22
- **Prompt series:** Created 6 top cover height variants (12mm, 17mm, 22mm for both flat-top and rounded-top v3). Expanded the windowed plate outer edge by 0.5mm per side for a tighter fit in the cover frame. Analyzed a new HEIC photo of the ESP32-S3 board fit-check, converted to JPEG, and used it to design a board cradle separator — an outer-footprint sheet with a board-shaped cutout and a 2mm raised cradle wall to hold the board in place. Updated design evolution page with new parts, version history entries, and the fit-check photo. Committed and pushed.
- **Input Tokens (est):** ~250
- **Output Tokens (est):** ~40,000
- **Files Created/Modified:**
  - `hardware-design/scad Parts/top-cover-v3-{12,17,22}mm.scad` (created — height variants of flat-top v3)
  - `hardware-design/scad Parts/top-cover-v3-rounded-top-{12,17,22}mm.scad` (created — height variants of rounded-top v3)
  - `hardware-design/scad Parts/top-plate-windowed-v1.scad` (modified — +0.5mm outer edge expansion)
  - `hardware-design/scad Parts/case-separator-board-cradle.scad` (created — outer separator with board cutout and raised cradle wall)
  - `website/docs/assets/images/enclosure/esp32-board-fitcheck-closeup.jpg` (created — board fit-check photo)
  - `website/docs/docs/hardware/design-evolution.md` (modified — new parts table, version history, fit-check photo)
  - `PromptProgression.md` (modified — added Prompts #204-207)

---

## Prompts #208–210 — 2026-04-22
- **Prompt series:** Trimmed windowed plate retaining rails by 0.5mm from the display-facing side (rails stay flush with plate edges, just narrower for easier screen insertion without bending). Widened board cradle separator cutout by 1mm per side for better board clearance. Updated design evolution version history and pushed.
- **Input Tokens (est):** ~150
- **Output Tokens (est):** ~15,000
- **Files Created/Modified:**
  - `hardware-design/scad Parts/top-plate-windowed-v1.scad` (modified — rail_trim=0.5mm from display side, flush outer edges preserved)
  - `hardware-design/scad Parts/case-separator-board-cradle.scad` (modified — cutout_extra=1mm per side)
  - `website/docs/docs/hardware/design-evolution.md` (modified — version history entries for rail trim and cradle widening)
  - `PromptProgression.md` (modified — added Prompts #208-210)

---

## Prompt #211 — 2026-04-22
- **Prompt:** "OK the is a puext1 port on the esp32 wroom board i have can this be connected to the waveshare display?"
- **Input Tokens (est):** ~25
- **Output Tokens (est):** ~4,500
- **Commit:** `762625a` — Add SCAD enclosure doc, blog post, renders, and Prompts #211-227
- **Files:** Research-only, no files changed. Identified `pUEXT1` as Olimex ESP32-S3-DevKit-Lipo UEXT10 connector. Mapped 10-pin pinout from reference schematic (GPIO17/18 UART, GPIO47/48 I2C, GPIO10–13 SPI). Compared to Waveshare 2.13" SPI 8-pin requirements and documented how pin repurposing would fill the gaps.

---

## Prompt #212 — 2026-04-22
- **Prompt:** "Can the display be wired into the OTGUSB port? or the joystick one of the two?"
- **Input Tokens (est):** ~20
- **Output Tokens (est):** ~2,800
- **Commit:** `762625a` — Add SCAD enclosure doc, blog post, renders, and Prompts #211-227
- **Files:** Research-only. USB-OTG is a protocol port (VBUS 5V, D+/D-, GND) — only 4 wires, can't drive SPI; "joystick port" is not a dedicated port — the DollaTek 5-way is jumper-wired into EXT1 header GPIOs.

---

## Prompt #213 — 2026-04-22
- **Prompt:** "[Measurements paste + case sandwich spec] 22mm between headers, antenna 18mm wide 6mm off, board 56x28mm. Need 4 square pillars nestled by the antenna corners + at the bottom of the board. Sandwich the board between a plane and a top cover, with a third plate 6mm below the headers. Let's make a SCAD script to plot this out."
- **Input Tokens (est):** ~250
- **Output Tokens (est):** ~7,500
- **Commit:** `762625a` — Add SCAD enclosure doc, blog post, renders, and Prompts #211-227
- **Files:**
  - `hardware-design/esp32s3-sandwich-mount.scad` (created — 3-plate sandwich mount with 4 corner pillars, screw channels, header pin slots, center window in top plate).

---

## Prompt #214 — 2026-04-22
- **Prompt:** "Rethink it — stack the board in the middle resting on a 2mm plastic plane, 5mm above the screen will be a cover with a hole for the display that curves down around the side. On the long sides slots for the screen to slide into. 6mm below the board another 2mm plastic layer for the battery. Still 4 square pillars. USB-C ports meet the edge with walls and holes. Make it in a SCAD script and copy it to a 3MF to print on Bambu."
- **Input Tokens (est):** ~180
- **Output Tokens (est):** ~12,000
- **Commit:** `762625a` — Add SCAD enclosure doc, blog post, renders, and Prompts #211-227
- **Files:**
  - `hardware-design/esp32s3-enclosure.scad` (created — full 3-piece enclosure: base with battery tray + side walls + USB-C cutouts + display slots, middle board tray, rounded top cover with display window).
  - `hardware-design/enclosure-prints/{base,middle,cover}.3mf` exported via OpenSCAD CLI.

---

## Prompt #215 — 2026-04-22
- **Prompt:** "Looks good but we need a spot for the middle piece to rest on when it's placed in the case."
- **Input Tokens (est):** ~25
- **Output Tokens (est):** ~3,500
- **Commit:** `762625a` — Add SCAD enclosure doc, blog post, renders, and Prompts #211-227
- **Files:**
  - `hardware-design/esp32s3-enclosure.scad` (modified — added `mid_plate_support()`: 2mm short-wall ledges between pillars + 4 pillar-corner tabs for 4-point plate support).
  - `enclosure-prints/base.3mf` re-exported.

---

## Prompt #216 — 2026-04-22
- **Prompt:** "Add another middle piece on top of the base that covers the rect holes on the side — a thin plastic pane with two 20mm slots on the middle of both sides of the long edge, 8mm inset."
- **Input Tokens (est):** ~60
- **Output Tokens (est):** ~5,500
- **Commit:** `762625a` — Add SCAD enclosure doc, blog post, renders, and Prompts #211-227
- **Files:**
  - `hardware-design/esp32s3-enclosure.scad` (modified — added `top_mid_plate` module, generalized `plate_shelf()` to support both z=8 and z=20.8 levels).
  - `enclosure-prints/topmid.3mf` created.

---

## Prompt #217 — 2026-04-22
- **Prompt:** "Get rid of the holes on the long edge in the base — there should only be 2 holes for the USB-C on that. Bevel all the outside edges and give the case a nice curve to it."
- **Input Tokens (est):** ~50
- **Output Tokens (est):** ~6,500
- **Commit:** `762625a` — Add SCAD enclosure doc, blog post, renders, and Prompts #211-227
- **Files:**
  - `hardware-design/esp32s3-enclosure.scad` (modified — removed display side-slot cutouts, added `rounded_v_box` helper for rounded vertical edges, cover redesigned to wrap over base with matching curves). All 4 pieces re-exported.

---

## Prompt #218 — 2026-04-22
- **Prompt:** "Add internal rails, make the base bottom as curvy as the top, fix print errors — the shelf edges need to extend to the bottom of the base so the printer can print properly."
- **Input Tokens (est):** ~70
- **Output Tokens (est):** ~14,000
- **Commit:** `762625a` — Add SCAD enclosure doc, blog post, renders, and Prompts #211-227
- **Files:**
  - `hardware-design/esp32s3-enclosure.scad` (modified — added `display_rails()` corner posts, `extend_to_floor` flag on lower shelf so it becomes a printable rib, curved bottom via sphere-offset trick for ~30° overhang).

---

## Prompt #219 — 2026-04-22
- **Prompt:** "Inset the shelves so the top-mid plate lays flush on top of the base. Also make screw hardware to fit in the screw holes so I can solder-meld it shut. The top-mid plate is not aligned with the base — I need everything to be flush and fit the components."
- **Input Tokens (est):** ~80
- **Output Tokens (est):** ~16,000
- **Commit:** `762625a` — Add SCAD enclosure doc, blog post, renders, and Prompts #211-227
- **Files:**
  - `hardware-design/esp32s3-enclosure.scad` (rewritten — raised `base_wall_top` to `z_disp_top + plate_thk` for flush plate, same-footprint cover, added `screw_plug`/`screw_plug_array` modules, `"screws"` render target).

---

## Prompt #220 — 2026-04-22
- **Prompt:** "The cover plate needs altering. Get rid of the display slot and add two long rails for the display to snap into. Also the base bottom needs to taper in the same manner as the cover. Ensure everything remains flush on the sides."
- **Input Tokens (est):** ~60
- **Output Tokens (est):** ~9,000
- **Commit:** `762625a` — Add SCAD enclosure doc, blog post, renders, and Prompts #211-227
- **Files:**
  - `hardware-design/esp32s3-enclosure.scad` (modified — removed topmid edge slots, added snap rails with 0.5mm bottom lips on top-mid plate underside, set `base_bot_cut = 0` for cover-matching taper).

---

## Prompt #221 — 2026-04-22
- **Prompt:** "You indented the wrong holes. It should be on the base — the 4 holes should go down the width of the top-mid plate so that it doesn't cause a gap."
- **Input Tokens (est):** ~45
- **Output Tokens (est):** ~4,500
- **Commit:** `762625a` — Add SCAD enclosure doc, blog post, renders, and Prompts #211-227
- **Files:**
  - `hardware-design/esp32s3-enclosure.scad` (modified — shortened base display-rail posts from `base_wall_top` to `z_disp_top`, removed corner notches from top-mid plate so its top face is solid with no through-holes or gaps).

---

## Prompt #222 — 2026-04-22
- **Prompt:** "The cover should not have a plastic plane on the base side of the model. The base should be completely open to the view window. Also on the top-mid model, on one of the long sides we need a 30mm by 6mm hole in the middle cut into the rail as well so wires can be fished through."
- **Input Tokens (est):** ~70
- **Output Tokens (est):** ~7,000
- **Commit:** `762625a` — Add SCAD enclosure doc, blog post, renders, and Prompts #211-227
- **Files:**
  - `hardware-design/esp32s3-enclosure.scad` (modified — removed cover's top plate leaving 4 corner posts + walls, added `topmid_window_w/l` cutout (25×50) and `wire_hole_len/depth` (30×6) on top-mid plate -X edge that cuts through both plate and snap rail).

---

## Prompt #223 — 2026-04-22
- **Prompt:** "No, you took off the wrong side of plastic on the cover. That was the top. Take off the opposite side instead."
- **Input Tokens (est):** ~25
- **Output Tokens (est):** ~2,500
- **Commit:** `762625a` — Add SCAD enclosure doc, blog post, renders, and Prompts #211-227
- **Files:**
  - `hardware-design/esp32s3-enclosure.scad` (modified — restored cover's top plate with 25×50 viewing window aligned with top-mid plate window; bottom remains open).

---

## Prompt #224 — 2026-04-22
- **Prompt:** "Go back to the previous and cut a 30mm by 6mm hole on the cover base to route wires."
- **Input Tokens (est):** ~25
- **Output Tokens (est):** ~2,200
- **Commit:** `762625a` — Add SCAD enclosure doc, blog post, renders, and Prompts #211-227
- **Files:**
  - `hardware-design/esp32s3-enclosure.scad` (modified — reverted cover to open-top and added a 30×6 notch at the bottom of the -X long wall).

---

## Prompt #225 — 2026-04-22
- **Prompt:** "Hole is on the wrong edge. It should be on the bottom not side."
- **Input Tokens (est):** ~20
- **Output Tokens (est):** ~1,500
- **Commit:** `762625a` — Add SCAD enclosure doc, blog post, renders, and Prompts #211-227
- **Files:**
  - `hardware-design/esp32s3-enclosure.scad` (modified — moved the wire notch from the -X long wall to the -Y short wall at the bottom edge, centered along X).

---

## Prompt #226 — 2026-04-22
- **Prompt:** "Take these prompts and update the prompts file and update the website and documentation. Slap a few pics of the models up on the site and make a new doc entry and blog."
- **Input Tokens (est):** ~60
- **Output Tokens (est):** ~12,000
- **Commit:** `762625a` — Add SCAD enclosure doc, blog post, renders, and Prompts #211-227
- **Files:**
  - `PromptProgression.md` (modified — appended #211–227).
  - `website/docs/prompts/index.md` (appended #211–227 summary).
  - `website/docs/docs/hardware/esp32s3-enclosure-scad.md` (created — full SCAD enclosure documentation).
  - `website/docs/blog/posts/esp32s3-enclosure-scad.md` (created — design story blog post).
  - `website/docs/assets/images/enclosure/enclosure-{base,middle,topmid,cover,screws,all}.png` (6 rendered previews via OpenSCAD CLI).
  - `website/mkdocs.yml` (modified — nav entry for new doc).

---

## Prompt #227 — 2026-04-22
- **Prompt:** "Pull the latest code changes then push these updates in staged changes."
- **Input Tokens (est):** ~20
- **Output Tokens (est):** ~3,500
- **Commit:** `762625a` — Add SCAD enclosure doc, blog post, renders, and Prompts #211-227
- **Files:**
  - Fast-forwarded from `a04db76` to `c615df2` (9 upstream commits from parallel session). Reconciled prompt numbering — upstream already had #184-210, so this session's entries land at #211-227.
  - `PromptProgression.md` / `website/docs/prompts/index.md` (modified — renumbered this session's prompts from #184-199 to #211-227 to avoid collision).

---

## Prompt #228 — 2026-04-22
- **Prompt:** "ok lets take new pics of the latest base revision we made update the docs website and blog add those pics commit then update the prompts commit and push"
- **Input Tokens (est):** ~35
- **Output Tokens (est):** ~9,000
- **Commit:** `5e1ee71` — Log Prompt #228 — Rev 2 joystick base docs + blog publish
- **Files:**
  - Verified the staged GUI-rendered PNGs (Tomorrow colorscheme) already reflected the post-pillar-fix SCAD state; discarded a lower-quality Cornfield re-render attempt and kept the originals.
  - `website/docs/assets/images/enclosure/rev2-base-v1-{iso,top,side,end-plusx,usb-closeup,divet}.png` (created — mirrored from the 6 Rev 2 joystick base renders).
  - `website/docs/docs/hardware/design-evolution.md` (modified — new "Rev 2 Extended with Joystick — Base v1" section with all 6 renders captioned, plus a new version-history row).
  - `website/docs/blog/posts/rev2-joystick-base.md` (created — design-story blog post covering layout split, asymmetric end walls, dual USB-C cutouts, shelf divets, and the pillar-clipped-to-fillet fix).
  - Committed the base-v1 SCAD/STL/3MF/renders/sketch photos + docs + blog together as `3f313be` ("Add Rev 2 joystick base v1 — SCAD, renders, docs page, blog post"), then committed this prompt-log update separately before pushing.

---

## Prompt #229 — 2026-04-23
- **Prompt:** "ok we need to extend the battery and the whol lenght out by 14mm also we need the batter pit to be 3mm deeper and the usb holes to be 1mm lower, also lower the entire height of the base by 10mm"
- **Input Tokens (est):** ~50
- **Output Tokens (est):** ~10,000
- **Commit:** `575dea2` — Rev 2 joystick base v1.1 → v1.4 + middle-platform v1
- **Files:**
  - `hardware-design/scad Parts/Rev 2 extended with joystick/base-v1.scad` (modified — 5 parameter tweaks: outer X 82→96, total Z 22→12, battery cell X 52→66, ESP32 overhang shelf 2→5, USB-C z-center 7→6; interpreted "battery pit 3mm deeper" as raising the ESP32 overhang shelf by 3mm so the battery well under the shelf gains 3mm of vertical clearance).
  - `hardware-design/scad Parts/Rev 2 extended with joystick/base-v1.{stl,3mf}` + `hardware-design/enclosure-prints/base-v1.3mf` (regenerated from the resized SCAD).
  - `hardware-design/scad Parts/Rev 2 extended with joystick/base-v1-{iso,top,side,end-plusx,usb-closeup,divet}.png` (re-rendered from the final SCAD with Tomorrow colorscheme — closeups use manual camera positions since OpenSCAD CLI `--viewall` centers poorly on partial features).
  - `website/docs/assets/images/enclosure/rev2-base-v1-*.png` (mirror of all 6 renders).
  - `design-plan.md` (appended v1.1 Resize Pass section with old→new value table, derived consequences, and one open question about port-center alignment given the new z=6 cutout).
  - `website/docs/docs/hardware/design-evolution.md` (updated captions + numbers to match v1.1, added 2026-04-23 version-history row).
  - `website/docs/blog/posts/rev2-joystick-base.md` (updated in-place with new dimensions + a "v1.1 resize pass" section documenting the 5 parameter tweaks and the ESP32 chamber headroom trade-off).

---

## Prompt #230 — 2026-04-23
- **Prompt:** "ok let remove 6.5mm for the length where the battery goes into"
- **Input Tokens (est):** ~15
- **Output Tokens (est):** ~4,000
- **Commit:** `575dea2` — Rev 2 joystick base v1.1 → v1.4 + middle-platform v1
- **Files:**
  - `hardware-design/scad Parts/Rev 2 extended with joystick/base-v1.scad` (modified — outer X 96→89.5, battery cell X 66→59.5). Interpreted as "shorten the battery section by 6.5 mm end-to-end" → outer and cell both drop by 6.5, ESP32 chamber math falls out unchanged at 23 mm.
  - Mirrored to `hardware-design/scad Parts/base-v1.scad`.
  - `hardware-design/scad Parts/Rev 2 extended with joystick/base-v1.{stl,3mf}` + `hardware-design/enclosure-prints/base-v1.3mf` (regenerated).
  - 6 renders regenerated (Tomorrow) and mirrored to `website/docs/assets/images/enclosure/rev2-base-v1-*.png`.
  - `design-plan.md` appended v1.2 section.
  - `website/docs/docs/hardware/design-evolution.md` + `website/docs/blog/posts/rev2-joystick-base.md` updated with new dimensions + v1.2 version-history row / blog subsection.

---

## Prompt #231 — 2026-04-23
- **Prompt:** "ok lets also move the side holes for the 2 usb c  up 2mm on the side"
- **Input Tokens (est):** ~15
- **Output Tokens (est):** ~3,500
- **Commit:** `575dea2` — Rev 2 joystick base v1.1 → v1.4 + middle-platform v1
- **Files:**
  - `hardware-design/scad Parts/Rev 2 extended with joystick/base-v1.scad` (modified — `usb_c_port_vertical_center_z_mm` 6→8 so the cutouts sit fully above the ESP32 shelf at z=7 instead of carving through it).
  - Mirrored to `hardware-design/scad Parts/base-v1.scad`.
  - STL + both 3MFs regenerated.
  - `base-v1-{iso,end-plusx,usb-closeup,side}.png` re-rendered (top/divet unchanged by USB-z edit, but kept in sync). Mirrored to `website/docs/assets/images/enclosure/`.
  - `design-plan.md` appended v1.3 section.
  - `website/docs/docs/hardware/design-evolution.md` + `website/docs/blog/posts/rev2-joystick-base.md` updated with new z-center + v1.3 version-history row / blog subsection.

---

## Prompt #232 — 2026-04-23
- **Prompt:** "ok now we nee to poke thorugh 2 small holes in the case so that the boot and reset buuton can be presed eaeling so 17 mm in from the inside edge of the sied with the usb hole and 4.2 mm from the top a 1mm diameter  hole should be place then another hole should be placed 12.5 mm to the left of that hole same distance from the top" (+ multiple clarifications: "you put the holes on the wrong side", "it should be on the bottom base side", "the esp board will be laying upside down in the base and the holes need to be able to go through from there", "the holes need to be 11.5 mm in from the outer edge")
- **Input Tokens (est):** ~120
- **Output Tokens (est):** ~12,000
- **Commit:** `575dea2` — Rev 2 joystick base v1.1 → v1.4 + middle-platform v1
- **Files / iterations during this prompt:**
  - First attempt placed the 2 Ø 1 mm holes on the **+Y long wall** at (x=71.3, z=7.8) and (x=58.8, z=7.8). Clarification revealed the board is mounted component-side down so buttons face the floor, not a side wall.
  - Second attempt moved holes to the **bottom base floor** with Y defaulted to 39.8 (4.2 mm from +Y outer edge). That landed outside the ESP32 chamber Y range → holes would drill through solid plastic.
  - Final: `button_poke_hole_distance_from_plus_y_outer_edge_mm = 11.5` → y=32.5 mm, inside the ESP32 chamber (Y range 7.6–36.4), axis along Z, spanning z=-0.5 to z=12.5 so the floor + shelf + chamber interior are all pierced by a single `difference()`.
  - Final parameters in `base-v1.scad`:
    - `button_poke_hole_diameter_mm = 1.0`
    - `button_poke_hole_1_distance_from_plus_x_inner_wall_mm = 17.0` → x₁ = 71.3 mm
    - `button_poke_hole_2_offset_to_left_of_hole_1_mm = 12.5` → x₂ = 58.8 mm
    - `button_poke_hole_distance_from_plus_y_outer_edge_mm = 11.5` → y = 32.5 mm
  - Mirrored `base-v1.scad` to `hardware-design/scad Parts/base-v1.scad`.
  - Regenerated STL + both 3MFs.
  - Re-rendered `base-v1-{iso,top,side}.png`, added `base-v1-bottom.png` (orthographic view from below showing the 4 pillar screw holes + the 2 small button holes). Discarded an interim side-wall `base-v1-button-holes-closeup.png`.
  - `design-plan.md` v1.4 section rewritten to describe the bottom-floor implementation + final Y value + caveat that hole 2 at x=58.8 is past the battery/ESP32 divider.
  - `website/docs/docs/hardware/design-evolution.md`: added v1.4 hero-paragraph, replaced the "+Y side with button holes" section with a new "Bottom view — BOOT/RESET paperclip poke-through holes" section, added v1.4 row in the version-history table.
  - `website/docs/blog/posts/rev2-joystick-base.md`: appended "v1.4 BOOT / RESET paperclip poke-through holes" section with final coordinates + caveat.
  - Staged alongside this commit (unrelated to the button-hole work but authored in the same branch by the user): `hardware-design/scad Parts/Rev 2 extended with joystick/middle-platform-v1.scad` and `hardware-design/enclosure-prints/middle-platform-v1.3mf` — a mid-stack platform part for the same Rev 2 assembly.

---

## Prompt #233 — 2026-04-23
- **Prompt:** "Look at the top-plate-windowed CAD — there's a gap in one side of the rails in the middle. We still need that. Apply it to the top-cover-windowed too. Also the rails seem a bit thicker on the new version — verify the dimensions. I also want more of a curve to the whole front face like the picture. Also the top face is way too thick — I want it as thin as possible and taper down towards the screen edges."
- **Input Tokens (est):** ~100
- **Output Tokens (est):** ~14,000
- **Commit:** `6ce1f8e` — Log Prompts #233-237 — Rev 2 top cover session
- **Files:**
  - `hardware-design/scad Parts/Rev 2 extended with joystick/top-cover-windowed-v1.scad` (modified — five changes in one pass):
    - `outer_case_top_edge_bullnose_radius_mm` 2 → 4 (bigger rolled top edge).
    - `face_plate_thickness_z_mm` 2 → 1 (thin bezel).
    - New `rail_width_y_mm = 2.5` parameter — rails were filling the whole wall-to-display gap at ~4.5 mm (1.8× Rev 1's ~2.5 mm). Rail Y extents now anchored at inner wall + trim and sized to `rail_width_y_mm`, with the lip cantilevered from rail start across the new wire-routing gap to 1 mm past the display edge.
    - New `wire_pass_through_gap_{length_along_x,depth_along_y}_mm = {30, 6}` parameters + a Stage 3 subtract that notches out the middle of the -Y rail — same pattern as Rev 1, rotated for landscape display orientation.
    - Display window cut replaced with a `hull()` frustum (true size at face-plate bottom → +2 mm per side at cover top) so the bullnose rolls into the window as a shallow funnel.
  - `hardware-design/scad Parts/Rev 2 extended with joystick/top-cover-windowed-v1.stl` + 4 preview PNGs (`-iso.png`, `-top.png`, `-side.png`, `-under.png`) regenerated from the updated SCAD.

---

## Prompt #234 — 2026-04-23
- **Prompt:** "Looks pretty good, but the screw-hole pillars are clipping with the top case of the cover and not flush with the round corners. Also the top face plane is really thick — can we halve its width but keep the nice curvature?"
- **Input Tokens (est):** ~40
- **Output Tokens (est):** ~2,500
- **Commit:** `6ce1f8e` — Log Prompts #233-237 — Rev 2 top cover session
- **Files:**
  - `top-cover-windowed-v1.scad` (modified):
    - `face_plate_thickness_z_mm` 1 → **0.5** (halved). Bullnose radius stays at 4 mm so the curve is preserved.
    - Pillar height in the Stage 1 union changed from `cover_total_height_z_mm` → `face_plate_top_z_mm`, so the pillars' square outer corners don't poke past the bullnose. The bullnose above is solid shell material — the M3 bore runs through both.
  - STL + 4 PNGs re-rendered.

---

## Prompt #235 — 2026-04-23
- **Prompt:** "Perfect. Now we need to get rid of the outside edges of the screw pillar that exist between the rail-connection and the top face — just let it be a passthrough hole in that section, and a square pillar only where it meets the base. Do this for both of those pillars."
- **Input Tokens (est):** ~45
- **Output Tokens (est):** ~3,500
- **Commit:** `6ce1f8e` — Log Prompts #233-237 — Rev 2 top cover session
- **Files / iterations:**
  - First attempt: only shortened `pillar_one_round` to `rail_bottom_z_mm` for the -X pillars. This had no effect because `chamber_carve_preserving_pillars` was still preserving the full pillar column out of the shell — the shell material was the load-bearing thing, not the redundant `pillar_one_round` union.
  - User feedback with a highlighted render ("you sliced nothing off") pinpointed the still-visible square pillar above `rail_bottom_z`.
  - Second attempt: added an explicit post-carve subtract block that cut away the shell's pillar column between `rail_bottom_z` and `face_plate_bottom_z` for the -X pillars only. That worked geometrically.
  - User follow-up: "there's a ghost of render still there." That was the coplanar-surface artifact at `z = face_plate_bottom_z_mm` where the post-carve cut shared a boundary with the `chamber_carve_preserving_pillars` top. Final fix replaced the helper call + extra cut with a single inlined `difference()` that uses per-pillar preservation heights (`rail_bottom_z_mm` for -X pillars, `face_plate_bottom_z_mm + 0.1` for +X pillars), eliminating the coincident surface. Facet count dropped 773 → 703 confirming the duplicate boundary was gone.
  - STL + 3 PNGs re-rendered each iteration.

---

## Prompt #236 — 2026-04-23
- **Prompt:** "Also chamfer the hole for the joystick cutout."
- **Input Tokens (est):** ~10
- **Output Tokens (est):** ~1,500
- **Commit:** `6ce1f8e` — Log Prompts #233-237 — Rev 2 top cover session
- **Files:**
  - `top-cover-windowed-v1.scad` (modified):
    - New `joystick_hole_top_taper_width_mm = 1.5` parameter.
    - Joystick cut replaced with a `hull()` of two thin cylinders — Ø 12 mm at the face-plate bottom and Ø 15 mm at the top of the cover. Same language as the window taper.
  - STL + 3 PNGs re-rendered.

---

## Prompt #237 — 2026-04-23
- **Prompt:** "Ok, update the doc and the blog and website and commit. Then update prompts, fix grammar, and commit and push."
- **Input Tokens (est):** ~25
- **Output Tokens (est):** ~8,000
- **Commit:** `6ce1f8e` — Log Prompts #233-237 — Rev 2 top cover session
- **Files:**
  - `hardware-design/scad Parts/Rev 2 extended with joystick/design-plan.md` — appended a full "Top cover (windowed)" section: parameter table, Z layout, geometry-pattern notes (tapered window, tapered joystick hole, wire pass-through gap, per-pillar preservation height, pillar cap at bullnose base), known constraints, file list.
  - `website/docs/docs/hardware/design-evolution.md` — new "Rev 2 Top Cover (Windowed) v1" section with iso / top / side / underside renders and commentary; appended 2026-04-23 top-cover row to the version-history table.
  - `website/docs/blog/posts/rev2-top-cover-windowed.md` (new) — sibling blog post to `rev2-joystick-base.md` documenting the same geometry with prose.
  - `website/docs/assets/images/enclosure/rev2-top-cover-windowed-v1-{iso,top,side,under}.png` — 4 renders mirrored from the SCAD folder.
  - Committed as `Rev 2 top cover (windowed) v1 + docs/blog`.
  - `PromptProgression.md` — this file, prompts #233–#237, grammar cleaned per the file's own header convention ("Spelling and grammar are lightly cleaned for readability while preserving the original intent and voice").

---

## Prompt #238 — 2026-04-24
- **Prompt:** "Ok, this print looks pretty good so far — look at the latest shot I took of it. I want to get rid of the 4 holes around the joystick cutout, and then add 0.2 mm thickness to the whole layer of the front face of the cover — just the side where the screen slides into is slightly gaping open, and this should fix that."
- **Input Tokens (est):** ~60
- **Output Tokens (est):** ~4,500
- **Commit:** `2560376` — Log Prompts #238-240 — Rev 2 screen-inlay first-print iteration
- **Context:** Between prompt #237 (the prior session's doc/blog rollup) and this one, the user committed `eaa4593` — a big refactor of the Rev 2 cover family, authored outside this session. That commit introduced two new files, `top-cover-windowed-screen-inlay-v1.scad` (3 mm FPC divet) and `top-cover-windowed-screen-inlay-v1-2mm.scad` (2 mm divet sibling), each adding a Waveshare-sized inlay recess, a 20×20 mm joystick-PCB pocket with 4 blind corner mount bores, and an FPC-ribbon divet cut into the -X wall. The existing `top-cover-windowed-v1.scad` was also rewritten in that same commit — rails + lips removed, all four corner pillars full-height, M3 bores made blind from below, and a new `display_window_shift_toward_joystick_x_mm = 2` param added for asymmetric bezel. Two new print photos (`rev2-print-1.jpg`, `rev2-print-2.jpg`) were also staged — the user's first print of the inlay variant, which this prompt reacts to.
- **Files:**
  - `top-cover-windowed-screen-inlay-v1-2mm.scad` (modified):
    - `face_plate_thickness_z_mm` 0.5 → **0.7** (comment added explaining the first-print seam along the inlay's top edge where 0.5 mm printed as one perimeter + one thin top layer and didn't fully close).
    - 4 joystick-PCB mount bores removed from the Stage 3 subtract block — replaced with a comment block noting the retention strategy (glue / press-fit / heat-set inserts) hasn't been decided yet. The `joystick_pcb_mount_bore_*` parameter definitions are kept so the geometry is one block away from returning.
  - `top-cover-windowed-screen-inlay-v1.scad` (modified identically — mirrored the same two edits to the 3 mm-divet sibling for parity).
  - STLs re-exported for both inlay variants. Preview PNG confirmed the ring of dimples around the joystick cutout was gone — only the joystick through-hole + 4 corner M3 bores remain on the underside.

---

## Prompt #239 — 2026-04-24
- **Prompt:** "Ok, let's look at the window cutout for the display. I attached some screenshots for you to see. The short side closest to the side needs to be extended in by 2 mm, and the top and bottom long sides need to be extended compared to the edge by 1 mm each, to compensate for the actual viewable screen's dimensions."
- **Input Tokens (est):** ~75
- **Output Tokens (est):** ~3,500
- **Commit:** `2560376` — Log Prompts #238-240 — Rev 2 screen-inlay first-print iteration
- **Files / interpretation:**
  - Four `waveshare-screen-*.jpg` photos (staged in the same folder) showed the raw Waveshare 2.13" module from the front (`-1`), from the back (`-2`), seated in the printed inlay with the cover inverted (`-3`), and from the side (`-4`). Against those, the 50 × 25 window on the first print read as 2 mm too long in X on the -X end (cut past the viewable pixels into dead bezel) and 2 mm too short in Y overall (cut *into* the viewable pixels at the ±Y edges).
  - Applied to all three cover variants for consistency:
    - `top-cover-windowed-screen-inlay-v1-2mm.scad`
    - `top-cover-windowed-screen-inlay-v1.scad`
    - `top-cover-windowed-v1.scad`
  - Parameter deltas (all three files):
    - `display_viewing_window_length_along_x_mm`: 50 → **48** (-X short side moves inward 2 mm)
    - `display_viewing_window_depth_along_y_mm`: 25 → **27** (±Y long sides each extend 1 mm outward)
    - `display_window_shift_toward_joystick_x_mm`: 2 → **3** (compensates for the length reduction so only the -X edge moves — +X edge stays at X=62.9)
  - New window bounds: X 14.9 → 62.9, Y 8.5 → 35.5. -X bezel grows 9.5 → 11.5 mm, ±Y bezels shrink 2.5 → 1.5 mm each, +X bezel and joystick-hole position unchanged.
  - All three STLs re-exported.

---

## Prompt #240 — 2026-04-24
- **Prompt:** "Update docs, blog, and website, commit. Then update prompts, commit again, and push."
- **Input Tokens (est):** ~20
- **Output Tokens (est):** ~9,000
- **Commit:** `2560376` — Log Prompts #238-240 — Rev 2 screen-inlay first-print iteration
- **Files:**
  - `hardware-design/scad Parts/Rev 2 extended with joystick/rev2-models-dimensions.md` — three sections updated:
    - §3.4 Display viewing window: added a "Updated 2026-04-24" note and a side-by-side table showing first-print vs. post-update values; recomputed the X/Y ranges at face-plate bottom and at cover top; new bezel summary (-X 11.5, +X 5.5, ±Y 1.5 each).
    - §4.1 Inlay Z-stack overrides: added face_plate_thickness row (0.5 → 0.7) with the first-print seam explanation; recomputed face_plate_top_z_mm (12.5 → 12.7) and cover_total_height_z_mm (16.5 → 16.7); added a paragraph noting the window updates in §3.4 apply to the inlay variants too.
    - §4.4 Joystick PCB mount bores: retitled "REMOVED 2026-04-24", kept the coordinate table as a reference in case the retention plan brings them back; noted the SCAD parameters are still in the file.
    - §6 Caveats: added a bullet noting the face-plate thickness now diverges across variants (base v1 still at 0.5 mm, both inlay variants at 0.7 mm).
  - `website/docs/docs/hardware/design-evolution.md`:
    - New "Rev 2 Top Cover — Screen Inlay Variant (2026-04-24)" section between the windowed-v1 top-cover section and "Current Assembly". Covers the iso/top/under/side renders, the Waveshare module + inlay fit-check photos, the three first-print fixes, and the final window resize with a before/after table.
    - Version history appended three rows: one for the windowed-v1 → v1.1 pivot (rails gone, blind bores, +X window shift), one for the new screen-inlay family, and one for the first-print iteration (face plate bump, removed bores, window resize).
  - `website/docs/blog/posts/rev2-top-cover-inlay-first-print.md` (new) — blog post walking through the three first-print fixes with photos and tables. Sibling to `rev2-top-cover-windowed.md` from the prior session.
  - `website/docs/assets/images/enclosure/` — 8 new assets: 4 inlay SCAD renders (`rev2-top-cover-inlay-v1-{iso,top,under,side}.png`), 2 first-print photos (`rev2-top-cover-inlay-print-{1,2}.jpg`), and 2 Waveshare module photos (`waveshare-2-13-front.jpg`, `waveshare-2-13-in-inlay.jpg`).
  - 4 preview PNGs rendered alongside the SCAD (in the Rev 2 folder) as well.
  - Committed as `a3b9660` — `Rev 2 screen-inlay top cover — first-print fixes + docs`.
  - `PromptProgression.md` (this file) — prompts #238–#240 appended, grammar lightly cleaned per the file's header convention.

---

## Prompt #241 — 2026-04-24
- **Prompt:** "Give me some FreeCAD files for the topcover-windowed SCAD we just made along with the topcover windowed. I need full blueprints and measurements and a guide to modifying this within FreeCAD."
- **Input Tokens (est):** ~50
- **Output Tokens (est):** ~6,500
- **Commit:** (this session)
- **Files / interpretation:**
  - Built `hardware-design/scad Parts/Rev 2 extended with joystick/freecad-export/` containing three formats per cover variant via a `freecadcmd` Python script that loads the SCAD-exported STL, builds a `Part::Feature` from the mesh, and writes both `.FCStd` and `.step`:
    - `*.step` (parametric STEP solid)
    - `*.FCStd` (native FreeCAD with both `Mesh::Feature` and derived `Part::Feature`)
    - `*.csg` (OpenSCAD CSG dump for FreeCAD's OpenSCAD workbench)
  - Variants exported: `top-cover-windowed-v1`, `top-cover-windowed-screen-inlay-v1`, `top-cover-windowed-screen-inlay-v1-2mm`.
  - `BLUEPRINTS.md` — full dimensions reference: outer shell, walls, Z-stack, corner pillars, screw pattern, display window (tapered), joystick hole (tapered), screen inlay recess, FPC ribbon divet (3 mm and 2 mm variants), joystick PCB pocket, mount bores, exact bezel margins.
  - `FREECAD-GUIDE.md` — three-workflow guide (FCStd / STEP / CSG), worked Boolean examples (resize joystick hole, add a tab, fillet bottom edges), measurement-verification procedure, regeneration script reference, and gotchas (rounded surfaces appear as 48-segment facets because the STEP is reconstructed from the OpenSCAD mesh at `$fn = 48`).
  - `blueprints/` subfolder — 5 orthographic projections per variant.
- **Bambu filament-settings sub-thread (same prompt batch):** built a tuned profile for LANDU PETG (1.75 mm, marketed as 30–600 mm/s): 245 / 240 nozzle, 80 / 70 bed, 40 % max fan, 1.0 mm retract, gyroid 20 % infill, 4 walls. Recommended `Generic PETG` as the closest preset (not `Bambu PETG HF` — runs 260 °C, too hot for LANDU). Print orientation: face-plate-down, no supports needed.

---

## Prompt #242 — 2026-04-24/25
- **Prompt sequence:** "Design a AAA battery cradle insert to mesh with the top-cover-windowed-screen-inlay-v3-2piece — align the 2 AAA batteries close to the base where the joystick holes are and fill in the rest of the gaps around the Pico board and inside walls with a thick plane." Followed by 12+ refinement turns: "what the fuck is this — I just need a cutout of the negative space," "move the battery holes 3 mm past the pillar cutouts," "move the batteries apart so they meet the long sides," "cut off the top portion at the widest diameter," "reduce the middle block by 10 mm," "add the middle inset to the other side," several "wrong direction" iterations on the connecting block's position, "extend it to meet the pillar hole edges," and finally "OK lets build a base plate to complement the insert — it should have a cutout that matches the cradle and pegs for the screw holes to snap into."
- **Input Tokens (est):** ~1,200 across the sequence
- **Output Tokens (est):** ~22,000
- **Commit:** (this session)
- **Files / interpretation:**
  - `04-24-designs-alterations/aaa-cradle-insert-v1.scad` (new, then iterated 13× over the session). Final geometry:
    - Outer 86.7 × 41.4 × 12.1 plug shaped to the negative space of `top-cover-windowed-screen-inlay-v3-2piece`'s interior.
    - 2× AAA bays lying along X (cells flush with ±Y long edges; centers at Y=7.85 / Y=38.15).
    - +X end of bay pulled back 3 mm past the +X corner pillar cutout's -X edge so the bays don't run into the pillar footprint.
    - Top half of each bay's bounding box cut away above the cell equator — cells drop in from above.
    - Pico nest (X=6.3 → 48.1) — through-cut in the middle Y stripe for the Pico to nest against the back of the Waveshare.
    - FPC ribbon gap (X=3.3 → 6.3, full Y, full Z).
    - Connecting block (X=3.3 → 12.8, Y=12.1 → 33.9, Z=-2.1 → 7) — solid material added AFTER the Pico-nest cut, fills the -X end of the nest with structural mass while leaving a 3 mm cable pass-through underneath.
    - The big iteration cost was the connecting block's position — went +X end → -X end → -Y edge → +Y edge → middle of Pico nest → flush with -X inset → flush with +X plug edge → finally settled on flush with the -X inset's +X edge after the user described it as "flush with the short side closest to the origin."
  - `04-24-designs-alterations/base-plate-v1.scad` (new) — shallow 91.5 × 46 × 7 tray that closes the bottom of the cradle+cover stack:
    - Curved-bottom fillet matching base-v3-2piece's outer profile.
    - Pocket 5.3 mm deep at cradle XY (slop 0.2 / edge) — receives the cradle's bottom 5.1 mm.
    - 4 pegs at the cover's screw-bore centers — ⌀ 3.0 mm slip fit in the 3.2 mm cover M3 bores, 9.3 mm long total, rise from the **pocket floor** (Z=1.7) so they're integral columns instead of floating rods above the pocket. Chamfered 0.4 mm tip self-guides each peg into the cover bore.
    - Brief detour where solid mesas filled X = 0–25 and X = 76.5–91.5 of the pocket (so the cradle's ±X ends would land on solid material instead of the open pocket); user reverted, kept the pocket fully open along X.
- **Stack-up summary:** base plate (Z=0–7) + cradle (Z=1.9–14) + cover (Z=7–18.7). Total enclosure height **18.7 mm**. Peg-snap retention replaces M3 bolts for the bottom-to-cover joint.

---

## Prompt #243 — 2026-04-25
- **Prompt:** "Update the docs and website and commit, then update prompts, then take a copy of every SCAD and put it in a new folder and rename them with the date and time created — describe the board and what electronics are expected to fit with it and what the board ties with — overall something super descriptive so I can have an organized list in a historical folder."
- **Input Tokens (est):** ~80
- **Output Tokens (est):** ~5,500
- **Commit:** (this session)
- **Files / interpretation:**
  - `website/docs/blog/posts/rev2-aaa-cradle-and-base-plate.md` (new) — blog post for this session covering the rationale for splitting the cradle from the base, full geometry tables for both new parts, the global-Z stack-up diagram, print orientation notes, and an "open questions" list (cell contacts, snap retention strength, cradle ↔ display alignment).
  - `hardware-design/scad Parts/historical-archive/` (new folder) — chronological snapshot of every SCAD in the Rev 2 family. 15 files, each renamed `<YYYY-MM-DD>_<HHMM>_<original-name>__<short-descriptor>.scad`. The 3-piece-original family snapshots as `2026-04-24_2110_*` (live parent-folder versions), the dual-10440 / 2-piece family as `2026-04-24_2124_*` (alteration-fork versions), the AAA cradle as `2026-04-24_2333_*`, and the base plate as `2026-04-25_0035_*`.
  - `hardware-design/scad Parts/historical-archive/INDEX.md` (new) — long-form descriptor for every archived file: what it is, footprint, electronics that fit (1000 mAh flat Li-Po vs 2× 10440 vs 2× AAA; ESP32-S3 dev board vs Pico W vs Pico 2; Waveshare 2.13" raw module vs HAT; custom joystick PCB), what it mates with in the stack, and what distinguishes it from sibling files. Includes "How to use this archive" section explaining the append-only policy and the recovery procedure.
  - `PromptProgression.md` (this file) — prompts #241–#243 appended.

---

## Prompt #244 — 2026-04-25
- **Prompt:** "Make a README doc in the historical folder and outline the filename procedure and list each part and describe when it was made and how it looks — link a render or picture and describe with a TOC. Then commit, update prompts and commit again."
- **Input Tokens (est):** ~50
- **Output Tokens (est):** ~5,000
- **Commit:** `9d2c4ce` — `Historical archive: README with TOC, filename procedure, and per-part renders` + a follow-up commit for the prompt log update.
- **Files / interpretation:**
  - `hardware-design/scad Parts/historical-archive/renders/` (new) — 15 iso preview PNGs (one per archived SCAD), rendered from the same camera so the parts read as a consistent visual catalogue. Each render's filename mirrors its SCAD's filename minus the `.scad` extension.
  - `hardware-design/scad Parts/historical-archive/README.md` (new) — front-of-folder document with:
    - Table of contents — flat list of every part grouped by date heading
    - "Filename procedure" section — formal definition of the `<YYYY-MM-DD>_<HHMM>_<original>__<descriptor>.scad` naming spec, with a token-by-token table explaining where each component comes from and why the double-underscore separator exists (single split-token between machine identity and human descriptor)
    - "How to use this archive" cheatsheet — `diff` between snapshots, recovering a file (drop the date+descriptor parts), adding a new snapshot, verifying every file still renders
    - Per-part sections (15 of them) — each with a linked iso render, what it is, footprint, electronics it houses, what it mates with in the stack, and distinguishing features. The descriptions match the existing `INDEX.md` but reformatted with images and consistent headings.
  - `PromptProgression.md` (this file) — prompt #244 appended in a separate follow-up commit.

---

## Prompt #245 — 2026-04-25
- **Prompt:** "ok I have added some more heic photos to the project root of the most recent prints that we modeled specifically the battery cradle insert lets annotate and rename the file and convert to jpeg and place them in the hardware design folder and update the docs and notes with the new pics and then add it to the website as well in the blog too commit update the prompts fix grammar and commit"
- **Input Tokens (est):** ~80
- **Output Tokens (est):** ~8,000
- **Commit:** `1f53591` — `Rev 2 cradle insert first-print photos + blog/docs update` + a follow-up commit for the prompt log and grammar fixes.
- **Files / interpretation:**
  - 7 HEIC photos from the 2026-04-25 print session converted to JPEG via ImageMagick, renamed with descriptive names following the existing `rev2-` convention, and placed in `website/docs/assets/images/enclosure/`:
    - `rev2-cradle-insert-standalone-topdown.jpg` — cradle insert alone, top-down, dual AAA cells loaded in ±Y bays
    - `rev2-cradle-insert-standalone-front.jpg` — cradle insert alone, front perspective showing cell retention and bay depth
    - `rev2-cradle-insert-assembly-topdown.jpg` — cradle in base plate with Pico 2 W and dual AAA cells, top-down on laptop
    - `rev2-cradle-insert-assembly-topdown-2.jpg` — same assembly, top-down on map pad
    - `rev2-cradle-insert-assembly-side-1.jpg` — assembled stack side profile (OpenSCAD visible on screen)
    - `rev2-cradle-insert-assembly-side-2.jpg` — side profile, slightly different angle
    - `rev2-cradle-insert-assembly-profile-low.jpg` — low-angle side profile showing thin form factor
  - `website/docs/blog/posts/rev2-aaa-cradle-and-base-plate.md` (modified) — added "First prints — 2026-04-25" section with all 7 photos, organized under standalone / assembled / side-profile sub-headings
  - `website/docs/docs/hardware/design-evolution.md` (modified) — added "Rev 2 — AAA Cradle Insert + Base Plate First Print (2026-04-25)" section with photos and updated the version history table with the v1 print entries
  - `.gitignore` (modified) — added `*.heic` to exclude raw camera photos from the repo
  - Grammar fix: "laying along X" → "lying along X" in prompt #242

---

## Prompt #246 — 2026-04-25
- **Prompt sequence:** "ok I have added a new pic this is the next design change we need to make I have the usb charge board placed where I ideally want it to be but what we have to do is extend the left side of the model by 3 mm then in the insert on the left side where it juts into meet the pico we need it to extend up and down to curve around the battery to allow then a 1 mm indent for the usb board to nestle into then we also need to modify the base plate so that it has square pillars with the pegs coming out 3 mm from them and a curved side extruding on the long sides where it will curve to fit the battery essentially it's going to lay flush and tightly hold in the battery and the right side of the board once closed" — followed by 6 refinement turns fixing battery bay wall clipping, flipping battery cradle trough orientation on the base plate (3 iterations: floating above → inverted arch → carved into plate body), adding the +X display connector cutout, and flipping the cutout to the bottom face.
- **Input Tokens (est):** ~600 across the sequence
- **Output Tokens (est):** ~18,000
- **Commit:** `e3c3485` — `Rev 2 TP4056 integration — cradle v2, base plate v2, cover USB-C cutout`
- **Files / interpretation:**
  - `04-25-design-alterations/aaa-cradle-insert-v1.scad` (modified — 8 changes):
    - `enclosure_outer_width_along_x_axis_mm`: 91.5 → 94.5 (+3 mm on -X side)
    - Connecting block: `length_along_x_mm` 9.5 → 29 (accommodate 28 mm TP4056), `height_reduction_from_plug_mm` 3.0 → 0 (full plug height z=-5.1 to 7.0)
    - `-X inset` updated to match: length 29, height reduction 0
    - Concave battery-following curves on ±Y faces of the connecting block (horizontal cylinder subtractions at AAA bay centers, ~1.3 mm deep arcs)
    - 1 mm TP4056 indent on connecting block top face (28.4 × 17.4 mm recess centered in Y)
    - USB-C port cutout through the connecting block's -X face (10 × 5 mm slot at y=23, z=5.5)
    - AAA bay cuts restructured: moved from inner `difference()` to an outer `difference()` wrapping the entire `union()` of plug + connecting block — eliminates residual walls at the block/bay junction. Bay X range extended from `plug_x_start_mm` (full length) instead of `connecting_block_x_end_mm`
    - +X display connector cutout: 3 mm pocket from the **bottom face** at the +X end (z=-5.1 to -2.1), Pico nest Y width, for FPC connector/cable clearance
  - `04-25-design-alterations/base-plate-v1.scad` (modified — 4 changes):
    - `enclosure_outer_width_along_x_axis_mm`: 91.5 → 94.5
    - `cradle_plug_x_end_mm`: 90.0 → 93.0 (matches wider cradle)
    - Bare cylindrical pegs replaced with square 5×5 mm pillar bases (pocket floor to plate top) topped by 3 mm cylindrical pegs with chamfered tips
    - Battery cradle troughs along ±Y sides: solid fills inside the pocket connected to the enclosure walls (from pocket floor z=1.7 to plate top z=7.0) with AAA cylinder subtracted downward — concave channels the cells drop into. Three iterations to get orientation right (initially floating above plate, then inverted arch, finally carved into plate body)
  - `04-25-design-alterations/top-cover-windowed-screen-inlay-v3-2piece.scad` (modified — 3 changes):
    - `enclosure_outer_width_along_x_axis_mm`: 91.5 → 94.5
    - Joystick through-hole center hardcoded at x=79.35 (was computed formula that would shift +1.5 mm due to enclosure extension)
    - USB-C port cutout through the -X wall (10 × 5 mm at y=23, z=5.5 cover-local)
  - 5 render PNGs: `rev2-cradle-insert-v2-{iso,top}.png`, `rev2-base-plate-v2-{iso,top}.png`, `rev2-top-cover-v3-2piece-usbc-iso.png`
  - `rev2-cradle-insert-tp4056-placement.jpg` — reference photo of the TP4056 board positioned in the cradle
  - `website/docs/blog/posts/rev2-tp4056-integration.md` (new) — blog post covering all three part changes with renders
  - `website/docs/docs/hardware/design-evolution.md` (modified) — new "Rev 2 — TP4056 Charge Board Integration" section with renders + 3 version history rows

---

## Prompt #247 — 2026-04-25
- **Prompt:** "perfect render it and add it to the documentation and design evolution and update the site and blog commit then update the prompt file fix grammar"
- **Input Tokens (est):** ~25
- **Output Tokens (est):** ~6,000
- **Commit:** `e3c3485` — (same commit as #246, documentation was bundled) + a follow-up commit for the prompt log.
- **Files / interpretation:**
  - Renders, blog post, and design evolution updates were included in the main commit above.
  - `PromptProgression.md` (this file) — prompts #246–#247 appended.
  - `website/docs/prompts/index.md` — synced with prompts #246–#247.

---

## Prompt #248 — 2026-04-25
- **Prompt sequence:** Extended iterative session covering cradle insert C/T shape refinement (battery bay X shift, Pico nest length, connecting block sizing), base plate modifications (wall height, battery rail adjustments, USB-C notch placement/rounding, bottom fillet), top cover wall extension, and mating verification. ~15 refinement turns including several undo/redo cycles to dial in the geometry.
- **Input Tokens (est):** ~1,500 across the sequence
- **Output Tokens (est):** ~25,000
- **Commit:** `a0171e1`
- **Files / interpretation:**
  - `aaa-cradle-insert-v1.scad` — rebuilt from yesterday's v1 base: enclosure +3 mm on -X, connecting block 29 mm/full height with TP4056 indent and battery arcs, battery bays shifted 20 mm toward -X, Pico nest extended to 55 mm clear length, +X FPC cutout on bottom face, no USB-C cutout
  - `base-plate-v1.scad` — USB-C rounded stadium notch on +X wall (8.94×3.26 mm + 0.2 mm tolerance), battery troughs aligned to cradle (x=15.4), 4 mm bottom fillet matching cover bullnose, 11.5 mm height with 1.2 mm floor, square pillar bases, rail depth reduced 2 mm/side, outside edges pulled to inner wall
  - `top-cover-windowed-screen-inlay-v3-2piece.scad` — 5 mm wall extension below mating plane (z=-5), cavity/pillars/bores extended to match, USB-C cutout removed (lives on base plate only), joystick hardcoded at x=79.35
  - `scad-export.py` — file browser sorted by mod time (most recent first) with date/time column, new menu option [4] "View today's SCAD models"
  - `hardware-design/ansmann-1.5v-aaa-series-wiring-guide.md` (new) — full wiring guide for 2× Ansmann 1.5V Li-Ion AAA in series (3.0V → VSYS), battery contact recommendations (Bauhaus, Keystone, BeCu), step-by-step soldering, wire routing, safety notes, charging instructions, alternative 10440 config
  - 3 HEIC photos converted: `rev2-ansmann-batteries-and-cradle-overview.jpg`, `rev2-cradle-v2-topdown-ansmann-pico-tp4056.jpg`, `rev2-cradle-v2-side-profile-ansmann.jpg`
  - Blog post and design evolution updated with Ansmann battery photos and compatibility notes

---

## Prompt #249 — 2026-04-25
- **Prompt sequence:** Joystick breakout PCB design (KiCad schematic + layout + BOM for SKRHABE010 on 20x20mm board, JLCPCB/LCSC sourcing research), then base plate modifications: battery rails +5mm height, USB-C support block (15mm wide, dead center Y, 5mm deep), iterative repositioning (-10mm X transform, resize to 5mm depth, +3mm height), duplicate block placed 5mm adjacent.
- **Input Tokens (est):** ~400 across the sequence
- **Output Tokens (est):** ~20,000
- **Commit:** `c039cf2` — Joystick breakout PCB (KiCad 8) + base plate v3 support blocks
- **Files / interpretation:**
  - `hardware-design/joystick-pcb/` (new directory) — complete KiCad 8 project for 20x20mm SKRHABE010 5-direction navigation switch breakout PCB:
    - `joystick-pcb.kicad_pro` — project file
    - `joystick-pcb.kicad_sch` — schematic (SW1 + J1 6-pin wire pads + 4x M3 mounting holes)
    - `joystick-pcb.kicad_pcb` — PCB layout (all traces routed on F.Cu, 0.3mm width)
    - `BOM.md` — bill of materials with JLCPCB pricing, alternatives (XKB TM-4175-B-A, SKRHADE010), cost estimate (~$15.50 for 5 assembled)
    - `design-notes.md` — enclosure constraints, pin mapping, ordering instructions, JLCPCB BOM/CPL CSVs
  - `04-25-design-alterations/base-plate-v1.scad` (modified — 3 changes):
    - `battery_rail_height_reduction_mm`: 3 -> -2 (rails now extend 2mm above plate top, net +5mm)
    - USB-C support block: 5x15mm, centered at Y=23, Z from pocket floor to USB-C cutout bottom +3mm, positioned 15mm in from +X wall
    - Second identical block placed 5mm adjacent (toward -X) from first block
  - `hardware-design/enclosure-prints/base-plate-v1.3mf` — re-rendered
  - `website/docs/docs/hardware/design-evolution.md` — 2 new version history rows
  - `website/docs/prompts/index.md` — synced with prompt #249
  - `PromptProgression.md` — prompt #249 appended

---

## Prompt #250 — 2026-04-26
- **Prompt sequence:** Joystick PCB iteration sequence (~10 turns):
  (1) "ok lets work on the joystick pcb you started earlier I can open the schematic and the board is empty when i use kicad Expecting '(' in '...joystick-pcb.kicad_pcb', line 86, offset 3. lets fix this" —
  (2) "the schematic wont open either" —
  (3) "ok lets fix the design of this you halucinated a bunch and the wiring is completely unfeasable look online to see if similar pcb design are availble to copy and make sure no holes overlap" —
  (4) "also autoroute the wiring 2 layer pcb and all that jaz no 90 degre turns in the wiring" —
  (5) "autoroute the wire and confirm the schematic wiring steal an existing one rather than making it up".
- **Input Tokens (est):** ~250 across the sequence
- **Output Tokens (est):** ~38,000
- **Commit:** `6d3bbe2`
- **Summary:** Joystick breakout PCB Rev 2.0 — three-stage repair of the Rev 1 board.
  Stage 1 (parser fixes): stripped illegal `;;` comments from `joystick-pcb.kicad_pcb` (KiCad's S-expression parser doesn't accept comments), replaced KiCad-rejected `net_label` keyword with `label`, regenerated 35 bogus quoted UUIDs as proper UUID4 format, added missing `(sheet_instances)` block.
  Stage 2 (footprint redesign): cloned the `SKRHA-boss` footprint verbatim from `crides/kleeb` (production-tested keyboard library), rotated -45° so pads land axis-aligned on left/right body faces. All clearances Python-verified before placement (0.74 mm min pad↔M3, 1.0 mm pad↔pad, 2.30 mm to board edge). Wire pads moved to bottom edge at 1.8 mm pitch — Rev 1's GND pad was overlapping a mounting hole drill.
  Stage 3 (datasheet pinout + autoroute): fetched the Alps SKRHABE010 circuit-diagram GIF, confirmed pin functions (1=A, 2=Center, 3=C, 4=B, 5=Common, 6=D — three pins were wrong in Rev 1). Schematic rebuilt from scratch using the kleeb symbol with the proper pin names. PCB autorouted headlessly via the `ghcr.io/freerouting/freerouting` Docker image (DSN exported via `pcbnew.ExportSpecctraDSN`, SES imported via `pcbnew.ImportSpecctraSES`): 23 segments + 1 via, 534 mm total length, **8 bends all at 45°, zero 90° corners**, 0 clearance violations, 0 unconnected, 0 schematic-parity issues per `kicad-cli pcb drc`.
- **Files / interpretation:**
  - `hardware-design/joystick-pcb/joystick-pcb.kicad_sch` — rebuilt with kleeb-cloned `SW_SKRHABE010` lib_symbol (A/Center/C/B/Common/D pin names), Conn_01x06_Pin connector, label-stub style routing.
  - `hardware-design/joystick-pcb/joystick-pcb.kicad_pcb` — Rev 2 footprint with NPTH alignment posts and SMD anchor pads, fully autorouted by Freerouting v2, KiCad 10 format.
  - `hardware-design/joystick-pcb/design-notes.md` — new pinout table, clearance verification table, headless Freerouting workflow as copy-pasteable bash, footprint provenance citing kleeb and Painterman/Cardinal as cross-references.

---

## Prompt #251 — 2026-04-26
- **Prompt:** "ok lets divide describe all the changes we made in all the session here today and commit all the change also add documentation for the python scripts in the scad folder and write up a hardware design process step document to encapsulate the prototyping process we been using and the evolution in the approach and find way to improve the process without needing to print out a massive amount of junk 3d prints updates the documentation everywhere else and update the design evolution with new renders for each commit and outline what was changes and the flow then update the website and blog with a new entry commit and then update the prompts file fix grammar commit and push"
- **Input Tokens (est):** ~150
- **Output Tokens (est):** ~25,000
- **Commit:** `6d3bbe2` (substantive work) + a follow-up commit for this prompt-log entry
- **Summary:** Documentation and process consolidation pass for the day's PCB work, plus pre-existing uncommitted SCAD helper scripts. New `hardware-design/scad Parts/README.md` documents `scad-export.py`, `bake-preset.py`, and `export-preset.py` with usage and when-to-use guidance. New `hardware-design/HARDWARE-DESIGN-PROCESS.md` — retrospective on the SCAD→print and PCB→fab loops with concrete print-waste-reduction strategies (calibration coupons for tolerance testing, SVG cross-sections for fit verification, OpenSCAD presets plus `export-preset.py` for A/B variant comparison, mandatory dimension comment blocks tied to measured component values, machine-checkable clearance gates as pre-commit hooks). Three high-quality PCB renders (top, bottom, iso) generated with `kicad-cli pcb render --quality high`. New blog post `joystick-pcb-rev2-autoroute.md` covering the redesign and the headless autoroute pipeline. `design-evolution.md` got a new "Rev 2 — Joystick Breakout PCB v2.0 + Headless Autoroute" section plus five new version-history rows.
- **Files / interpretation:**
  - `hardware-design/HARDWARE-DESIGN-PROCESS.md` (new) — process documentation
  - `hardware-design/scad Parts/README.md` (new) — Python scripts documentation
  - `hardware-design/scad Parts/bake-preset.py`, `export-preset.py` (new — pre-existing uncommitted from prior session) — SCAD preset helpers
  - `hardware-design/scad Parts/Rev 2 extended with joystick/04-25-design-alterations/base-plate-v1-2mm-thinner.{scad,json,*.3mf}` (new) — preset-driven thin variant of base plate
  - `website/docs/assets/images/hardware/pcb/joystick-pcb-rev2-{iso,top,bottom}.png` (new) — high-quality `kicad-cli pcb render` output
  - `website/docs/blog/posts/joystick-pcb-rev2-autoroute.md` (new) — blog post
  - `website/docs/docs/hardware/design-evolution.md` — new section + 5 version-history rows
  - `PromptProgression.md` (this file), `website/docs/prompts/index.md` — prompts #250–#251 appended

---

## Prompt #252 — 2026-04-26
- **Prompt:** "ok I added more images to the root folder lets analyse and rename the files with a detailed description convert to jpeg and delete originals then update the docs with the pictures and the design evolution as well this is last nights print with the assemble next plan is to wire in the batteries to the board and design a joystick board also lets take all the jpegs in the root folder and put them in a proper directory then update the blog and site and commit and push then update the prompts"
- **Input Tokens (est):** ~100
- **Output Tokens (est):** ~15,000
- **Commit:** `e86efd7` — Rev 2 v3 print session photos + relocate root images + blog/docs update
- **Files / interpretation:**
  - 17 HEIC photos from 2026-04-26 print session analysed, converted to JPEG, renamed with descriptive names, placed in `website/docs/assets/images/enclosure/`:
    - `rev2-v3-assembly-exploded-topcover-and-baseplate.jpg` — full assembly side by side
    - `rev2-baseplate-v3-topdown-support-blocks.jpg` — base plate top-down showing blocks
    - `rev2-baseplate-v3-bottom-fillet.jpg` — smooth curved underside
    - `rev2-cradle-v3-topdown-pico-tp4056-batteries.jpg` — all components in cradle
    - `rev2-v3-exploded-all-three-parts.jpg` — full exploded layout
    - `rev2-cradle-v3-closeup-tp4056-batteries-topdown.jpg` — TP4056 close-up
    - `rev2-cradle-v3-side-profile-battery-trough.jpg` — side profile
    - `rev2-cradle-v3-angled-tp4056-usbc-end.jpg` — USB-C end angled
    - `rev2-topcover-v3-interior-pico2w-seated.jpg` — Pico 2 W in cover
    - `rev2-topcover-v3-interior-joystick-hole-portrait.jpg` — joystick hole portrait
    - `rev2-topcover-v3-interior-display-inlay-recess.jpg` — display inlay cavity
    - `rev2-topcover-v3-interior-angled-waveshare.jpg` — angled with Waveshare
    - `rev2-v3-assembled-stack-side-profile.jpg` — mated stack side view
    - `rev2-solar-panel-pcb-back-ak62x36.jpg` — solar panel back
    - `rev2-solar-panel-pcb-front-cells.jpg` — solar panel front
    - `rev2-baseplate-v3-topdown-blocks-troughs.jpg` — blocks and troughs
    - `rev2-baseplate-v3-side-profile-pegs-fillet.jpg` — pegs and fillet side
  - 12 stale root JPEGs (older layout/battery/base photos) moved to `website/docs/assets/images/enclosure/`
  - `docs/solar-charging-research.md` — fixed broken image path after move
  - `website/docs/docs/hardware/design-evolution.md` — new "Rev 2 — v3 Print Session Photos" section with 14 annotated images + 1 version history row
  - `website/docs/blog/posts/rev2-v3-print-session-assembly.md` (new) — blog post with all assembly photos and next-steps roadmap
  - `website/docs/prompts/index.md` — synced with prompt #252
  - `PromptProgression.md` — prompt #252 appended
  - HEIC originals deleted

---

## Prompt #253 — 2026-04-26

**Prompt sequence:** Hand-routed joystick breakout PCB design session in KiCad 10 (~20 turns). Started with missing symbol libraries ("I have no symbols available in KiCad how do I get a symbol lib"), installed `kicad-library`, pulled the K1-1506SN-01 5-way switch from JLCPCB via `easyeda2kicad` (LCSC C145910), added a 6-pin connector header, wired the schematic (COM to ground, 5 direction signals to GPIOs via internal pull-ups), annotated components, assigned footprints, drew a 19.6x19.6mm edge cut, centered the joystick, added silkscreen labels (Com/L/D/UP/R/C), fixed ERC errors, exported gerbers and JLCPCB-compatible BOM. Then cropped the KiCad workspace screenshot into labeled sections and updated docs/blog/website/prompts.

- **Input Tokens (est):** ~500 across the sequence
- **Output Tokens (est):** ~8,000
- **Commit:** `cab962e` — Hand-routed joystick PCB (K1-1506SN-01) + blog/docs/prompts update
- **Summary:** First PCB designed entirely from scratch (no autorouter). KiCad workspace screenshot cropped into 4 labeled JPEGs (PCB layout, schematic, 3D viewer, full workspace). New blog post `joystick-hand-routed-pcb.md`. Design evolution updated with new section and version history row. Front page updated with joystick PCB 3D preview image and current progress. JLCPCB BOM reformatted in `production/bom.csv`.
- **Layman summary:** Designed a tiny circuit board (about the size of a postage stamp) for a joystick controller. Started from nothing — installed the parts catalog, downloaded the joystick component from an online supplier, drew the wiring diagram, laid out where every wire goes on the board, added labels so you know which wire is which direction, and exported the manufacturing files to send to a factory in China that will make the real board.
- **Files:**
  - `hardware-design/joystick-pcb-by-hand/JoystickBoardDilder/JoystickBoardDilder.kicad_sch` — schematic with K1-1506SN-01 + Conn_01x06_Pin
  - `hardware-design/joystick-pcb-by-hand/JoystickBoardDilder/JoystickBoardDilder.kicad_pcb` — hand-routed PCB layout
  - `hardware-design/joystick-pcb-by-hand/JoystickBoardDilder/JoystickBoardDilder.kicad_sym` — project-local symbol library (easyeda2kicad import)
  - `hardware-design/joystick-pcb-by-hand/JoystickBoardDilder/production/bom.csv` — JLCPCB-format BOM
  - `website/docs/assets/images/hardware/pcb/joystick-hand-pcb-layout-editor.jpg` (new) — cropped PCB layout
  - `website/docs/assets/images/hardware/pcb/joystick-hand-schematic-editor.jpg` (new) — cropped schematic
  - `website/docs/assets/images/hardware/pcb/joystick-hand-3d-viewer.jpg` (new) — cropped 3D viewer
  - `website/docs/assets/images/hardware/pcb/joystick-hand-pcb-full-workspace.jpg` (new) — full workspace screenshot
  - `website/docs/blog/posts/joystick-hand-routed-pcb.md` (new) — blog post
  - `website/docs/docs/hardware/design-evolution.md` — new section + version history row
  - `website/docs/index.md` — front page updated with PCB image and progress
  - `PromptProgression.md` (this file), `website/docs/prompts/index.md` — prompts #253 appended

---

## Prompt #254 — 2026-04-26
- **Prompt sequence:** Extended iterative SCAD session (~15 turns) covering top cover face plate curvature tuning, base plate pillar extension height adjustability, and solar panel integration. Key turns:
  - Top cover: multiple attempts at a `face_plate_outer_edge_curve_radius_mm` parameter to independently control the face-to-wall rollover without bulging the sides or affecting the display window. Final approach uses `scale([1,1,zr/case_r])` on the top spheres to create an ellipsoid — flat face in Z, unchanged walls in XY.
  - Base plate (thinner): `peg_height_above_pillar_mm` Customizer slider added (0–10mm, 0.1mm steps). `pillar_extension_z_above_plate_mm` parameter added to `base-plate-v1-2mm-thinner.scad` with negative range support (-10 to +10mm). Original 5x5 screw pillars kept at fixed height; only extension wings respond to the Z adjustment.
  - Solar panel: new `base-plate-with-solar-cutout.scad` forked from the thinner variant. 62x36mm pit (AK 62X36 panel dimensions), 2mm deep, centered on bottom face. Two 3mm wire pass-through holes at adjustable coordinates. Breakaway support ribs added (0.4mm walls, 5mm spacing, 0.2mm Z gap) for printing the pit ceiling without slicer supports.
  - Cleanup: joystick-pcb/ (autorouter version) deleted in favor of joystick-pcb-by-hand/. Solar params removed from thinner file after fork.
- **Input Tokens (est):** ~600 across the sequence
- **Output Tokens (est):** ~30,000
- **Commit:** `21650d8` — Top cover curvature param + base plate pillar tuning + solar cutout variant
- **Files / interpretation:**
  - `04-26-design-alterations/top-cover-windowed-screen-inlay-v3-2piece.scad` — `face_plate_outer_edge_curve_radius_mm` parameter + ellipsoid sphere scaling in `shell_with_bullnose_top`
  - `04-26-design-alterations/base-plate-v1-2mm-thinner.scad` — `peg_height_above_pillar_mm` slider, `pillar_extension_z_above_plate_mm` with negative range, split pillar/extension wing geometry
  - `04-26-design-alterations/base-plate-with-solar-cutout.scad` (new) — fork of thinner with solar pit + wire holes + breakaway support ribs
  - `04-26-design-alterations/base-plate-with-solar-cutout__with_supports.3mf` (new) — rendered with supports
  - `hardware-design/joystick-pcb/` (deleted) — superseded by `joystick-pcb-by-hand/`
  - Multiple `.json` preset files and `.3mf` renders updated
  - `website/docs/docs/hardware/design-evolution.md` — 3 new version history rows
  - `website/docs/prompts/index.md` — synced with prompt #254
  - `PromptProgression.md` — prompt #254 appended

---

## Prompt #255 — 2026-04-26

- **Prompt sequence:** Multi-turn session adding Raspberry Pi Pico 2 W (RP2350) as a third target board alongside Pico W and ESP32-S3. Major iterative effort covering board support, GUI adaptation, build system porting, and resolving RP2350 platform incompatibilities. Key turns:
  - Board support: added `BOARD_PICO2_W` to `board_config.h` (same pins, 4MB flash), `firmware/CMakeLists.txt`, DevTool board selector dropdown, `setup.py` CLI (`--board pico2`).
  - DevTool GUI: full sweep of all user-visible strings — FlashUtility, ConnectionUtility, PinViewer, DocumentationTab, ProgramsTab — all now dynamically show "Pico 2 W (RP2350)" or "Pico W (RP2040)" based on dropdown selection. BOOTSEL drive label shows "RP2350" vs "RPI-RP2". Documentation tab refreshes on board change.
  - Dockerfile: `PICO_BOARD` env var made configurable (was hardcoded `pico_w`).
  - BOOTSEL detection: `find_rpi_rp2_mount()` updated in both `devtool.py` and `setup.py` to search for both `RPI-RP2` (Pico W) and `RP2350` (Pico 2 W) drive labels.
  - CMake cache poisoning: stale `PICO_PLATFORM=rp2040` in build dirs caused failures when switching to `pico2_w`. Added cache detection logic that checks both `PICO_BOARD` and `PICO_PLATFORM` and auto-wipes `build/` on mismatch.
  - RTC compat: RP2350 has no hardware RTC — `hardware/rtc.h` and `pico/util/datetime.h` (which defines `datetime_t`) don't exist. Created `rtc_compat.h` that defines `datetime_t` and software `rtc_init()`/`rtc_set_datetime()`/`rtc_get_datetime()` using `time_us_64()` on RP2350, passes through to real hardware on RP2040. Updated all 18 program `main.c` files and CMakeLists.txt files (conditional `hardware_rtc` linking).
  - Docs: new `website/docs/docs/reference/pico-2-w.md` with specs comparison, critical gotchas, and migration guide. Added to mkdocs nav.
- **Input Tokens (est):** ~800 across the sequence
- **Output Tokens (est):** ~45,000
- **Commit:** `39d375f` — Add Pico 2 W (RP2350) as third target board
- **Files:**
  - `firmware/include/platform/board_config.h` — `BOARD_PICO2_W` section (RP2350, 4MB flash, same pins)
  - `firmware/CMakeLists.txt` — `PICO2_W` target board option
  - `DevTool/devtool.py` — board selector, dynamic UI text, BOOTSEL detection, Docker/CMake build flags, pin viewer, docs refresh
  - `setup.py` — `--board pico2`, interactive menu, cache detection, dynamic step text
  - `dev-setup/Dockerfile` — `PICO_BOARD` env var
  - `dev-setup/hello-world/lib/Config/rtc_compat.h` (new) — cross-platform RTC compat header
  - `dev-setup/*/main.c` (18 files) — `rtc_compat.h` replaces `hardware/rtc.h` + `pico/util/datetime.h`
  - `dev-setup/*/CMakeLists.txt` (18 files) — conditional `hardware_rtc` linking
  - `website/docs/docs/reference/pico-2-w.md` (new) — Pico 2 W reference and migration guide
  - `website/mkdocs.yml` — nav entry for Pico 2 W reference
  - `website/docs/prompts/index.md` — synced with prompt #255
  - `PromptProgression.md` — prompt #255 appended

---

## Prompt #256 — 2026-04-26

- **Prompt:** "ok new heic images added analyse and describe and rename them descriptively and put them on the front page after converting to jpeg and put em in a proper folder delete the heic files and update the blog and hardware evolution pull the renders for the latest scad and this is going to be the current design so update the website and hard design to reflect that then commit and push update prompts and push"
- **Input Tokens (est):** ~80
- **Output Tokens (est):** ~8,000
- **Commit:** `ac8f356` — Current design photos + front page gallery + Pico 2 W blog post
- **Files:**
  - `website/docs/assets/images/enclosure/rev2-current/rev2-assembled-front-view.jpg` (new) — converted from HEIC, Pico 2 W running Sassy Octopus front view
  - `website/docs/assets/images/enclosure/rev2-current/rev2-assembled-three-quarter-view.jpg` (new) — three-quarter angle showing case depth
  - `website/docs/assets/images/enclosure/rev2-current/rev2-display-closeup-sassy-octopus.jpg` (new) — e-ink display close-up with clock header and quote
  - `website/docs/assets/images/enclosure/rev2-current/rev2-case-parts-disassembled.jpg` (new) — top cover, base plate, cradle laid out
  - `*.heic` (6 deleted) — original camera files removed
  - `website/docs/index.md` — front page redesigned with current build gallery, updated hardware table for Pico 2 W as default
  - `website/docs/blog/posts/pico2w-board-support-current-design.md` (new) — blog post covering Pico 2 W support and current design photos
  - `website/docs/docs/hardware/design-evolution.md` — Pico 2 W and current design photo entries
  - `website/docs/prompts/index.md` — synced with prompt #256
  - `PromptProgression.md` — prompt #256 appended

---

## Prompt #257 — 2026-04-27

- **Prompt sequence:** Multi-turn SCAD session forking two design files for the next print pass, plus a battery-procurement research thread. Key turns:
  - Fork the solar-cutout base plate using the `with supports` preset values as baked defaults — name it `base-plate-solar-thin-af-27-04`. (Preset deltas: `solar_pit_*`, `solar_hole_*`, `aaa_bay_x_start/length`, `battery_rail_z_lift`, `cradle_pocket_floor_thickness`, `outer_case_bottom_edge_fillet_radius`, `pico_retention_block_height`, `pillar_extension_y/z`, `usb_sidewall_block_width_y`, `solar_support_enabled false` — 17 knobs in total.)
  - User then hand-edited the new `.json` to a "thick floo reduce negative space" preset (total height 11.5 → 8 mm, floor 2.5 → 2.6 mm, pico retention 7 → 3 mm) and rendered with that preset.
  - Battery procurement: confirmed PKCELL ICR10440 (3.7 V, 350 mAh, 4-pack, ~€16 on Amazon DE) as the correct cell for the TP4056 + solar charging path — verified against the listing's `3.7 V Lithium Ion / ICR10440` spec, distinguished from regulated 1.5 V AAA-form-factor cells (the Ansmanns) which would be wrong for a TP4056.
  - Fork the AAA cradle insert using the `working insert 4-26-26` preset values — name it `aaa-cradle-with-batt-clips`. Preset values matched parent SCAD constants exactly (no value bake), so the fork only adds the new feature: 4 vertical drop-in slots sized for the **smallest Swpeet 1.5V AAA battery contact plate** (7×7 mm stamped sheet metal), one at each X-end of each AAA bay. Slot dimensions: 7.4 × 7.4 × 0.9 mm (size + 0.2 slop per edge, plate ~0.5 mm thick + tolerance), centered on cell axis, opening upward to plug top so plates drop in post-print and wires exit through the top.
  - Render both new files to 3MF; commit and push the design evolution; update prompts.
- **Input Tokens (est):** ~400 across the sequence
- **Output Tokens (est):** ~25,000
- **Commit:** `faf44b7` — Thin-af base plate fork + cradle with batt-clip slots + 10440 battery research
- **Summary:** Two new SCAD forks for the 2026-04-27 design pass: a thinner solar-cutout base plate (`base-plate-solar-thin-af-27-04`) carrying the with-supports preset as defaults, and an AAA cradle with battery-clip slots (`aaa-cradle-with-batt-clips`) sized for the cheapest Swpeet 7×7 mm unipolar contact plates. The cradle slots are oriented in YZ, opening to the plug top — 0.9 mm friction-fit thickness, plates drop in from above, wires exit upward. Battery-of-record settled: PKCELL ICR10440 raw 3.7 V Li-Ion AAA, wired in **parallel** (not series — 2S = 7.4 V exceeds the Pico W's 5.5 V VSYS max). Adhesive research note added (`solar-panel-bonding-adhesives.md`) covering Sikaflex / VHB / DOWSIL options for bonding the AK 62×36 panel to a PETG base plate outdoors.
- **Layman summary:** Cloned two 3D-print files to start the next iteration. The base plate gets a name based on its goal — make it really thin. The battery cradle gets a new feature — four little slots at the ends of each battery cylinder, sized to hold the metal contact tabs from a cheap multi-pack of battery springs. Also nailed down which rechargeable AAA-shaped batteries to actually buy (the 3.7 V "raw lithium" kind — not the deceptively similar 1.5 V "smart" kind — because the charger board on the device only knows how to charge the raw kind), and wrote up which glues survive years of sun for sticking the solar panel down.
- **Files:**
  - `hardware-design/scad Parts/Rev 2 extended with joystick/04-26-design-alterations/base-plate-solar-thin-af-27-04.scad` (new) — fork of `base-plate-with-solar-cutout` with `with supports` preset values baked as defaults
  - `hardware-design/scad Parts/Rev 2 extended with joystick/04-26-design-alterations/base-plate-solar-thin-af-27-04.json` (new) — customizer params; user-edited preset `thick floo reduce negative space` for the 8 mm thinner pass
  - `hardware-design/scad Parts/Rev 2 extended with joystick/04-26-design-alterations/base-plate-solar-thin-af-27-04.3mf` (new) — render at default values
  - `hardware-design/scad Parts/Rev 2 extended with joystick/04-26-design-alterations/base-plate-solar-thin-af-27-04__thick_floo_reduce_negative_space.3mf` (new) — render with the user's thinner preset
  - `hardware-design/scad Parts/Rev 2 extended with joystick/04-26-design-alterations/aaa-cradle-with-batt-clips.scad` (new) — fork of `aaa-cradle-insert-v1` with 4 contact-plate slots for the Swpeet 7×7 mm unipolar plate
  - `hardware-design/scad Parts/Rev 2 extended with joystick/04-26-design-alterations/aaa-cradle-with-batt-clips.json` (new) — customizer params with new `batt_clip_*` knobs
  - `hardware-design/scad Parts/Rev 2 extended with joystick/04-26-design-alterations/aaa-cradle-with-batt-clips.3mf` (new) — render at default values
  - `hardware-design/scad Parts/Rev 2 extended with joystick/04-26-design-alterations/solar-panel-bonding-adhesives.md` (new) — outdoor-adhesive option matrix for bonding the AK 62×36 panel to PETG (Sikaflex 252 / 295 UV / DOWSIL 795 / 3M VHB 4945)
  - `hardware-design/scad Parts/Rev 2 extended with joystick/04-26-design-alterations/base-plate-with-solar-cutout.{scad,json,__with_supports.3mf}` — minor cleanup (8 → 8.0 default, json key sort)
  - `website/docs/docs/hardware/design-evolution.md` — version history rows for the two new forks
  - `website/docs/prompts/index.md` — synced with prompt #257
  - `PromptProgression.md` — prompt #257 appended

---

## Prompt #258 — 2026-04-27

- **Prompt:** "put a small 1mm thick retaining side in front of the battery clip holder so it will hold the battery clip in and only surround the perimeter so that contact points are exposed to the battery" — followed by a render-and-push pass after a user-named preset was added.
- **Input Tokens (est):** ~80
- **Output Tokens (est):** ~3,500
- **Commit:** `583744d` — Add retainer wall to batt-clip slots
- **Summary:** Added a 1 mm retainer wall on the cell side of each of the 4 battery-clip slots in `aaa-cradle-with-batt-clips.scad`. Implementation uses SUBTRACTIVE geometry (no floating add-ons): each slot is pulled back from its bay end by `batt_clip_retainer_thickness_x_mm`, leaving body material as the wall, and a smaller central window (`batt_clip_retainer_window_size_y/z_mm`, default 5 × 5 mm) is cut through the wall to expose the plate's contact face to the cell. The wall catches the 7 × 7 mm Swpeet plate's perimeter with 1 mm of edge engagement on all sides. Cylinder cut shaves ~0.1 mm off the wall on the bay side, so effective wall thickness is ~0.9 mm (close enough to spec). Four new tunable knobs: `batt_clip_retainer_enabled` (true), `_thickness_x_mm` (1.0), `_window_size_y_mm` / `_window_size_z_mm` (5.0). Set enabled=false to revert to the original through-slot. User then added a new customizer preset `battery clips first print 04-27` capturing these values for the next print run, and rendered it.
- **Layman summary:** Each battery contact tab now has a tiny picture-frame in front of it — a 1 mm wall with a 5 mm hole cut in the middle. The frame catches the edge of the metal contact tab so it can't fall sideways into the battery hole, but the hole in the frame's middle lets the contact still touch the battery's terminal. Like a window screen: the screen catches the bug, the air gets through.
- **Files:**
  - `hardware-design/scad Parts/Rev 2 extended with joystick/04-26-design-alterations/aaa-cradle-with-batt-clips.scad` — retainer params + revised `batt_clip_slot` module (slot offset + window cut)
  - `hardware-design/scad Parts/Rev 2 extended with joystick/04-26-design-alterations/aaa-cradle-with-batt-clips.json` — new `battery clips first print 04-27` preset for the first-print pass
  - `hardware-design/scad Parts/Rev 2 extended with joystick/04-26-design-alterations/aaa-cradle-with-batt-clips.3mf` — re-render with retainer walls present
  - `hardware-design/scad Parts/Rev 2 extended with joystick/04-26-design-alterations/aaa-cradle-with-batt-clips__battery_clips_first_print_04-27.3mf` (new) — render of the named first-print preset
  - `website/docs/docs/hardware/design-evolution.md` — version history row for the retainer wall
  - `website/docs/prompts/index.md` — synced with prompt #258
  - `PromptProgression.md` — prompt #258 appended

---

## Prompt #259 — 2026-04-27
- **Prompt:** "ok I designed the board and sent it to JLCPCB, got this email... help me understand what they are asking... make an md note of this exchange in the hardware design and give a summary of the design process and status so far, update the website with a progression blog page, and update the design evolution and running summary of everything"
- **Input Tokens (est):** ~200
- **Output Tokens (est):** ~8,000
- **Commit:** `5ca8a59` — JLCPCB joystick PCB order notes + blog + docs/prompts update
- **Summary:** Analyzed the JLCPCB placement verification email for the joystick PCB order. The factory flagged SW1 (K1-1506SN-01) because the near-symmetric package makes automated rotation detection unreliable. "Polarity" in this context means component orientation, not electrical polarity — the switch is passive. Confirmed the placement image shows the correct rotation (pin A/up arrow away from header). Documented the exchange, the full PCB design journey (autorouted Rev 1 failure through hand-routed Rev 2 success), current build status, and lesson learned (add pin 1 silkscreen dot). New blog post with build status table and next steps.
- **Files:**
  - `hardware-design/jlcpcb-joystick-pcb-order-notes.md` (new) — JLCPCB order notes, placement verification analysis, PCB design journey, current status
  - `website/docs/assets/images/hardware/pcb/jlcpcb-sw1-placement-verification.png` — moved from root `unnamed.png`
  - `website/docs/blog/posts/joystick-pcb-jlcpcb-order.md` (new) — blog post with order details, design history, and build status table
  - `website/docs/docs/hardware/design-evolution.md` — JLCPCB order version history row
  - `website/docs/prompts/index.md` — synced with prompt #259
  - `PromptProgression.md` — prompt #259 appended

---

## Prompt #260 — 2026-04-27
- **Prompt:** "can we embed the filename into the model print, have that as an option in the export, find a flat bit that won't be on the printer bed and put a file or product number?"
- **Input Tokens (est):** ~40
- **Output Tokens (est):** ~4,500
- **Commit:** `a4abf3f` — DesignTool: embedded label feature + export history tracking
- **Summary:** Added a label-embedding option to the DesignTool's Export tab. Recessed or raised text on any vertical face (front/back/left/right), configurable font size, depth, and position. Uses a two-pass STL workflow: plain export first, then a wrapper SCAD that `import()`s the STL and applies `difference()` (recessed) or `union()` (raised) with a `linear_extrude`d `text()` block. Label details recorded in description.md and history.json for each export.
- **Layman summary:** Added a feature to stamp a filename or product number onto the side of your 3D-printed part — like a tiny engraved label that won't interfere with the flat bottom sitting on the print bed.
- **Files:**
  - `hardware-design/DesignTool/designtool.py` — label UI controls (checkbox, text, size, depth, face, offsets) + two-pass export workflow + wrapper SCAD generation

---

## Prompt #261 — 2026-04-27
- **Prompt:** "take the models in the Dilder Pico Prototype with joystick cutout aaa battery holder and clip cutouts Working Model Rev 1 and create a proper parametric FreeCAD design based on the SCAD and parameters setup"
- **Input Tokens (est):** ~60
- **Output Tokens (est):** ~25,000
- **Commit:** `5d25c9a` — FreeCAD PartDesign parametric model — full 3-part enclosure
- **Summary:** Translated all three Rev 2 enclosure parts (base plate, AAA cradle, top cover) from OpenSCAD to FreeCAD. First attempt used `Part::Feature` (frozen CSG shapes) — looked correct but had no editable feature tree. Rebuilt from scratch using real PartDesign API: `Sketcher::SketchObject` with constraints, `PartDesign::Pad`, `PartDesign::Pocket`, `PartDesign::Fillet`, `AdditiveBox`, `AdditiveCylinder`, `SubtractiveCylinder`. 81 features across 3 Bodies, 90-parameter spreadsheet with expression links. Fixed face-coordinate-system issues by replacing sketch-on-face pockets with `SubtractiveBox`/`SubtractiveCylinder` using explicit placement coordinates. Added USB-C stadium-shaped cutout (rounded bottom corners, open top) using 3 subtractive features. Comprehensive FreeCAD guide written with step-by-step tutorial panels showing 2D sketch diagrams alongside 3D results.
- **Layman summary:** Converted the entire Tamagotchi case design from a text-based CAD tool (OpenSCAD) into a visual CAD tool (FreeCAD) where you can click on any part of the model and change its dimensions by typing new numbers. Like going from editing code to using a graphical editor.
- **Files:**
  - `hardware-design/freecad/dilder_rev2_partdesign.FCMacro` — PartDesign macro (81 features, 90 params)
  - `hardware-design/freecad/Dilder_Rev2_PartDesign.FCStd` — pre-built FreeCAD document
  - `hardware-design/freecad/dilder_rev2_parametric.FCMacro` — legacy static CSG version
  - `hardware-design/freecad/*_PD.stl` — exported meshes for each part
  - `hardware-design/Working Designs/` — organized working model snapshot with all exports

---

## Prompt #262 — 2026-04-28
- **Prompt sequence:** Multi-turn FreeCAD rebuild of the TopCover body. Started with a viewing question ("how do I see the final part?"), escalated to "the topcover doesn't have the cutouts like the SCAD does," then "rebuild it from scratch with proper sketches and constraints — option C," then "I want a full master sketch for this," followed by "the cavity has a plane covering the inside and the FPC divet is missing," and finally "I want ZX sketches to alter component depths so I can make the top cover as thin as possible."
- **Input Tokens (est):** ~400 across the sequence
- **Output Tokens (est):** ~40,000
- **Commit:** `8868f13` — Parametric TopCover rebuild with master sketch + Z-section + prompt #262
- **Summary:** Full parametric rebuild of the TopCover Body in `Dilder_Rev2_PartDesign.FCStd`. Replaced the placement-based `SubtractiveBox` / `SubtractiveCylinder` primitives from prompt #261 with a sketch-driven master-sketch architecture. New `topcover_master_sketch.FCMacro` (~700 lines) builds: a 30-alias `TC_Params` spreadsheet (the dimensional source of truth); `Sk_Master_Plan` — a single XY-plane construction-only sketch holding every plan-view outline (outer shell, cavity, 4 pillars, screen inlay, display window, FPC ribbon divet, joystick PCB pocket, joystick through-hole, 4 M3 bores) fully constrained to spreadsheet aliases so the entire plan is visible in one diagram; per-feature sketches (`Sk_Shell`, `Sk_Cavity`, `Sk_Pillar_1..4`, `Sk_Inlay`, `Sk_Window`, `Sk_Joystick`, `Sk_M3_1..4`, `Sk_JoyPCB`, `Sk_FPC`) each on its own datum offset, with full geometric (Coincident, Horizontal, Vertical) + dimensional (DistanceX, DistanceY, Diameter) constraints all expression-bound to the same aliases; PartDesign Pads/Pockets driven by those sketches plus `Fillet_Corners` (vertical edges) and `Fillet_Bullnose` (top edges); display window and joystick hole get tapered Pockets (23.05° and 17.70° outward draft) matching SCAD's `hull()`-based frustum cuts. Two debug iterations: (1) the master sketch's overlapping rectangles caused `makeElementFace: invalid face` errors until every line in the master was flagged construction-only; (2) every `Pocket.Reversed` flag was inverted from convention — verified by an empirical test that proved `Reversed=False` cuts in -Z (downward) from the sketch plane (not +Z as initially assumed), causing the cavity to never carve out and the FPC divet to extrude into space. Fixed all 7 cuts (cavity now Reversed=True for upward, inlay/JoyPCB/FPC now False for downward, window/joystick/M3-bore now True for upward) — volume dropped 57460 → 20288 mm³ and face count grew 40 → 48, confirming the cuts now actually remove material. Final addition: `Sk_Section_Y23`, an XZ-plane side-profile section through Y=23 (display + joystick centerline) showing the full Z-layout as construction lines — outer envelope rectangle, 7 horizontal Z-level construction lines (`Z_ext_bot`, `Z_mating`, `Z_fpc_floor`, `Z_inlay_floor`, `Z_face_bot`, `Z_face_top`, `Z_bullnose_top`), and 6 vertical X-marker lines (`X_wall_mx`, `X_wall_px`, `X_inlay_x0/x1`, `X_joy_cx`, `X_fpc_x0`) — every dimension expression-bound so the section visualizes whatever the spreadsheet currently dictates. Documented the thinning levers: total height = `face_bot + fp_z + bull_r` = 11.7 mm; aggressive thin preset (`face_bot=5.0`, `fp_z=0.5`, `bull_r=1.5`) drops it to 7.0 mm. BasePlate and AAACradle bodies untouched. Pre-rebuild `.bak` snapshot kept for rollback.
- **Layman summary:** Took the case's top cover and rebuilt it inside FreeCAD so every shape is now a real editable sketch instead of a frozen box. There's one "master diagram" sketch that shows the whole top-down view in one place, and a side-view sketch that shows every height layer (where the screen sits, where the face plate is, how thick the rolled top edge is). Both sketches are wired to a parameter spreadsheet — change a number there, hit recompute, and the cover updates. To make the cover thinner, edit three numbers: how much room the screen needs, how thick the top plate is, and how rounded the top edge is. Also fixed two bugs along the way: the cavity wasn't actually hollowing out (had a "ceiling plane" floating inside) and the cable slot wasn't getting cut — both because every Pocket was set to cut in the wrong direction.
- **Files:**
  - `hardware-design/freecad/topcover_master_sketch.FCMacro` (new) — parametric TopCover macro: 30-alias spreadsheet, master plan sketch, side-profile section sketch, per-feature sketches with full constraint sets, expression bindings throughout
  - `hardware-design/freecad/Dilder_Rev2_PartDesign.FCStd` — TopCover body rebuilt; BasePlate + AAACradle untouched. 34 features, Tip = `Cut_FPC`, valid solid, 48 faces, 20288 mm³
  - `hardware-design/freecad/Dilder_Rev2_PartDesign_MasterSketch.FCStd` (new) — sanity copy of the rebuilt file
  - `hardware-design/freecad/Dilder_Rev2_PartDesign.FCStd.bak-20260427-203331` (new) — pre-rebuild backup
  - `hardware-design/freecad/Dilder_Rev2_PartDesign-TopCover.3mf` (new) — exported mesh of the rebuilt cover
  - `hardware-design/freecad/Dilder_Rev2_PartDesign_MasterSketch.20260427-204016.FCBak`, `…20260427-205533.FCBak` (new) — FreeCAD auto-backups

---

## Prompt #263 — 2026-04-29
- **Prompt:** "the solar panel holes for the wires dont cut through the base plate fully in the macro you made" — followed by "commit and push all these changes and update the documentation create a few render pic of all the pieces we made individually and assembled and put that on the front page then commit and push this all update the prompts with the git hashes and commit and push once more"
- **Input Tokens (est):** ~150
- **Output Tokens (est):** ~12,000
- **Commit:** `9d96395` — Rev 2 Mk2 enclosure: final SCAD parts, FreeCAD macro fix, renders, README update
- **Summary:** Fixed the solar panel wire holes in `dilder_rev2_mk2.FCMacro` — the two `SubtractiveCylinder` features were at step 7 in the feature tree, but steps 9-12 added pillars, wings, rail supports, and blocks on top. Since PartDesign evaluates sequentially, the holes only cut material that existed at step 7. Moved them to step 13 (last operation) so they cut through everything. Also added final baked SCAD files for all 3 parts, FreeCAD Mk2 design files (FCStd + 3MF exports), rendered all parts via OpenSCAD CLI (base plate top/bottom, AAA cradle, top cover, assembled), added render gallery to README front page, updated Phase 6 progress, and added `*.FCBak` to `.gitignore`.
- **Layman summary:** The wire holes for the solar panel weren't going all the way through the base plate because they were being drilled before walls and supports were added on top — like drilling a hole in a table before gluing a shelf over it. Moved the drilling step to the very end so it punches through everything. Also took nice pictures of all three parts and put them on the project's front page.
- **Files:**
  - `hardware-design/freecad-mk2/dilder_rev2_mk2.FCMacro` — moved WireHole SubtractiveCylinders from step 7 to step 13 (end of feature tree)
  - `hardware-design/renders/base-plate.png` (new) — OpenSCAD render, top view
  - `hardware-design/renders/base-plate-bottom.png` (new) — OpenSCAD render, bottom view showing solar pit
  - `hardware-design/renders/aaa-cradle.png` (new) — OpenSCAD render
  - `hardware-design/renders/top-cover.png` (new) — OpenSCAD render
  - `hardware-design/renders/assembled.png` (new) — OpenSCAD render, all 3 parts stacked
  - `README.md` — added enclosure render gallery section + updated Phase 6 checklist
  - `.gitignore` — added `*.FCBak` pattern
  - `hardware-design/final case with aaa cradle and solar/*.scad` (new) — final baked SCAD files
  - `hardware-design/freecad-mk2/*.FCStd` (new) — FreeCAD Mk2 design files
  - `hardware-design/freecad-mk2/*.3mf` (new) — exported meshes
  - `hardware-design/freecad-mk2/BUILD-INSTRUCTIONS.txt` (new)
  - `hardware-design/speaker-module-selection.md` (new)
  - `PromptProgression.md` — prompt #263 appended

---

## Prompt #264 — 2026-04-29
- **Prompt sequence:** Multi-turn integration of the Raspberry Pi Pico 2 W board into the FreeCAD assembly. "ok we got a macro to create the dilder board in free cad lets also pull in a model for the pico2 w board with headers see if you can find it online it would be good to seel it in the part assembly" → "ok reverse the pico on the x axis and align the edge of the board to the ClipWindow_2P.Face44" → "the headers should be on the opposite face of the pico board then we need to flip the board and headers along the z axis" → "nope that didn't work … the pico board face should sit flush with `AAACradle.ClipWindow_2P.Face6`" → "perfect orientation now lets make sure the ClipWindow_2P.Face44 is on the same z axis point as `AAACradle.ClipWindow_2P.Face6`" → "update the docs and make a new set of rendering pics and update the website and front page add a blog and outline the tech and steps used to create this model and how the macro works in a separate website doc commit and push and update prompt fix grammar add the commit hashes and push".
- **Input Tokens (est):** ~600 across the sequence
- **Output Tokens (est):** ~25,000
- **Commit:** `eb6e5c2` — Pico 2 W in FreeCAD assembly: STEP import, procedural headers, named-face anchoring
- **Summary:** Added the Pico 2 W board to the FreeCAD assembly with procedural pin headers and named-face anchoring. Raspberry Pi only publishes an official STEP for the (non-W) Pico 2, but it's mechanically identical to the Pico 2 W — only the wireless module differs. Downloaded `Pico-R3-step.zip` (a redirect chain off `datasheets.raspberrypi.com`) and committed `RaspberryPi-Pico-2.step` to `hardware-design/reference-boards/raspberry-pi-pico-2/`. Wrote `add_pico_with_headers()` in `dilder_rev2_mk2.FCMacro`. Five-stage pipeline: (1) `Part.Shape().read()` the STEP, then bbox-driven re-orientation — shortest axis becomes +Z, then a 90° Z rotation if the long axis ended up on Y — making the import robust to any source-CAD convention. (2) Optional 180° Z reverse (`PICO_USB_PLUS_X = False`) so the USB-C end sits on the −X side of the bbox. (3) Procedural 2×20 pin headers built **below** the board: two 50.8 mm shroud strips (one per long edge, 2.54 mm wide × 2.54 mm tall) plus 40 brass pins (0.64 mm square × 8.6 mm tall) on a 2.54 mm pitch with first pin 1.61 mm from one short edge and 1.0 mm row inset from each long edge — matching the standard Pico footprint. (4) A single 180° rotation about world X applied to **both** shapes — flips the board upside-down so components face −Z, headers swing from below to above with pins now pointing +Z. (5) Anchor to named cradle faces — `resolve_face_global((body, idx))` returns the global XYZ of `body.Tip.Shape.Faces[idx-1].CenterOfMass` after applying the body's `Placement`. `PICO_ANCHOR_FACE = ("AAACradle", 44)` gives the inner −X wall of the PicoNest cavity (global X = 11.20) — used to translate `bbox.XMin` to that X. `PICO_Z_ANCHOR_FACE = ("AAACradle", 6)` gives the plug-top mating plane (global Z = 6.00) — and the Z anchor expression is `target_z - (bb.ZMax - PCB_THICKNESS)` so the **component-side face** (one board thickness below the post-flip ZMax) lands flush, not the lowest point. Result: PCB component-side face at Z = 6.00 (flush with cradle), components hang to Z = 3.27 (into the base plate's cradle pocket), pin tips at Z = 18.14 (well into the cradle's PicoNest cavity). One critical ordering fix: the Pico import has to run **after** the cradle's `Placement` is applied in `main()`, otherwise the face center-of-mass resolves to local cradle coords (X = 85.10) instead of global (X = 11.20). Four new FreeCAD-rendered assembly images (iso with translucent cover, no-cover, cradle-hidden, front elevation) committed under `hardware-design/renders/` and copied into `website/docs/assets/images/enclosure/`. README front page got a "Pico 2 W in the Assembly" section. New blog post `website/docs/blog/posts/freecad-pico-import-and-assembly.md` walks through the technique. New doc page `website/docs/docs/hardware/freecad-mk2-macro.md` is a section-by-section macro reference covering helpers, the Parameters spreadsheet, all three body builds, the assembly-placement order, and the five-stage Pico import pipeline. `mkdocs.yml` nav updated. Design evolution table got a 2026-04-29 row. Website prompts index #264 synced.
- **Layman summary:** Added a real-looking Raspberry Pi Pico W board (with the little black pin-strips) to the 3D model so you can finally *see* where the brain of the device sits inside the case. Found that the Pi Foundation only ships the file for the non-wireless Pico (the wireless one is the same shape anyway), downloaded it, and wrote a script that automatically figures out which way the file is oriented and rotates it to match. Built the pin headers by code instead of downloading them. Then flipped the whole board upside-down so the chips face the floor and the pins poke up — like mounting a Pico under a shelf. Instead of typing in coordinates ("put the board at X=11.2"), the script asks the case "where's the inside of your wall?" and uses *that* as the anchor — so if you make the case bigger, the board moves with it automatically. Also re-rendered the case from inside FreeCAD with the Pico in place (you can see through the lid in one image, lid removed in another), updated the front page, wrote a blog post, and wrote a separate "how the macro works" reference page.
- **Files:**
  - `hardware-design/freecad-mk2/dilder_rev2_mk2.FCMacro` — added `add_pico_with_headers()` and integrated it into `main()` after the cradle/cover placements; new module-level constants `PICO_USB_PLUS_X`, `PICO_ANCHOR_FACE`, `PICO_Z_ANCHOR_FACE`
  - `hardware-design/freecad-mk2/Dilder_Rev2_Mk2.FCStd` — re-saved with the Pico import baked in
  - `hardware-design/reference-boards/raspberry-pi-pico-2/RaspberryPi-Pico-2.step` (new) — official RP Foundation STEP, 1.7 MB
  - `hardware-design/reference-boards/raspberry-pi-pico-2/Pico-2-step.zip` (new) — original archive
  - `hardware-design/renders/assembly-with-pico-iso.png` (new) — translucent-cover iso render
  - `hardware-design/renders/assembly-with-pico-no-cover.png` (new) — top cover hidden
  - `hardware-design/renders/assembly-with-pico-on-base.png` (new) — cradle hidden, Pico on base plate
  - `hardware-design/renders/assembly-with-pico-front.png` (new) — front elevation
  - `website/docs/assets/images/enclosure/assembly-with-pico-*.png` (new) — same four renders copied for the docs site
  - `README.md` — added "Pico 2 W in the Assembly" section with three render thumbnails and a link to the macro reference
  - `website/docs/blog/posts/freecad-pico-import-and-assembly.md` (new) — blog post: STEP source hunt, bbox-driven orientation, procedural headers, the Z-flip technique, named-face anchoring, why Z-anchor uses ZMax-PCB_THICKNESS instead of ZMin
  - `website/docs/docs/hardware/freecad-mk2-macro.md` (new) — full macro reference: file layout, run command, architecture table, Parameters spreadsheet, sketch helpers, edge finders, all three body builds in detail, assembly placement, the five-stage Pico import pipeline, tweaking guide, limitations
  - `website/mkdocs.yml` — added "FreeCAD Mk2 Macro" nav entry under Hardware
  - `website/docs/docs/hardware/design-evolution.md` — 2026-04-29 row covering the Pico import + Z-flip mount + named-face anchors
  - `website/docs/prompts/index.md` — Prompt #264 synced
  - `PromptProgression.md` — Prompt #264 appended

## Prompt #265 — 2026-04-29
- **Prompt sequence:** "ok we have to fix up the window cut on the topcover its a bit offcenter when you added 2mm to the length and with it should have been 1mm add to each end instead of one end" → "we need the center of the window cutout to be aligned with the center of the joystick cutout" → "ok can we add in a aaa battery assempbly in there find a model for that to attach to the rail and then also find a model for the usb c charger board we have to set in to the inlay we made then lets find a waveshare 2.13 eink display model to place in the top cover cutout we made for it".
- **Input Tokens (est):** ~250 across the sequence
- **Output Tokens (est):** ~10,000
- **Commit:** `a906cf1` — Add AAA cells, TP4056 charger, and Waveshare e-paper to FreeCAD assembly
- **Summary:** Two related fixes plus a peripherals expansion. (1) `Cut_Window` placement literals were stale — `win_w=48, win_h=22` while the spreadsheet `win_xl/win_yd` had moved to 50/25, so the centered placement formula `(65 - win_w)/2 + win_shift` computed a gap based on the OLD width and the cut grew off one corner instead of equally on both ends. Updated literals to 50/25 to match. (2) Wired `win_y0` directly to `joy_cy = enc_y/2` instead of going through `disp_y0`, making the window-vs-joystick Y alignment explicit so future joystick Y changes propagate to the window automatically. (3) Added `add_peripherals(doc)` to the macro — built three more components procedurally since most third-party STEP models for these are behind login/paywalls (CraftedTech, GrabCAD) and Waveshare doesn't publish CAD for the Pico-ePaper-2.13. Two AAA Li-Ion cells (10.5 mm × 39.5 mm cylinders + 5.5 mm brass positive-terminal caps) anchored to global Y=7.85/38.15, Z=12.05, X centered in each cradle bay's effective length range. TP4056 USB-C charge module (28 × 17 × 1.6 mm navy blue PCB + IC/capacitor block + silver USB-C connector protruding +X toward the base plate cutout) seated in the cradle's TP4056_Indent recess so the board top face is flush at global Z=6.0. Waveshare 2.13" e-paper display module (65 × 30 × 3 mm off-white carrier with a 50 × 22 mm "paper white" active panel rectangle on the +Z face, win-shifted +2.8 toward +X to match the window cut) sized to fill the top cover's screen inlay; module back at Z=18.0, panel surface at Z=21.0 visible through the display window. Re-rendered all four assembly views with peripherals visible and TopCover transparency dialed back from 60 → 40% so the cover actually shows up against the white background. README, FreeCAD macro reference doc, and design-evolution table updated.
- **Layman summary:** Fixed a small bug where the screen window in the top lid had grown off to one side instead of staying centered (it was using stale numbers from before the window got resized). Then locked the window's vertical centerline to the joystick's centerline so future tweaks stay in sync. Then added three more chunks of "fake" hardware to the 3D model so you can see the whole device assembled: two AAA batteries sitting in their bays, the little USB-C charger board tucked into its dimple, and the e-ink screen module fitting into its window pocket. Couldn't find free 3D models for the charger and screen so I just built them by hand using the published dimensions — same trick used for the pin headers. The new render shows everything inside through the translucent blue lid: green Pico board upside-down, black header pins, gold-toned battery cradle with two grey cells, white screen poking up through the window, silver USB-C nub on the side.
- **Files:**
  - `hardware-design/freecad-mk2/dilder_rev2_mk2.FCMacro` — `Cut_Window` literals 48/22 → 50/25 with new comment explaining the symmetric-grow contract; `win_y0` rewired to `joy_cy_v - win_h/2`; new `add_peripherals(doc)` function and `main()` wiring after the Pico import
  - `hardware-design/freecad-mk2/Dilder_Rev2_Mk2.FCStd` — re-saved with peripherals baked in
  - `hardware-design/renders/assembly-with-pico-{iso,no-cover,on-base,front}.png` — re-rendered with the 4 peripherals + 40% cover transparency
  - `website/docs/assets/images/enclosure/assembly-with-pico-*.png` — same set copied for the docs site
  - `README.md` — updated front-page section heading to "Full Assembly with Electronics" and added peripherals to the description
  - `website/docs/docs/hardware/freecad-mk2-macro.md` — new "Peripherals" section covering the AAA / TP4056 / e-ink builds; architecture table + main flow updated to include the new pipeline stage
  - `PromptProgression.md` — prompt #265 appended

---

## Prompt #266 — 2026-04-30
- **Prompt sequence:** "ok we were working on the macro earlier, I want you to — I undid that, that wasn't working, forget about that change for now. Let's build out a thumbpiece attachment that can snap securely to the joystick and be flush to the joystick circle cutout … make the thumbpieces concave to contour the thumb and 1mm shorter in diameter than the circle cutout" → "I do not want the square of the joystick exposed; the thumbpiece should cover that — it just slides in and uses the bit that covers to stop its travel downwards" → "didn't mean to send … undo any changes regarding that, I just wanted to fix the square hole in the prompt prior" → "whoa, it's extending out of the hole — no, and the diameter is too wide. It should nest in the joystick hole with 1mm around it to allow travel and cover the peg for the joystick model" → "ok we are back to the original. Essentially the squared peg is still exposed — perhaps make it a bit less concave so that we can cover that square" → "ok let's document this and add it to the hardware evolution, get some real nice renders of all of it like before, then we want to add the prototype to the home page of the site with the picture, make a new document regarding this hardware design process, commit and push, then update the prompts and put the git hash, clean up spelling, and commit and push".
- **Input Tokens (est):** ~700 across the sequence
- **Output Tokens (est):** ~30,000
- **Commit:** `3ffe156` — Joystick thumbpiece + cover joy-well + JoystickPCB STEP integration
- **Summary:** New `Thumbpiece` PartDesign Body in `dilder_rev2_mk2.FCMacro` — a printable snap cap that fits over the K1-1506SN-01 5-way switch actuator peg. Single disc nested inside the cover's 12 mm joystick circle cutout: OD = `joy_d - 1.0` = 11 mm (0.5 mm radial clearance all around → 1 mm total for joystick directional swing), height 4.5 mm, top sitting 0.1 mm below the cover top face (Z = 22.9), bottom at Z = 18.4. Three PartDesign primitives: `Thumb_Disc` (`AdditiveCylinder`), `Thumb_Dish` (`SubtractiveSphere` R = 12 mm, depth 0.6 mm — concave thumb contour), `Thumb_Socket` (`SubtractiveBox` 3.3 × 3.3 × 3.5 mm, friction-fit on the 3.2 mm peg). Socket is centered on the **actuator** (`thumb_stick_cy = 24.35`) **not** on the disc axis — the SW1 stick is offset +0.68 mm in Y from the cover hole on the production PCB layout, so the disc reads visually centered while the snap pocket actually lands on the peg. Geometry verified against the JoystickPCB STEP face selections (peg X span 77.75–80.95, Y span 22.76–25.94, Z span 17.91–21.17, top at Z = 21.17). Two wrong turns recovered: first attempt was a T-shape (wider cap on top of the cover + narrow stem dropping through the hole) — reverted because "1 mm shorter than the cutout" implied the whole thumbpiece nests inside the hole. Second issue was the dish breaking into the socket cavity — at 1.5 mm depth the dish bottom (Z = 21.4) was below the socket ceiling (Z = 21.95), opening a window straight through the disc to the peg. Fix: dish depth dropped to 0.6 mm with the constraint `thumb_dish_d < thumb_h - thumb_top_clr - thumb_sock_d` documented in the parameter description. Result: 0.35 mm solid skin covers the peg, 2.77 mm of socket grip, concave dish stays usable. 9 new spreadsheet aliases (`thumb_od`, `thumb_h`, `thumb_top_clr`, `thumb_dish_r/d`, `thumb_sock_x/y/d`, `thumb_stick_cy`) all expression-bound — drop `thumb_sock_x/y` to ~3.15 to convert friction-fit to interference snap-fit. Also bundled in this commit: cover's `Cut_JoyBody` square cutout sized to the SW1 body + clearance, `JoyWell_Outer/Inner/HeaderNotch` sleeve molding around the body inside the cover (header notch on -Y so the 6 wire-solder pads stay accessible), `JoystickPCBPit` on the cradle so the body's 10 mm height fits between pit floor and cover dome top, the hand-routed joystick PCB STEP committed under `joystick-pcb-by-hand/JoystickBoardDilder/`, and `add_joystick_pcb()` macro stage that imports it (filters out the pin-lead solid by volume threshold 80–180 mm³). Companion `render_views.FCMacro` that batch-saves 18 var-* views via FreeCAD Gui from a single FCStd open. README front page got a Joystick Thumbpiece section, website home page got a Latest Prototype section, design-evolution gained a 2026-04-30 row, and a new blog post `joystick-thumbpiece-snap-cap.md` walks through the peg-vs-hole offset, the T-shape wrong turn, the dish-vs-socket constraint, and why the thumbpiece had to be its own Body.
- **Layman summary:** The little plastic peg on the joystick switch is sharp and small, and bare it sticks up through the hole in the case lid looking unfinished. So I designed a snap-on thumb cap — shaped like a hockey puck, 11 mm across (1 mm narrower than the case hole so the joystick can still wiggle around for direction), with a bowl-shaped scoop on top to fit your thumb and a square pocket on the bottom that grips the peg. Trickiest bit: the peg isn't actually centered in the case hole — it's offset by half a millimeter — so the cap and the peg-grip-pocket have *different* centers. The cap is centered on the hole (so it looks straight), and the pocket is centered on the peg (so it actually grips). One bug along the way: the bowl on top was carved too deep and ate clean through into the peg pocket below, leaving a hole through the cap — so I made the bowl shallower and added a math constraint to the parameters that prevents future-me from doing the same thing. Also rendered 18 fresh views of the assembled device with the new cap in place, put a hero shot on the front page, wrote a blog post about the design decisions, and committed.
- **Files:**
  - `hardware-design/freecad-mk2/dilder_rev2_mk2.FCMacro` — added `build_thumbpiece(doc)` (Thumbpiece PartDesign Body with disc/dish/socket primitives) plus the supporting `Cut_JoyBody`, `JoyWell_Outer/Inner/HeaderNotch`, `JoystickPCBPit`, and `add_joystick_pcb(doc)` stages; 9 new `thumb_*` spreadsheet aliases
  - `hardware-design/freecad-mk2/render_views.FCMacro` (new) — batch-render macro: opens the FCStd, walks 18 + 1 viewpoints (hero iso, top translucent, front, side stack, cover-removed iso/top, cradle+batt+clips iso/top, pico-on-base, joystick detail, display detail, baseplate top/bottom, cradle bottom, cover bottom, exploded iso/front, joystick aligned top, thumbpiece hero), saves PNGs to `../renders/`
  - `hardware-design/freecad-mk2/Dilder_Rev2_Mk2.FCStd` — re-saved with thumbpiece + supporting features baked in
  - `hardware-design/joystick-pcb-by-hand/JoystickBoardDilder/JoystickBoardDilder.step` (new) — KiCad STEP export of the hand-routed K1-1506SN-01 breakout board, used by `add_joystick_pcb()`
  - `hardware-design/renders/var-01..17-*.png`, `var-joystick-aligned-top.png`, `var-thumbpiece-hero.png` (new) — fresh renders showing the assembly with the thumbpiece in place
  - `hardware-design/renders/assembly-with-pico-{front,iso,no-cover,on-base}.png` — re-rendered to include the new thumbpiece + cover joy-well features
  - `website/docs/assets/images/enclosure/var-*.png` (new) — same render set copied into the docs site
  - `website/docs/index.md` — new "Latest Prototype — Joystick Thumbpiece" section with hero + detail renders and a link to the blog post
  - `website/docs/docs/hardware/design-evolution.md` — 2026-04-30 row covering the thumbpiece geometry, spreadsheet aliases, and the dish-vs-socket constraint
  - `website/docs/blog/posts/joystick-thumbpiece-snap-cap.md` (new) — design write-up: the peg-vs-hole offset, the T-shape wrong turn, the dish-vs-socket constraint, why the thumbpiece is its own Body
  - `README.md` — front-page "Joystick Thumbpiece" section under the Mk2 enclosure block
  - `PromptProgression.md` — prompt #266 appended

---

## Prompt #267 — 2026-04-30
- **Prompt sequence:** "I made a new pad in the [FreeCAD file] pcbjoystick anchor and I got rid of the usb-c part and the cutout on the joy ... I need the square top of the joystick pcb Face277 to be aligned in the center of the joystick hole cutout" -> "TP4056_USBC should be removed also the square pit for the joystick board should fit the dimension perfectly for the board there's too much gap around it on the cradle then we want to get rid of the joypcb pocket on the front cover also the topcover is not there anymore after the changes you made" -> "ok the joystick pcb is in the right location but the square pit is not positioned correctly to fit the joystick board we need to move the square pit down the y-axis ... also we are missing the fillets around the joystick hole and window" -> "get rid of that last fillet step it's still too jank I'll do it myself ... we need the joy anchor to meet the top of the pcb board not go through it" -> "get rid of the retention block the wifi on the pico is what's being retained will that interfere with the wireless signal?" -> "ok I have some piezo speakers on the way ... find the proper dimensions of this and pull in an equivalent model ... then we need to create a circular formed elevated wall in the base plate between the battery rails" -> "ok now we wanna add the accelerometer to the base ... 1-10pcs IIC I2C SPI MPU6500 MPU-6500 6-Axis Gyroscope Accelerometer Sensor Module ... lets pull in the dimensions and a model assembly and carve out a spot similar to the speakers on the base" -> "get rid of the retention block ... will that interfere with the wireless signal?" -> "ok we got a lot of changes lets document it make renders update the website doc and put the renders on the home page ... add another blog entry notate and commit everything"
- **Input Tokens (est):** ~2,000 across the sequence
- **Output Tokens (est):** ~25,000
- **Commit:** `327d1de` — Joystick anchor pad, piezo speaker ring, MPU-6500 IMU pocket, alignment fix
- **Summary:** Major revision to the FreeCAD parametric macro covering joystick mounting, sensor integration, and alignment fixes. (1) Replaced the old `JoyWell_Outer/Inner` + `Cut_JoyBody` + `Cut_JoyPCBPocket` system with a single 14x14 mm `JoyAnchor_Outer/Inner` pad with 12 mm square inner hole, extending 6.85 mm from cover face_bot down to exactly the PCB top surface (pit floor 9.65 + 1.5 mm PCB = 11.15 global Z). (2) Fixed the joystick PCB Y placement bug: `joy_cy_g` was `enc_y/2 + 0.67` which double-applied the SW1 offset — the cover hole/pocket/pit already shift by `joy_pcb_y_offset`, so the PCB bbox center should be at `enc_y/2 = 23.0`. After fix the stick center lands within 0.01 mm of the hole center. (3) Tightened the cradle's `JoystickPCBPit` from 23 mm to 20 mm (`joy_pit_xy` param) and shifted its Y center from 23.67 to 23.0 to match the corrected PCB position — the 19.6 mm board now has 0.2 mm clearance per side instead of 1.7 mm. Fill piece guards added so they only generate when there's actually a gap to fill. (4) Added a 20 mm piezo speaker (FT-20T / YOUMILE JK-YM-297A) with a circular retaining ring on the base plate: `PiezoRing_Outer` (AdditiveCylinder OD 22.2 mm, 1 mm wall, 1.5 mm tall) + `PiezoRing_Inner` (SubtractiveCylinder ID 20.2 mm), centered at (47.25, 23.0) between the battery rails. Procedural `add_piezo_speaker()` builds the brass disc (20 mm x 0.2 mm) + ceramic element (15 mm x 0.22 mm). (5) Added an MPU-6500 6-axis IMU (GY-6500 module, 25x15 mm) with rectangular retaining pocket: `IMU_Wall` (AdditiveBox 27.4x17.4 mm) + `IMU_Pocket` (SubtractiveBox 25.4x15.4 mm), same Y center as piezo, shifted toward -X. Procedural `add_imu_module()` builds the PCB + QFN chip + passives + header pads. (6) Removed `TP4056_USBC` connector visualization, `PicoRetentionBlock` (overlapped IMU pocket). Neither piezo nor IMU interfere with Pico W 2.4 GHz WiFi — both are passive/low-frequency in plastic retaining walls. (7) Updated `render_views.FCMacro` with 3 new views (baseplate sensors top/iso, cover anchor bottom) and removed `TP4056_USBC` from hide lists. (8) New blog post, updated website home page with sensor build progress renders.
- **Layman summary:** Big hardware session. The joystick mount was redesigned — instead of a bulky sleeve wrapping around the whole PCB, there's now a precise collar that wraps just around the switch body and stops exactly at the top of the circuit board (no more poking through it). Fixed a subtle misalignment where the joystick peg was 0.68 mm off-center in its hole. Shrunk the slot that holds the joystick board so it fits snugly instead of rattling around. Added a piezo buzzer — a thin brass-and-ceramic disc that sits in a circular ring printed right into the base plate between the battery slots. Added a motion sensor (accelerometer/gyroscope chip on a tiny blue board) that drops into its own rectangular pocket next to the speaker. Removed some old features that were in the way. Updated the website and wrote a blog post about all of it.
- **Files:**
  - `hardware-design/freecad-mk2/dilder_rev2_mk2.FCMacro` — anchor pad replaces JoyWell/Cut_JoyBody/Cut_JoyPCBPocket; PCB Y fix; pit 23->20 mm; pit Y center fix; PiezoRing + IMU_Wall/Pocket in BasePlate; `add_piezo_speaker()`, `add_imu_module()` in peripherals; removed PicoRetentionBlock, TP4056_USBC
  - `hardware-design/freecad-mk2/render_views.FCMacro` — 3 new views (baseplate-sensors-top/iso, cover-anchor-bottom); removed TP4056_USBC refs
  - `hardware-design/freecad-mk2/Dilder_Rev2_Mk2.FCStd` — re-saved with all changes
  - `hardware-design/freecad-mk2/*-speeker-inlay-*accelerameter*.{FCStd,3mf}` — FreeCAD iteration snapshots
  - `hardware-design/speaker-module-selection.md` — updated
  - `website/docs/index.md` — home page updated: "Sensors, Speaker, and Joystick Anchor" section with 4 render images
  - `website/docs/blog/posts/joystick-anchor-piezo-imu-sensors.md` (new) — build write-up covering alignment fix, anchor pad, pit tightening, piezo ring, IMU pocket
  - `PromptProgression.md` — prompt #267 appended

---

## Prompt #268 — 2026-05-01
- **Prompt sequence:** "ok the top cover is wonky af the cutjoystick steps is a mess" -> "get rid of that last fillet step it's still too jank I'll do it myself" -> "the joystickpcb is intersecting the joy anchor, we need the joy anchor to meet the top of the pcb board not go through it" -> "get rid of the retention block" -> "ok I have some piezo speakers on the way" -> "ok now we wanna add the accelerometer to the base" -> "ok we got a lot of changes lets document it make renders" -> "ok we need to add .2mm to the length of the baseplate and cover" -> "I undid the widening ... lets add .2mm on the furthest x axis side [of the screen inlay]" -> "put it in a menu cli interface let me choose the freecad model" -> "give me options of what to render and render style and which body components" -> "the rendering is a lie its not looking at my freecad model at all I need freecad to open" -> "there are some blank images its not waiting to screenshot" -> "also I need some nice angled views" -> "ok perfect lets make a freecad build and render tool readme" -> "make a new set of robust renders ... update the website doc ... blog post ... commit push"
- **Input Tokens (est):** ~3,000 across the sequence
- **Output Tokens (est):** ~40,000
- **Commit:** `895314b` — Build & render CLI tool, comprehensive design doc, fresh renders
- **Summary:** (1) Fixed TopCover build failures: removed all programmatic fillets (user will add manually in FreeCAD GUI), fixed anchor pad depth from 10 mm to 6.85 mm so it stops at the PCB top surface instead of intersecting through it, removed PicoRetentionBlock (overlapped IMU pocket). (2) Cradle adjustments: shifted plug_x0 from 3.3 to 3.1 (+0.2 mm Pico clearance on +X global), plug_x1 from 93.0 to 93.01 (total cradle width 89.91 mm). (3) Display inlay: disp_xl from 65.0 to 65.2 mm (+0.2 mm for Waveshare V3 board fit; total inlay with slop = 65.8 mm). (4) Built interactive `build_and_render.sh` CLI tool: 5-screen flow (model picker sorted by date, 19 render presets, resolution/background/transparency style picker, custom component combos, confirmation). Generates a Python render script on the fly and launches FreeCAD GUI. Fixed blank renders by replacing `all_objects()` with `top_objects()` that skips internal PartDesign features, and adding `flush(5, 0.3)` to pump the Qt event loop before screenshots. Fixed unknown view errors by replacing invalid `ViewRotateRight` messages with Coin3D `SbRotation` via pivy for custom camera angles. Added 4 angled hero shots (35/25 deg, -35/25 deg, 30/10 deg, 150/35 deg yaw/pitch). (5) New `animate_assembly.FCMacro`: 13-step frame-by-frame assembly with cosine ease-in-out, auto-assembles GIF via ffmpeg. (6) New `freecad-mk2-design.md`: 12-component design breakdown with isolated renders, specs tables, assembly order, and 6 pain-point case studies. (7) New `build-render-tool.md` in Tools section. (8) New `hardware-design/README.md`. (9) Blog post covering the render tool and design doc. (10) Website home page updated with 6 validated render images (hero, angled, exploded, opaque, cover-removed, sensors). 40+ assembly renders + 14 component portraits generated.
- **Layman summary:** Built a fancy interactive menu tool that lets you pick which FreeCAD model file to render, choose what views you want (everything, just one component, exploded, animation, etc.), set the quality and background style, and then it opens FreeCAD and takes all the screenshots automatically. Fixed a bunch of blank screenshots caused by the tool trying to capture before FreeCAD finished drawing. Also fixed the joystick anchor going through the circuit board (shortened it to stop exactly at the board surface), widened the screen slot by 0.2 mm so the display fits, and adjusted the cradle dimensions for better Pico clearance. Wrote a complete breakdown of every part in the 3D model with renders and specs tables, plus a blog post and tool documentation. Updated the website front page with proper working images.
- **Files:**
  - `hardware-design/build_and_render.sh` (new) — interactive render CLI with 19 presets, pivy camera angles, top_objects() fix, flush() timing fix
  - `hardware-design/README.md` (new) — render tool documentation
  - `hardware-design/freecad-mk2/render_views.FCMacro` — comprehensive 27-view render macro with DILDER_FCSTD env var support
  - `hardware-design/freecad-mk2/animate_assembly.FCMacro` (new) — 13-step assembly animation
  - `hardware-design/freecad-mk2/dilder_rev2_mk2.FCMacro` — anchor depth 10->6.85, removed fillets, removed PicoRetentionBlock, cradle plug_x0 3.3->3.1, disp_xl 65.0->65.2
  - `hardware-design/renders/var-*.png` (30 files) — fresh assembly renders including angled views
  - `hardware-design/renders/comp-*.png` (14 files) — isolated component portraits
  - `website/docs/docs/hardware/freecad-mk2-design.md` (new) — 12-component design breakdown
  - `website/docs/docs/tools/build-render-tool.md` (new) — render CLI documentation
  - `website/docs/blog/posts/build-render-tool-and-design-doc.md` (new) — blog post
  - `website/docs/index.md` — home page updated with 6 validated render images
  - `website/mkdocs.yml` — nav updated with FreeCAD Mk2 Design + Build & Render Tool pages
  - `website/docs/assets/images/enclosure/` — 64 render PNGs copied from hardware-design/renders
  - `PromptProgression.md` — prompt #268 appended

---

## Prompt #269 — 2026-05-01
- **Prompt sequence:** "the tp4056 needs to be attached to the inlay for it in the assemble on this plane ... we need to expand it by .2mm the to line need to be 17.60mm apart instead of 17.4 also we need to add .4 mm to the length of the cradle topcover and base plate ... move them +x .4mm on the x axis so that we have a bit more room for the pico board to slide the distance between these to face should go from 52.8 to 53.2" -> "work this out in the macro" -> "the distance between these two faces is 52.8 you didnt change this right [Face25/Face53 selections]" -> "the tp4056 is not attached to the right plane it should set flat on [Face69]" -> "there is a slim rectangular extruded lip hanging off the side of the usb platform into the +x axis [Edge43/Edge42] lets trim that off"
- **Input Tokens (est):** ~1,500 across the sequence
- **Output Tokens (est):** ~15,000
- **Commit:** `422dc00` — Widen TP4056 indent, extend enclosure +0.4mm, fix PitWallFill lip
- **Summary:** Five dimensional corrections to the FreeCAD parametric macro. (1) TP4056 indent widened from 17.4 to 17.6mm (`tp_slop` 0.2 -> 0.3) — the printed cradle was too narrow for the USB-C charger module. (2) Enclosure extended +0.4mm on +X axis (`enc_x` 94.5 -> 94.9) to give the Pico board more slide room. All downstream values updated: `plug_x1` 93.0 -> 93.4, `cpx1` 93.2 -> 93.6, pillar origins, cradle flip translate 96.3 -> 96.7, Pico anchor, piezo/IMU centers. (3) PicoNest extended 0.4mm (`pico_nx` 78.8 -> 79.2) so the face-to-face distance between ConnBlock +X and PicoNest +X goes from 52.8 to 53.2mm — the initial enc_x change had moved both faces together. (4) TP4056 module peripheral repositioned to sit flat on Face69 (ConnBlockBayOpen indent floor at global Z=7.0) instead of hanging below the mating surface at Z=4.4. The indent floor after the 180deg Y flip maps from local Z=6.0 to global Z=13-6=7.0. (5) PitWallFill additive boxes trimmed: `fill_x0` changed from `plug_x0-0.1` (3.2) to `plug_x0` (3.3) — the -0.1 overshoot created a 0.1mm lip at global X=93.5 past the plug body face, visible as a thin rectangle hanging off the USB platform side.
- **Layman summary:** Five fixes to the 3D model dimensions. Made the USB charger slot 0.2mm wider because the printed version was too tight. Extended the whole case by 0.4mm on one end so the Pico circuit board has more room to slide in. Made the internal cavity 0.4mm longer to match. Moved the charger module visualization to sit flat on the correct shelf instead of floating below. Trimmed a hair-thin lip of plastic (0.1mm) that was sticking out past the case wall at the USB end — caused by an additive fill feature overshooting the body boundary.
- **Files:**
  - `hardware-design/freecad-mk2/dilder_rev2_mk2.FCMacro` — tp_slop 0.2->0.3, enc_x 94.5->94.9, plug_x1 93.0->93.4, cpx1 93.2->93.6, pico_nx 78.8->79.2, cradle translate 96.3->96.7, TP4056 placement Z fix, PitWallFill fill_x0 trim
  - `hardware-design/freecad-mk2/Dilder_Rev2_Mk2.FCStd` — re-saved with changes
  - `hardware-design/freecad-mk2/Dilder_Rev2_Mk2 .4mm extension fixed lip and curved the thumbstick.FCStd` (new) — iteration snapshot
  - `hardware-design/freecad-mk2/*.3mf` (4 new) — AAACradle, BasePlate, Thumbpiece, TopCover exports
  - `tools/design-tracker/.design-tracker/history.json` — snapshot #2 added

---

## Prompt #270 — 2026-05-01
- **Prompt sequence:** "lets revamp the python design-tracker.py we need a gui with all the options and docs and guide to using it and each menu option and description along with table to see the freecad models made and the 3mf files created and a way to link a print with a render and the freecad file use and package them together in a folder for easy tracking and a way to attach a md file to indicate the changes that occurred on each print and an interface to see the renders and also attach camera pics of the printout" -> "update the testing and take new screenshots when done and also update the documentation with a full walkthrough as well" -> "ok update the website with this new doc replace what was there and add a blog posting for it commit and push all the changes and then update prompts file include commit hashes to the appropriate changes and commit and push"
- **Input Tokens (est):** ~800 across the sequence
- **Output Tokens (est):** ~30,000
- **Commit:** `5229edf` — Design Tracker v2.0 GUI revamp with packages, render gallery, and docs
- **Summary:** Complete rewrite of `design-tracker.py` from a 7-option CLI menu to a full Tkinter GUI (1,870 lines) with 6 tabs. (1) Dashboard: live stats panel (git hash, FCStd/3MF/render/snapshot/print counts), merged timeline with color-coded entries (green snapshots, magenta prints, orange packages), Take Snapshot/Refresh/Compare actions. (2) Models & Exports: side-by-side Treeview tables of all FCStd files (with MD5 hashes) and all 3MF exports, sorted by modification date. (3) Prints: Log New Print dialog (description, result combo, notes, 3MF file multi-select, camera photo attachment), Attach Photo to existing prints, detail panel showing full metadata. (4) Renders: gallery list of all PNGs from `hardware-design/renders/` with a live Pillow-based image preview pane. (5) Packages: Create Package dialog that bundles a FreeCAD model, selected 3MF exports, render images, camera photos, and a changelog into a tracked folder under `.design-tracker/packages/` with a `CHANGES.md` manifest; link to snapshot and/or print entries. (6) Guide: scrollable built-in reference covering every tab, the design-print-review workflow, naming conventions, and CLI commands. Theme: Catppuccin Mocha matching DesignTool. CLI preserved via `--cli` flag. Took 4 Spectacle screenshots (dashboard, models-exports, renders, guide) saved to `tools/design-tracker/screenshots/` and `website/docs/assets/images/tools/design-tracker/`. Replaced website tool doc with full walkthrough including Mermaid workflow diagram. New blog post covering the v1→v2 evolution, tab descriptions, and package system.
- **Layman summary:** Rebuilt the design tracking tool from a text-only terminal menu into a proper desktop app with tabs. Now you can see all your FreeCAD models and 3D print files in tables, browse render images with live preview, log every print attempt with photos of the physical result, and bundle everything (model files, print files, screenshots, photos, and change notes) into organized folders. The old terminal commands still work if you prefer typing. Took screenshots of every tab, updated the website documentation with a full walkthrough, and wrote a blog post about the upgrade.
- **Files:**
  - `tools/design-tracker/design-tracker.py` — complete rewrite: 469 lines CLI → 1,870 lines GUI + CLI
  - `tools/design-tracker/README.md` — rewritten with screenshots, walkthrough, file structure
  - `tools/design-tracker/screenshots/{dashboard,models-exports,renders,guide}.png` (4 new) — GUI screenshots
  - `website/docs/docs/tools/design-tracker.md` — replaced with v2.0 doc: 6-tab walkthrough, Mermaid workflow, package system
  - `website/docs/blog/posts/design-tracker-v2-gui-revamp.md` (new) — blog post covering the CLI-to-GUI rewrite
  - `website/docs/assets/images/tools/design-tracker/{dashboard,models-exports,renders-gallery,guide}.png` (4 new) — screenshots for website
  - `PromptProgression.md` — prompts #269-#270 appended

---

## Prompt #271 — 2026-05-01
- **Prompt sequence:** "put the devtool oin the tools folder and update any references that may break and and filepaths that are relative to this as well"
- **Input Tokens (est):** ~50
- **Output Tokens (est):** ~3,500
- **Commit:** `a7a1eab` — Move DevTool to tools/devtool/ and update path references
- **Summary:** Relocated `DevTool/` to `tools/devtool/` so the firmware companion app sits alongside the other tools (`build-render`, `design-tracker`, `designtool`). Used `git mv` to preserve rename history. The internal `PROJECT_ROOT` calculation in `tools/devtool/devtool.py` was extended from `Path(__file__).parent.parent` to `parent.parent.parent` to compensate for the extra nesting level — verified that it still resolves to the repo root and locates `assets/`, `dev-setup/`, and `firmware/`. Path references updated in: `testing/conftest.py` (sys.path insert), `testing/devtool/conftest.py` (`spec_from_file_location` source path), `dev-setup/mood-selector/generate_quotes.py` and `dev-setup/joystick-mood-selector/generate_quotes.py` (sys.path + devtool_path constants), `setup.py` line 1710 (launch banner), `tools/README.md` (table link, paths, quick-start), root `README.md` (Phase 1 link), `tools/devtool/README.md` (cd command, launch command, architecture diagram), and `docs/programs-guide.md` (launch hint). Historical content in `PromptProgression.md`, `website/docs/prompts/index.md`, blog posts, and the auto-generated `website/site/` build output was deliberately left untouched. All touched Python files compile cleanly via `py_compile`.
- **Layman summary:** Moved the firmware development tool's folder to live next to the other project tools and rewired every place in the codebase that pointed at the old location. The script that figures out where the project root lives needed a one-line tweak to walk up an extra folder. Tests, helper scripts, and documentation that mentioned the old path were all updated. Old historical files like the change log and blog posts kept their original wording so the history stays accurate.
- **Files:**
  - `DevTool/` → `tools/devtool/` (3 files renamed via `git mv`: `devtool.py`, `README.md`, `requirements.txt`)
  - `tools/devtool/devtool.py` — `PROJECT_ROOT = Path(__file__).parent.parent.parent.resolve()`, usage docstring updated
  - `tools/devtool/README.md` — cd command, launch command, architecture diagram updated to `tools/devtool/`
  - `setup.py` — checkpoint banner launch line updated
  - `testing/conftest.py` — `sys.path.insert(0, str(PROJECT_ROOT / "tools" / "devtool"))`
  - `testing/devtool/conftest.py` — module loader path updated, docstring corrected
  - `dev-setup/mood-selector/generate_quotes.py`, `dev-setup/joystick-mood-selector/generate_quotes.py` — relative paths walked up to `tools/devtool/`
  - `tools/README.md` — table link, command paths, quick-start updated
  - `README.md` — Phase 1 DevTool link
  - `docs/programs-guide.md` — launch hint
- **Related commit (context):** `4439d5c` — Reorganize hardware-design layout and prune obsolete CAD assets (groundwork for the new `PCB Designs/Dilder Full Board/` workspace; also moved `joystick-pcb-by-hand/` under `PCB Designs/`)

---

## Prompt #272 — 2026-05-01
- **Prompt sequence:** "/home/rompasaurus/CodingProjects/Dilder/hardware-design/PCB Designs/Dilder Full Board/ ok we are going to work out of this folder and start designing a board for all the planned component to be embedded onto to start this process we need to compile a set of open pcb design for each components availble to lok at in kicad so that their component can be mapped into a all in one boarde make a md file to compile the list of planned components adn there schematics and give me a guide on how to take existing board designs and import them into my own kicad project retainign the schematic and wiring requirments" -> "not quite the components llist i wanted look at the freecad macro you made body models for all the components i need so let use that as the list rewreite this to update it" -> "ok lets divide describe and commit this and updaate the blog with this doc and plan commit and push and update prompts fix spelling and link the git hashes commit and push"
- **Input Tokens (est):** ~700 across the sequence
- **Output Tokens (est):** ~14,000
- **Commit:** `3acb691` — Add Dilder Full Board component reference and KiCad import guide
- **Summary:** Created `hardware-design/PCB Designs/Dilder Full Board/COMPONENTS-AND-IMPORT-GUIDE.md` (307 lines) as the kickoff document for the all-in-one PCB. First draft pulled the component list from `BOM.md` (v0.3 ESP32-S3 design); user redirected to use `hardware-design/freecad-mk2/dilder_rev2_mk2.FCMacro` as the source of truth, since the FreeCAD macro reflects what the printed enclosure is actually shaped around. Rewrote against the macro's `add_pico_with_headers`, `add_joystick_pcb`, `add_peripherals` (TP4056 module, AAA cells, battery clip kit, e-paper module), `add_imu_module`, `add_piezo_speaker`, `add_solar_panel`, and `build_thumbpiece` calls. Each of the 10 component bodies is mapped to one or more KiCad reference projects already cloned under `hardware-design/reference-boards/` and `hardware-design/examples/` (Pico WH/Pico 2 reverse-engineered schematics, BitwiseAjeet TP4056 reference, KLP-5e hierarchical sensors sheet, Ducky e-paper SPI reference, the existing `joystick-pcb-by-hand` project). Documented KiCad's four import mechanisms (Append Schematic, hierarchical sub-sheet, copy/paste, library-only) with what gets preserved vs. broken in each. Flagged the **module-on-headers vs. bare-IC** asymmetry between the macro (Pico 2 W on 2×20 headers) and the BOM (bare ESP32-S3-WROOM-1) so the schematic direction is settled before importing. Proposed a five-sheet schematic layout (`pico` / `power` / `sensors` / `display` / `io`) tied together with hierarchical labels. Wrote a companion blog post at `website/docs/blog/posts/dilder-full-board-kickoff.md` covering the same ground in narrative form.
- **Layman summary:** Started the all-in-one circuit board for Dilder. Wrote a markdown file that lists every part the case is shaped around (Pico, joystick board, charger, batteries, solar panel, IMU, piezo, e-paper) and points to a working KiCad project on disk that shows how to wire each one. Also wrote a step-by-step guide for the four ways to copy circuits between KiCad projects without breaking the wiring. Spotted a mismatch between two earlier plans — one assumed a bare ESP32 chip, the other (the actual 3D-printed case) uses a Pico module on header pins — and locked in the Pico-on-headers direction since the case is committed to it. Sketched out splitting the schematic into five separate pages (Pico, power, sensors, display, I/O) so the work stays manageable. Wrote a blog post explaining the same thing in plain English.
- **Files:**
  - `hardware-design/PCB Designs/Dilder Full Board/COMPONENTS-AND-IMPORT-GUIDE.md` (new) — 10-component reference map + 4-mechanism KiCad import playbook + 5-sheet schematic plan
  - `website/docs/blog/posts/dilder-full-board-kickoff.md` (new) — companion blog post
  - `PromptProgression.md`, `website/docs/prompts/index.md` — prompts #271-#272 appended with linked commit hashes
- **Related commits (context):**
  - `4439d5c` — folder and joystick relocation under `hardware-design/PCB Designs/` made room for this workspace
  - `a7a1eab` — Prompt #271 (DevTool move that preceded this work in the same session)

---

## Prompt #273 — 2026-05-02
- **Prompt sequence:** "ok summarize the staged changes update the documens and provide renders with the lates freecad file modified add it to the site as a lternative design update the docs and blog and I added heic pics to the root describe them follown pic descript stucture be detailed in description and convert to jpeg and put in the correct folders then update the fron home page with the choice pictures of the lates hardware progression then also update the docs and docs on the page and the hardware evolution as well note that the unit is solder and power via batter and usb charging works attach the pics to the pertinant docs as well commit and push then update prompts fix spelling and attach the commit hashes and commit and push"
- **Input Tokens (est):** ~200
- **Output Tokens (est):** ~25,000
- **Commit:** `2f33b2d` — Add NoSolar variant, soldered unit photos, and hardware docs update
- **Summary:** Multi-step documentation and media pipeline: converted 10 HEIC photos from root to JPEG with descriptive filenames, categorized and placed in `website/docs/assets/images/hardware/` and `website/docs/assets/images/enclosure/rev2-nosolar/`. Photos cover the full hardware progression: 3D-printed parts storage (2 photos), first battery power-on with e-ink display running (3 photos), NoSolar variant case open/closed/charging (3 photos), fully assembled unit running Conspiratorial Octopus (1 photo), solar variant back view for comparison (1 photo). Added the NoSolar FreeCAD variant as an alternative design with new blog post (`nosolar-variant-first-power.md`) documenting the variant differences, build session, and first power-on. Updated home page (`index.md`) with latest hardware progression photos replacing/augmenting the existing current build section, updated phase status to reflect soldered unit and battery power milestones, corrected blog/prompt counts. Updated `design-evolution.md` with two new sections (Soldered Unit + NoSolar Variant) including all 10 photos with detailed alt text, variant comparison table, and 4 new version history entries. The NoSolar macro (`dilder_rev2_mk2_no_solar.FCMacro`), FCStd, and 5 pre-exported 3MF files were already staged from user's manual work.
- **Layman summary:** Took 10 raw iPhone photos showing the Dilder being built, soldered, and powered on for the first time. Converted them from Apple's HEIC format to standard JPEG, gave each a descriptive filename, and sorted them into the right website folders. Created a blog post about the new "no solar panel" case variant. Updated the home page with the best new photos showing the device actually running. Updated the hardware evolution documentation with full write-ups of the soldering milestone and the NoSolar alternative design. All the FreeCAD model files and 3D print exports for the new variant were already staged.
- **Files:**
  - `website/docs/assets/images/hardware/first-battery-power-display-on.jpg` (new) — first battery power-on, display showing Sassy Octopus
  - `website/docs/assets/images/hardware/first-battery-power-side-view.jpg` (new) — side view of soldered unit with battery and charger
  - `website/docs/assets/images/hardware/soldered-unit-battery-cradle.jpg` (new) — close-up of solder joints, Pico W, TP4056, 10440 cell in cradle
  - `website/docs/assets/images/hardware/fully-assembled-display-running.jpg` (new) — Conspiratorial Octopus running on fully assembled NoSolar unit
  - `website/docs/assets/images/hardware/build-session/printed-parts-storage-close.jpg` (new) — 3D-printed parts in printer storage drawer, close view
  - `website/docs/assets/images/hardware/build-session/printed-parts-storage-wide.jpg` (new) — storage drawer unit wide angle
  - `website/docs/assets/images/enclosure/rev2-nosolar/nosolar-open-internals-top-view.jpg` (new) — NoSolar case opened showing internals
  - `website/docs/assets/images/enclosure/rev2-nosolar/nosolar-base-and-unit-usb-charging.jpg` (new) — NoSolar variant assembled, USB charging
  - `website/docs/assets/images/enclosure/rev2-nosolar/nosolar-base-and-unit-wide-view.jpg` (new) — NoSolar variant wide view on bench
  - `website/docs/assets/images/enclosure/rev2-nosolar/solar-variant-back-view.jpg` (new) — solar variant back showing AK 62x36mm panel
  - `website/docs/blog/posts/nosolar-variant-first-power.md` (new) — blog post: NoSolar variant first power-on
  - `website/docs/index.md` — home page updated with 6 new hardware progression photos, phase status updated (soldered, battery, USB charging, NoSolar), blog/prompt counts corrected
  - `website/docs/docs/hardware/design-evolution.md` — two new sections (Soldered Unit, NoSolar Variant) with photos, comparison table, 4 version history entries, intro text updated
  - `hardware-design/freecad-mk2/dilder_rev2_mk2_no_solar.FCMacro` (new) — NoSolar variant FreeCAD macro
  - `hardware-design/freecad-mk2/Dilder_Rev2_Mk2_NoSolar.FCStd` (new) — NoSolar variant FreeCAD document
  - `hardware-design/freecad-mk2/Dilder_Rev2_Mk2_NoSolar-*.3mf` (5 new) — pre-exported 3MF parts
  - `hardware-design/freecad-mk2/Dilder_Rev2_Mk2-without solar panel.FCStd` (new) — iteration snapshot
  - `hardware-design/freecad-mk2/dilder_rev2_mk2.FCMacro` — minor modification
  - `hardware-design/freecad-mk2/DilderFull Case Print out 29.04.3mf` — updated print export

---

## Prompt #274 — 2026-05-03
- **Prompt sequence:** "ok let update the dilder home page and make a new idea concept for the game play loop encorporating proximity detection dilder sholud make a uniques noise or action when another dilder is encountered in proximity and a collectible item can be received further there can be collectable geocaching challenges wher the user is given a dridldle and approximate location to find a collectable electronic physical gift of some sort this could play into a marketing router to get people interested in the device"
- **Input Tokens (est):** ~150
- **Output Tokens (est):** ~30,000
- **Commit:** `6185e50` — Add Dilder Encounters, Geocaching & Collectibles gameplay concept
- **Summary:** Designed a three-layer gameplay and marketing system extending the existing peer discovery BLE protocol and treasure hunt system. (1) **Proximity Encounters ("Dilder Meet")**: when two Dilders detect each other via BLE (~10-30m range), each plays *the other's* unique 3-note piezo chime (generated from device_id hash — 16^3 = 4,096 unique melodies), shows an encounter screen (pet name, emotion, evolution form, encounter count), awards +25 XP / +15 happiness, and optionally offers a collectible for trade via joystick. 24-hour per-device cooldown, 5/day cap, 256-entry encounter log (2KB flash). Extended GATT payload (26 bytes) for rich data exchange beyond the 13-byte advertising packet. (2) **Riddle Hunts (Geocaching)**: curated real-world geocaching challenges where the device displays a text riddle hinting at an approximate location (~200m radius). Physical weatherproof capsules at each location contain an NTAG215 NFC tag ($0.30) and a tiered electronic component prize: Common (LED packs, $0.50-1), Uncommon (breadboards, $1-2), Rare (NeoPixel rings, $3-5), Legendary (Pico W boards, $5-15), Mythic (pre-assembled Dilder, $15-40). Tap-to-collect via NFC reader (PN532, ~$3) or QR/code fallback. Cache Keeper community program for placing/maintaining caches with starter kits and exclusive cosmetics. (3) **Collectible Ecosystem**: digital collectibles (cosmetics, sound packs, personality fragments, genome traits, lore fragments) earned from encounters/hunts/achievements, with real trading during encounters (items fully transfer — genuine scarcity). Collection Journal UI with completion tracking. (4) **Marketing Viral Loop**: chime creates public curiosity → owner demonstrates encounter → bystander wants one → GitHub (free) or Patreon (kits) → more Dilders = more encounters = network effect. Patreon tiers ($0 free / $5 supporter / $15 builder / $30 legendary) integrated with the encounter/cache system. Seeded cache launch strategy: Alpha (Berlin, 10-20 caches) → Beta (5 cities, 50-100) → Community launch (500+ worldwide). Full technical analysis: 5 new firmware modules (~25KB total), 3.3KB flash budget, 0.3 mA avg BLE power overhead (~5% battery impact). Three riddle examples (Berlin, London, Portland). Eight open questions (anti-theft, cache maintenance, legal, accessibility, cold start). Home page updated with new "Encounters, Riddle Hunts & Collectibles" section.
- **Layman summary:** Designed a gameplay system where Dilder devices automatically detect each other in public via Bluetooth and play unique musical chimes as a greeting. Both owners earn rewards and can trade digital collectibles. Also designed a geocaching treasure hunt system where the device shows riddles hinting at real-world locations — find the hidden capsule and you get both a digital unlock and a real electronic component (like LEDs, sensors, or even a complete Dilder). Community members can become "Cache Keepers" who hide and maintain treasure capsules worldwide. The whole system doubles as marketing: the chime creates curiosity in public, encounters demonstrate the product, and the device becomes more valuable as more people own one.
- **Files:**
  - `Gamplay Planning/14-encounters-geocaching-collectibles.md` (new) — full design doc: encounter protocol, chime generation, riddle hunt system, capsule tiers, NFC tap-to-collect, Cache Keeper program, marketing viral loop, revenue tiers, technical requirements, flash/power budgets, riddle examples, open questions
  - `website/docs/blog/posts/encounters-geocaching-collectibles.md` (new) — blog post covering the three-layer system in narrative form
  - `website/docs/docs/design/encounters-geocaching.md` (new) — website design doc with packet specs, UI mockups, tables, implementation phases
  - `website/docs/index.md` — new "Encounters, Riddle Hunts & Collectibles" section on home page with encounter/riddle/trading overview
  - `website/mkdocs.yml` — nav updated with Encounters & Geocaching under Design

---

## Prompt #275 — 2026-05-05
- **Prompt sequence:** "how would I go about easily update the program code and firmware for the pico 2 can I do this wirelessly it is tiring to connect usb and hit boot select" -> "lets do the picowota route lets make a new tab in the dev tool and implement a deployment and update process" -> "I also want the devtool to retain my wifi config on reload" -> "the firmware list you made is washed out white background I cant read it at all" -> "also the ota setup guide you made is confusing what does the build bootloader and flash bootloader do" -> "also I need this to be specific to the pico 2 w board ensure that is clear on the tab title" -> [multiple debugging rounds for picowota build: CMSIS header RP2350 fix, disable_interrupts rename, SSID quoting fix, SDK path discovery, stale build cleanup] -> "still not found after proper flash" -> "the pico never reboot after the flash" -> "ok its there now that worked now how do I push the program on this thing" -> "permission denied when trying a clean build and flash" -> [picowota flash failed: INFO returns garbage addresses, ERASE returns ERR on RP2350] -> "get me a picotool added to the devtool as a tab" -> "give me a script to install the dependencies in the root" -> "give that in the devtool as well to install the dep if not exists" -> "have it launch like this by default I dont want to type args I will forget" -> "ok tried the sound program cant get any sound" -> "sorry pin 11" -> "10 is already taken" -> "with the waveshare" -> "lets do pin 20" -> "fix sound on both programs and fix the wifi too" -> "give a menu option for the sound at the bottom I can navigate to and for the wifi with a back button" -> "yea build it into a new program I can test" -> "permission denied when trying to deploy" -> "do I need a resistor for this?" -> "still really faint with resistor will more ohm equal louder?" -> "would this work?" [active buzzer link] -> "ok ordered lets work a bit more on dilder hub I want it to be able to select all the moods" -> "permission denied the log error shows in the 3 box" -> "ok the emotion program should show at the bottom not dilder hub also when I change the emotion on the menu it should return back to the octopus" -> "we still have flashing on this display please let utilize the partial refresh like the display is specced for" -> "the v4 screen is what I'm using" -> "perfection!!!! write a detailed md document and blog entry for this" -> "alright commit and push the change gitignore the build nonsense make sure my wifi pw isnt put in the repo update the site and docs"
- **Input Tokens (est):** ~5,000 across the sequence
- **Output Tokens (est):** ~150,000
- **Commits:**
  - `f57f2fb` — Add OTA Update tab to DevTool with picowota WiFi bootloader integration
  - `8460184` — Add full firmware list and clean build + OTA flash to DevTool OTA tab
  - `8ead4d3` — Persist OTA WiFi config, fix Treeview dark theme, rewrite guide
  - `409bdd8` — Rename OTA tab to 'Pico 2 W OTA' and make board-specific
  - `d119710` — Fix OTA bootloader build: SDK path discovery, error logging, stale cache
  - `8578da4` — Patch picowota for Pico 2 W (RP2350) and fix OTA build flow
  - `3fe68d4` — Auto-discover firmware projects in OTA tab
  - `a1816c0` — Fix find_rpi_rp2_mount() call
  - `b40ba8c` — Fix picowota SSID with spaces
  - `cbfc503` — Fix RP2350 RTC compat and add missing firmware
  - `ec1f20c` — Default board selector to Pico 2 W (RP2350)
  - `b587a2f` — Force picowota bootloader to build as pico_w (RP2040 compat mode)
  - `55c23d8` — Fix picowota SSID quoting that broke WiFi
  - `ea3d908` — Add Picotool tab to DevTool — USB flash without BOOTSEL button
  - `1843655` — Add install-deps.sh for one-command development setup
  - `6e8d5f2` — Add dependency checker and Install All Dependencies button
  - `b64042c` — Fix install-deps.sh: heif-convert to libheif on Arch
  - `2953feb` — Install picotool via AUR on Arch
  - `7005e97` — Auto-eject BOOTSEL drive after flash to trigger Pico reboot
  - `fa84405` — Move speaker pin from GP7 to GP15 in both sound firmwares
  - `31c85f6` — Add Dilder Hub firmware — octopus + joystick menu + speaker + device info
  - `fb69b9f` — Push-pull piezo driver for 2x volume
  - `bf0bc63` — Auto-relaunch DevTool with docker group if not active
  - `150f84b` — Fix permission denied on clean build and lambda NameError
  - `90cb19b` — Dilder Hub v2 — mood selector, WiFi/NTP, network screen, all 823 quotes
  - `57d8939` — WiFi icon on octopus screen + single-pass partial refresh
  - `2437a5e` — WiFi icon left, battery icon right, display variant selector
  - `3552e07` — Fix black flash, battery lightning bolt, menu fits on screen
  - `2e8285f` — Fix V4 display flash, mood tagline, battery info
  - `1c68e71` — Rewrite V4 display driver — V3-style custom LUT partial refresh
  - `b97be53` — Add sprint documentation: blog post, Picotool & OTA guide, Dilder Hub docs
  - `8275da9` — Scrub WiFi credentials and simplify .gitignore
- **Summary:** Massive development sprint across firmware updates, DevTool expansion, and display driver fixes. (1) **OTA/Picotool**: attempted WiFi OTA via picowota — ported to RP2350 (CMSIS header, function rename), built Python TCP client (580 lines), added DevTool tab with WiFi config persistence, device discovery, firmware list. Discovered picowota's flash operations don't work on RP2350 due to hardware abstraction differences. Pivoted to picotool (Tab 9) for BOOTSEL-free USB flashing with auto-eject. (2) **Dilder Hub firmware**: new combined firmware (1,935 lines) with animated octopus (823 quotes, 16 moods), joystick menu system (6 states), mood selector, WiFi/NTP network screen with on/off toggle, sound test, device info with battery voltage, push-pull piezo driver (GP14+GP15 opposite phase, 6.6Vpp). (3) **V4 display driver**: traced flicker root cause through 6 iterations — the SSD1680's internal OTP LUT has no proper partial waveform. Complete rewrite using the V3's custom 159-byte partial LUT (WF_PARTIAL) with RAM ping-pong and 0x0F trigger. Zero flicker, only changed pixels update. (4) **Dev workflow**: install-deps.sh for one-command setup, Docker group auto-detection, display variant selector in toolbar, auto-discover firmware projects. (5) **Documentation**: blog post covering the full sprint narrative, Picotool & OTA reference guide, Dilder Hub firmware docs. WiFi credentials scrubbed, .gitignore simplified with glob patterns.
- **Layman summary:** Started by trying to eliminate the annoying USB plug-unplug cycle for firmware updates. First tried wireless updates over WiFi — got it connecting but the actual flash writing didn't work on the newer Pico 2 W chip. Switched to a simpler approach using picotool which reboots the device over USB without pressing buttons. Built a combined firmware that shows an animated octopus with 16 different moods you can switch between using a joystick menu, connects to WiFi to get the real time, plays sounds through a tiny speaker, and shows battery status. Fixed the e-ink display flashing problem that had been plaguing the project — the screen was doing a full black refresh every few seconds instead of just updating the pixels that changed. The fix was loading a custom display waveform that only drives changed pixels. Added complete documentation covering everything built.
- **Files:**
  - `tools/devtool/devtool.py` — 3 new tabs (OTA, Picotool, display selector), Docker group auto-relaunch, dependency checker, firmware auto-discovery
  - `tools/devtool/picowota_client.py` (new) — Python TCP client for picowota protocol
  - `dev-setup/dilder-hub/` (new) — combined firmware: main.c, CMakeLists.txt, wifi_config.h, lwipopts.h, quotes.h
  - `dev-setup/hello-world/lib/e-Paper/EPD_2in13_V4.c` — complete rewrite with V3 custom LUT
  - `dev-setup/moodselector-sound/main.c` — speaker pin GP7 to GP15
  - `dev-setup/moodselector-sound-wifi/main.c` — speaker pin + RTC compat
  - `dev-setup/docker-compose.yml` — dilder-hub service added
  - `install-deps.sh` (new) — one-command dev setup for Arch/Debian/Fedora
  - `picowota/` — submodule with RP2350 patches (CMSIS, disable_interrupts, SSID quoting)
  - `.gitignore` — simplified with glob patterns, WiFi creds excluded
  - `website/docs/blog/posts/devtool-ota-display-hub-sprint.md` (new) — sprint blog post
  - `website/docs/docs/tools/picotool-ota.md` (new) — Picotool & OTA reference
  - `website/docs/docs/software/dilder-hub.md` (new) — Dilder Hub firmware docs
  - `website/mkdocs.yml` — nav updated with new pages

---

### Prompt #276 — Testbench Hardware Session: WiFi Scan, Sound Patterns, MPU-6050, Active Buzzer

- **Date:** 2026-05-07
- **Model:** Claude Opus 4.6 (1M context)
- **Tokens:** ~80,000+ (extended multi-turn session)
- **Commits:**
  - `ff836b7` — Dilder Hub: WiFi scan/keyboard, sound patterns, MPU-6050, active buzzer
- **What happened:** Hands-on testbench session wiring and integrating multiple hardware components into the Dilder Hub firmware. Iterative debugging with real hardware feedback.
- **Hardware changes:**
  - Moved Waveshare VCC from VSYS (pin 39) to 3V3(OUT) (pin 36) to free VSYS for TP4056 charger board
  - Wired TP4056 USB-C charger module (OUT+ to VSYS, OUT- to GND) — battery voltage now reads correctly
  - Replaced passive piezo with active buzzer on GP14 — fixed screaming bug caused by PWM inverted polarity
  - Wired MPU-6050 accelerometer/gyroscope via I2C0 (SDA=GP0, SCL=GP1) — auto-detects at 0x68 or 0x69
- **Firmware additions:**
  - Fixed `cyw43_arch_gpio_get` API call (1 arg, returns bool directly)
  - CYW43 initialized at boot for battery VSYS sensing (GPIO 29 shared with CYW43 SPI)
  - Active buzzer GPIO driver replacing PWM piezo code
  - 6 sound patterns (beep, chirp, SOS, doorbell, alert, happy) with volume control
  - WiFi submenu: on/off toggle, async network scanning, scrollable results list
  - On-screen keyboard: 4x10 QWERTY grid + 5 special keys (SHIFT, SPC, DEL, DONE, CANCEL)
  - `wifi_connect_to(ssid, password)` — connect to any network, not just hardcoded credentials
  - MPU-6050 I2C driver with burst read, auto-detect, error checking
  - Motion menu: live accel/gyro values, pedometer, tilt angles, temperature, I2C bus scanner
  - Input debounce reduced from 200ms to 5ms, poll interval from 20ms to 5ms
  - All menus now scroll when items exceed visible area
- **New documentation:**
  - `docs/mpu6050-wiring-guide.md` — full wiring table, pin map, I2C details, register reference
  - `hardware-design/power-consumption-report.md` — 4 power scenarios (34-260mA), 8 reduction strategies, battery life projections (29h to 10 days), solar viability analysis
  - `docs/session-2026-05-07-implementation.md` — complete session implementation recap
- **Design notes:** TP4056 CHRG/STDBY pins to GPIOs deferred to full board PCB design for USB-C charge detection (CYW43 VBUS only detects Pico's own USB port)
- **Files:**
  - `dev-setup/dilder-hub/main.c` — +959/-125 lines (all firmware features)
  - `dev-setup/dilder-hub/CMakeLists.txt` — added hardware_i2c
  - `docs/mpu6050-wiring-guide.md` (new)
  - `docs/session-2026-05-07-implementation.md` (new)
  - `hardware-design/power-consumption-report.md` (new)
  - `README.md` — updated hardware table, phase checklists, content links
  - `website/docs/docs/software/dilder-hub.md` — updated features, menus, wiring, all new screens
  - `PromptProgression.md` — entry for #276

---

## Prompt #277 — 2026-05-08
- **Prompt sequence:** "ok we are going to look at the latest macro we made with the buzzer the cutout is looking good but lets get rid of the hole on the base plate we are going to instead need to route the sound through the side of the top cover lets get a pit on the cradle where the speaker rest on the cradle and channel it in to a small hole on the top cover side the channel we make starts exactly at the center of the speaker cutout and head to the x origin direction through the top cover" -> "then when that's done we need to extend the height of the base plate sides and the usb hole and platform 5mm so we can have room to route cables n such and we need a circle to surround the speaker so it can rest in place there as well" -> "thats a great start now we need to adjust where the wires come out of the speaker the end with the wires will be resting on the base plate so we need 2 indent channels there that gap into the circle cutout as well let's change that and also the accelerometer board is 20mm by 15.6 mm let's adjust the cutout for it on the base plate for those dimensions also there are 2 3mm holes on the corners of the board long side let's add 2 3mm pegs in the 2 corners for it to set on top of and give me 2 square peg washer for it to snap into on top separately" -> "the center of the holes on the accel board are about 15mm apart" -> "cut the holes out of the model and make the assembly reflect that with the washer inserts as well" -> "it's solid but the speaker cable isn't cutting into the base plate then move the speaker up the z axis 2mm and let it cut into the cradle more to compensate" -> "we have hole cutouts on the base plate still everything else looks good just get rid of the hole defined by the lines I share" -> "ok let's commit these changes and update the docs and notes and todos and push then update the prompts with what we did here and attach the commit hashes in the right places then commit and push"
- **Input Tokens (est):** ~1,400 across the sequence
- **Output Tokens (est):** ~50,000
- **Commits:**
  - `fdadd83` — Sound routing redesign: lateral channel, taller base, IMU pegs
  - `ce4bb05` — Update TODO and prompt logs for the no-solar-buzzer overhaul
- **Summary:** Major no-solar-buzzer enclosure overhaul across 7 design iterations on `dilder_rev2_mk2_no_solar_buzzer.FCMacro`. (1) **Sound routing flipped from vertical to lateral**: removed the 2 mm `BuzzerSoundPort` through-floor cut; modified the cradle's `BuzzerPocket` to be shallow (1.2 mm → 3.2 mm tall after the +2 mm speaker lift) so the speaker top seats against the pocket ceiling; added `BuzzerSoundPit` (2 mm vertical cylinder above pocket ceiling) and `BuzzerSoundChannel` (R=1 horizontal cylinder along -X global axis); added a matching `BuzzerSoundChannel` cut through the cover's -X wall so sound exits through a small hole on the side. The cover's `BuzzerWallPocket` was reshaped (4.1 → 6.1 mm tall) to clear the new lateral channel. (2) **Base plate sides extended +5 mm** (`bp_h` 4.0 → 9.0): updated `Z`, `Z_preshave` in `build_base_plate`; cascaded `bp_top` and `PICO_ANCHOR_Z_GLOBAL` to 9.0; rewrote hardcoded cradle Z (`11.0` → `16.0`) and cover Z (`9.0` → `14.0`) in peripherals (`cell_z_g`, `tp_z_bot_g`, `disp_z_back_g`, `pocket_floor_g`, `cover_top_z`); updated stale 18.1 cradle plug_bot Z to 21.1 in joystick PCB pit code. USB-C cutout and platform automatically tracked up 5 mm via `Z_preshave`. (3) **Speaker containment**: added `BuzzerCradleRing` (additive 14 mm OD cylinder, 5 mm tall) on the base plate floor before `BuzzerNest` cut — leaves a 0.9 mm-thick retaining ring around the speaker. (4) **Speaker lifted +2 mm in Z** (`buzz_z_bot_g` 0.6 → 2.6) so the wire end face has a 2 mm gap to the floor for the wires to route in; deepened cradle `BuzzerPocket` 2 mm to compensate (`pocket_ceil_z` 5.9 → 3.9 in cradle local). (5) **Wire pass-through notches**: 2× `BuzzerWireChannel_Plus`/`_Minus` SubtractiveBoxes, 1.5 mm wide, at Y = `buzz_cy ± 2.0`, running X = 3 → 18; iterated bottom Z from -0.1 (cut floor) to `floor_z` (0.6) after the user reported through-holes appearing on the base plate underside — now they only notch the lower ring wall. (6) **IMU pocket dimensions** updated from 21×16 → 20×15.6 mm to match the actual MPU-6050 board; added `imu_hole_spacing = 15.0` and `imu_hole_y_inset = 2.0` parameters. (7) **2 corner mounting pegs** (`IMUPeg_MX`/`_PX`): 2.8 mm OD additive cylinders rising from the IMU pocket floor (Z=0.5) up by 3 mm, positioned at `imu_cx ± 7.5` mm on the +Y long edge. (8) **PCB visualization**: cut matching 3 mm through-holes in the IMU PCB at the peg positions in `add_imu_module`. (9) **Separate snap-on washer bodies**: new `build_imu_washer(doc, idx, peg_x, peg_y)` function — square 6×6×1.5 mm plate with 2.7 mm hole (interference fit on the 2.8 mm peg), `IMUPegWasher_MX`/`_PX` instances placed in the assembly above each peg. Top-level docstring rewritten to reflect the new sound path and lifted speaker; ~12 cascading comments updated for the new Z geometry. Macro parses cleanly via `python3 -m ast`.
- **Layman summary:** Reworked the buzzer-equipped Dilder case in seven rounds. Moved the sound exit from a hole on the bottom of the case to a small hole on the side, drilling a tunnel through the speaker cradle and out through the side wall. Made the base plate walls 5 mm taller so wires have somewhere to live inside the case. Added a thin circular wall around the speaker to keep it from sliding around. Lifted the speaker 2 mm higher so its wires (which come out of the bottom face) have a 2 mm gap underneath to route through, then notched the speaker ring so the wires can exit toward the rest of the electronics. Updated the accelerometer board pocket to the right size (20 × 15.6 mm), added two 3 mm pegs in the corners for the board's mounting holes (15 mm apart), and designed two small square washers (printed separately) that snap onto the pegs to hold the board down. Cut matching holes in the on-screen visualization of the board so the assembly preview reflects the real layout. Caught and fixed a bug where the wire channels were cutting through the base plate floor leaving visible holes — moved the cuts up so they only notch the speaker ring.
- **Files:**
  - `hardware-design/freecad-mk2/dilder_rev2_mk2_no_solar_buzzer.FCMacro` — +290/-100 lines: sound routing redesign, base plate +5 mm Z extension with cascaded references, BuzzerCradleRing + WireChannels + IMU pegs in build_base_plate; deeper BuzzerPocket + BuzzerSoundPit + BuzzerSoundChannel in build_cradle; BuzzerSoundChannel + extended BuzzerWallPocket in build_top_cover; new build_imu_washer() body builder; updated add_imu_module() with hole cuts; lifted speaker in add_buzzer_module()
  - `hardware-design/freecad-mk2/Dilder_Rev2_Mk2_NoSolar_Buzzer.FCStd` — regenerated FreeCAD document
  - `hardware-design/freecad-mk2/Dilder_Rev2_Mk2_NoSolar_Buzzer-AAACradle_thiccc.3mf` (new) — thicker variant cradle export
  - `hardware-design/freecad-mk2/Dilder_Rev2_Mk2_NoSolar_Buzzer-BasePlate_thiccc.3mf` (new) — thicker variant base plate export
  - `hardware-design/freecad-mk2/Dilder_Rev2_Mk2_NoSolar_Buzzer-IMUPegWasher_PX.3mf` (new) — peg washer 3MF export (single-instance test print)
  - `TODO.md` — Week 4 section added with this session's completed items + open follow-ups
  - `PromptProgression.md` — this entry
  - `website/docs/prompts/index.md` — synced entry for #277

---

## Prompt #278 — 2026-05-08
- **Prompt sequence:** "ok slight mod need lets move the imu peg down 1mm on the y axis both of them, also with the speaker buzzer cradle ring the hole for the wires should be slot in the ring not a hole so that the wire don't have to be fished through the hole so let's extend the hole up the z axis so it cuts through the entirety of the ring" -> "ok commit the changes and add to the notes and docs and push"
- **Input Tokens (est):** ~150
- **Output Tokens (est):** ~3,000
- **Commit:** `312a65b` — Tweak IMU peg Y position and open-top wire channel slots
- **Summary:** Two small follow-up adjustments to the no-solar-buzzer enclosure. (1) **IMU pegs -1 mm Y**: `imu_hole_y_inset` parameter changed 2.0 → 3.0 in three coordinated places — `build_base_plate` (`IMUPeg_MX`/`_PX` placements), `add_imu_module` (PCB through-hole positions), and `main()` (`IMUPegWasher_MX`/`_PX` placements). Net effect: peg/hole/washer Y moves from 28.8 → 27.8 (1 mm closer to the board's center along Y). (2) **Wire channels now open-top slots**: `wire_chan_z_top` raised from `floor_z + 1.6` (Z=2.2) to `floor_z + 5.1` (Z=5.7) so the cut extends through the full 5 mm-tall `BuzzerCradleRing` height. The slots are now open at the top — wires can drop in from above instead of being threaded laterally through a closed hole. Floor remains uncut (`wire_chan_z_bot = floor_z`) so no holes appear on the base plate underside. User regenerated the FCStd and re-exported `BasePlate`, `AAACradle`, `AAACradle_thiccc`, and a new `TopCover_thicccc` 3MF.
- **Layman summary:** Two small tweaks. Moved both accelerometer board mounting pegs 1 mm closer to the middle of the board (the user measured the actual hole positions and they were a bit closer to center than first assumed). Changed the speaker wire channels from short notches near the bottom of the retaining ring to tall open-top slots that go all the way up — now you can just drop the wires into the slots from above instead of having to fish them through a closed-off hole.
- **Files:**
  - `hardware-design/freecad-mk2/dilder_rev2_mk2_no_solar_buzzer.FCMacro` — `imu_hole_y_inset` 2.0 → 3.0 in three places; `wire_chan_z_top` `floor_z + 1.6` → `floor_z + 5.1`; comments updated
  - `hardware-design/freecad-mk2/Dilder_Rev2_Mk2_NoSolar_Buzzer.FCStd` — regenerated FreeCAD document
  - `hardware-design/freecad-mk2/Dilder_Rev2_Mk2_NoSolar_Buzzer-BasePlate.3mf` — re-exported with updated peg + slot geometry
  - `hardware-design/freecad-mk2/Dilder_Rev2_Mk2_NoSolar_Buzzer-AAACradle.3mf` — re-exported
  - `hardware-design/freecad-mk2/Dilder_Rev2_Mk2_NoSolar_Buzzer-AAACradle_thiccc.3mf` — re-exported (thicker variant)
  - `hardware-design/freecad-mk2/Dilder_Rev2_Mk2_NoSolar_Buzzer-TopCover_thicccc.3mf` (new) — top cover thicker variant export
  - `TODO.md` — two tweak items added to Week 4 completed list
  - `PromptProgression.md` — this entry
  - `website/docs/prompts/index.md` — synced entry for #278

---

## Prompt #279 — 2026-05-16
- **Prompt:** "Alright I have made a major advancement on the Dilder progression and have designed a Full Board Rev 1 of the Dilder PCB. I have added several pictures to the folder to note the progression along with a 3D model of the board in KiCad. Look through the Dilder PCB folder and summarize the steps and research taken in a friendly non-technical way and create an MD Rev 1 Dilder Full Board process. Add this to the website and also look at the images I added, rename them to a nice description, and add an entry to the front page marking this milestone. Also update the phase status and indicate the next step is to get this board and solder the extended components and design another FreeCAD case based on the measurements of this board. This is a big step so let's celebrate this on the site. Once done, commit and push these changes to the Dilder site, and update the prompts, fix spelling, and commit and push again."
- **Input Tokens (est):** ~280
- **Output Tokens (est):** ~6,000
- **Commit:** `807877e` — Celebrate Full Board Rev 1 milestone on the site (site + images + blog post + homepage + phase update); follow-up commit for the prompt log itself.
- **Summary:** Major milestone celebration on the Dilder site for **Full Board Rev 1**: schematic complete, 4-layer stackup configured, board routed end-to-end, 3D preview verified. Twelve new images (3D top/bottom/iso renders, front/back silkscreen captures, layout editor screenshot, full schematic screenshot, 4-layer board stackup dialogs, and the e-paper "spaced" fit-check render) were moved out of the repo root and into `website/docs/assets/images/hardware/pcb/full-board-rev1/` with descriptive filenames (`full-board-rev1-3d-top-view.png`, `full-board-rev1-front-silkscreen-dildafication-begins.png`, etc.). A new long-form blog post `dilder-full-board-rev1.md` walks through the seven-step journey in plain language: deciding what's on the board from the FreeCAD model (not the BOM); finding a working reference design for every part; wiring it up in KiCad as a hierarchical schematic; laying it out on a real rectangle; configuring a 4-layer stackup with internal ground and 3.3 V planes; verifying the 3D preview; and test-fitting the e-paper screen above the board. The homepage gained a celebratory milestone banner (with the front/back silkscreen images, the 3D top render, and the screen fit-check render) placed above the existing Mk2 translucent section, plus a "Read the full milestone write-up" button linking into the new post. The Current Phase admonition was upgraded from `info` → `success` and the next steps were rewritten to highlight three concrete follow-ups: **order Full Board Rev 1 from JLCPCB**, **solder the extended components onto the bare board** (USB-C, TP4056, IMU, slide switch, decoupling caps), and **design a new FreeCAD case based on the Full Board measurements** — slimmer, with no leftover internal channels for module wiring.
- **Layman summary:** The Dilder PCB just became a single board for the first time. Renamed twelve screenshots and 3D renders from the KiCad work into a tidy folder with descriptive names, then wrote a friendly tour of the seven steps it took to get there — picking parts off the 3D-printed case (not the old parts list), hunting down reference designs for every chip, drawing the wiring, dragging the parts onto a green rectangle, setting up a fancy 4-layer board sandwich, checking the 3D preview, and test-fitting the screen. Added a celebratory banner to the front page with the prettiest shots and a button linking to the full write-up. Updated the project's status section to reflect the win and to say what's next: order the bare boards, solder the small surface-mount parts onto them, and design a new 3D-printed case measured against this new board.
- **Files:**
  - `website/docs/blog/posts/dilder-full-board-rev1.md` (new) — long-form friendly write-up of the seven steps
  - `website/docs/index.md` — added celebratory milestone section with images + button; rewrote the Current Phase admonition to `success`, new "Done" entry, new in-progress + next-step bullets
  - `website/docs/assets/images/hardware/pcb/full-board-rev1/full-board-rev1-3d-top-view.png` (new, renamed from `3d-pcb-top-view.png`)
  - `website/docs/assets/images/hardware/pcb/full-board-rev1/full-board-rev1-3d-bottom-view.png` (new, renamed from `3d-pcb-bottom-view.png`)
  - `website/docs/assets/images/hardware/pcb/full-board-rev1/full-board-rev1-3d-with-epaper-display-spaced.png` (new, renamed from `Board with screen spaced out.png`)
  - `website/docs/assets/images/hardware/pcb/full-board-rev1/full-board-rev1-pcb-layout-traces-routed.png` (new, renamed from `Screenshot_20260516_150936.png`)
  - `website/docs/assets/images/hardware/pcb/full-board-rev1/full-board-rev1-3d-render-front-with-pico.png` (new, renamed from `Screenshot_20260516_151001.png`)
  - `website/docs/assets/images/hardware/pcb/full-board-rev1/full-board-rev1-3d-back-with-joystick.png` (new, renamed from `Screenshot_20260516_151037.png`)
  - `website/docs/assets/images/hardware/pcb/full-board-rev1/full-board-rev1-3d-isometric-angle.png` (new, renamed from `Screenshot_20260516_151102.png`)
  - `website/docs/assets/images/hardware/pcb/full-board-rev1/full-board-rev1-front-silkscreen-dildafication-begins.png` (new, renamed from `Screenshot_20260516_162733.png`)
  - `website/docs/assets/images/hardware/pcb/full-board-rev1/full-board-rev1-back-silkscreen-mascot.png` (new, renamed from `Screenshot_20260516_162755.png`)
  - `website/docs/assets/images/hardware/pcb/full-board-rev1/full-board-rev1-complete-schematic.png` (new, renamed from `Screenshot_20260516_164940.png`)
  - `website/docs/assets/images/hardware/pcb/full-board-rev1/full-board-rev1-board-setup-stackup-4layer-default.png` (new, renamed from `board-setup-physical-stackup-4layer.png`)
  - `website/docs/assets/images/hardware/pcb/full-board-rev1/full-board-rev1-board-setup-stackup-4layer-corrected.png` (new, renamed from `board-setup-physical-stackup-4layer-corrected.png`)
  - `PromptProgression.md` — this entry
  - `website/docs/prompts/index.md` — synced entry for #279
