rompasaurus/dilder/website/docs/index.md

# Dilder

**A real-time build journal for an open-source AI-assisted virtual pet.**

Dilder is a Tamagotchi-style device built on a Raspberry Pi Pico W, a Waveshare 2.13" e-ink display, and a 3D-printed case — developed entirely in the open, one phase at a time.

---

## The Origin Story — How Jamal Was Found

<figure markdown="span">
  Jamal the plush octopus, lounging in a chair like he owns the place
  <figcaption>Jamal. Chair thief. Hat enthusiast. The one who started it all.</figcaption>
</figure>

It started with a trip to TEDi — a German dollar store where the shelves are chaos and the deals are questionable. My wife Emma and I were browsing the bins, not looking for anything in particular, when we spotted him: a massive plush octopus, soft as a cloud, grinning up at us from a pile of discount stuffed animals like he'd been waiting.

We bought him. Obviously.

On the walk home, something happened. We started talking *to* him. Then *about* him — as if he had opinions, preferences, a whole inner life. By the time we got back to the apartment, he had a name: **Jamal**. He had a personality: laid-back but opinionated, a little sassy, suspiciously wise for a creature with no skeleton. He claimed the armchair immediately. He looked... comfortable. *Too* comfortable. Like he'd always lived there and we were the guests.

And then the question asked itself:

> *What if we could actually bring him to life?*

Not literally — we're not mad scientists (yet). But what if we could build a tiny digital version of Jamal? A pocket-sized octopus with moods, opinions, and an attitude problem? Something that lives on a screen, reacts to the world, and roasts you when you forget to feed it?

That's how Dilder was born. Not from a grand engineering vision or a product roadmap — from a plush octopus in a discount bin and two people who couldn't stop giving him a backstory on the walk home.

Jamal still sits in the armchair. He still wears the hat. He watches us build his digital self from across the room, and honestly? He looks unimpressed. Which tracks.

---

## :sparkles: Milestone — Dilder Full Board Rev 1 Complete! :sparkles:

After two months of breadboards, flying wires, and a small army of off-the-shelf modules, **every part of the Dilder now lives on a single PCB**. The Full Board Rev 1 layout is done — schematic finalized, 4-layer stackup configured, board routed end-to-end, and the 3D preview is green-and-gorgeous.

This is the moment Dilder graduates from "breadboard inside a case" to **actual hardware product**.

<div class="grid" markdown>

<figure markdown="span">
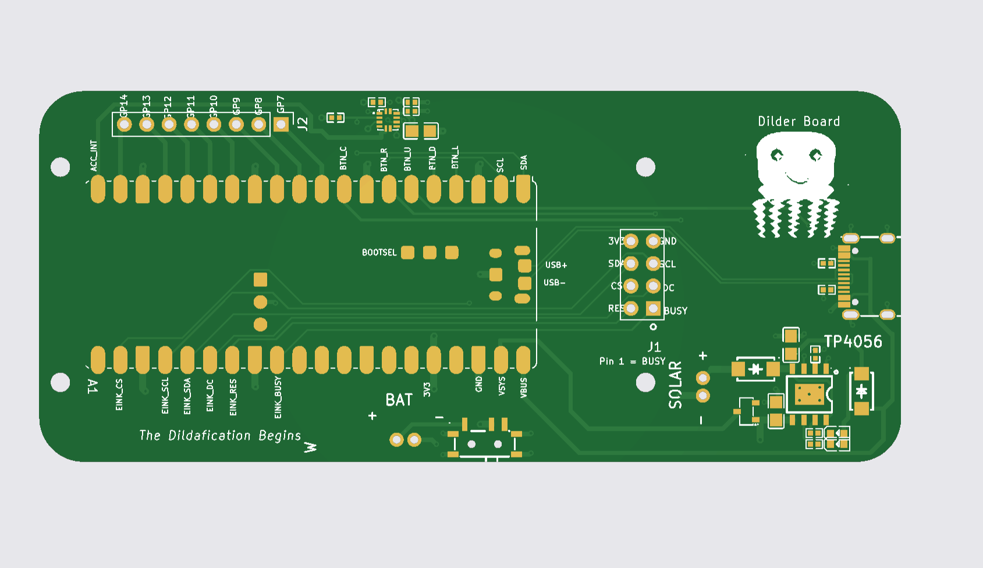
[picture p1: website/docs/assets/images/hardware/pcb/full-board-rev1/full-board-rev1-front-silkscreen-dildafication-begins.png]
Dilder Full Board Rev 1 — front silkscreen with The Dildafication Begins tagline
  
  <figcaption>Front of the board — Pico 2 W, TP4056 charger, USB-C, IMU, button pads. Tagline: "The Dildafication Begins."</figcaption>
</figure>

<figure markdown="span">
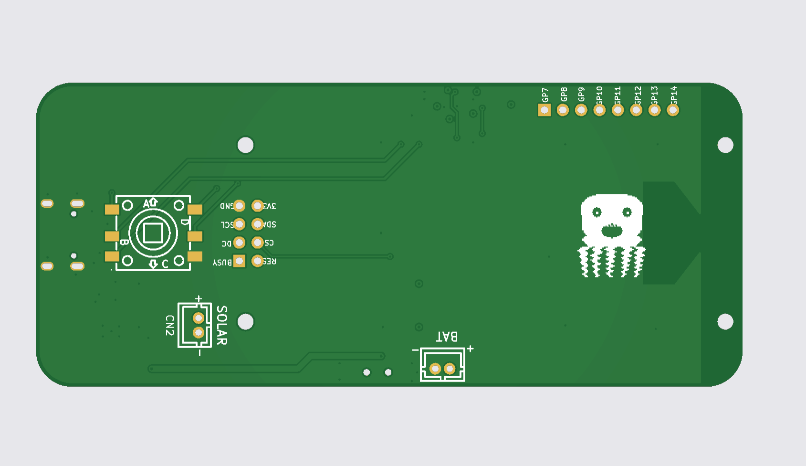
[picture p2: website/docs/assets/images/hardware/pcb/full-board-rev1/full-board-rev1-back-silkscreen-mascot.png]
Dilder Full Board Rev 1 — back silkscreen with octopus mascot and joystick footprint
  
  <figcaption>Back of the board — joystick switch, e-paper SPI breakout, solar + battery JST connectors, octopus mascot.</figcaption>
</figure>

</div>

<div class="grid" markdown>

<figure markdown="span">
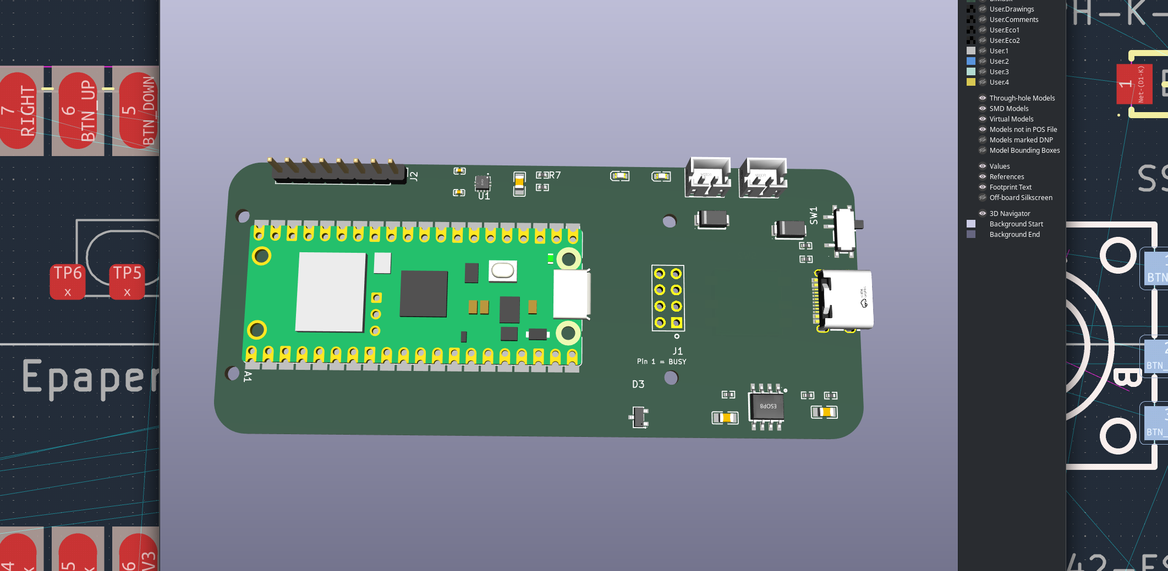
[picture p3: website/docs/assets/images/hardware/pcb/full-board-rev1/full-board-rev1-3d-top-view.png]
Dilder Full Board Rev 1 — 3D top view of the routed board with Pico module placed
  
  <figcaption>3D top view from KiCad — Pico 2 W in its 2×20 header, charger circuit on the right.</figcaption>
</figure>

<figure markdown="span">
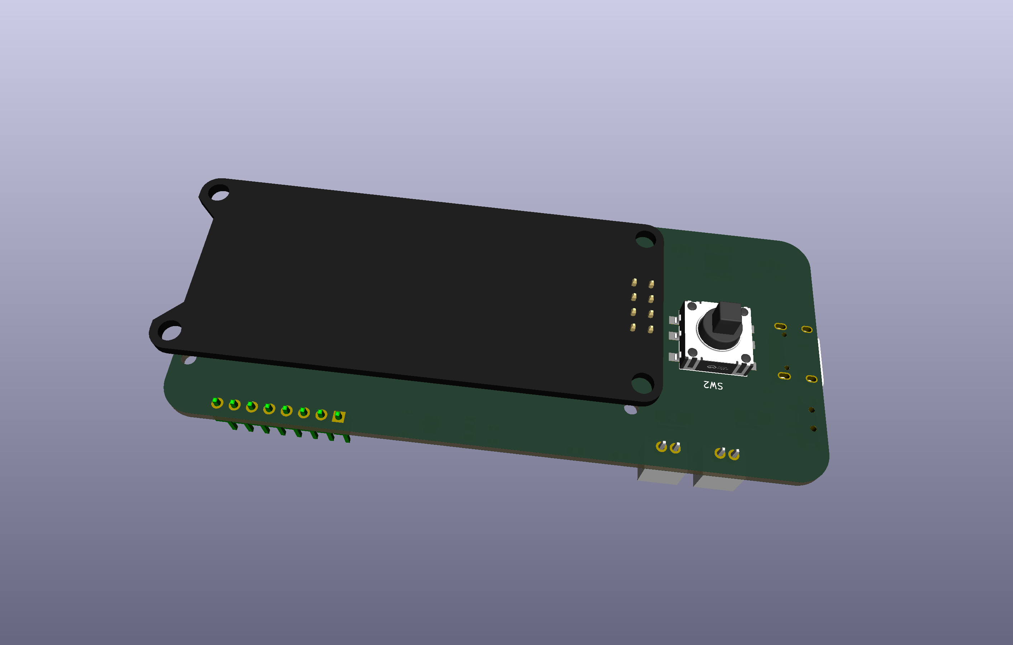
[picture p4: website/docs/assets/images/hardware/pcb/full-board-rev1/full-board-rev1-3d-with-epaper-display-spaced.png]
Dilder Full Board Rev 1 — 3D render with e-paper display floating above the board
  
  <figcaption>Screen fit-check — the Waveshare e-paper module floats exactly where the case expects it.</figcaption>
</figure>

</div>

[Read the full milestone write-up :material-arrow-right:](blog/posts/dilder-full-board-rev1.md){ .md-button .md-button--primary }

---

## Latest Milestone — Dilder Goes Real-Time (and Social)

The firmware moved off its single bare-metal loop onto **FreeRTOS across both cores** of the RP2350 — the slow e-ink refresh now lives on its own core so buttons stay snappy. And the big new trick: **Dilders can find each other.** Turn on the new **Social** mode and when another Dilder comes into Bluetooth range, your octopus pipes up — *"A Dilder appears in the wild! Say hi?"* — then **acts out an emote** (wave, hearts, laugh, party, sleepy, whoa) that the other Dilder performs on its own screen.

It's all **connectionless** (a beacon broadcast, no pairing), every Dilder gets a gloriously dumb auto-name (*Unhinged Trashpanda*, anyone?), and there's a **Dilders Met** log with a 24-hour re-greet cooldown. Under the hood: input now **paces itself to the display** (no more ghost presses), the battery gauge is load-aware, and a field-debugging saga traced three "dead" units to **e-ink BUSY-line solder joints** — not the silicon — which led to hang-proof timeouts on the accelerometer and display drivers.

**This milestone added:** FreeRTOS dual-core SMP rewrite · **Dilder-to-Dilder proximity hellos + emotes** (octopus animations) · Social menu, scan-nearby, met-log · display-paced input (no ghost presses) · load-aware battery reading · I²C + e-ink **timeouts** (no more boot hangs on bad hardware) · DevTool Full Erase recovery.

[Read the full RTOS + social milestone :material-arrow-right:](blog/posts/rtos-rewrite-social-emotes.md){ .md-button .md-button--primary }

---

## Milestone — The Firmware Comes Alive

The custom **Dilder Board** is running the real firmware, and it grew a brain this month: the octopus **auto-rotates** with the device, **counts your steps**, **remembers your WiFi**, flashes itself **over the air**, and now **pairs to your phone over Bluetooth LE** with a passkey shown right on the e-ink.

<div class="grid" markdown>

<figure markdown="span">
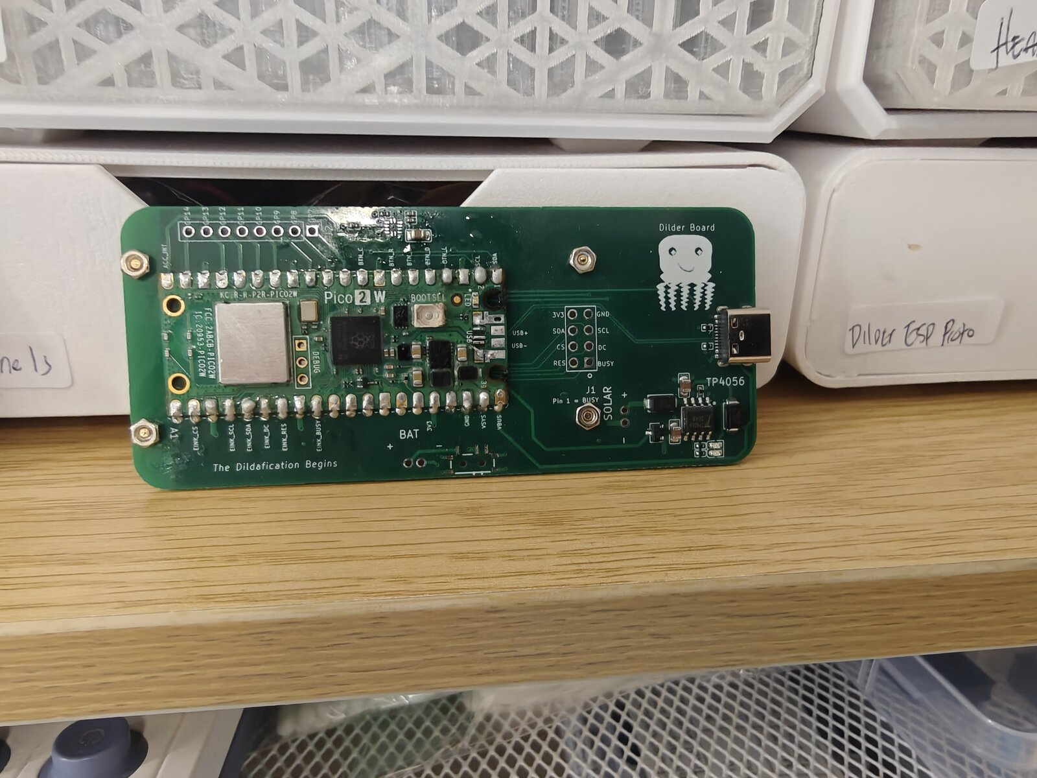
[picture p5: website/docs/assets/images/firmware/dilder-custom-pcb-bare.jpg]
Bare custom Dilder Board — green PCB with Raspberry Pi Pico 2 W, TP4056 charger, solar pads, and the octopus silkscreen reading "Dilder Board"
  
  <figcaption>The custom Dilder Board — Pico 2 W, TP4056 charging, solar pads, USB-C.</figcaption>
</figure>

<figure markdown="span">
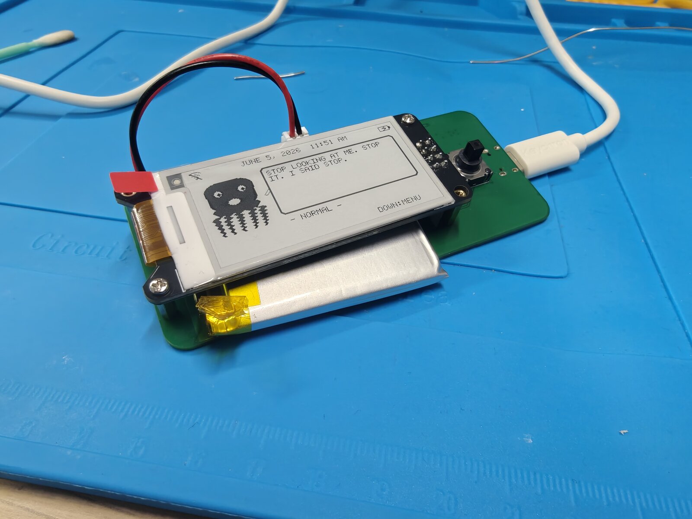
[picture p6: website/docs/assets/images/firmware/dilder-board-running-normal-quote.jpg]
Dilder Board running firmware on the bench — e-ink reads "STOP LOOKING AT ME. STOP IT. I SAID STOP." with the octopus, clock, and NORMAL mood
  
  <figcaption>Firmware live on the custom board — clock, mood line, and menu prompt.</figcaption>
</figure>

</div>

<div class="grid" markdown>

<figure markdown="span">
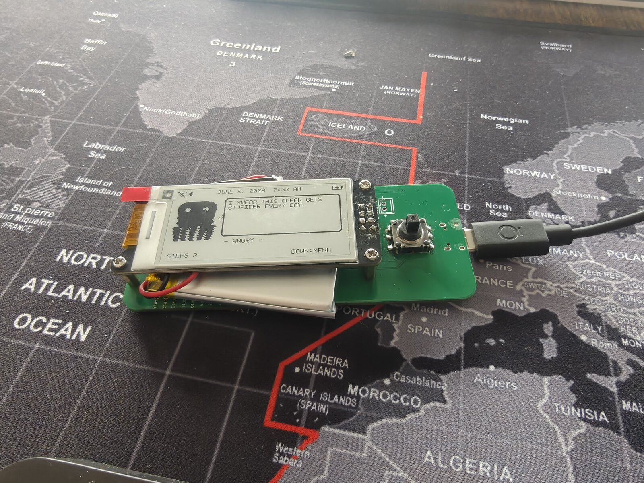
[picture p7: website/docs/assets/images/firmware/dilder-board-wide-angry-steps.jpg]
Dilder Board with joystick on a world map — wide layout showing "I SWEAR THIS OCEAN GETS STUPIDER EVERY DAY.", ANGRY mood, STEPS 3, and WiFi/Bluetooth/battery status icons
  
  <figcaption>Wide layout — live step count and the new WiFi / Bluetooth / battery status bar.</figcaption>
</figure>

<figure markdown="span">
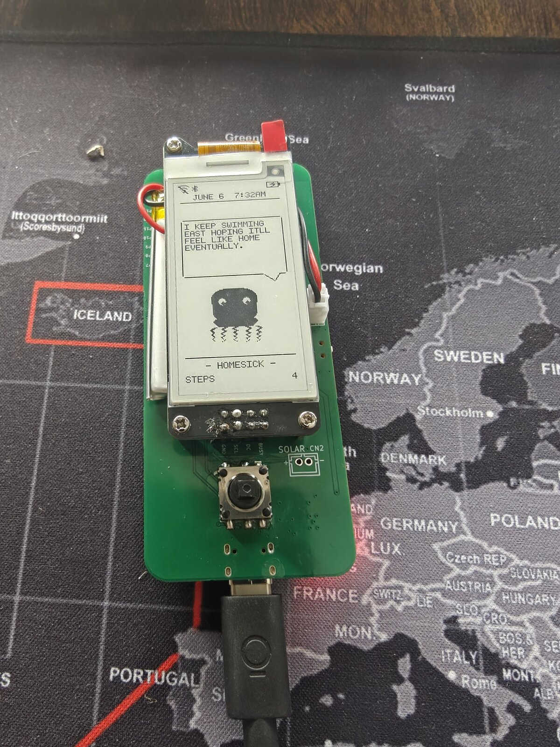
[picture p8: website/docs/assets/images/firmware/dilder-board-tall-homesick.jpg]
Dilder Board in tall portrait orientation — speech-bubble quote "I KEEP SWIMMING EAST HOPING IT'LL FEEL LIKE HOME EVENTUALLY." above a HOMESICK octopus, STEPS 4, Bluetooth icon lit
  
  <figcaption>Auto-rotated tall "longways" layout — speech bubble, HOMESICK octopus, Bluetooth paired.</figcaption>
</figure>

</div>

**This milestone added:** auto-rotating UI (3 orientations) · accelerometer step + activity tracking · saved WiFi with NTP clock · **Bluetooth LE pairing** (passkey-secured, phone-readable mood/steps) · WiFi OTA + buttonless USB reflash · WiFi/BT/battery status icons.

[Read the full firmware milestone :material-arrow-right:](blog/posts/firmware-comes-alive-bluetooth-autorotate.md){ .md-button .md-button--primary }

---

## The Current Build — Mk2 Translucent Prototype

The latest revision: printed in **natural/clear PETG** so every internal component is visible through the case walls. Running the Conspiratorial Octopus personality on battery power.

<div class="grid" markdown>

<figure markdown="span">
  Mk2 translucent Dilder outdoors — hero front shot with Conspiratorial Octopus running on e-ink display, Claude Code terminal visible on laptop behind, blue sky and rooftops
  <figcaption>"THE PYRAMIDS WERE BUILT BY CATS. EGYPTIANS JUST TOOK CREDIT." — e-ink perfectly readable in sunlight</figcaption>
</figure>

<figure markdown="span">
  Mk2 translucent Dilder — front view showing THE MOON LANDING WAS REAL BUT THE MOON IS FAKE quote on e-ink display with joystick dome
  <figcaption>"THE MOON LANDING WAS REAL BUT THE MOON IS FAKE." — front view, display sharp, joystick dome on right</figcaption>
</figure>

</div>

<div class="grid" markdown>

<figure markdown="span">
  Mk2 translucent Dilder — isometric view showing Conspiratorial Octopus on e-ink display, internals visible through clear PETG case
  <figcaption>"DEJA VU IS THE SIMULATION BUFFERING." — translucent walls reveal battery, board, and wiring</figcaption>
</figure>

<figure markdown="span">
  Mk2 translucent Dilder — back view showing TP4056, battery, and piezo ring visible through translucent walls
  <figcaption>Back view — TP4056, 10440 battery, and piezo speaker ring all visible through the case</figcaption>
</figure>

</div>

<div class="grid" markdown>

<figure markdown="span">
  Joystick breakout PCB from JLCPCB with 3D-printed thumbpiece snap cap fitted on the K1-1506SN-01 switch actuator
  <figcaption>Joystick breakout PCB from JLCPCB — K1-1506SN-01 switch with 3D-printed thumbpiece snap cap</figcaption>
</figure>

<figure markdown="span">
  JLCPCB blue shipping box with full panel of joystick breakout boards on pink antistatic foam
  <figcaption>JLCPCB delivery — full panel of hand-routed joystick breakout boards, switches pre-mounted</figcaption>
</figure>

</div>

<div class="grid" markdown>

<figure markdown="span">
  Fully assembled Dilder in black NoSolar case — e-ink display showing Conspiratorial Octopus, battery powered
  <figcaption>NoSolar variant (black PLA) — same internals, different look</figcaption>
</figure>

<figure markdown="span">
  NoSolar variant open top-down — Pico W, 10440 battery, TP4056 charger with red LED visible
  <figcaption>NoSolar internals — Pico W, 10440 battery, TP4056 charger (red LED = charging)</figcaption>
</figure>

</div>

[Read the full Mk2 build post :material-arrow-right:](blog/posts/mk2-translucent-prototype-running.md){ .md-button }

[View the design evolution timeline :material-arrow-right:](docs/hardware/design-evolution.md){ .md-button }

[See the progress report :material-arrow-right:](docs/progress.md){ .md-button }

---

## Latest Prototype — Sensors, Speaker, and Joystick Anchor

The parametric FreeCAD macro gained three new systems: a **20 mm piezo speaker** in a circular retaining ring, an **MPU-6500 6-axis accelerometer** in a recessed pocket, and a precision **joystick anchor pad** that replaces the old well/sleeve design. The joystick PCB alignment was fixed (stick now dead-center in the hole), and the cradle pit tightened from 23 mm to 20 mm for a snug board fit.

<div class="grid" markdown>

<figure markdown="span">
  Dilder Rev 2 — hero isometric
  <figcaption>Hero shot — full assembly with all components visible through the translucent cover</figcaption>
</figure>

<figure markdown="span">
  Dilder Rev 2 — 3/4 angle front-right
  <figcaption>3/4 angle — joystick thumbpiece and display window on the bullnose dome</figcaption>
</figure>

</div>

<div class="grid" markdown>

<figure markdown="span">
  Dilder Rev 2 — exploded isometric
  <figcaption>Exploded view — base plate, cradle with batteries, cover with anchor pad, and thumbpiece</figcaption>
</figure>

<figure markdown="span">
  Dilder Rev 2 — assembled opaque
  <figcaption>Assembled (opaque cover) — the finished device with display window and joystick</figcaption>
</figure>

</div>

<div class="grid" markdown>

<figure markdown="span">
  Dilder Rev 2 — cover removed
  <figcaption>Cover removed — cradle with batteries, Pico board, TP4056 charger, and joystick PCB</figcaption>
</figure>

<figure markdown="span">
  Dilder Rev 2 — base plate sensors
  <figcaption>Base plate — piezo speaker ring (center) and IMU pocket (left) between battery rails</figcaption>
</figure>

</div>

[Read the full build write-up :material-arrow-right:](blog/posts/joystick-anchor-piezo-imu-sensors.md){ .md-button }

[View the complete design breakdown :material-arrow-right:](docs/hardware/freecad-mk2-design.md){ .md-button }

---

## Dilder Encounters, Riddle Hunts & Collectibles

The Dilder isn't just a desk pet — it's a device that comes alive when it meets other Dilders in the real world.

### Proximity Encounters

Every Dilder broadcasts a BLE beacon. When two devices come within range (~10-30m), both react automatically — a **unique 3-note chime** plays through the piezo speaker, the e-ink display shows the other pet's name and personality, and both players earn XP and collectibles. No buttons to press. The chime is generated from the device's unique ID, so every Dilder sounds different — and you play *the other one's* chime, not your own.

### Riddle Hunts — Geocaching with Physical Prizes

The device presents riddles hinting at real-world locations where **physical electronic prizes** are hidden in waterproof capsules:

> *"Where iron horses once drank and the clock tower still watches, look beneath the bench that faces west."*

Find the capsule, tap the NFC tag against your Dilder, and collect both a **digital unlock** (cosmetics, sounds, lore fragments) and a **physical electronic component** — anything from an LED pack to a full sensor breakout board. Legendary capsules might contain an actual Pico W or a pre-assembled Dilder unit.

Community members become **Cache Keepers** — writing their own riddles, hiding capsules, and maintaining caches worldwide.

### The Network Effect

More Dilders = more encounters = more fun. The chime creates curiosity in public. Bystanders ask what the device is. Every encounter is a natural demonstration — and the device is free to build from GitHub or available as a kit on Patreon.

[Read the full design doc :material-arrow-right:](blog/posts/encounters-geocaching-collectibles.md){ .md-button }

---

## Meet the Octopus

A tiny octopus lives on a 250x122 pixel e-ink display. It has **16 emotional states**, each with unique eyes, mouth expressions, body animations, and themed quotes. It's sassy. It's opinionated. It runs on 100KB of firmware and a coin cell's worth of ambition.

Pick a personality, flash it to the board, and you've got a desk companion that judges your life choices in ALL CAPS.

---

## The Hardware

Three supported boards. Same firmware. Under $25 to get started.

| Component | Price | Why |
|---|---|-----|
| Raspberry Pi Pico 2 W | ~$7 | 4MB flash, WiFi + BLE, RP2350 dual Cortex-M33, current default |
| Raspberry Pi Pico W | ~$6 | 2MB flash, WiFi + BLE, RP2040, original dev board |
| Waveshare 2.13" e-Paper V3 | ~$15 | 250x122px, paper-like readability, near-zero standby current |
| 3D-printed enclosure | ~$2 filament | Two-piece snap-fit case, SCAD source files included |

---

## 16 Emotions, One Octopus

Every mood changes the face, the body, and the attitude.

<div class="grid" markdown>

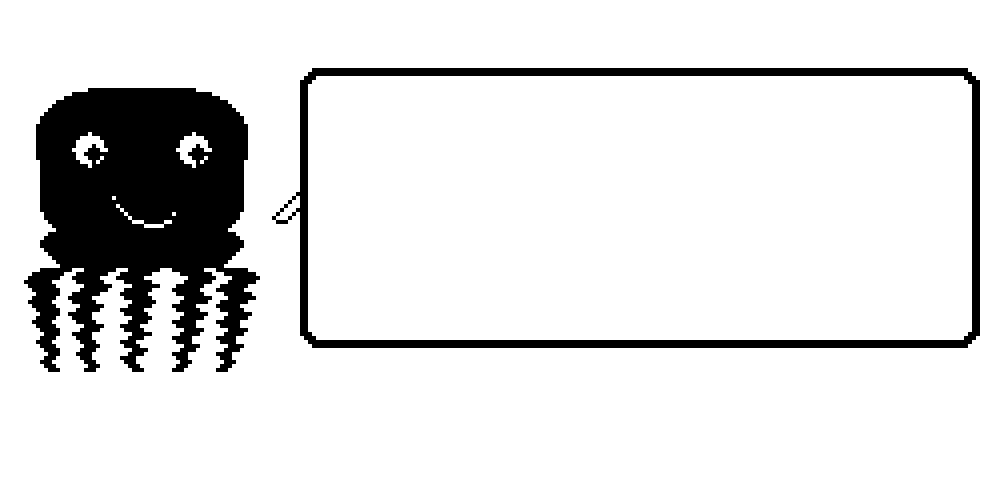
[picture p9: website/docs/assets/images/octopus/normal.png]
Normal

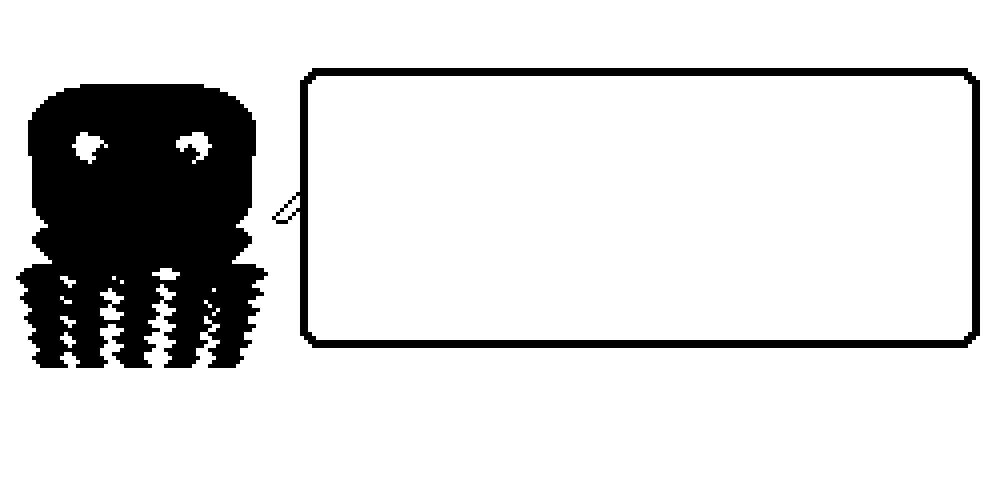
[picture p10: website/docs/assets/images/octopus/angry.png]
Angry

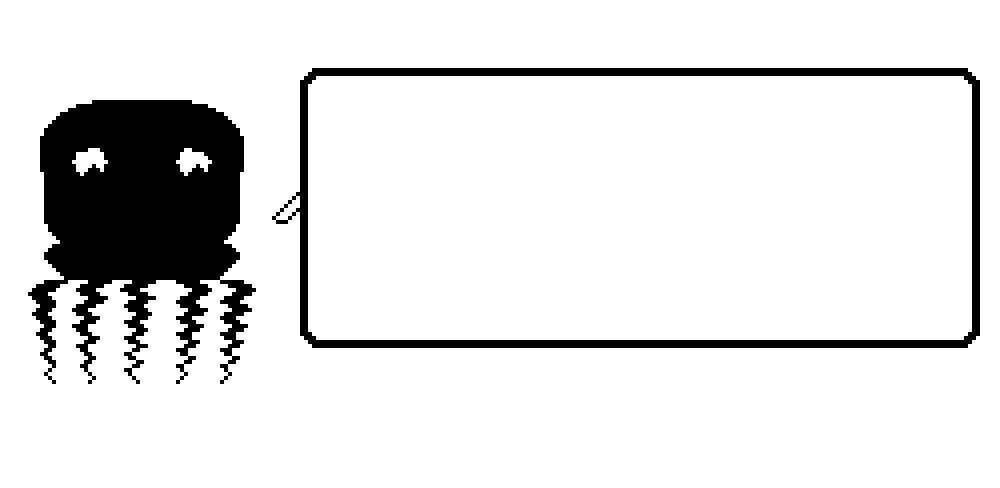
[picture p11: website/docs/assets/images/octopus/sad.png]
Sad


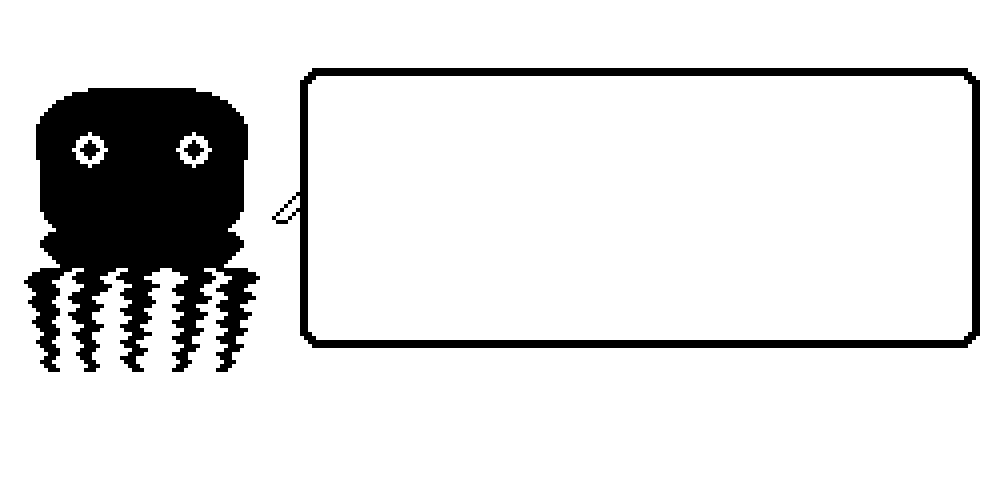
[picture p12: website/docs/assets/images/octopus/excited.png]
Excited

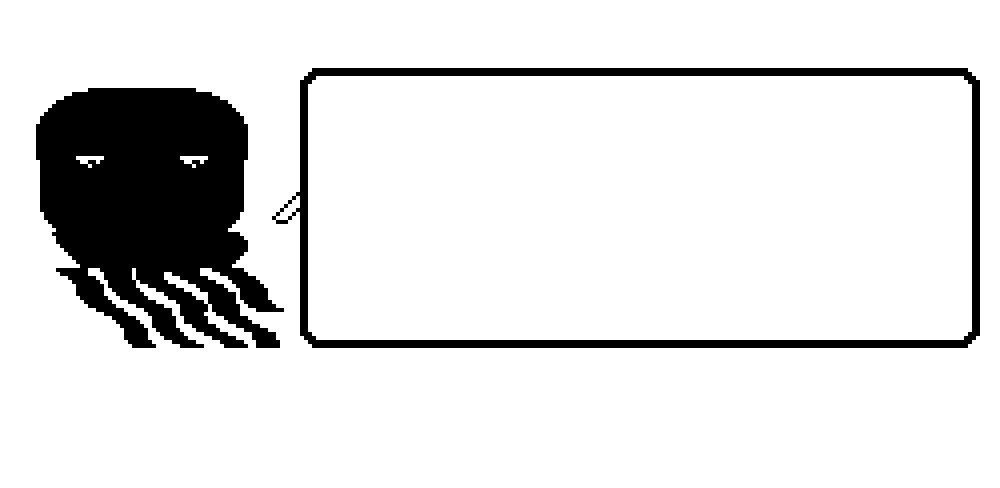
[picture p13: website/docs/assets/images/octopus/lazy.png]
Lazy

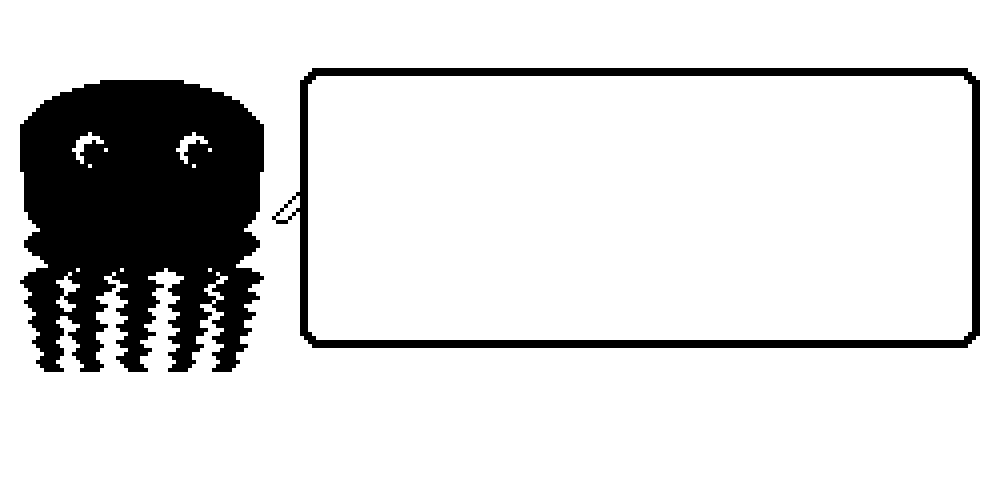
[picture p14: website/docs/assets/images/octopus/fat.png]
Fat


</div>

Normal. Angry. Sad. Excited. Lazy (tentacles draped to the right, naturally). Fat (thicc dome, no waist, proud of it). Plus Weird, Unhinged, Chaotic, Hungry, Tired, Slap Happy, Chill, Creepy, Nostalgic, and Homesick.

Each personality has 30-196 themed quotes, a 4-frame mouth animation cycle, and per-mood body movement — breathing bobs, angry trembles, chaotic distortion, lazy lounging.

[See all 16 emotion states :material-arrow-right:](docs/software/emotion-states.md){ .md-button }

---

## The DevTool

A custom Tkinter GUI for designing, previewing, and deploying octopus firmware — without touching a terminal.

<figure markdown="span">
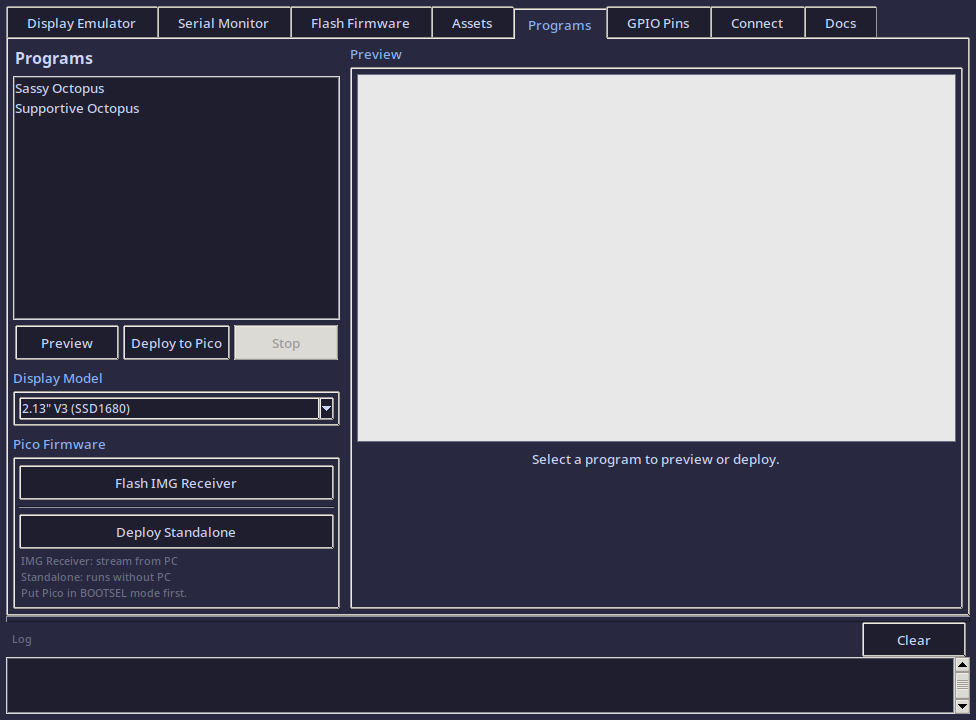
[picture p15: website/docs/assets/images/devtool/devtool_tab_programs.png]
DevTool Programs tab
  
  <figcaption>Programs tab — pick a personality, preview it, flash it to the Pico</figcaption>
</figure>

**7 tabs:** Display Emulator (pixel art tools) | Serial Monitor | Flash Firmware | Asset Manager | Programs (17 octopus personalities) | GPIO Pin Reference | Connection Utility

Select a program and you get a live preview, estimated firmware size (~100KB), how much of the Pico's 2MB flash you'll use (~5%), and one-click deploy.

[DevTool docs :material-arrow-right:](docs/tools/devtool.md){ .md-button }

---

## First PCB from Scratch — Joystick Breakout Board

Before the Dilder, the closest I'd come to PCB design was staring at someone else's Gerber files and thinking "that looks complicated." This board changed that.

The joystick needed a breakout board — the K1-1506SN-01 5-way switch is a tiny surface-mount component with six pins spaced 1.27 mm apart. You can't hand-solder wires to that. So instead of buying a pre-made breakout (they don't exist for this switch), I designed one from scratch in KiCad 10.

<div class="grid" markdown>

<figure markdown="span">
  Schematic editor in KiCad
  <figcaption>The schematic — five direction pins (Up, Down, Left, Right, Push) plus a common ground, all routed through the switch to header pads</figcaption>
</figure>

<figure markdown="span">
  PCB layout editor in KiCad
  <figcaption>The PCB layout — every trace hand-routed on a 19.6 x 19.6 mm board. No autorouter, no templates, just dragging copper one track at a time</figcaption>
</figure>

</div>
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
