rompasaurus/dilder/assets/octopus/asset_plan.md

# Jamal the Octopus - Complete Asset Plan

**Canvas:** 250x122px, 1-bit monochrome | **Character footprint:** ~70x70px (left side) | **Bubble:** 170x70px (right side)

---

## Emotion Retention: The "Emotion Echo" System

The core problem: when Jamal changes pose (standing -> sleeping) or enters a new environment, body transforms are overridden and the face may be partially obscured. We need emotion to remain **instantly readable** in any configuration.

### Three-Layer Emotion Encoding

**Layer 1 - Face Invariance (Primary)**
Eyes and mouth are drawn LAST, composited on top of everything. Even in sleeping pose, emotion-specific markers persist above closed eyelids (angry brows, sad droop arcs). Face draw functions are fully decoupled from body/pose — they receive a face anchor point and draw relative to it.

**Layer 2 - Aura Particles (Novel - Key Innovation)**
Each emotion has 3-5 small pixel clusters (2-4px each) that float around the character. These are ALWAYS drawn regardless of pose, environment, or outfit. They orbit the character's center anchor, animated per-frame via sinusoidal motion.

| Emotion | Aura Particles |
|---|---|
| Normal | Gentle dots drifting outward (calm ripple) |
| Weird | Wobbly question marks / tilted dots |
| Unhinged | Rapid flickering random dots (static noise) |
| Angry | Sharp zigzag sparks (lightning bolt fragments) |
| Sad | Falling tear drops (2px dots trailing downward) |
| Chaotic | Spiral dots orbiting wildly (variable speed) |
| Hungry | Rising sweat drops + tiny fork/knife pixels |
| Tired | Floating Z-letters ascending diagonally |
| Slap Happy | Bouncing exclamation marks, alternating sides |
| Lazy | Slow drifting ellipsis dots (...) |
| Fat | Tiny satisfied sparkles (food crumb dots) |
| Chill | Wavy tilde lines drifting sideways (~) |
| Creepy | Pulsing heart-shaped pixel clusters |
| Excited | Star bursts (+ shaped, rotating outward) |
| Nostalgic  | Floating clock/hourglass dots (slow upward drift) |
| Homesick | Tiny house silhouette pixels dissolving outward |

**Layer 3 - Environment Modulation (Ambient)**
The environment subtly reacts to the current emotion. This layer is supplementary, not relied upon for recognition:
- Sad + any outdoor env -> rain drops overlay
- Angry + any -> nearby decor items get 1px vibration offset
- Excited + any -> background elements get subtle bounce
- Tired + any -> decor droops/sags 1-2px
- Chaotic + any -> environment elements get row-wobble distortion
- Chill + any -> ambient wavy heat-shimmer effect

**Why this works on 1-bit e-ink:**
- Aura particles are just 3-8 `px_set` calls per frame — negligible cost
- Particles are recognizable even in silhouette (just outline + particles = emotion readable)
- The system degrades gracefully: face alone works, face+aura is better, face+aura+env is best
- Aura animation drives visual interest when body is static (sleeping, sick)

---

## Poses
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
