rompasaurus/dilder/assets/c-render/_grid_all_moods.png

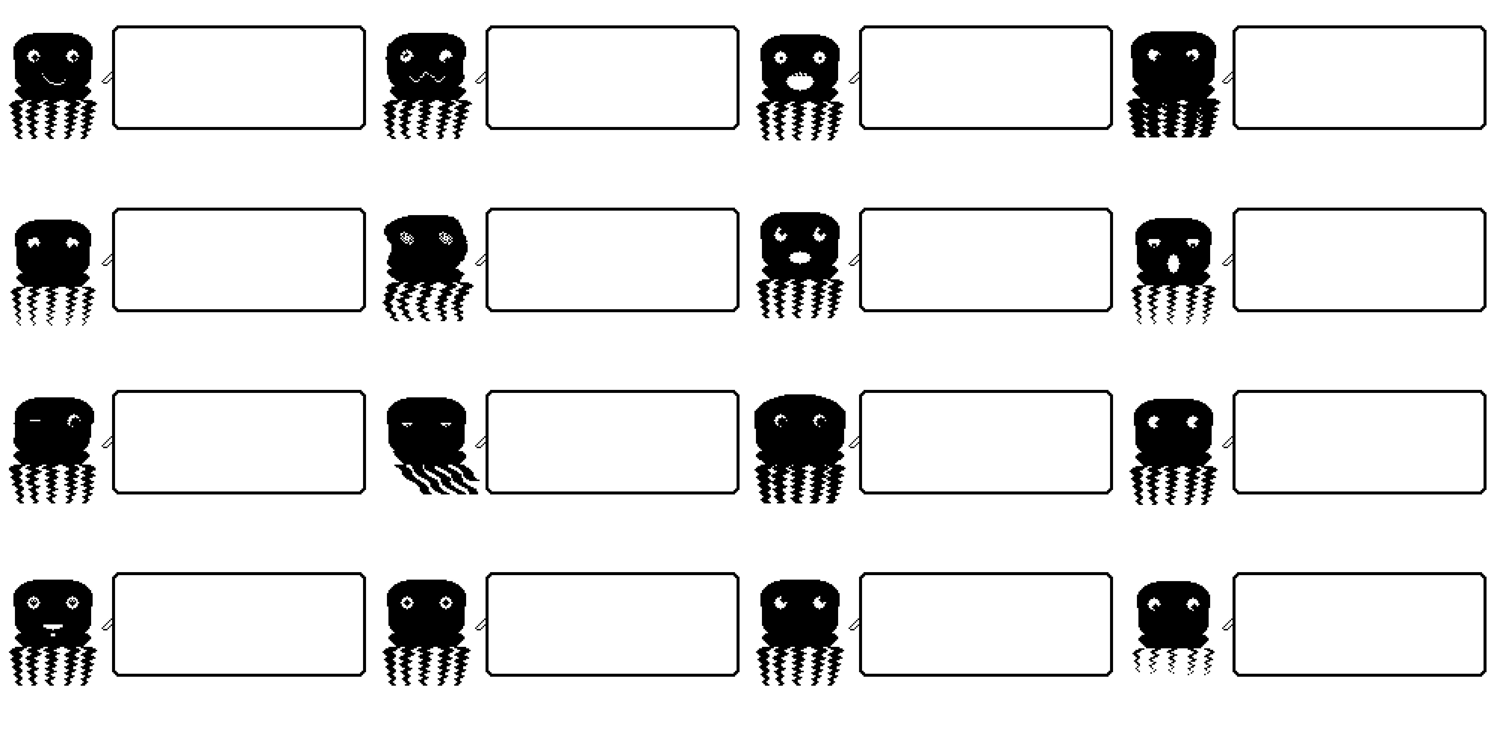
assets/c-render/_grid_all_moods.png
