rompasaurus/dilder/assets/c-vs-python-comparison.png

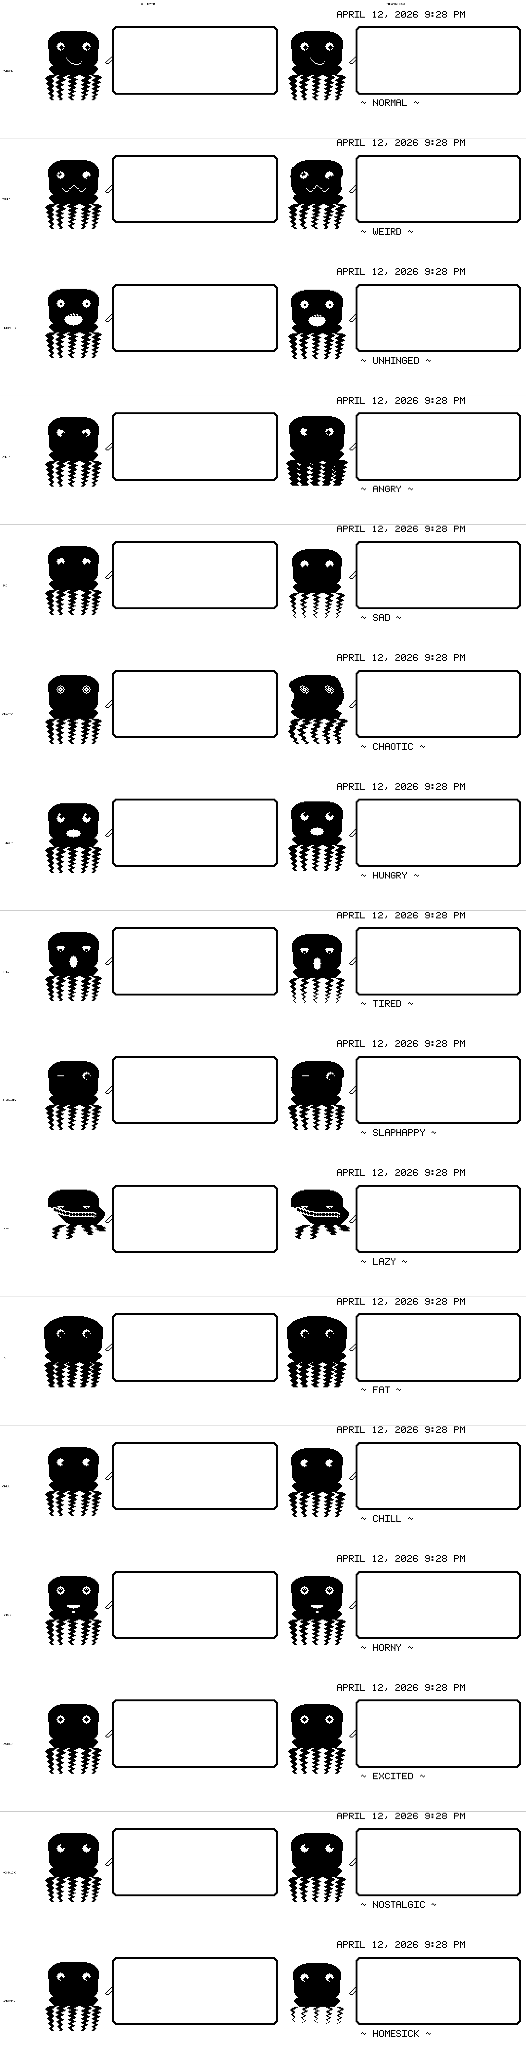
assets/c-vs-python-comparison.png
