rompasaurus/dilder/assets/c-vs-python-key-comparison.png

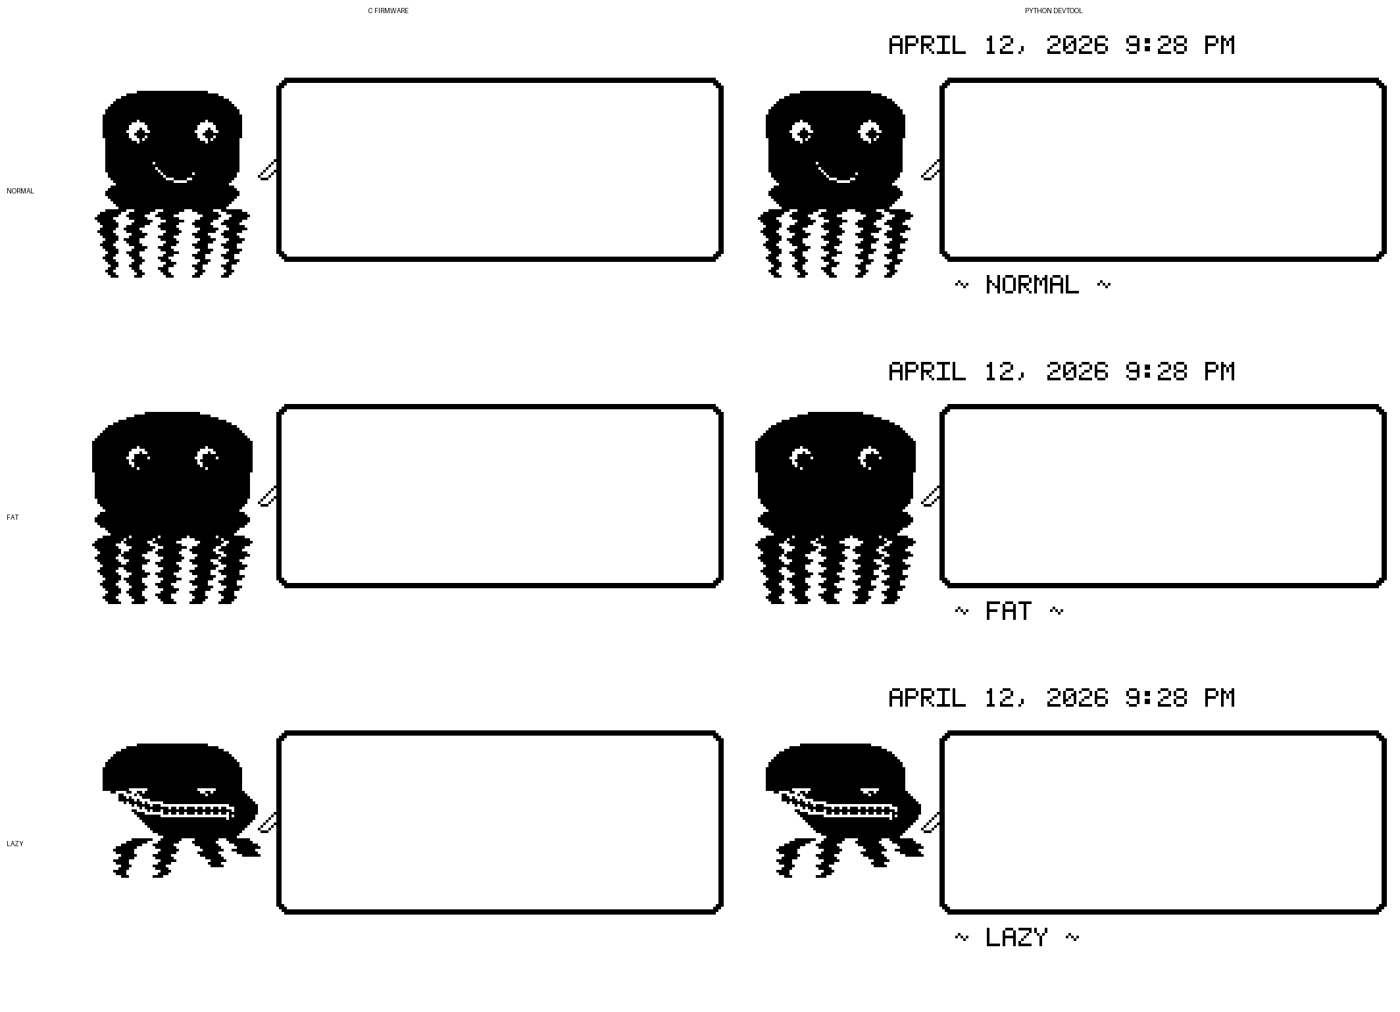
assets/c-vs-python-key-comparison.png
