rompasaurus/dilder/assets/emotion-previews/angry-anim.png

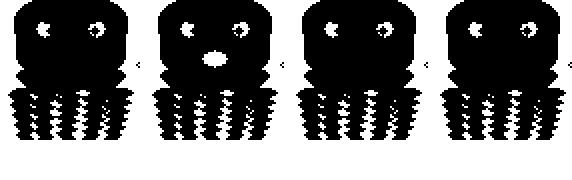
assets/emotion-previews/angry-anim.png
