rompasaurus/dilder/assets/emotion-previews/homesick-anim.png

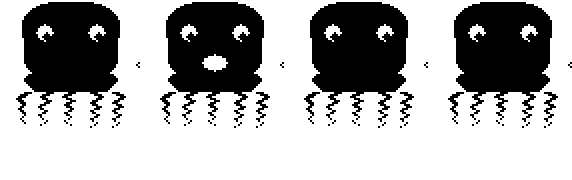
assets/emotion-previews/homesick-anim.png
