rompasaurus/dilder/assets/emotion-previews/horny.png

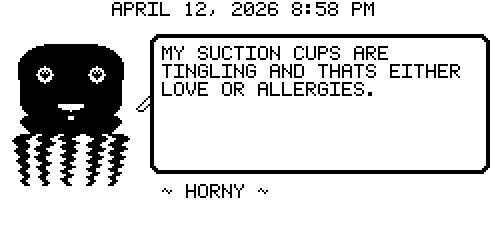
assets/emotion-previews/horny.png
