rompasaurus/dilder/assets/octopus/output/grids/new_3d_environments.png

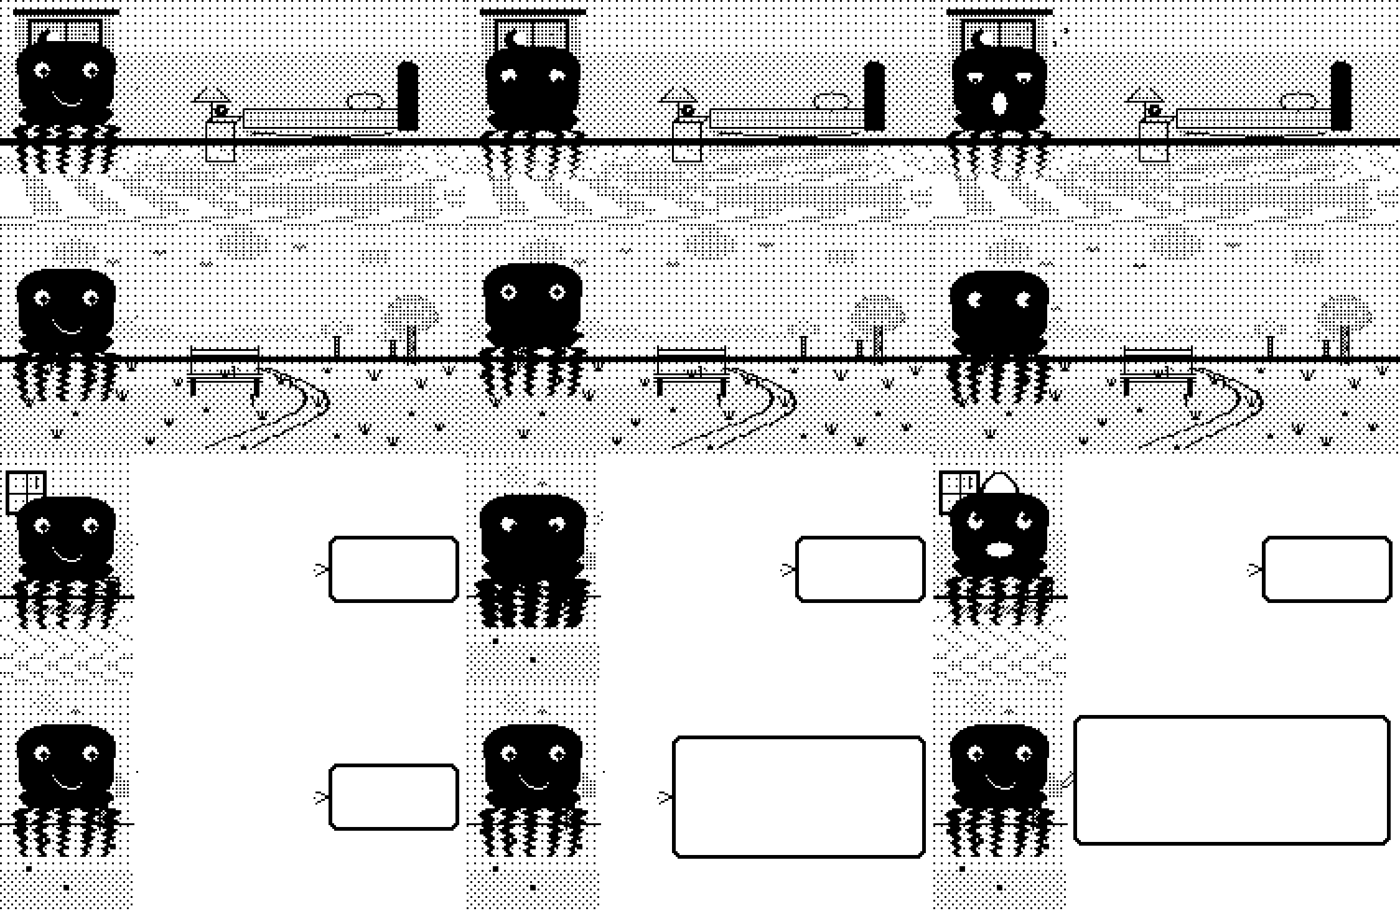
assets/octopus/output/grids/new_3d_environments.png
