rompasaurus/dilder/assets/octopus/output/grids/new_12_environments_hires.png

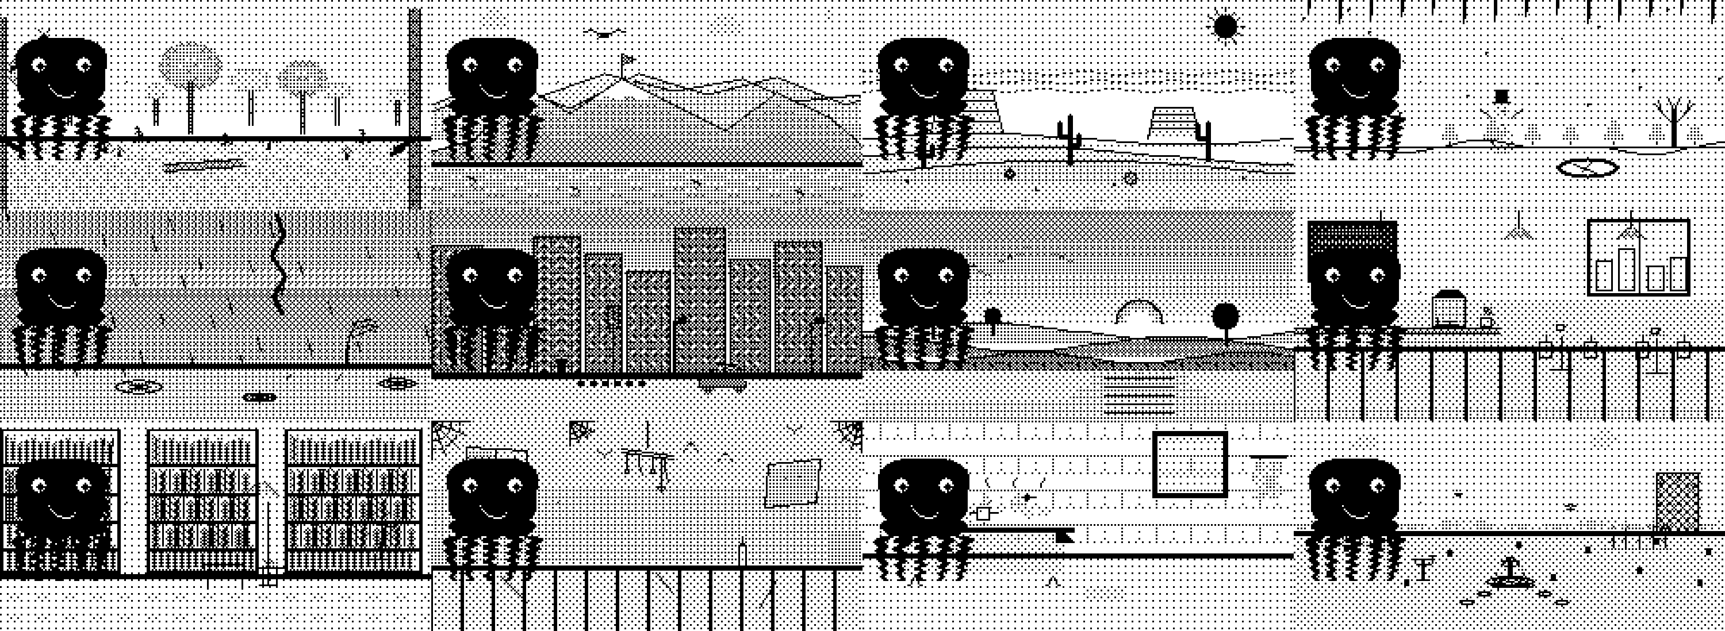
assets/octopus/output/grids/new_12_environments_hires.png
