rompasaurus/dilder/assets/py-render/angry-anim.png

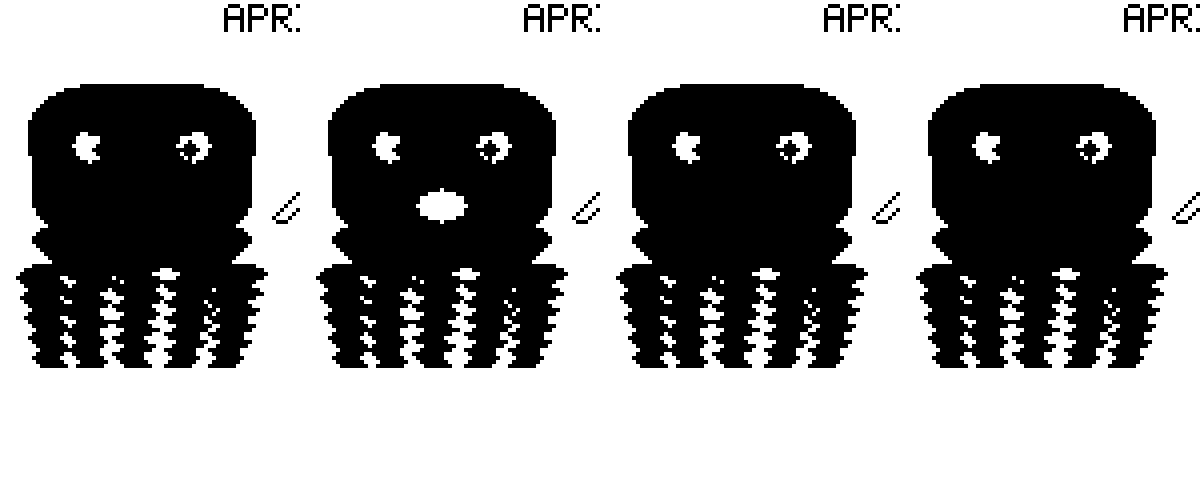
assets/py-render/angry-anim.png
