rompasaurus/dilder/assets/py-render/angry.png

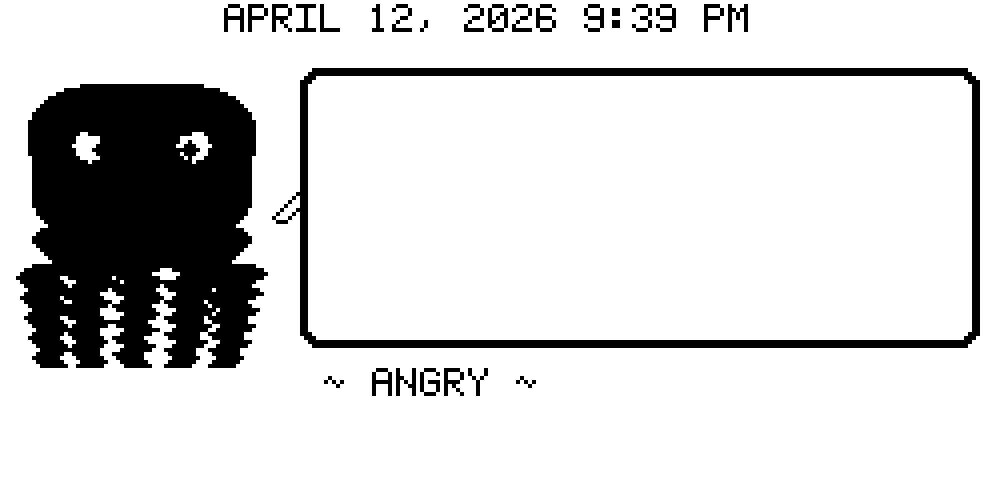
assets/py-render/angry.png
