rompasaurus/dilder/assets/py-render/homesick-anim.png

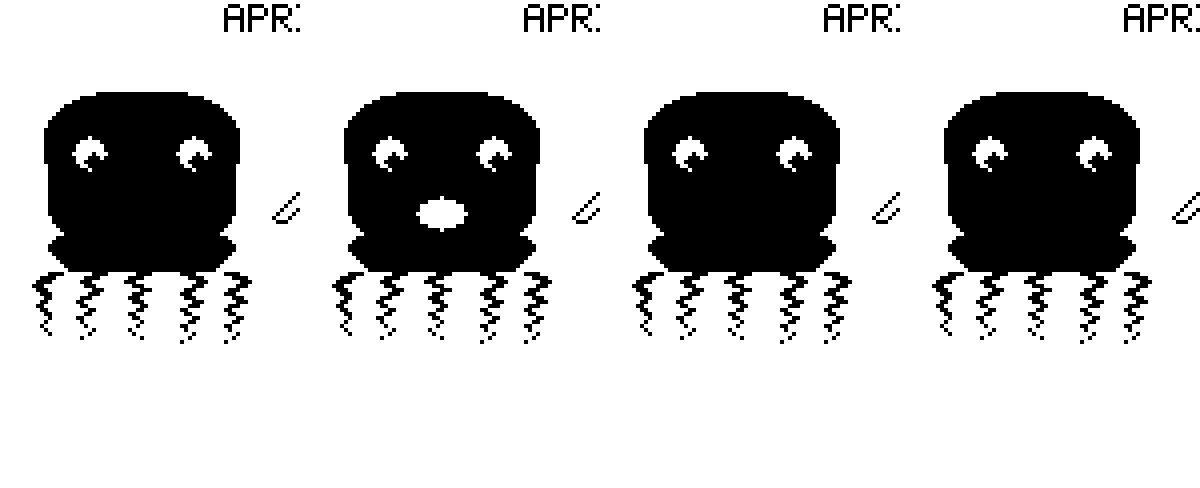
assets/py-render/homesick-anim.png
