rompasaurus/dilder/assets/py-render/homesick.png

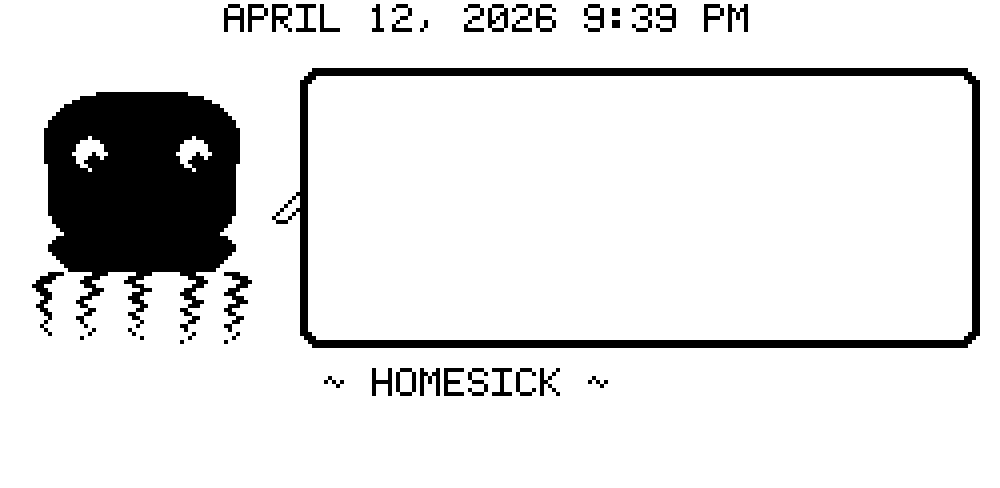
assets/py-render/homesick.png
