rompasaurus/dilder/docs/software/emotion-previews/angry-anim.png

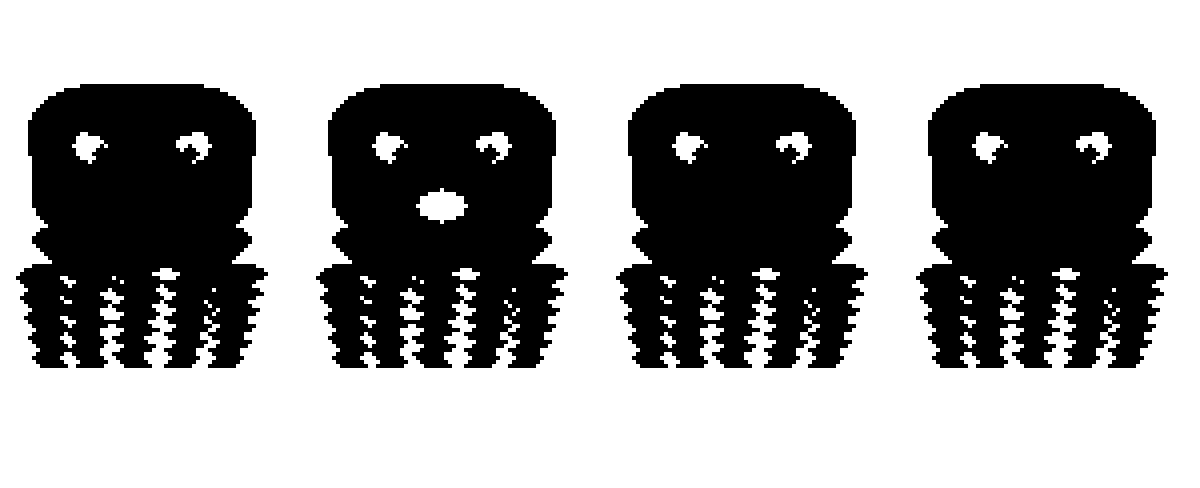
docs/software/emotion-previews/angry-anim.png
