rompasaurus/dilder/docs/software/emotion-previews/homesick-anim.png

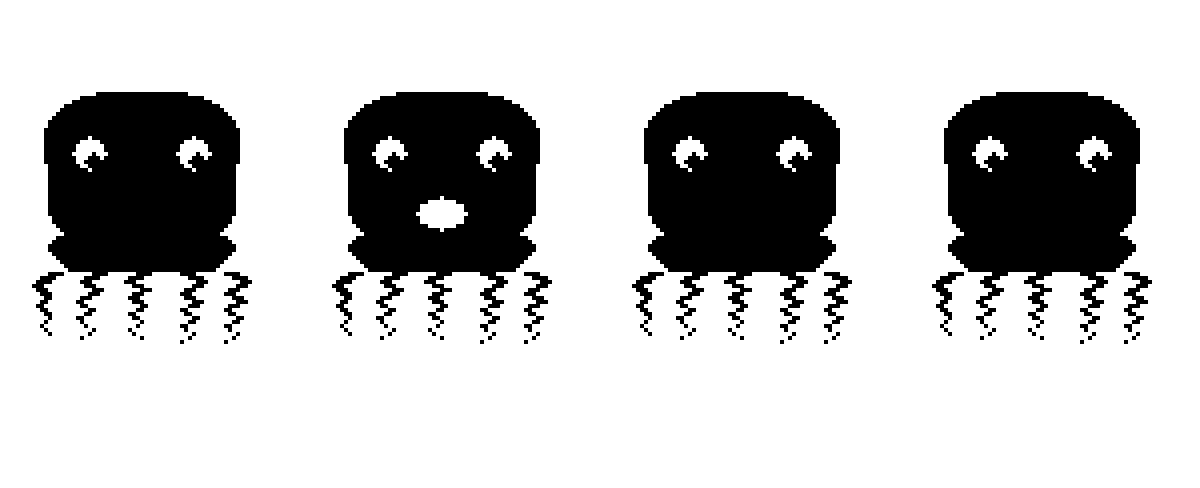
docs/software/emotion-previews/homesick-anim.png
