rompasaurus/dilder/hardware-design/PCB Designs/Dilder Full Board/39570771e9 Good Dsiplay 2.13 Blueprint.webp

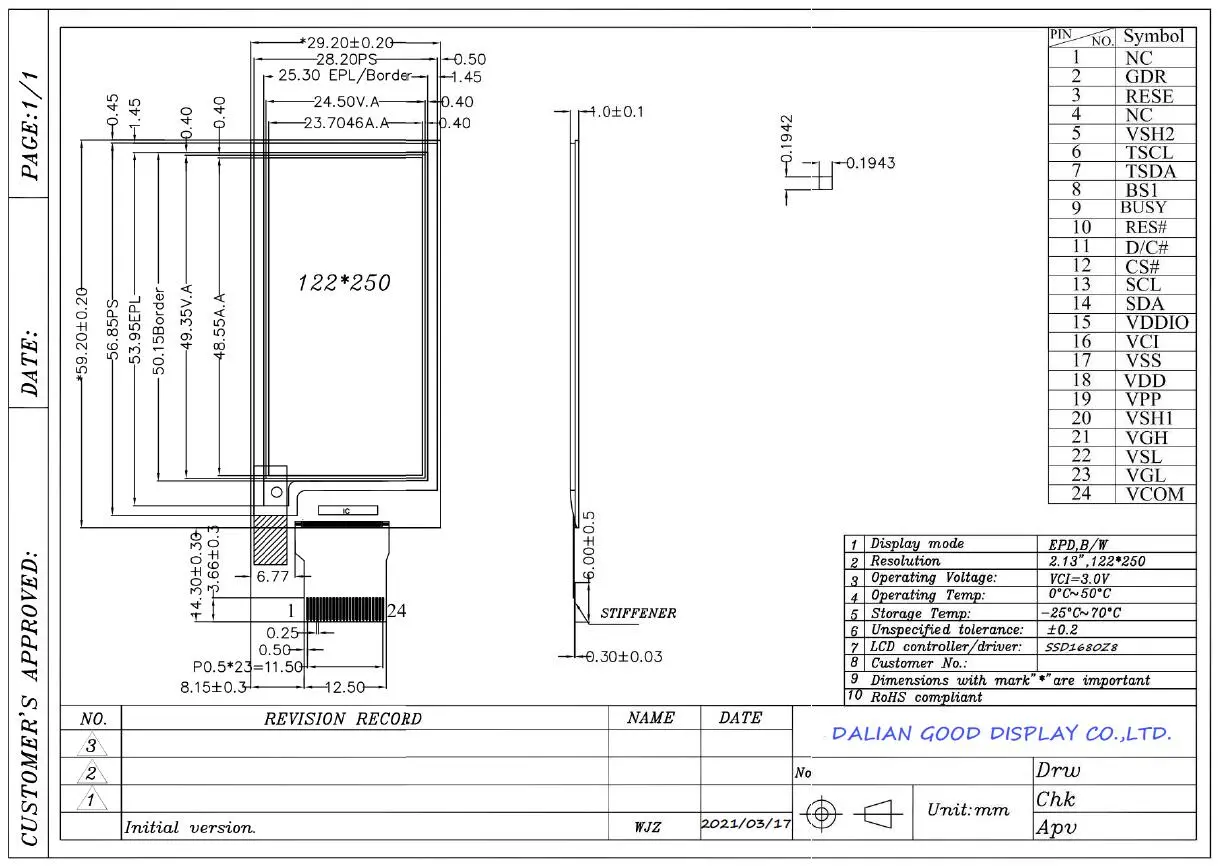
hardware-design/PCB Designs/Dilder Full Board/39570771e9 Good Dsiplay 2.13 Blueprint.webp
