rompasaurus/dilder/website/docs/assets/images/firmware/dilder-board-bench-first-power.jpg

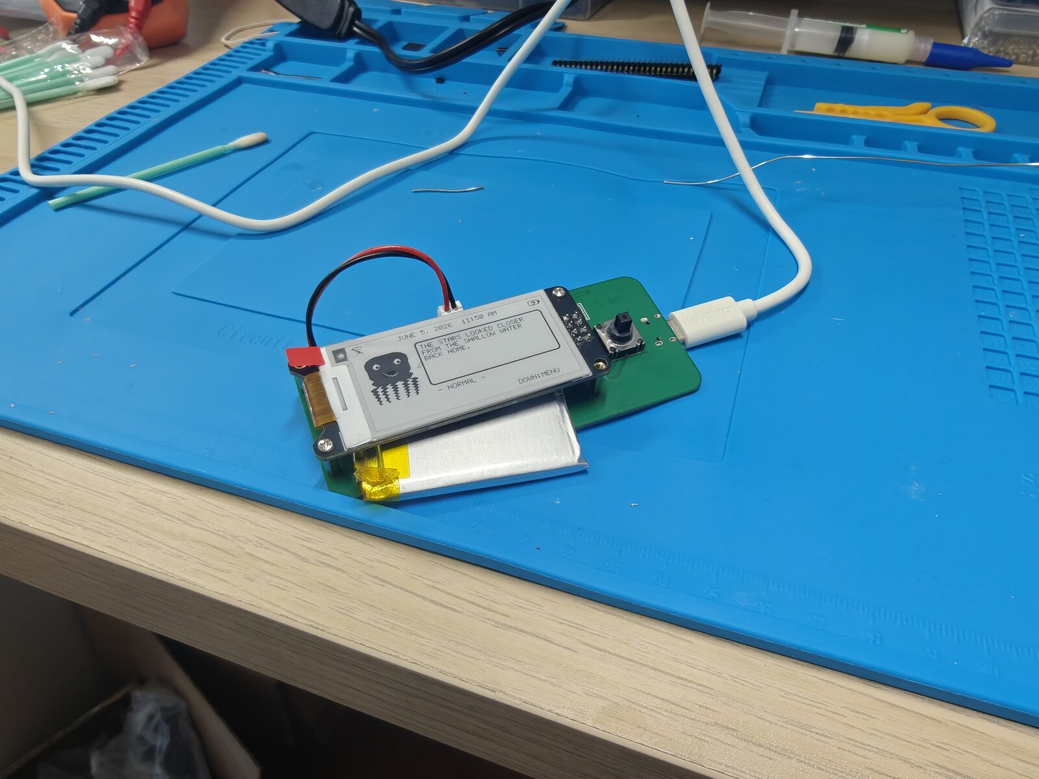
website/docs/assets/images/firmware/dilder-board-bench-first-power.jpg
