rompasaurus/dilder/website/docs/assets/images/hardware/pcb/full-board-rev1/full-board-rev1-3d-back-with-joystick.png

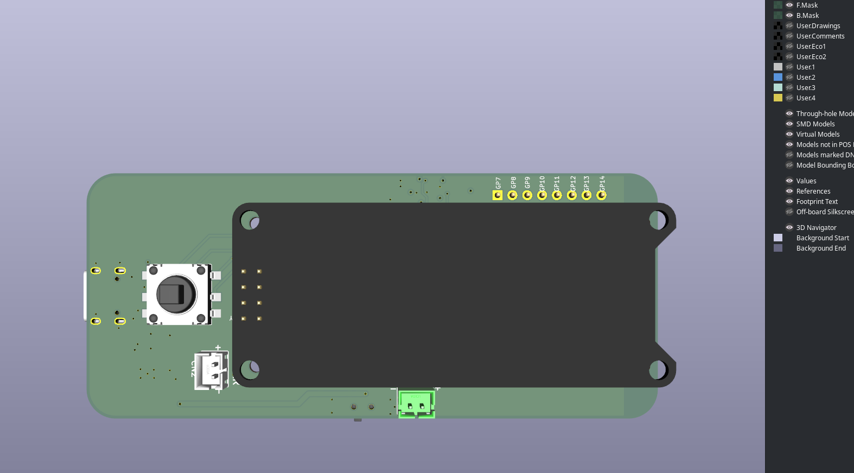
website/docs/assets/images/hardware/pcb/full-board-rev1/full-board-rev1-3d-back-with-joystick.png
