rompasaurus/dilder/website/docs/assets/images/hardware/pcb/full-board-rev1/full-board-rev1-3d-bottom-view.png

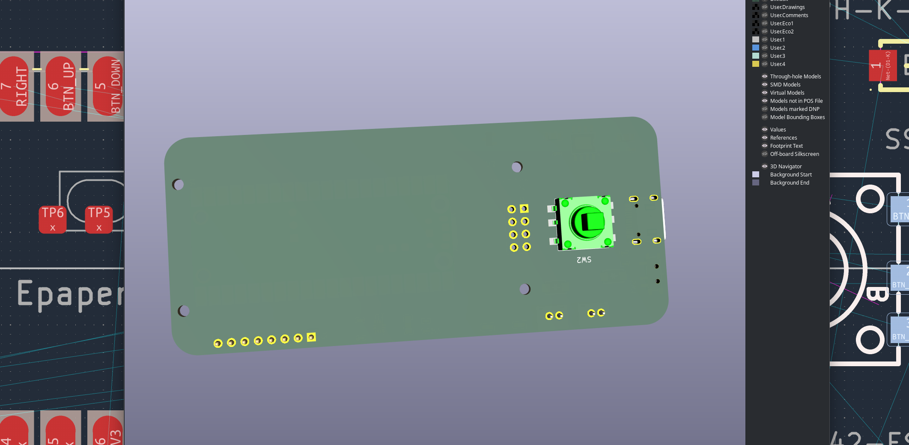
website/docs/assets/images/hardware/pcb/full-board-rev1/full-board-rev1-3d-bottom-view.png
