rompasaurus/dilder/assets/images/components/lis2dh12-accelerometer.jpg

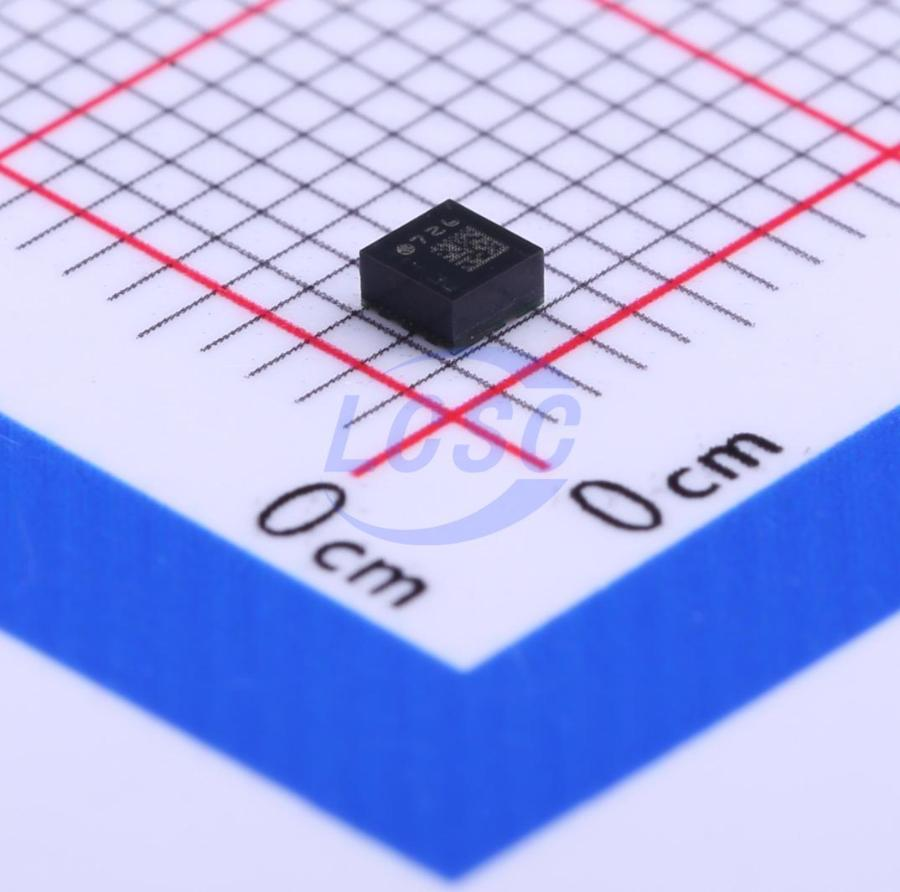
assets/images/components/lis2dh12-accelerometer.jpg
