rompasaurus/dilder/assets/images/hardware/build-session/jamal-plush-armchair.jpg

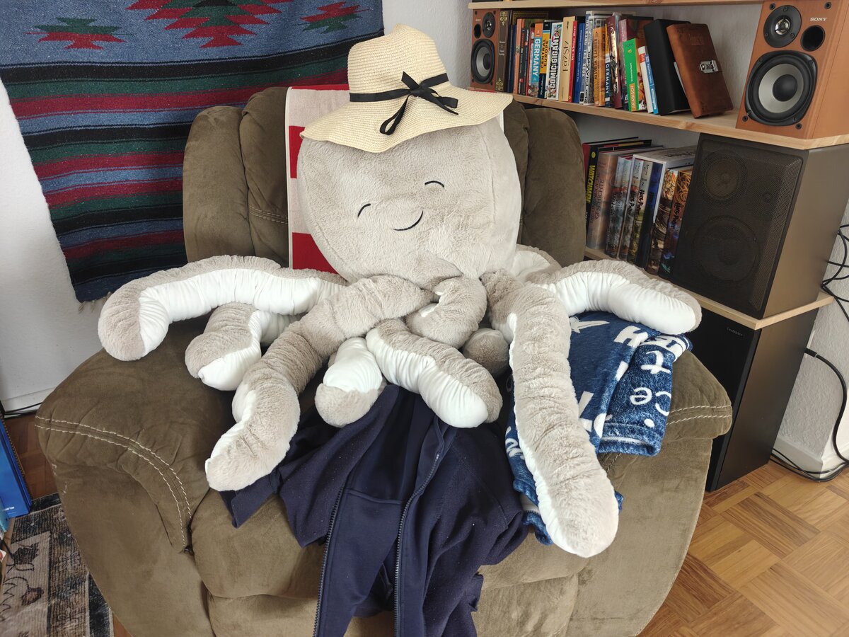
assets/images/hardware/build-session/jamal-plush-armchair.jpg
