rompasaurus/dilder/assets/images/hardware/build-session/joystick-on-breadboard.jpg

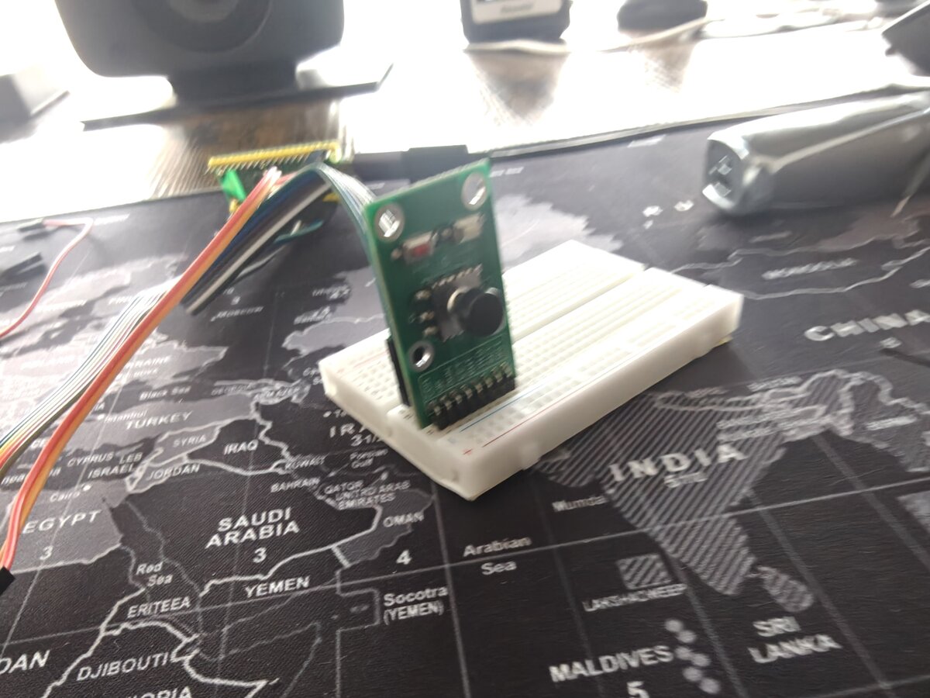
assets/images/hardware/build-session/joystick-on-breadboard.jpg
