rompasaurus/dilder/assets/images/hardware/build-session/joystick-selector-hungry-left.jpg

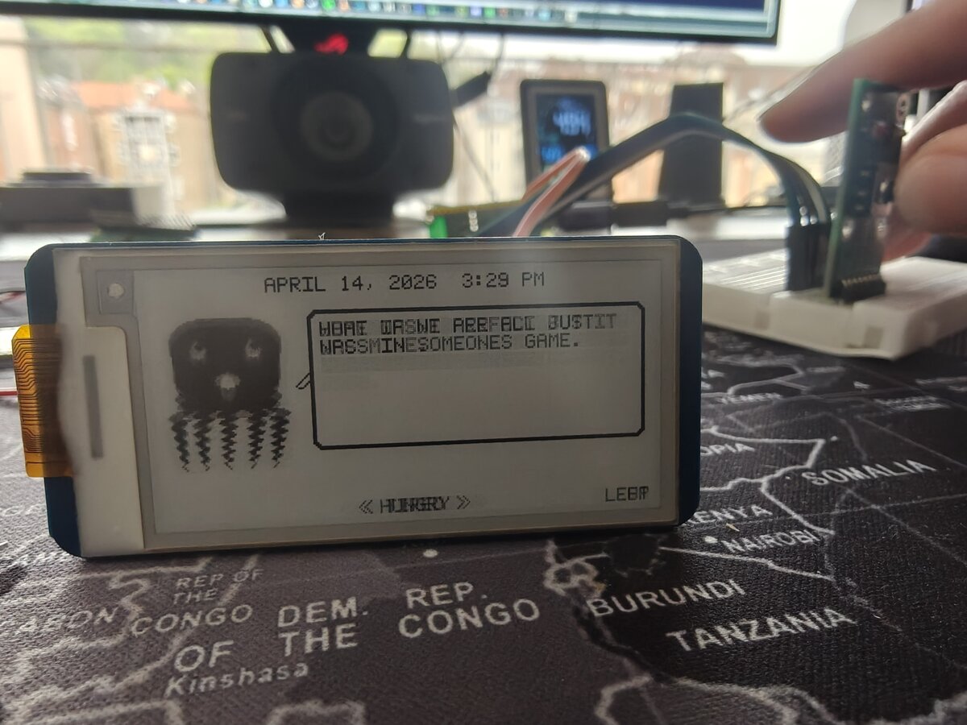
assets/images/hardware/build-session/joystick-selector-hungry-left.jpg
