rompasaurus/dilder/assets/images/hardware/build-session/joystick-selector-tired-mood.jpg

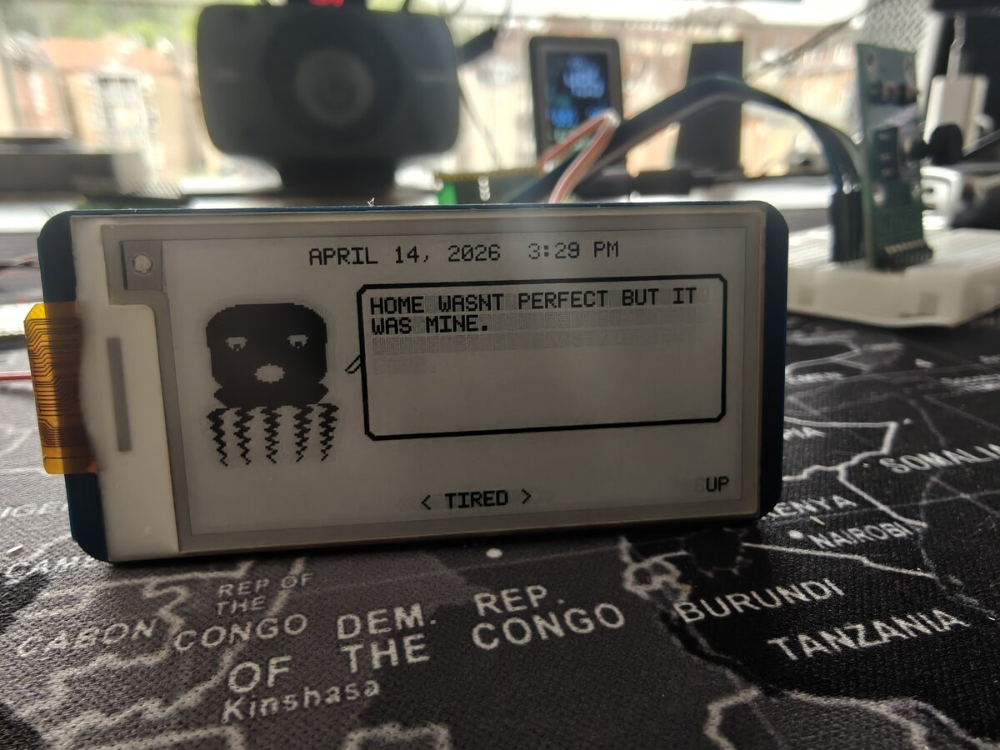
assets/images/hardware/build-session/joystick-selector-tired-mood.jpg
