rompasaurus/dilder/assets/images/hardware/build-session/pico-w-gpio-closeup-wiring.jpg

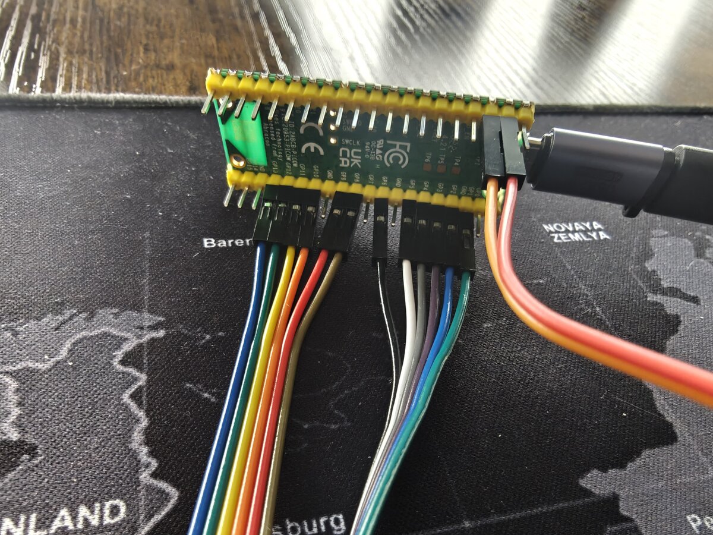
assets/images/hardware/build-session/pico-w-gpio-closeup-wiring.jpg
