rompasaurus/dilder/assets/images/hardware/build-session/pico-w-jumper-wires-display-angle.jpg

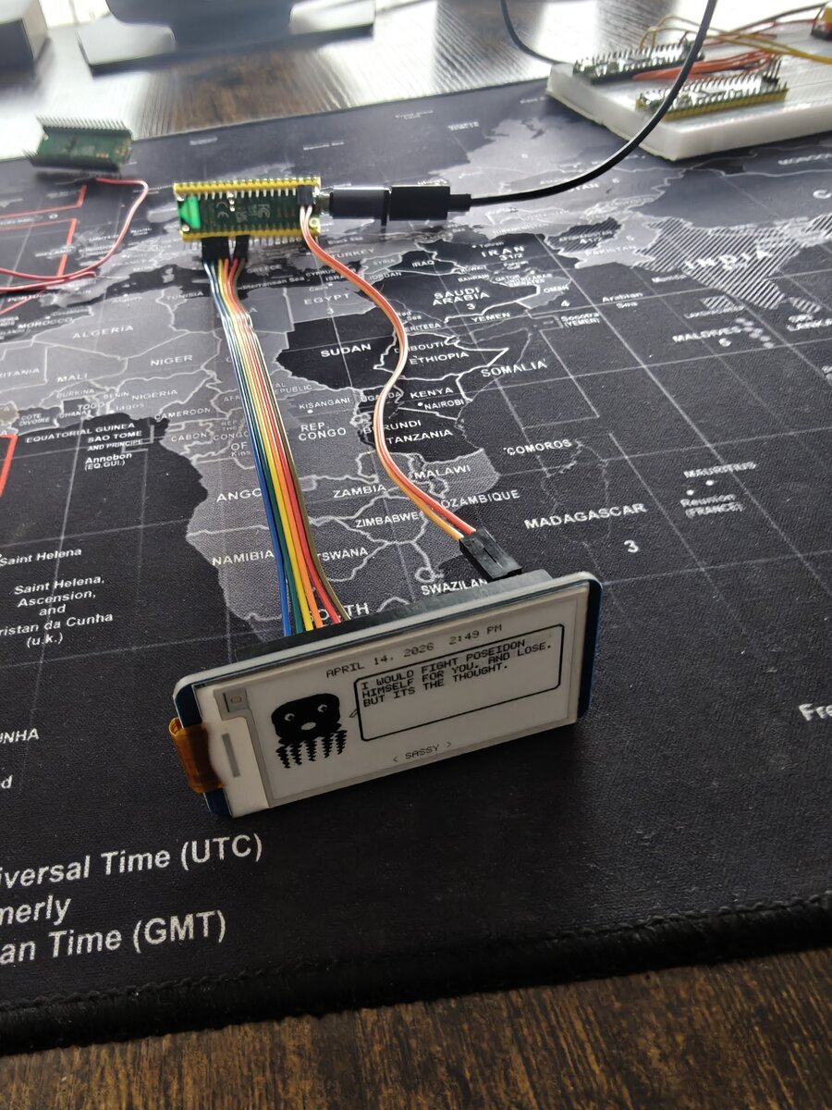
assets/images/hardware/build-session/pico-w-jumper-wires-display-angle.jpg
