rompasaurus/dilder/assets/images/hardware/build-session/pico-w-jumper-wires-display-side.jpg

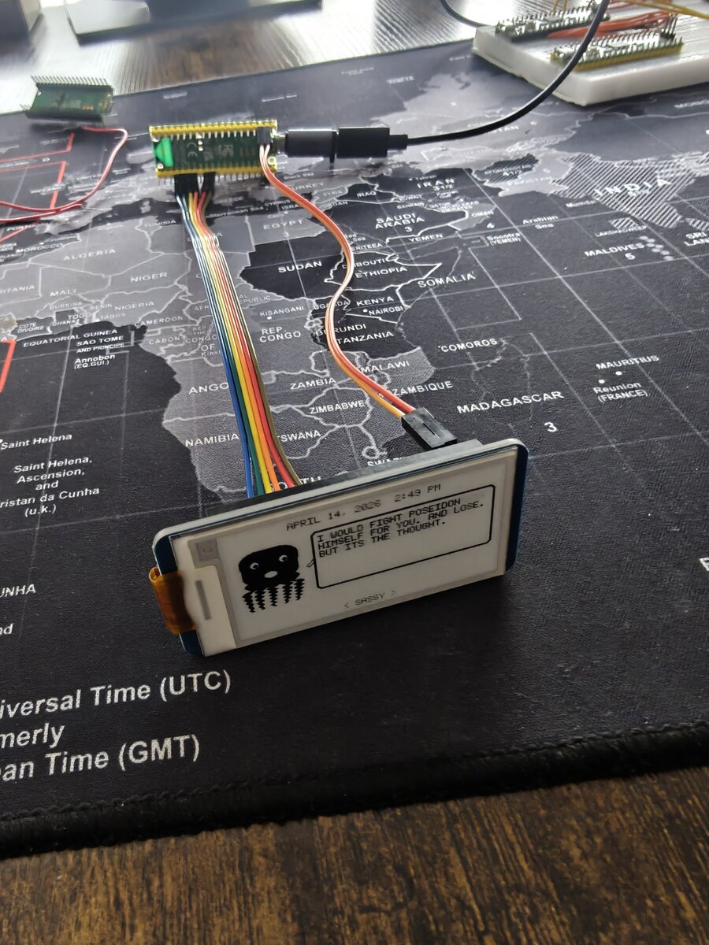
assets/images/hardware/build-session/pico-w-jumper-wires-display-side.jpg
