rompasaurus/dilder/assets/images/hardware/build-session/workspace-desk-blurry.jpg

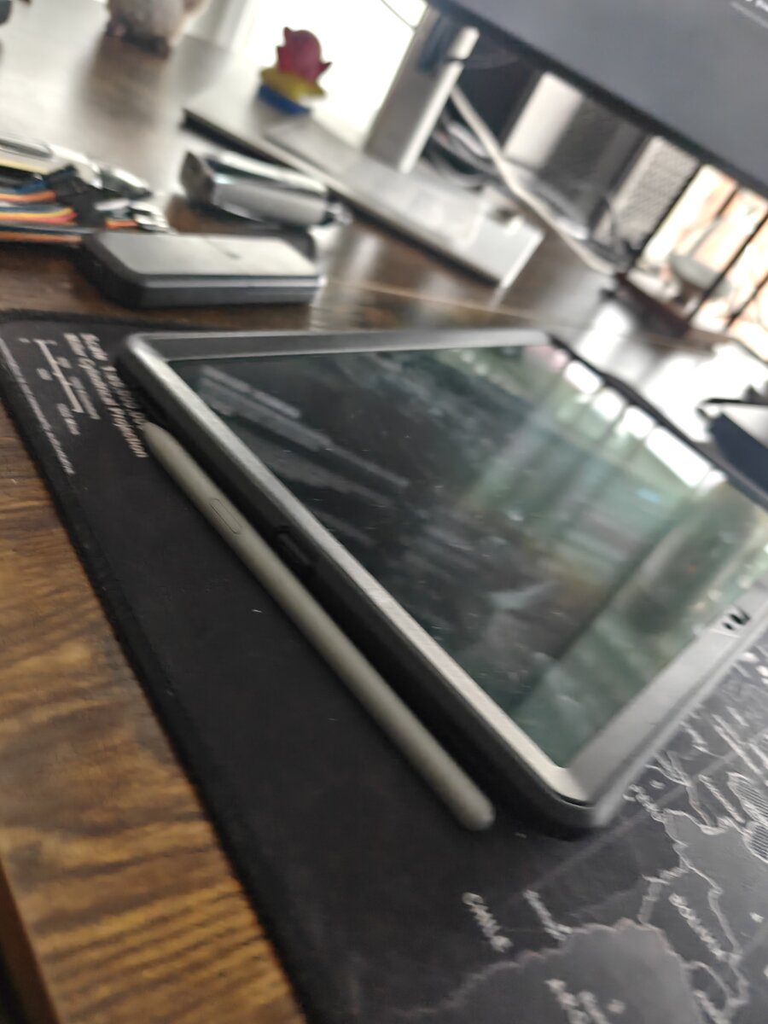
assets/images/hardware/build-session/workspace-desk-blurry.jpg
