rompasaurus/dilder/assets/images/hardware/build-session/workspace-full-breadboard-setup.jpg

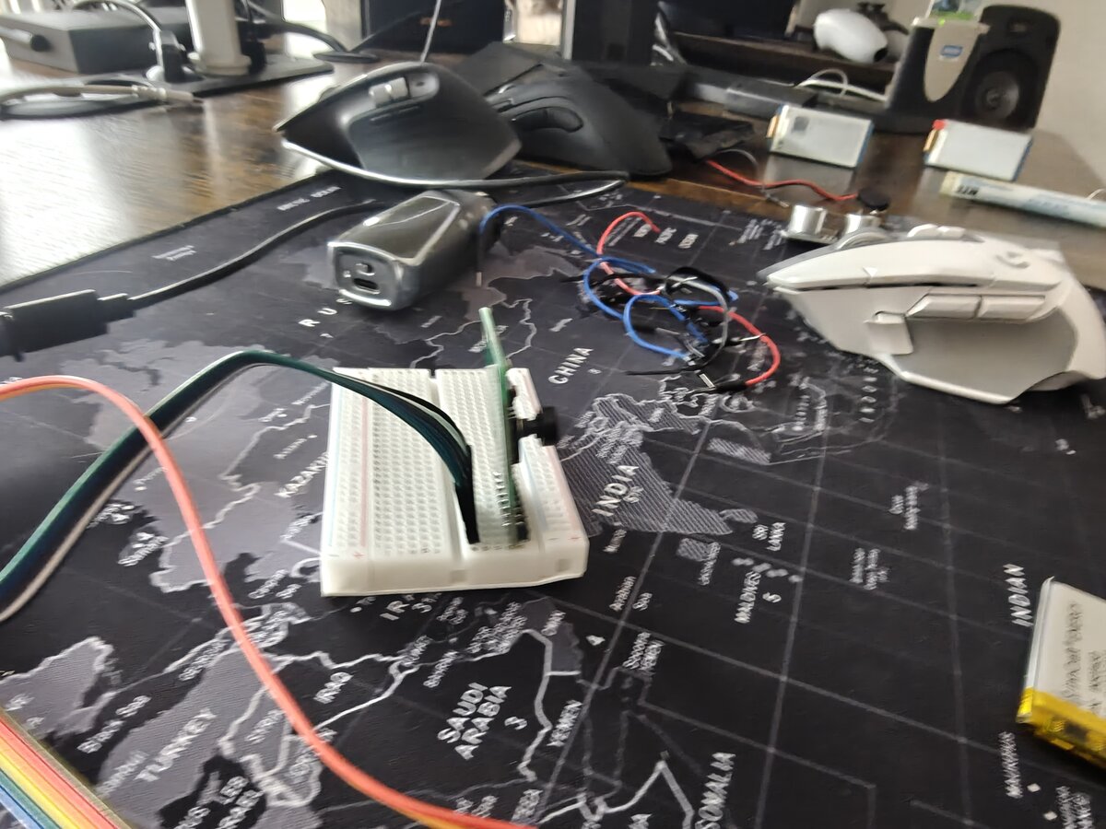
assets/images/hardware/build-session/workspace-full-breadboard-setup.jpg
