rompasaurus/dilder/website/docs/assets/images/hardware/pcb/full-board-rev1/full-board-rev1-board-setup-stackup-4layer-default.png

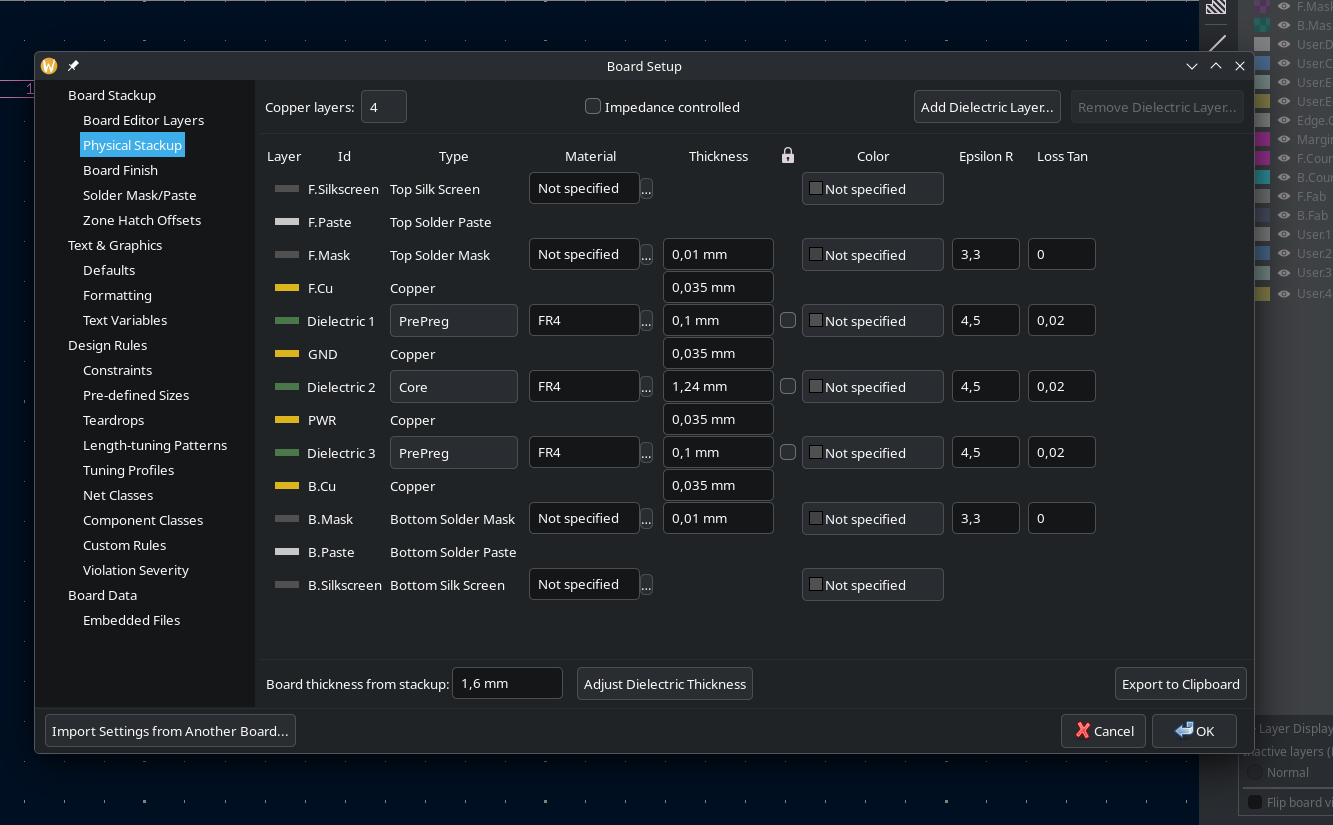
website/docs/assets/images/hardware/pcb/full-board-rev1/full-board-rev1-board-setup-stackup-4layer-default.png
