rompasaurus/dilder/assets/images/hardware/build-session/test-bench-full-with-joystick.jpg

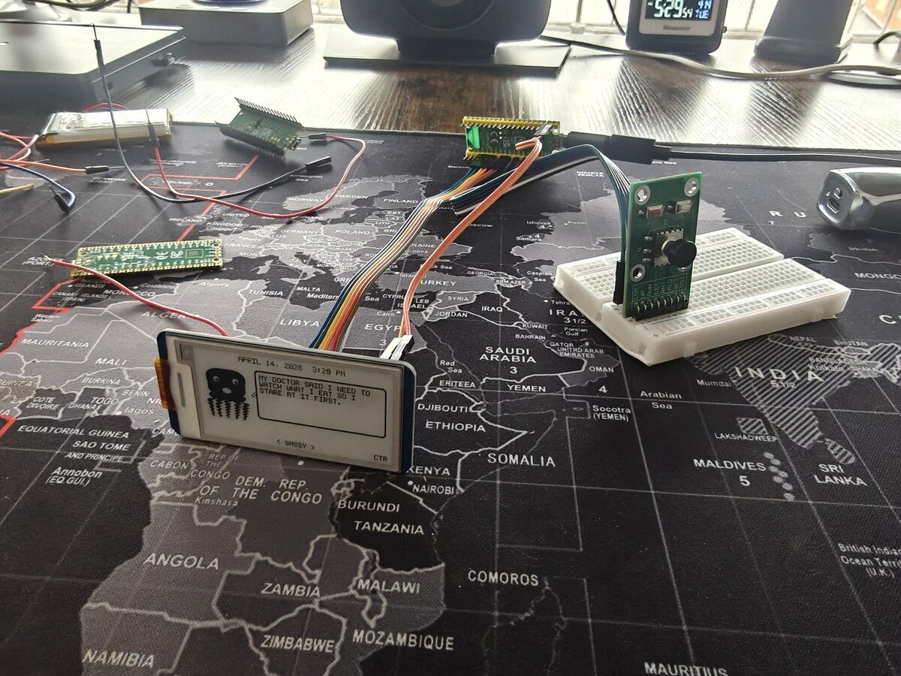
assets/images/hardware/build-session/test-bench-full-with-joystick.jpg
