rompasaurus/dilder/assets/octopus/output/grids/fixes_bubble_and_outfits.png

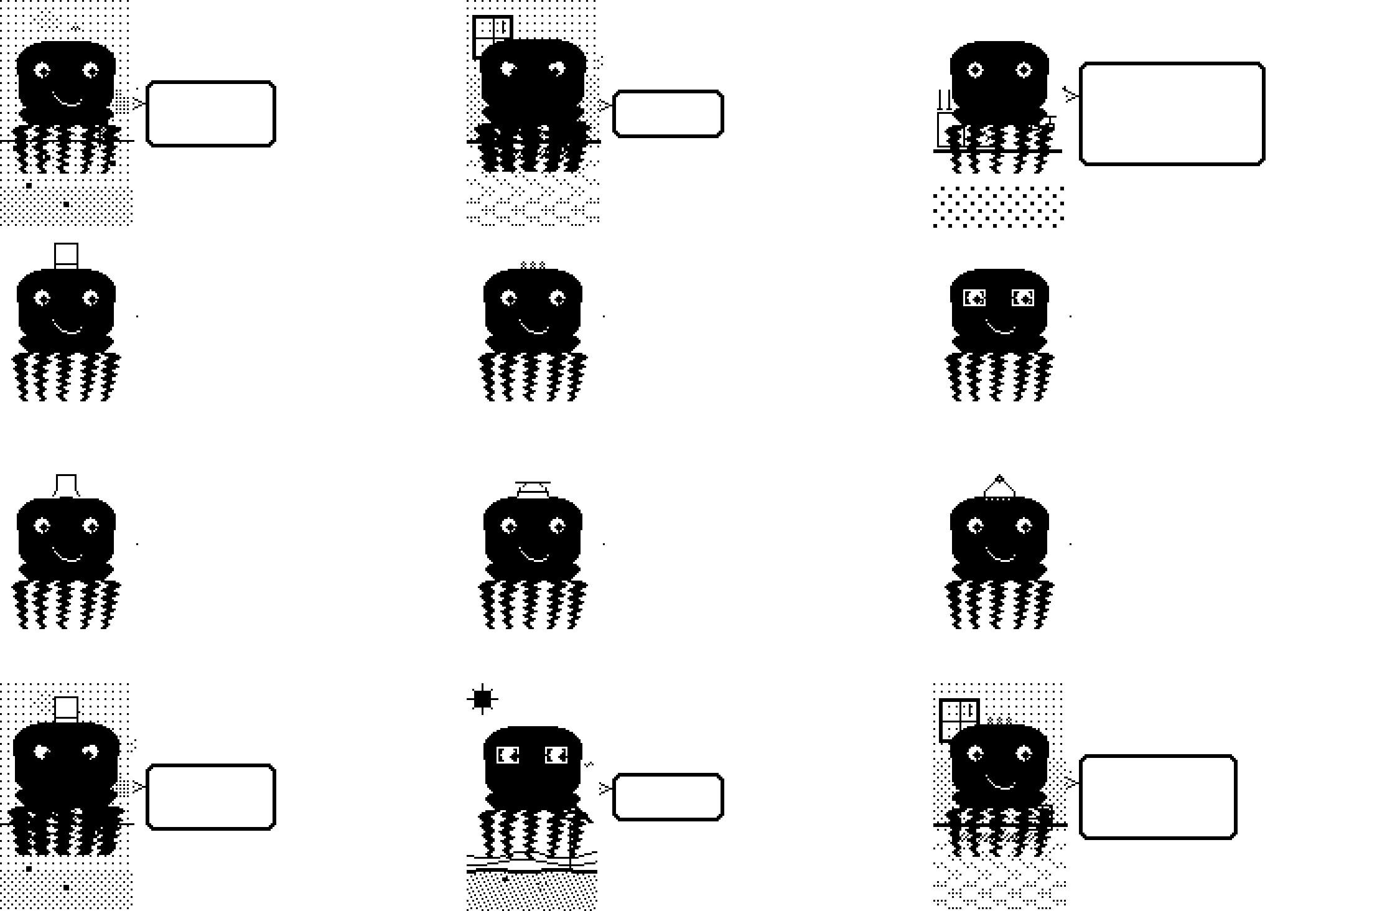
assets/octopus/output/grids/fixes_bubble_and_outfits.png
