rompasaurus/dilder/hardware-design/PCB Designs/Dilder Full Board/Dilder-Full-board/Dilder-Full-board.kicad_sch

## KiCad design hardware-design/PCB Designs/Dilder Full Board/Dilder-Full-board/Dilder-Full-board.kicad_sch (2026-05-10)

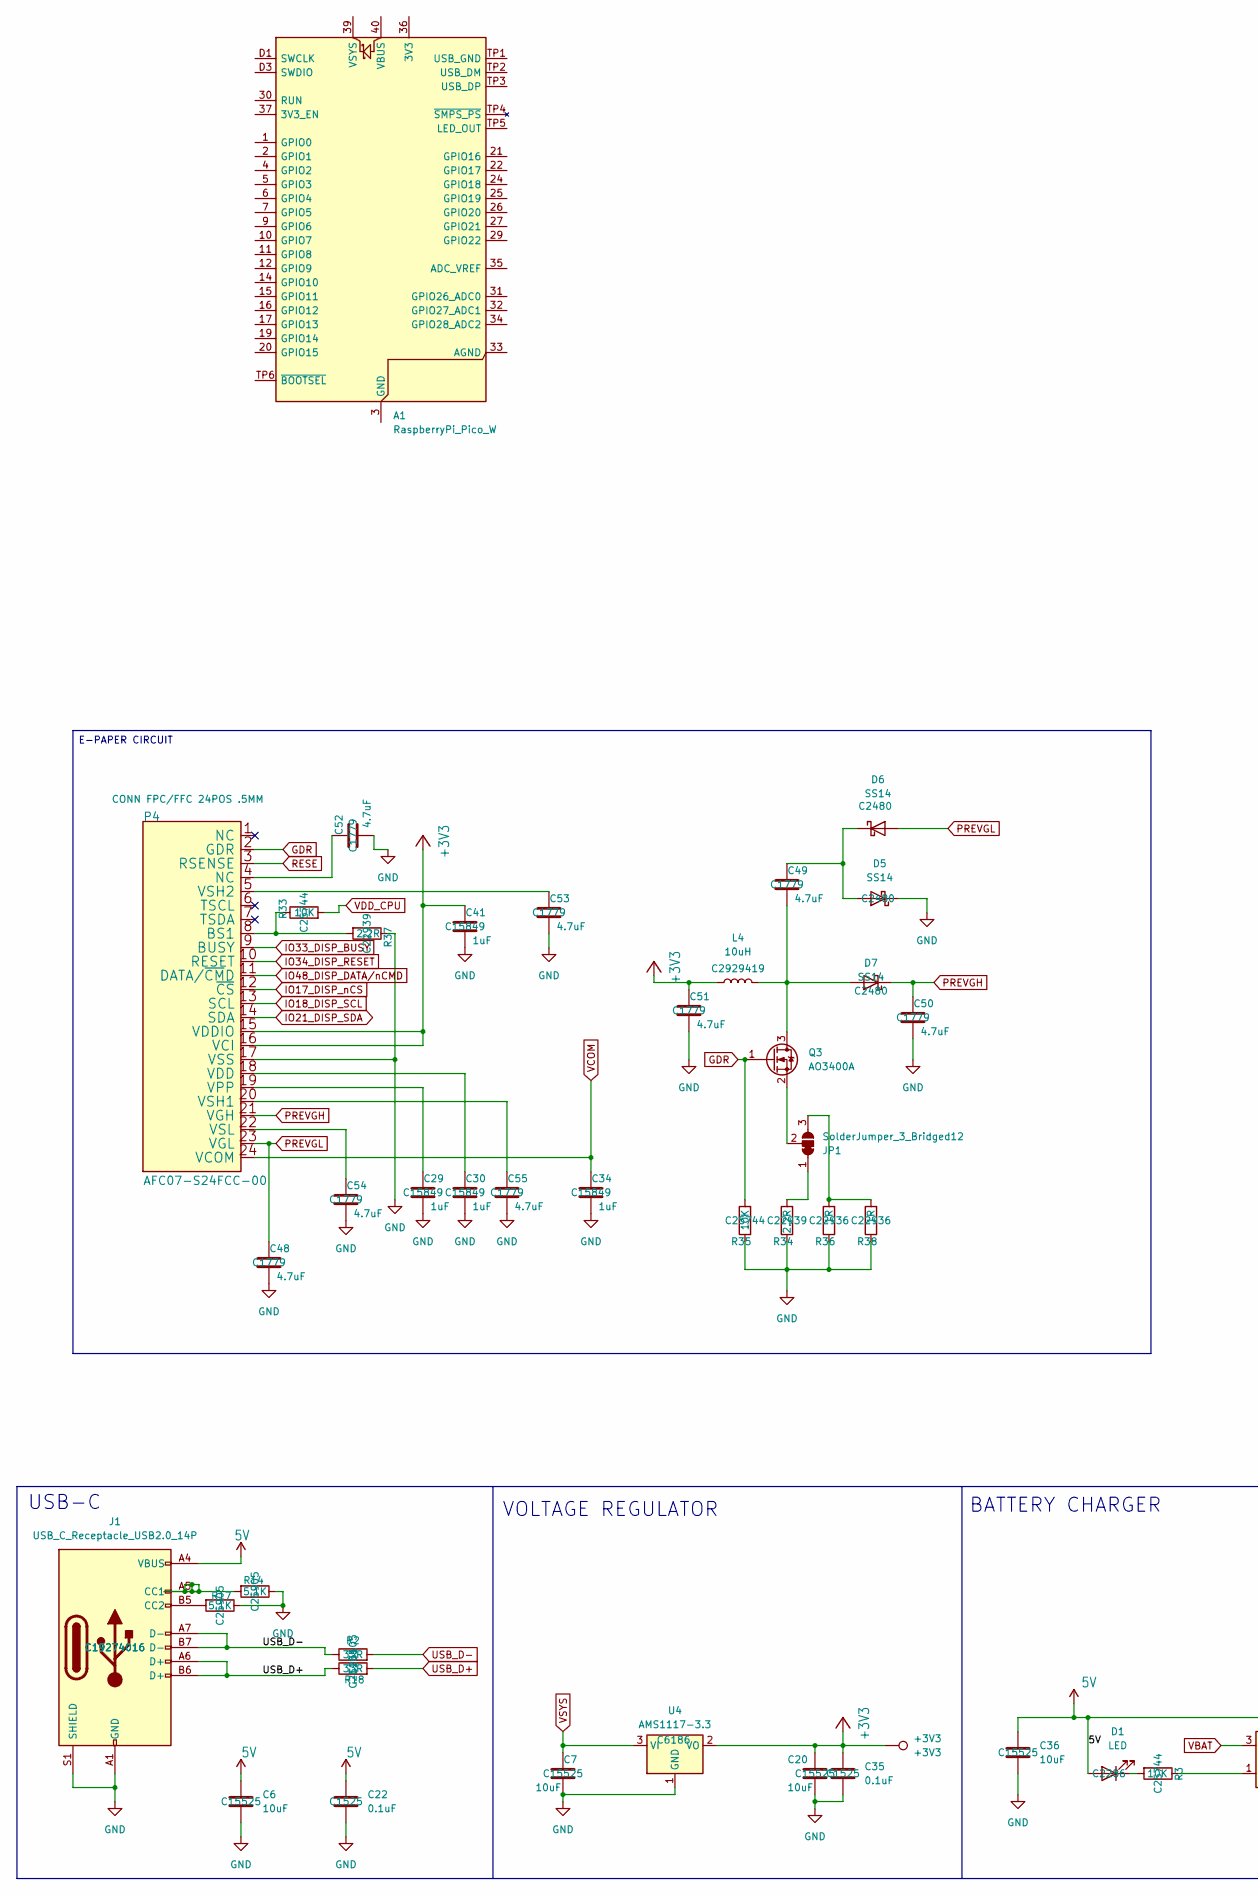
[picture p106: schematic Dilder-Full-board.kicad_sch, part in row 1, column 1]

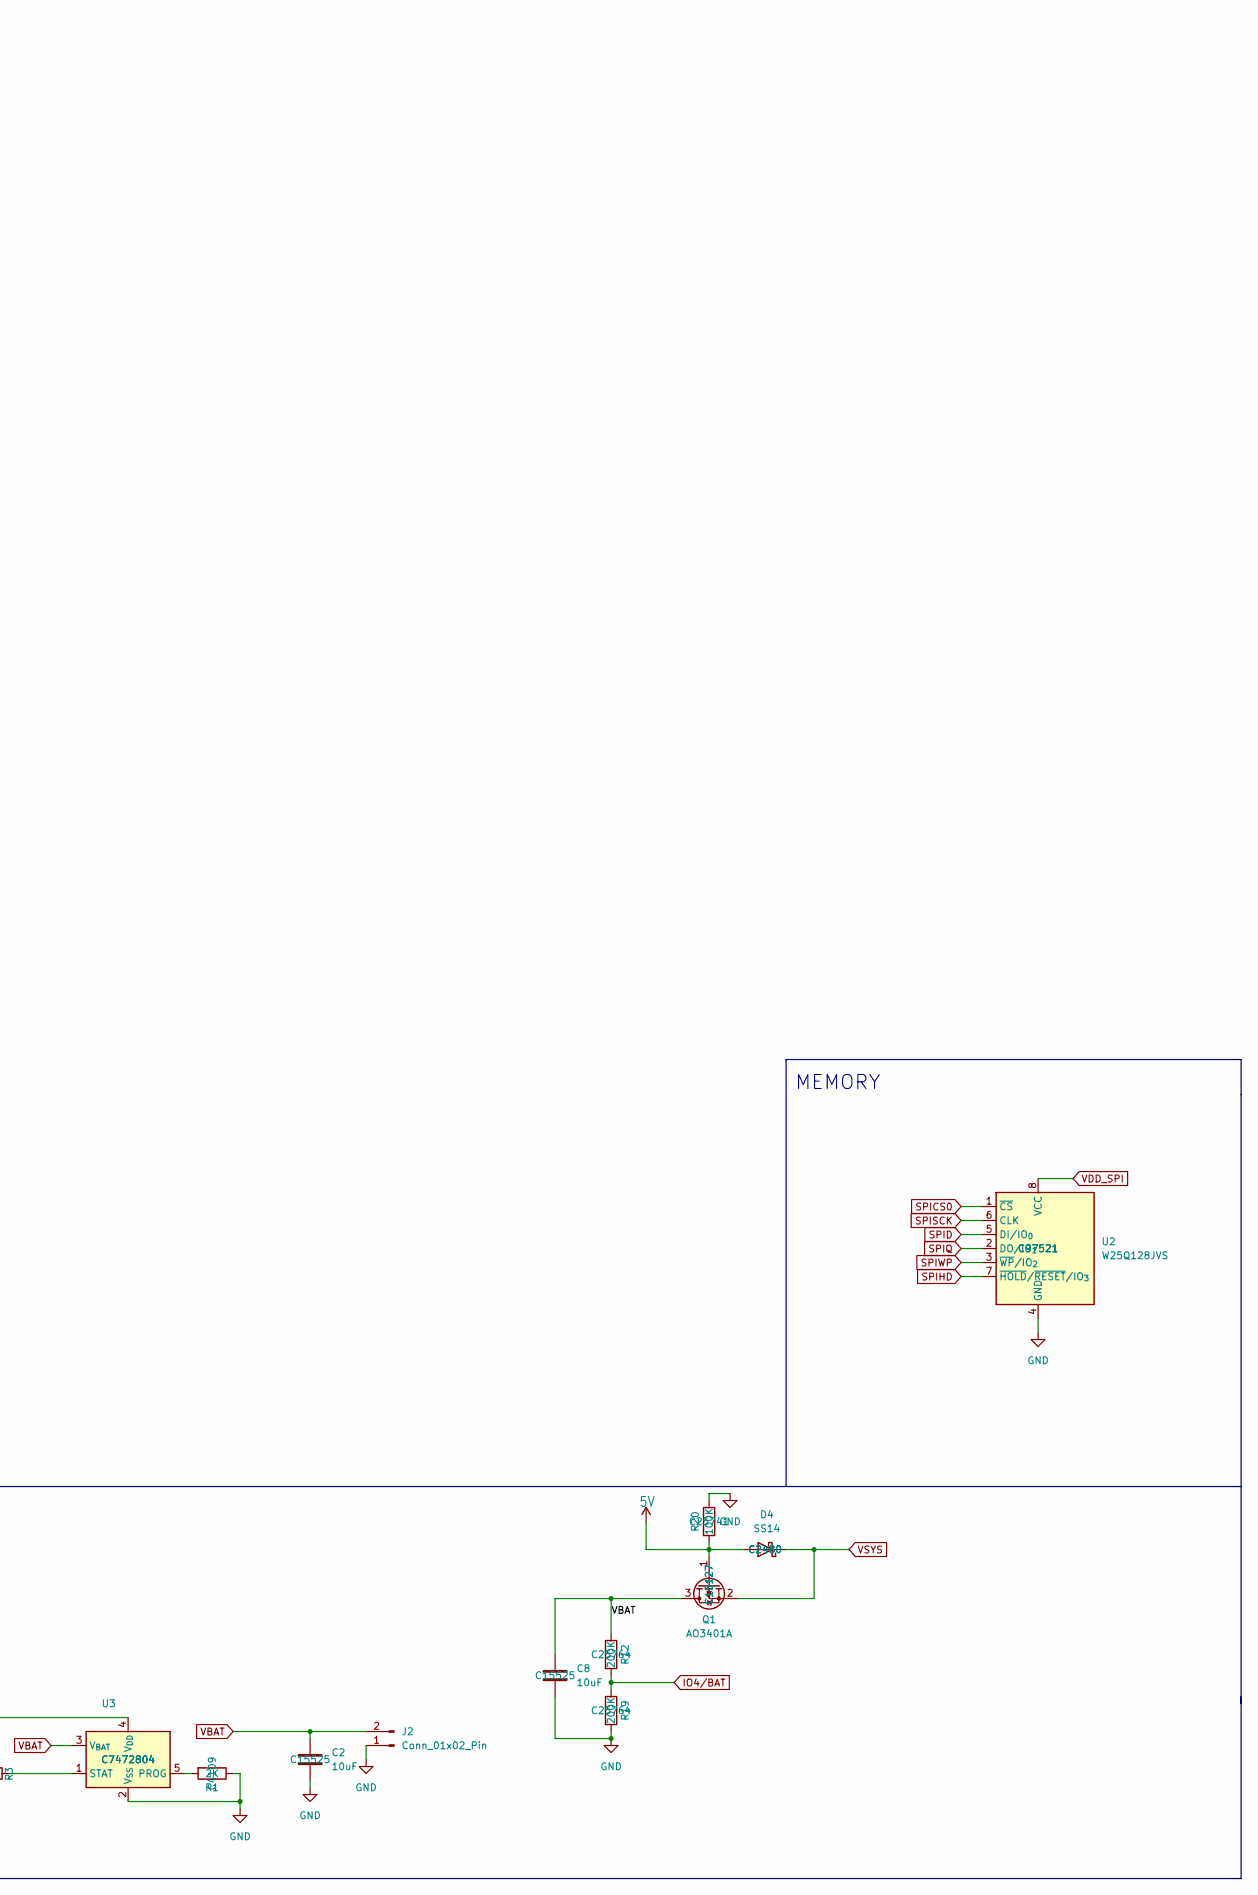
[picture p107: schematic Dilder-Full-board.kicad_sch, part in row 1, column 2]

Parts:
+3V3: +3V3; TestPoint_Pad_D1.0mm
A1: RaspberryPi_Pico_W; RaspberryPi_Pico_W_SMD
C2, C6, C7, C8, C20, C36: 10uF; C_0402_1005Metric; MNF PART NUMBER C15525; LCSC C15525
C22, C35: 0.1uF; C_0402_1005Metric; MNF PART NUMBER C1525; LCSC C1525
C29, C30, C34, C41: 1uF; C_0603_1608Metric; MNF PART NUMBER C15849; LCSC C15849
C48, C49, C50, C51, C52, C53, C54, C55: 4.7uF; C_0805_2012Metric; MNF PART NUMBER C1779; LCSC C1779
D1: LED; LED_0603_1608Metric; MNF PART NUMBER C2286; LCSC C2286
D4, D5, D6, D7: SS14; D_SMA; MNF PART NUMBER C2480; LCSC C2480
J1: USB_C_Receptacle_USB2.0_14P; USB_C_Receptacle_HCTL_HC-TYPE-C-16P-01A; MNF PART NUMBER C19274016; LCSC C19274016
J2: Conn_01x02_Pin; PinSocket_1x02_P2.54mm_Vertical
JP1: SolderJumper_3_Bridged12; SolderJumper-3_P1.3mm_Bridged12_RoundedPad1.0x1.5mm_NumberL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
L4: 10uH; L_Ferrocore_DLG-0403; MNF PART NUMBER C2929419; LCSC C2929419
P4: AFC07-S24FCC-00; Jushuo_AFC07-S24FCA-00_1x24-1MP_P0.50_Horizontal; MNF PART NUMBER C11057; LCSC C11057
Q1: AO3401A; SOT-23; MNF PART NUMBER C15127; LCSC C15127
Q3: AO3400A; SOT-23; MNF PART NUMBER C20917; LCSC C20917
R1: 2K; R_0402_1005Metric; MNF PART NUMBER C4109; LCSC C4109
R2, R18: 33R; R_0402_1005Metric; MNF PART NUMBER C25105; LCSC C25105
R3, R33, R35: 10K; R_0402_1005Metric; MNF PART NUMBER C25744; LCSC C25744
R12, R19: 200K; R_0402_1005Metric; MNF PART NUMBER C25764; LCSC C25764
R14, R17: 5.1K; R_0402_1005Metric; MNF PART NUMBER C25905; LCSC C25905
R20: 100K; R_0402_1005Metric; MNF PART NUMBER C25741; LCSC C25741
R34, R37: 2.2R; R_0603_1608Metric; MNF PART NUMBER C22939; LCSC C22939
R36, R38: 1R; R_0603_1608Metric; MNF PART NUMBER C22936; LCSC C22936
U2: W25Q128JVS; SOIC-8_5.3x5.3mm_P1.27mm; MNF PART NUMBER C97521; LCSC C97521
U3: MCP73831-2-OT; SOT-23-5; MNF PART NUMBER C7472804; LCSC C7472804
U4: AMS1117-3.3; SOT-223-3_TabPin2; MNF PART NUMBER C6186; LCSC C6186

Connections:
5V: C6.1, C22.1, C36.1, D1.2 (A), D4.2 (A), J1.A4 (VBUS), J1.A9 (VBUS), J1.B4 (VBUS), J1.B9 (VBUS), Q1.1 (G), R20.2, U3.4 (V_{DD})
+3V3: +3V3.1, C20.1, C35.1, C41.1, C51.1, L4.1, P4.15 (VDDIO), P4.16 (VCI), U4.2 (VO)
GDR: P4.2 (GDR), Q3.1 (G), R35.2
GND: C2.2, C6.2, C7.2, C8.2, C20.2, C22.2, C29.2, C30.2, C34.2, C35.2, C36.2, C41.2, C48.2, C50.2, C51.2, C52.2, C53.2, C54.2, C55.2, D5.1 (K), J1.A1 (GND), J1.A12 (GND), J1.B1 (GND), J1.B12 (GND), J1.S1 (SHIELD), J2.1, P4.17 (VSS), R1.1, R14.1, R17.1, R19.2, R20.1, R34.1, R35.1, R36.1, R37.1, R38.1, U2.4 (GND), U3.2 (V_{SS}), U4.1 (GND)
IO4/BAT: R12.2, R19.1
IO17_DISP_nCS: P4.12 (~CS)
IO18_DISP_SCL: P4.13 (SCL)
IO21_DISP_SDA: P4.14 (SDA)
IO33_DISP_BUSY: P4.9 (BUSY)
IO34_DISP_RESET: P4.10 (RESET)
IO48_DISP_DATA/nCMD: P4.11 (DATA/~CMD)
unnamed: A1.3 (GND), A1.8 (GND), A1.13 (GND), A1.18 (GND), A1.23 (GND), A1.28 (GND), A1.38 (GND), A1.D2 (GND)
unnamed: C29.1, P4.19 (VPP)
unnamed: C30.1, P4.18 (VDD)
unnamed: C49.1, D5.2 (A), D6.1 (K)
unnamed: C49.2, D7.2 (A), L4.2, Q3.3 (D)
unnamed: C52.1, P4.4 (NC)
unnamed: C53.1, P4.5 (VSH2)
unnamed: C54.1, P4.22 (VSL)
unnamed: C55.1, P4.20 (VSH1)
unnamed: D1.1 (K), R3.2
unnamed: J1.A5 (CC1), R14.2
unnamed: J1.B5 (CC2), R17.2
unnamed: JP1.1 (A), R34.2
unnamed: JP1.2 (C), Q3.2 (S)
unnamed: JP1.3 (B), R36.2, R38.2
unnamed: P4.8 (BS1), R33.1, R37.2
unnamed: R1.2, U3.5 (PROG)
unnamed: R3.1, U3.1 (STAT)
PREVGH: C50.1, D7.1 (K), P4.21 (VGH)
PREVGL: C48.1, D6.2 (A), P4.23 (VGL)
RESE: P4.3 (RSENSE)
SPICS0: U2.1 (~CS)
SPID: U2.5 (DI/IO_{0})
SPIHD: U2.7 (~HOLD/~RESET/IO_{3})
SPIQ: U2.2 (DO/IO_{1})
SPISCK: U2.6 (CLK)
SPIWP: U2.3 (~WP/IO_{2})
USB_D+: J1.A6 (D+), J1.B6 (D+), R18.1, R18.2
USB_D-: J1.A7 (D-), J1.B7 (D-), R2.1, R2.2
VBAT: C2.1, C8.1, J2.2, Q1.3 (D), R12.1, U3.3 (V_{BAT})
VCOM: C34.1, P4.24 (VCOM)
VDD_CPU: R33.2
VDD_SPI: U2.8 (VCC)
VSYS: C7.1, D4.1 (K), Q1.2 (S), U4.3 (VI)

Notes on the sheet:
USB-C
VOLTAGE REGULATOR
MEMORY
BATTERY CHARGER
E-PAPER CIRCUIT
