rompasaurus/dilder/dev-setup/dilder-hub-rtos/btstack_config.h

#ifndef BTSTACK_CONFIG_H
#define BTSTACK_CONFIG_H

/* BTstack configuration for the Dilder Hub — BLE peripheral with pairing/bonding.
 * Based on the Pico SDK picow_ble example config. */

/* BTstack features */
#define ENABLE_BLE
#define ENABLE_LE_PERIPHERAL
#define ENABLE_LE_CENTRAL                 /* scan/observer for Dilder-to-Dilder discovery */
#define ENABLE_LE_SECURE_CONNECTIONS
#define ENABLE_LE_DATA_LENGTH_EXTENSION
#define ENABLE_LOG_ERROR
#define ENABLE_PRINTF_HEXDUMP

/* Buffers / sizes */
#define HCI_OUTGOING_PRE_BUFFER_SIZE 4
#define HCI_ACL_PAYLOAD_SIZE (255 + 4)
#define HCI_ACL_CHUNK_SIZE_ALIGNMENT 4
#define MAX_NR_GATT_CLIENTS 0
#define MAX_NR_HCI_CONNECTIONS 1
#define MAX_NR_L2CAP_SERVICES  3
#define MAX_NR_L2CAP_CHANNELS  3
#define MAX_NR_SM_LOOKUP_ENTRIES 3
#define MAX_NR_WHITELIST_ENTRIES 16
#define MAX_NR_LE_DEVICE_DB_ENTRIES 16

/* Limit ACL/SCO buffers to avoid the cyw43 shared-bus overrun */
#define MAX_NR_CONTROLLER_ACL_BUFFERS 3
#define MAX_NR_CONTROLLER_SCO_PACKETS 3

/* HCI controller-to-host flow control (cyw43 shared bus) */
#define ENABLE_HCI_CONTROLLER_TO_HOST_FLOW_CONTROL
#define HCI_HOST_ACL_PACKET_LEN 1024
#define HCI_HOST_ACL_PACKET_NUM 3
#define HCI_HOST_SCO_PACKET_LEN 120
#define HCI_HOST_SCO_PACKET_NUM 3

/* Link-key / LE device DB via TLV on flash */
#define NVM_NUM_DEVICE_DB_ENTRIES 16
#define NVM_NUM_LINK_KEYS 16

/* Fixed-size ATT DB (no malloc) */
#define MAX_ATT_DB_SIZE 512

#define HAVE_EMBEDDED_TIME_MS
#define HAVE_ASSERT
#define HCI_RESET_RESEND_TIMEOUT_MS 1000
#define ENABLE_SOFTWARE_AES128
#define ENABLE_MICRO_ECC_FOR_LE_SECURE_CONNECTIONS

#endif
